myriadrf/LimeRFE-8001P/hardware/1v0/KiCAD/ATMEGA_MCU.sch

## KiCad design hardware/1v0/KiCAD/ATMEGA_MCU.sch (2023-10-04)

Schematic: ATMEGA_MCU.sch

Parts:
C35, C91, C179, C181, C183, C323, C325: 1nF_0402; SMD0402; Manufacturer Part Number CC0402KRX7R9BB102
C43, C46, C48, C50: 1uF_0603_TMK107BJ105KA-T; SMD0603; Manufacturer Part Number TMK107BJ105KA-T
C44: 4.7uF_0402_GRM155R60J475ME87D; SMD0402; Manufacturer Part Number GRM155R60J475ME87D
C45, C47, C49, C56: 100nF_0402_GRM155R71C104KA88J; SMD0402; Manufacturer Part Number GRM155R71C104KA88J
C83: 3.9nF_0402_04025C392JAT2A; SMD0402; Manufacturer Part Number 04025C392JAT2A
C92, C96, C97, C98, C167, C169, C180, C182, C184, C228, C229, C321, C322, C324, C326, C329, C330, C387, C388, C390, C391, C394, C395, C396, C397: 10nF_0402; SMD0402; Manufacturer Part Number CC0402ZRY5V7BB103
C320, C393: 1uF_0402; SMD0402; Manufacturer Part Number CC0402ZRY5V5BB105
CON2: 47346-0001; USB-MINI-B; Manufacturer Part Number 47346-0001
D1: LED0603_RED; LED_0603; Manufacturer Part Number SML-D12U1WT86
D2: LED0603_GREEN; LED_0603; Manufacturer Part Number SML-D12M1WT86
FB23: 10uH_0603_TDK; SMD0603; Manufacturer Part Number MLZ1608E100MT
J19: TSM-103-04-F-DV; Manufacturer Part Number TSM-103-04-F-DV
J28, J31: PMOD_CONN; Manufacturer Part Number 95278-401-06LF
J32: M50-3600542; PIN_HEADER_2X5; Manufacturer Part Number M50-3600542
J42: TSM-103-04-L-SV; Manufacturer Part Number TSM-103-04-L-SV
J43: Jumper_SNM-100-BK-T; SNM-100-BK-T; Manufacturer Part Number SNM-100-BK-T
R3, R4, R7, R18, R19, R22: 10K_0402; SMD0402; Manufacturer Part Number RMCF0402FT10K0
R5, R6, R20, R21: 10K_0402; SMD0402
R8, R9, R10, R11, R12, R13, R14, R15, R17, R23, R24, R25, R26, R27, R28, R84, R85, R132: 330R_0402; SMD0402; Manufacturer Part Number RC0402JR-07330RL
R16, R60, R61, R64, R71, R181, R182: 20K_0402_CRCW040220K0FKEDC; SMD0402; Manufacturer Part Number CRCW040220K0FKEDC
R43, R44, R46, R58, R59: 1K_0402_CRGP0402F1K0; SMD0402; Manufacturer Part Number CRGP0402F1K0
R47, R48: 22R_0402_RC0402JR-0722RL; SMD0402; Manufacturer Part Number RC0402JR-0722RL
R49: 1M_0402_RC0402FR-071ML; SMD0402; Manufacturer Part Number RC0402FR-071ML
R100: 0R_0402_RC0402JR-070RL; SMD0402; Manufacturer Part Number RC0402JR-070RL
R129, R204: 0R_0402_NF; SMD0402; Manufacturer Part Number RC0402JR-070RL
R163, R164, R165, R166, R167, R168, R169, R170, R173, R174, R175, R176, R177, R178, R205, R206, R207, R209, R279, R280, R281, R300, R301, R302, R303, R304, R305, R306, R307: 0R_0402; SMD0201
R179, R180: NF_0R_0402_RCS04020000Z0ED; SMD0402; Manufacturer Part Number RCS04020000Z0ED
R208: 0RNF_0402; SMD0402
SW3: SW_PUSH; B3U-1000P; Manufacturer Part Number B3U-1000P
U1, U2: LMS8001
U3, U22, U87: SN74LV1T04; Manufacturer Part Number SN74LV1T04DCKRG4
U11: ATMEGA328P-AU; Manufacturer Part Number ATMEGA328P-AUR
U12: FT232RL; Manufacturer Part Number FT232RL-REEL
U13: NUP2202W1T2G; SC-88-6_NUP2202W1T2G; Manufacturer Part Number NUP2202W1T2G
U17, U70, U71, U72: NXB0108PW-Q100J; Manufacturer Part Number NXB0108PW-Q100J
U19, U20: SN74HCS594QPWRQ1; Manufacturer Part Number SN74HCS594QPWRQ1
U23, U24: MC74VHC1G126DBVT1G; Manufacturer Part Number ONSEMI
U25: SN74HCS595QPWRQ1; Manufacturer Part Number SN74HCS595QPWRQ1
U88, U89: SN74CBT3245APWE4; Manufacturer Part Number SN74CBT3245APWE4
U90: TC7MBL3245CFT(EL); Manufacturer Part Number TC7MBL3245CFT(EL)
X2: CSTNE16M0V530000R0; Manufacturer Part Number CSTNE16M0V530000R0

Notes on the sheet:
SPI_SOFT CON
SAENn towards LMS8001 #1
SCENn towards PLL #1
Level convertors 3.3V<->5V for SPI
Daisy Chain
SBENn towards LMS8001 #2
SN74HCS595QPWRQ1: this one has OE pin and 3-state out
brisi ovo!
3.3V pull-up
5V pull-up
0V pull-down
SDENn towards PLL #2
This one should be default
This one should be NF
LMS8001 #1
LMS8001 #2
MCU FREE PINS CON
RESETn towards LMS8001 #1
RESETn towards LMS8001 #2
1.2-3.6V on A side
1.65-5V on B side
SCENn towards PLL #2
MCU_side
Connects free MCU pins to eather LMS8001 chip A or B
GPIO 00, 01, 02 of LMS8001 A or B to free MCU pins PC5, PC4 and PB0
SPI connector from 5G board
SDIO signal to MISO and MOSI
RESET
USB 2 SERIAL
TVS_protection
USB_CONN
Interupt 1
NE ZNAM CEMU SLUZI?
Interupt 0
Shift (Serial) Register Data CLOCK
Output Register Data ENABLE
Shift (Serial) Register Data RESET
Output Register Data RESET
MCU
