myriadrf/LimeRFE-8001P/hardware/1v0/KiCAD/DA1.sch

## KiCad design hardware/1v0/KiCAD/DA1.sch (2023-10-04)

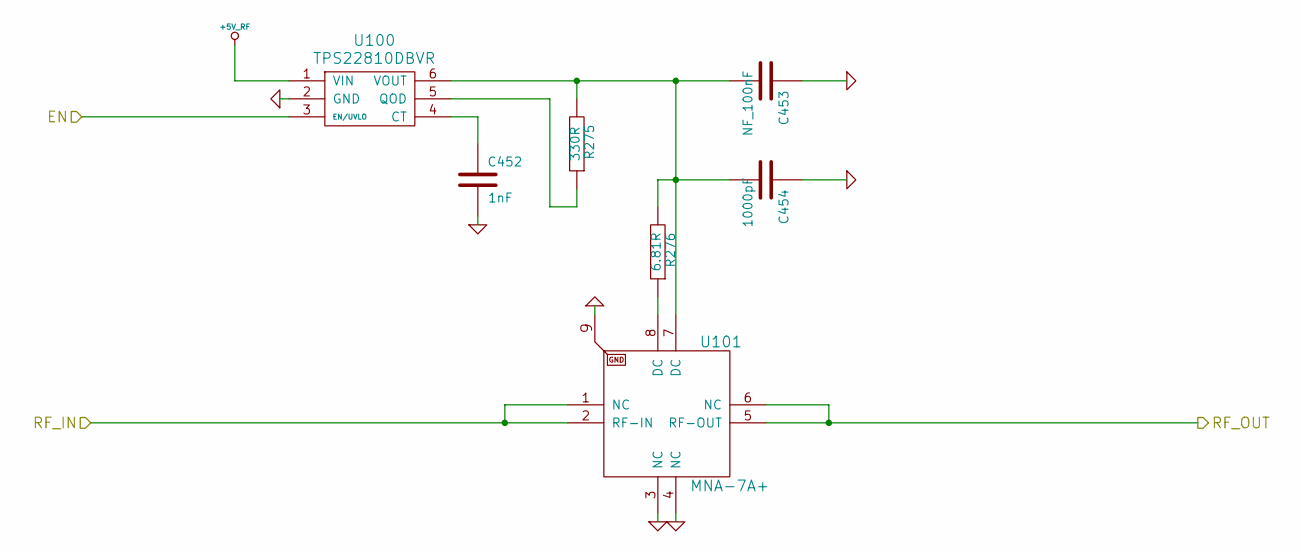
[picture p48: schematic DA1.sch]

Parts:
C452: 1nF_0603_06035C102KAT2A; SMD0603; Manufacturer Part Number 06035C102KAT2A
C453: NF_100nF_0603_C0603C104M5RACTU; SMD0603; Manufacturer Part Number C0603C104M5RACTU
C454: 1000pF_0402_GCM155R71H102KA37D; SMD0402; Manufacturer Part Number GCM155R71H102KA37D
R275: 330R_0603_CRGCQ0603J330R; SMD0603; Manufacturer Part Number CRGCQ0603J330R
R276: 6.81R_0805_CRCW08056R81FNEA; SMD0805; Manufacturer Part Number CRCW08056R81FNEA
U100: TPS22810DBVR; SOT23_TPS22810DBVR; Manufacturer Part Number TPS22810DBVR
U101: MNA-7A+; Manufacturer Part Number MNA-7A+

Connections:
+5V_RF: U100.1 (VIN)
EN: U100.3 (EN/UVLO)
GND: C452.2, C453.1, C454.1, U100.2 (GND), U101.3 (NC), U101.4 (NC), U101.9
unnamed: C452.1, U100.4 (CT)
unnamed: C453.2, C454.2, R275.2, R276.2, U100.6 (VOUT), U101.7 (DC)
unnamed: R275.1, U100.5 (QOD)
unnamed: R276.1, U101.8 (DC)
RF_IN: U101.1 (NC), U101.2 (RF-IN)
RF_OUT: U101.5 (RF-OUT), U101.6 (NC)
