myriadrf/LimeRFE-8001P/hardware/1v0/KiCAD/DA2.sch

## KiCad design hardware/1v0/KiCAD/DA2.sch (2023-10-04)

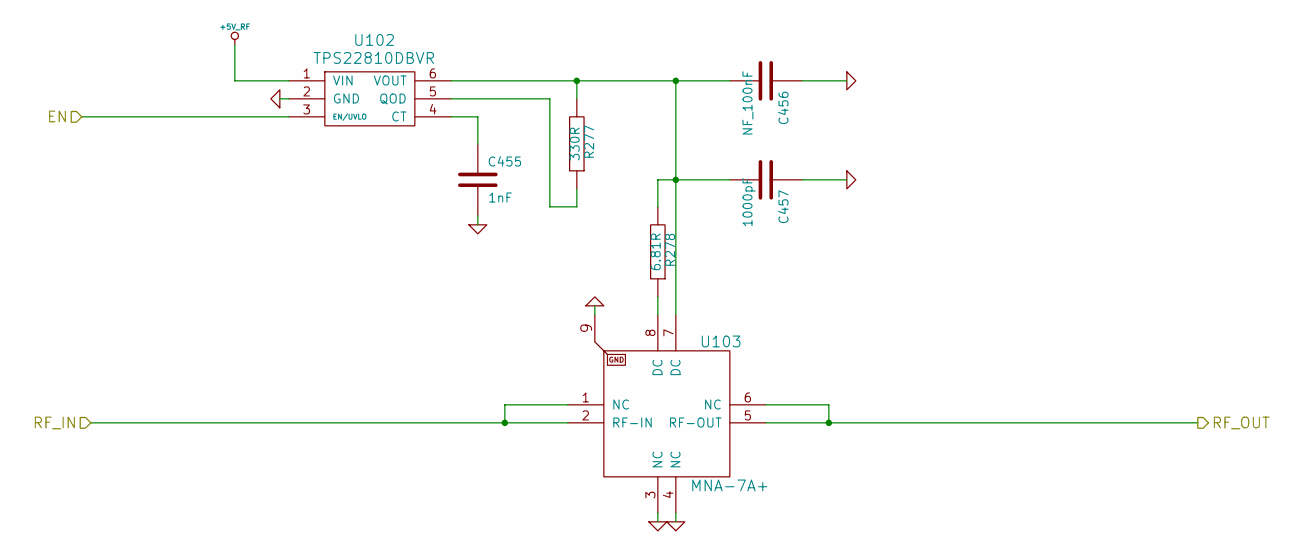
[picture p49: schematic DA2.sch]

Parts:
C455: 1nF_0603_06035C102KAT2A; SMD0603; Manufacturer Part Number 06035C102KAT2A
C456: NF_100nF_0603_C0603C104M5RACTU; SMD0603; Manufacturer Part Number C0603C104M5RACTU
C457: 1000pF_0402_GCM155R71H102KA37D; SMD0402; Manufacturer Part Number GCM155R71H102KA37D
R277: 330R_0603_CRGCQ0603J330R; SMD0603; Manufacturer Part Number CRGCQ0603J330R
R278: 6.81R_0805_CRCW08056R81FNEA; SMD0805; Manufacturer Part Number CRCW08056R81FNEA
U102: TPS22810DBVR; SOT23_TPS22810DBVR; Manufacturer Part Number TPS22810DBVR
U103: MNA-7A+; Manufacturer Part Number MNA-7A+

Connections:
+5V_RF: U102.1 (VIN)
EN: U102.3 (EN/UVLO)
GND: C455.2, C456.1, C457.1, U102.2 (GND), U103.3 (NC), U103.4 (NC), U103.9
unnamed: C455.1, U102.4 (CT)
unnamed: C456.2, C457.2, R277.2, R278.2, U102.6 (VOUT), U103.7 (DC)
unnamed: R277.1, U102.5 (QOD)
unnamed: R278.1, U103.8 (DC)
RF_IN: U103.1 (NC), U103.2 (RF-IN)
RF_OUT: U103.5 (RF-OUT), U103.6 (NC)
