myriadrf/LimeRFE-8001P/hardware/1v0/KiCAD/LMS8001_PowerSupply.sch

## KiCad design hardware/1v0/KiCAD/LMS8001_PowerSupply.sch (2023-10-04)

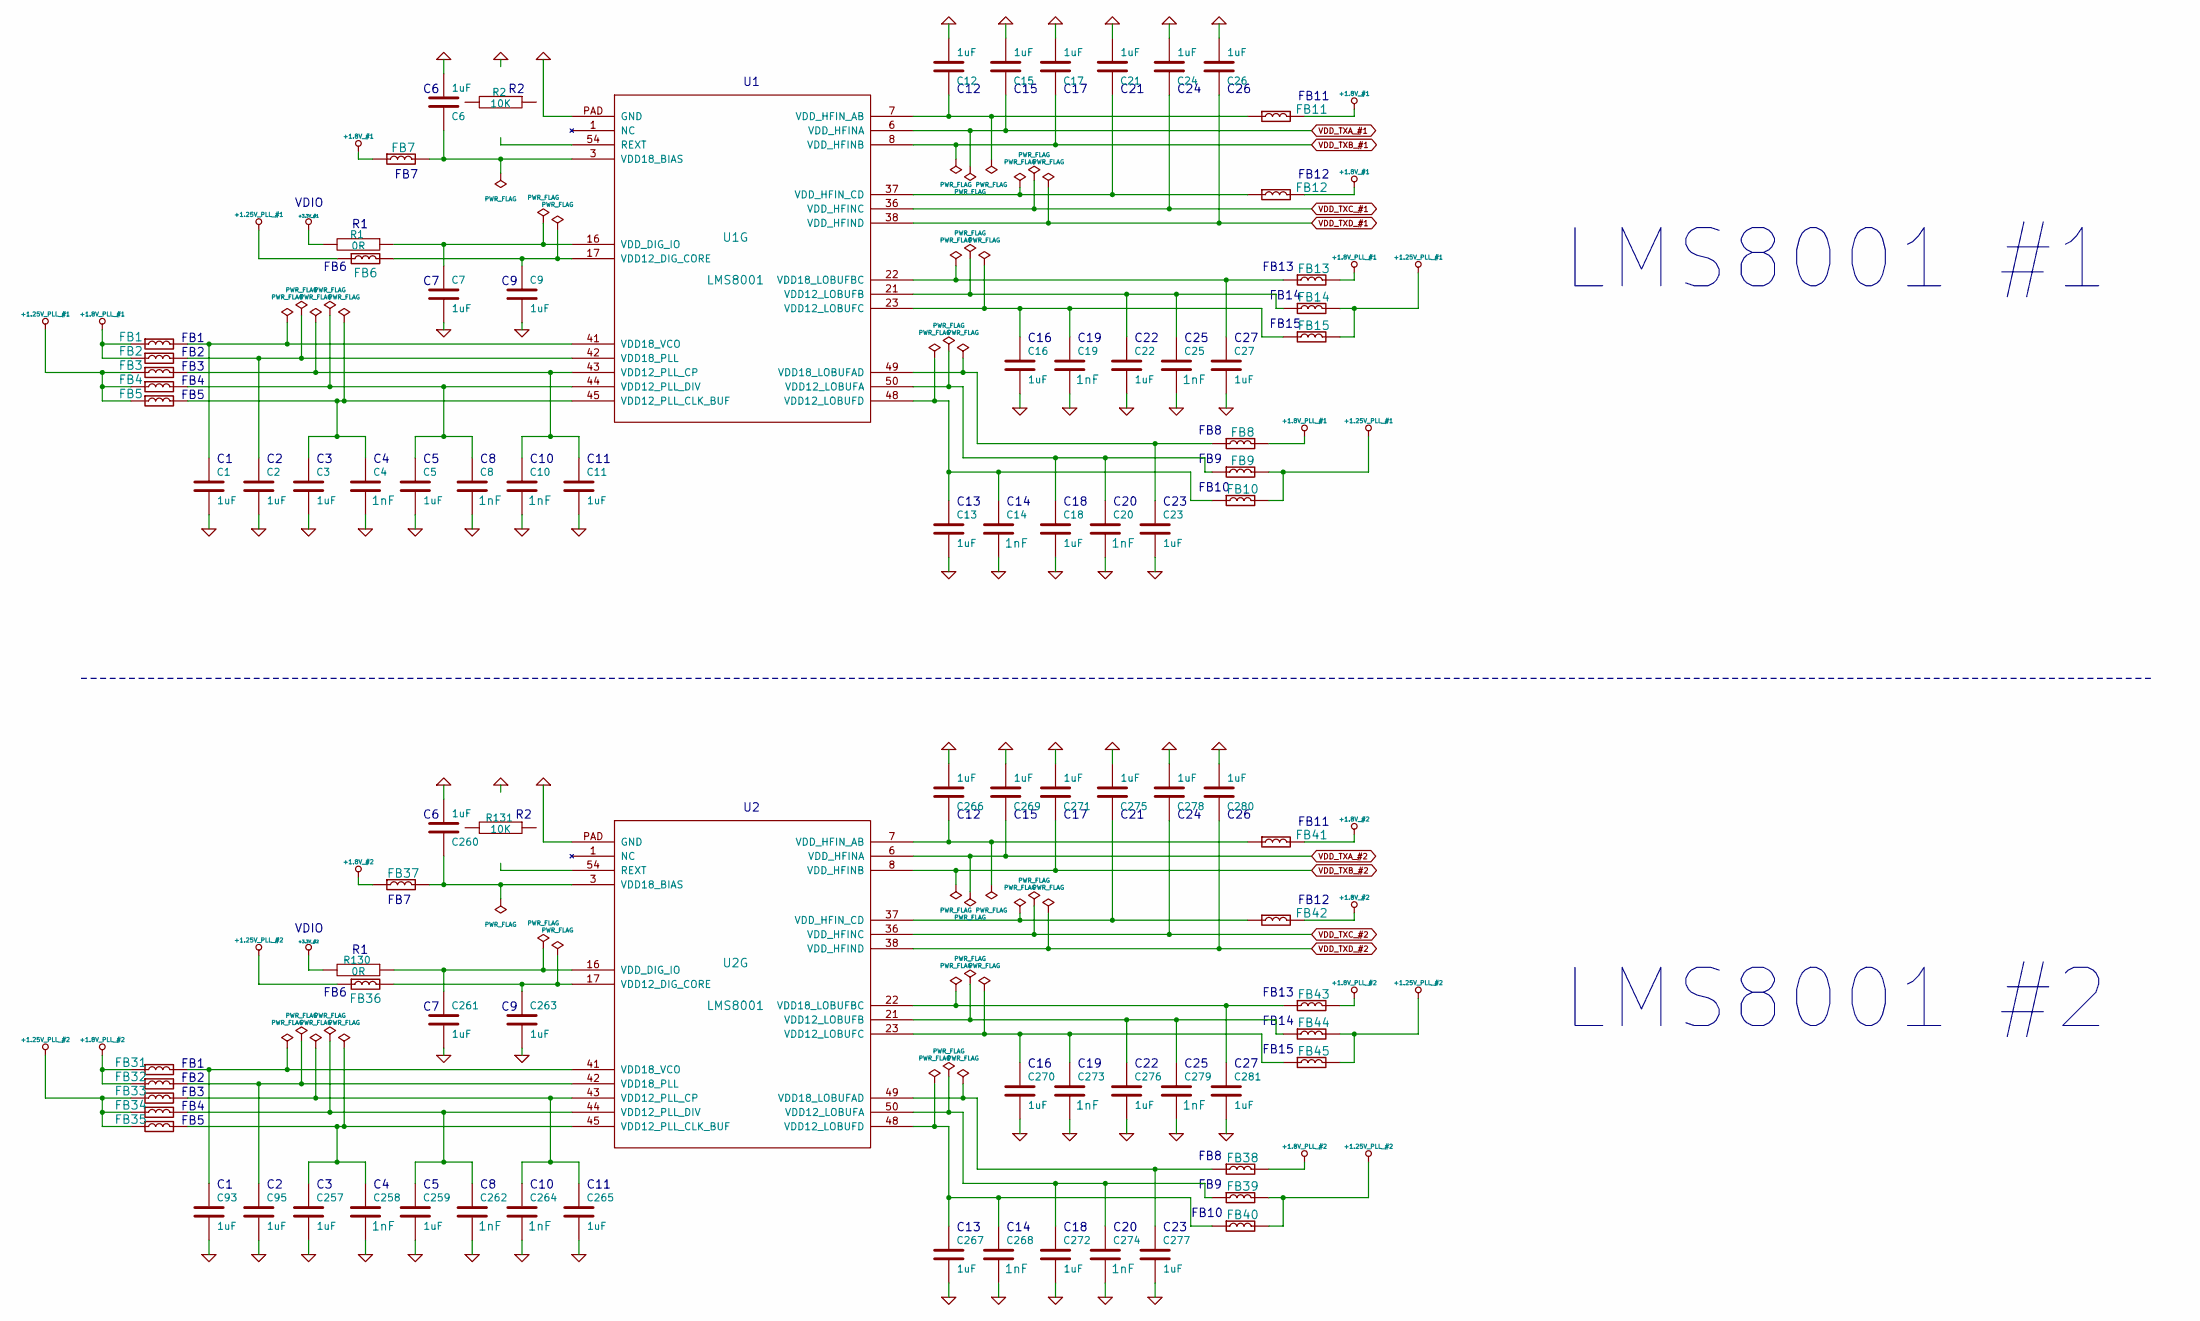
[picture p50: schematic LMS8001_PowerSupply.sch]

Parts:
C1, C2, C3, C5, C6, C7, C9, C11, C12, C13, C15, C16, C17, C18, C21, C22, C23, C24, C26, C27, C93, C95, C257, C259, C260, C261, C263, C265, C266, C267, C269, C270, C271, C272, C275, C276, C277, C278, C280, C281: 1UF_0201_TDK_X5R; SMD0201; Manufacturer Part Number C0603X5R0J105M030BC
C4, C8, C10, C14, C19, C20, C25, C258, C262, C264, C268, C273, C274, C279: 1NF_0201; SMD0201; Manufacturer Part Number C0603X7R1E102K030BA
FB1, FB2, FB3, FB4, FB5, FB6, FB7, FB8, FB9, FB10, FB11, FB12, FB13, FB14, FB15, FB31, FB32, FB33, FB34, FB35, FB36, FB37, FB38, FB39, FB40, FB41, FB42, FB43, FB44, FB45: FB_0201; SMD0201; Manufacturer Part Number BK0603TS601-T
R1, R130: 0R_0201; SMD0201; Manufacturer Part Number MCR006YRTJ000
R2, R131: 10K_0402; SMD0402; Manufacturer Part Number RMCF0402FT10K0
U1, U2: LMS8001

Connections:
+1.8V_#1: FB7.1, FB11.2, FB12.2
+1.8V_#2: FB37.1, FB41.2, FB42.2
+1.8V_PLL_#1: FB1.1, FB2.1, FB8.2, FB13.2
+1.8V_PLL_#2: FB31.1, FB32.1, FB38.2, FB43.2
+1.25V_PLL_#1: FB3.1, FB4.1, FB5.1, FB6.1, FB9.2, FB10.2, FB14.2, FB15.2
+1.25V_PLL_#2: FB33.1, FB34.1, FB35.1, FB36.1, FB39.2, FB40.2, FB44.2, FB45.2
+3.3V_#1: R1.2
+3.3V_#2: R130.2
GND: C1.2, C2.2, C3.2, C4.2, C5.2, C6.2, C7.2, C8.2, C9.2, C10.2, C11.2, C12.2, C13.2, C14.2, C15.2, C16.2, C17.2, C18.2, C19.2, C20.2, C21.2, C22.2, C23.2, C24.2, C25.2, C26.2, C27.2, C93.2, C95.2, C257.2, C258.2, C259.2, C260.2, C261.2, C262.2, C263.2, C264.2, C265.2, C266.2, C267.2, C268.2, C269.2, C270.2, C271.2, C272.2, C273.2, C274.2, C275.2, C276.2, C277.2, C278.2, C279.2, C280.2, C281.2, U1.PAD (GND), U2.PAD (GND)
unnamed: C1.1, FB1.2, U1.41 (VDD18_VCO)
unnamed: C2.1, FB2.2, U1.42 (VDD18_PLL)
unnamed: C3.1, C4.1, FB5.2, U1.45 (VDD12_PLL_CLK_BUF)
unnamed: C5.1, C8.1, FB4.2, U1.44 (VDD12_PLL_DIV)
unnamed: C6.1, FB7.2, U1.3 (VDD18_BIAS)
unnamed: C7.1, R1.1, U1.16 (VDD_DIG_IO)
unnamed: C9.1, FB6.2, U1.17 (VDD12_DIG_CORE)
unnamed: C10.1, C11.1, FB3.2, U1.43 (VDD12_PLL_CP)
unnamed: C12.1, FB11.1, U1.7 (VDD_HFIN_AB)
unnamed: C13.1, C14.1, FB10.1, U1.48 (VDD12_LOBUFD)
unnamed: C16.1, C19.1, FB15.1, U1.23 (VDD12_LOBUFC)
unnamed: C18.1, C20.1, FB9.1, U1.50 (VDD12_LOBUFA)
unnamed: C21.1, FB12.1, U1.37 (VDD_HFIN_CD)
unnamed: C22.1, C25.1, FB14.1, U1.21 (VDD12_LOBUFB)
unnamed: C23.1, FB8.1, U1.49 (VDD18_LOBUFAD)
unnamed: C27.1, FB13.1, U1.22 (VDD18_LOBUFBC)
unnamed: C93.1, FB31.2, U2.41 (VDD18_VCO)
unnamed: C95.1, FB32.2, U2.42 (VDD18_PLL)
unnamed: C257.1, C258.1, FB35.2, U2.45 (VDD12_PLL_CLK_BUF)
unnamed: C259.1, C262.1, FB34.2, U2.44 (VDD12_PLL_DIV)
unnamed: C260.1, FB37.2, U2.3 (VDD18_BIAS)
unnamed: C261.1, R130.1, U2.16 (VDD_DIG_IO)
unnamed: C263.1, FB36.2, U2.17 (VDD12_DIG_CORE)
unnamed: C264.1, C265.1, FB33.2, U2.43 (VDD12_PLL_CP)
unnamed: C266.1, FB41.1, U2.7 (VDD_HFIN_AB)
unnamed: C267.1, C268.1, FB40.1, U2.48 (VDD12_LOBUFD)
unnamed: C270.1, C273.1, FB45.1, U2.23 (VDD12_LOBUFC)
unnamed: C272.1, C274.1, FB39.1, U2.50 (VDD12_LOBUFA)
unnamed: C275.1, FB42.1, U2.37 (VDD_HFIN_CD)
unnamed: C276.1, C279.1, FB44.1, U2.21 (VDD12_LOBUFB)
unnamed: C277.1, FB38.1, U2.49 (VDD18_LOBUFAD)
unnamed: C281.1, FB43.1, U2.22 (VDD18_LOBUFBC)
VDD_TXA_#1: C15.1, U1.6 (VDD_HFINA)
VDD_TXA_#2: C269.1, U2.6 (VDD_HFINA)
VDD_TXB_#1: C17.1, U1.8 (VDD_HFINB)
VDD_TXB_#2: C271.1, U2.8 (VDD_HFINB)
VDD_TXC_#1: C24.1, U1.36 (VDD_HFINC)
VDD_TXC_#2: C278.1, U2.36 (VDD_HFINC)
VDD_TXD_#1: C26.1, U1.38 (VDD_HFIND)
VDD_TXD_#2: C280.1, U2.38 (VDD_HFIND)

Notes on the sheet:
LMS8001 #1
LMS8001 #2
FB7
FB6
FB1
FB2
FB3
FB4
FB5
C10
C11
C12
C15
C17
C21
C24
C26
FB11
FB12
FB13
FB14
FB15
C16
C19
C22
C25
C27
FB8
FB9
FB10
C13
C14
C18
C20
C23
VDIO
