myriadrf/LimeRFE-8001P/hardware/1v0/KiCAD/LMS98001_GPIO.sch

## KiCad design hardware/1v0/KiCAD/LMS98001_GPIO.sch (2023-10-04)

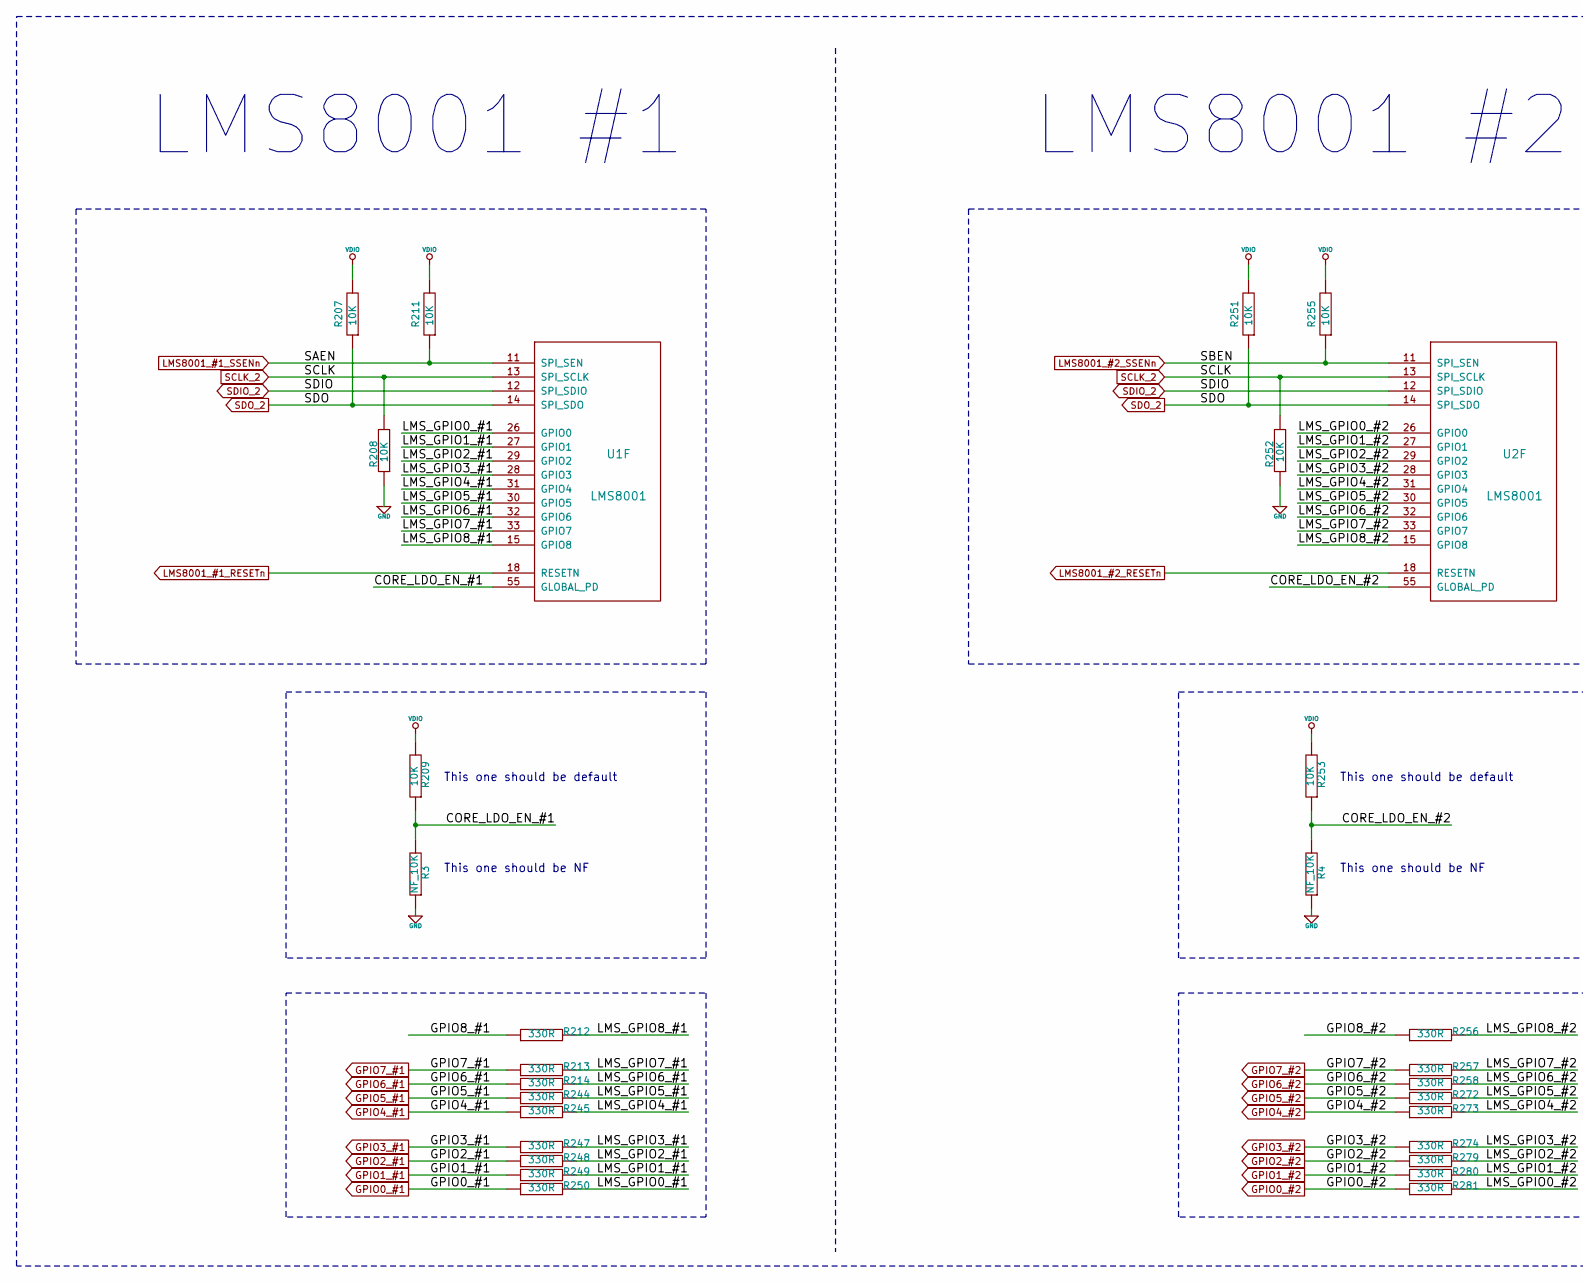
[picture p55: schematic LMS98001_GPIO.sch, part in row 1, column 1]

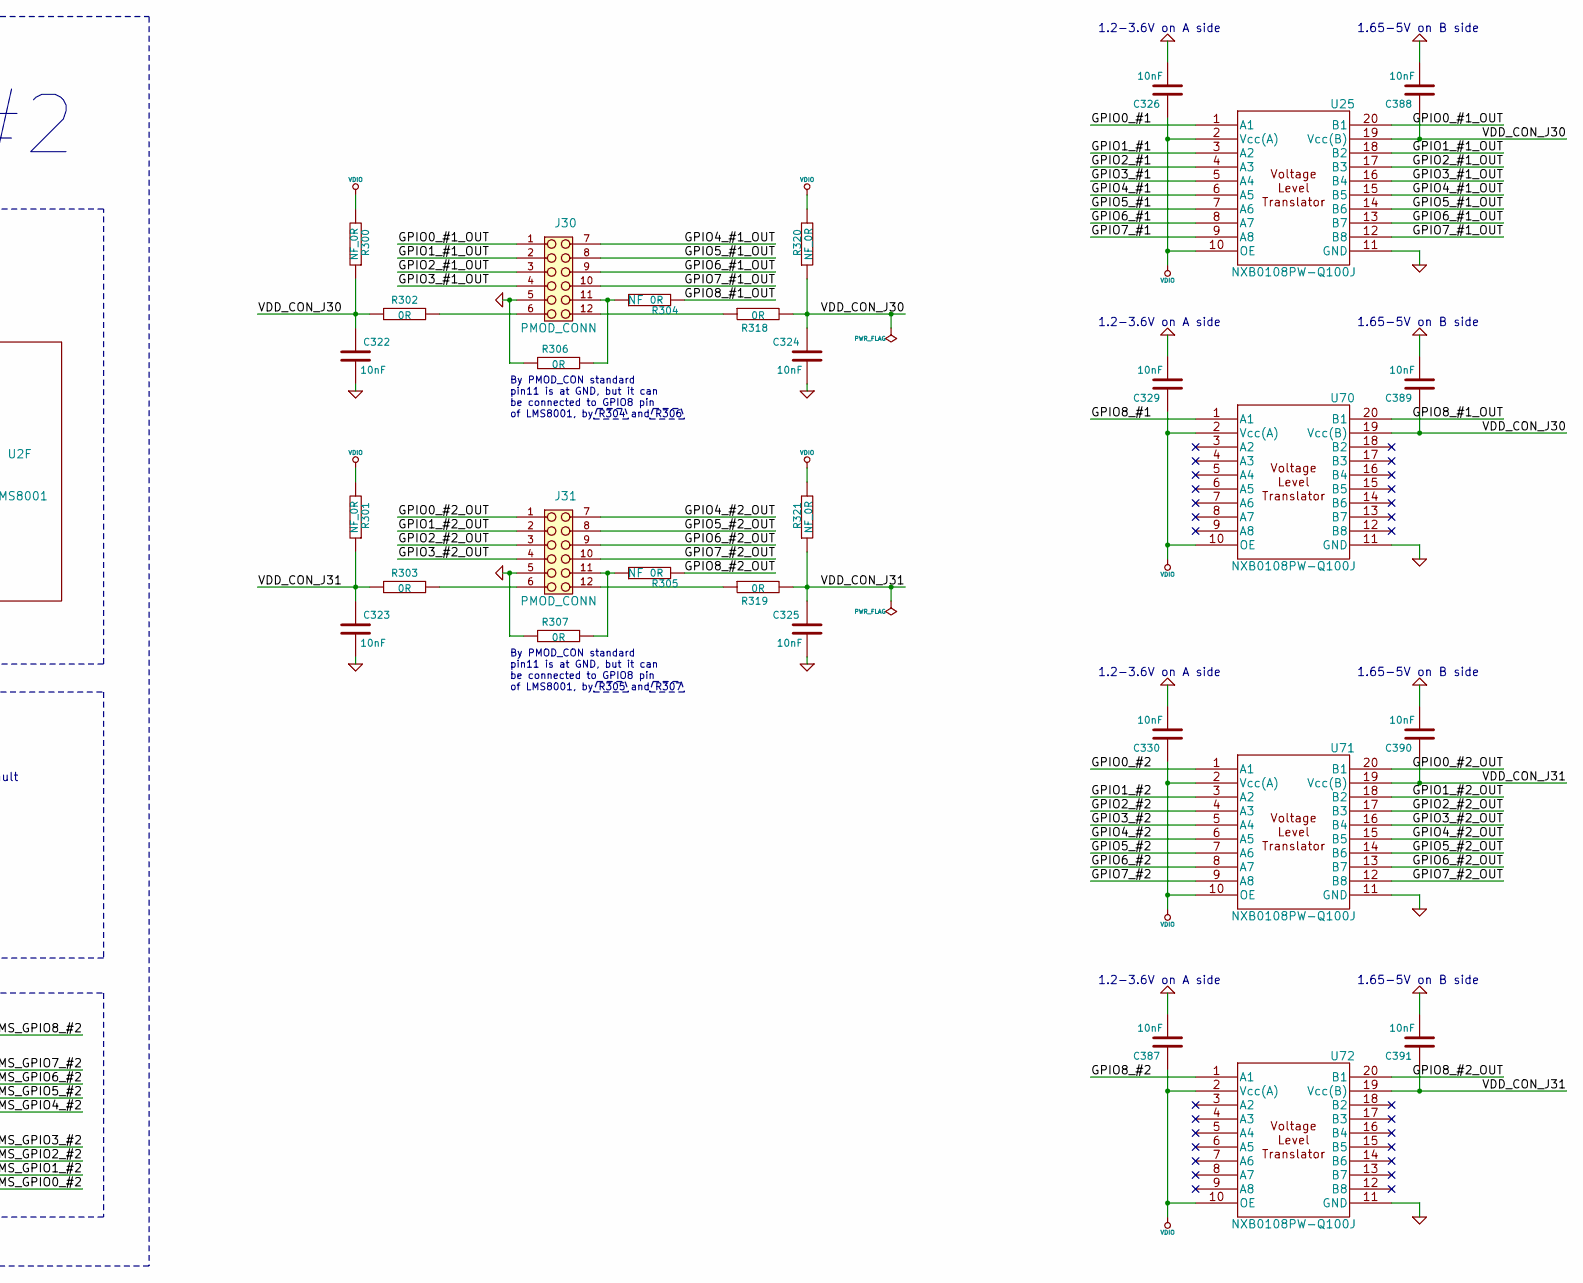
[picture p56: schematic LMS98001_GPIO.sch, part in row 1, column 2]

Parts:
C322, C323, C324, C325, C326, C329, C330, C387, C388, C389, C390, C391: 10nF_0402; SMD0402; Manufacturer Part Number CC0402ZRY5V7BB103
J30, J31: PMOD_CONN; Manufacturer Part Number 95278-401-06LF
R3, R4: NF_10K_0402; SMD0402
R207, R208, R211, R251, R252, R255: 10K_0402; SMD0402; Manufacturer Part Number RMCF0402FT10K0
R209, R253: 10K_0402; SMD0402
R212, R213, R214, R244, R245, R247, R248, R249, R250, R256, R257, R258, R272, R273, R274, R279, R280, R281: 330R_0402; SMD0402; Manufacturer Part Number RC0402JR-07330RL
R300, R301, R320, R321: NF_0R_0402_RCS04020000Z0ED; SMD0402; Manufacturer Part Number RCS04020000Z0ED
R302, R303, R306, R307, R318, R319: 0R_0402; SMD0402
R304, R305: 0R_0402_NF; SMD0402; Manufacturer Part Number RC0402JR-070RL
U1, U2: LMS8001
U25, U70, U71, U72: NXB0108PW-Q100J; Manufacturer Part Number NXB0108PW-Q100J

Connections:
CORE_LDO_EN_#1: R3.2, R209.1, U1.55 (GLOBAL_PD)
CORE_LDO_EN_#2: R4.2, R253.1, U2.55 (GLOBAL_PD)
GND: C322.2, C323.2, C324.2, C325.2, C326.2, C329.2, C330.2, C387.2, C388.2, C389.2, C390.2, C391.2, J30.5, J31.5, R3.1, R4.1, R208.1, R252.1, R306.2, R307.2, U25.11 (GND), U70.11 (GND), U71.11 (GND), U72.11 (GND)
GPIO0_#1: R250.1, U25.1 (A1)
GPIO0_#1_OUT: J30.1, U25.20 (B1)
GPIO0_#2: R281.1, U71.1 (A1)
GPIO0_#2_OUT: J31.1, U71.20 (B1)
GPIO1_#1: R249.1, U25.3 (A2)
GPIO1_#1_OUT: J30.2, U25.18 (B2)
GPIO1_#2: R280.1, U71.3 (A2)
GPIO1_#2_OUT: J31.2, U71.18 (B2)
GPIO2_#1: R248.1, U25.4 (A3)
GPIO2_#1_OUT: J30.3, U25.17 (B3)
GPIO2_#2: R279.1, U71.4 (A3)
GPIO2_#2_OUT: J31.3, U71.17 (B3)
GPIO3_#1: R247.1, U25.5 (A4)
GPIO3_#1_OUT: J30.4, U25.16 (B4)
GPIO3_#2: R274.1, U71.5 (A4)
GPIO3_#2_OUT: J31.4, U71.16 (B4)
GPIO4_#1: R245.1, U25.6 (A5)
GPIO4_#1_OUT: J30.7, U25.15 (B5)
GPIO4_#2: R273.1, U71.6 (A5)
GPIO4_#2_OUT: J31.7, U71.15 (B5)
GPIO5_#1: R244.1, U25.7 (A6)
GPIO5_#1_OUT: J30.8, U25.14 (B6)
GPIO5_#2: R272.1, U71.7 (A6)
GPIO5_#2_OUT: J31.8, U71.14 (B6)
GPIO6_#1: R214.1, U25.8 (A7)
GPIO6_#1_OUT: J30.9, U25.13 (B7)
GPIO6_#2: R258.1, U71.8 (A7)
GPIO6_#2_OUT: J31.9, U71.13 (B7)
GPIO7_#1: R213.1, U25.9 (A8)
GPIO7_#1_OUT: J30.10, U25.12 (B8)
GPIO7_#2: R257.1, U71.9 (A8)
GPIO7_#2_OUT: J31.10, U71.12 (B8)
GPIO8_#1: R212.1, U70.1 (A1)
GPIO8_#1_OUT: R304.2, U70.20 (B1)
GPIO8_#2: R256.1, U72.1 (A1)
GPIO8_#2_OUT: R305.2, U72.20 (B1)
LMS8001_#1_RESETn: U1.18 (RESETN)
LMS8001_#1_SSENn: R211.1, U1.11 (SPI_SEN)
LMS8001_#2_RESETn: U2.18 (RESETN)
LMS8001_#2_SSENn: R255.1, U2.11 (SPI_SEN)
LMS_GPIO0_#1: R250.2, U1.26 (GPIO0)
LMS_GPIO0_#2: R281.2, U2.26 (GPIO0)
LMS_GPIO1_#1: R249.2, U1.27 (GPIO1)
LMS_GPIO1_#2: R280.2, U2.27 (GPIO1)
LMS_GPIO2_#1: R248.2, U1.29 (GPIO2)
LMS_GPIO2_#2: R279.2, U2.29 (GPIO2)
LMS_GPIO3_#1: R247.2, U1.28 (GPIO3)
LMS_GPIO3_#2: R274.2, U2.28 (GPIO3)
LMS_GPIO4_#1: R245.2, U1.31 (GPIO4)
LMS_GPIO4_#2: R273.2, U2.31 (GPIO4)
LMS_GPIO5_#1: R244.2, U1.30 (GPIO5)
LMS_GPIO5_#2: R272.2, U2.30 (GPIO5)
LMS_GPIO6_#1: R214.2, U1.32 (GPIO6)
LMS_GPIO6_#2: R258.2, U2.32 (GPIO6)
LMS_GPIO7_#1: R213.2, U1.33 (GPIO7)
LMS_GPIO7_#2: R257.2, U2.33 (GPIO7)
LMS_GPIO8_#1: R212.2, U1.15 (GPIO8)
LMS_GPIO8_#2: R256.2, U2.15 (GPIO8)
unnamed: J30.6, R302.1
unnamed: J30.11, R304.1, R306.1
unnamed: J30.12, R318.1
unnamed: J31.6, R303.1
unnamed: J31.11, R305.1, R307.1
unnamed: J31.12, R319.1
SCLK_2: R208.2, R252.2, U1.13 (SPI_SCLK), U2.13 (SPI_SCLK)
SDIO_2: U1.12 (SPI_SDIO), U2.12 (SPI_SDIO)
SDO_2: R207.1, R251.1, U1.14 (SPI_SDO), U2.14 (SPI_SDO)
VDD_CON_J30: C322.1, C324.1, C388.1, C389.1, R300.1, R302.2, R318.2, R320.1, U25.19 (Vcc(B)), U70.19 (Vcc(B))
VDD_CON_J31: C323.1, C325.1, C390.1, C391.1, R301.1, R303.2, R319.2, R321.1, U71.19 (Vcc(B)), U72.19 (Vcc(B))
VDIO: C326.1, C329.1, C330.1, C387.1, R207.2, R209.2, R211.2, R251.2, R253.2, R255.2, R300.2, R301.2, R320.2, R321.2, U25.2 (Vcc(A)), U25.10 (OE), U70.2 (Vcc(A)), U70.10 (OE), U71.2 (Vcc(A)), U71.10 (OE), U72.2 (Vcc(A)), U72.10 (OE)

Notes on the sheet:
This one should be default
This one should be NF
LMS8001 #1
LMS8001 #2
1.2-3.6V on A side
1.65-5V on B side
By PMOD_CON standard pin11 is at GND, but it can be connected to GPIO8 pin of LMS8001, by R304 and R306
By PMOD_CON standard pin11 is at GND, but it can be connected to GPIO8 pin of LMS8001, by R305 and R307
