myriadrf/LimeRFE-8001P/hardware/1v0/KiCAD/LNA1.sch

## KiCad design hardware/1v0/KiCAD/LNA1.sch (2023-10-04)

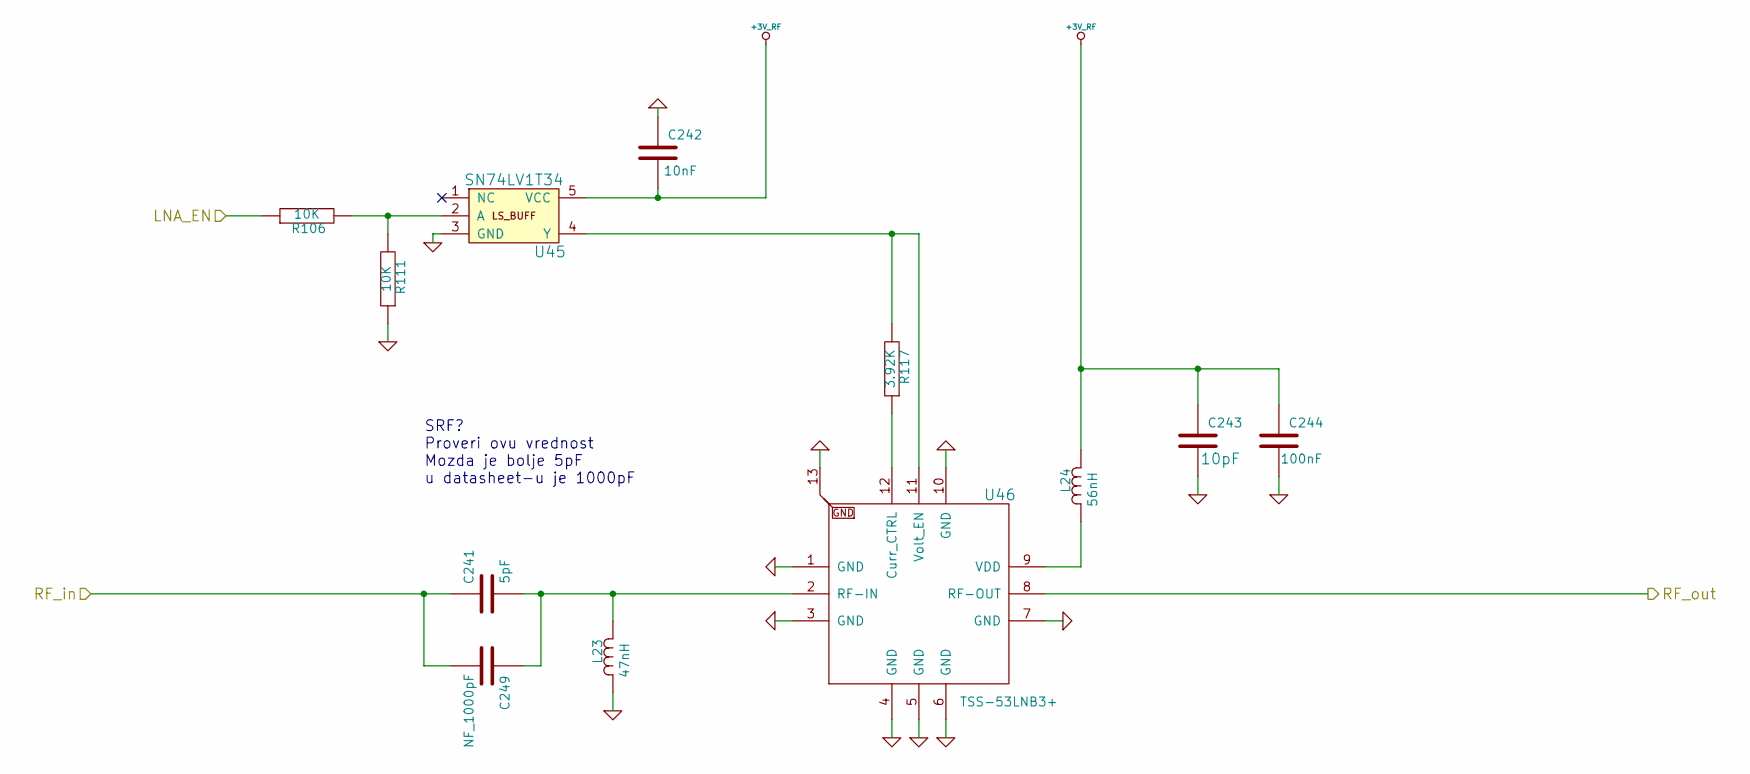
[picture p57: schematic LNA1.sch]

Parts:
C241: 5pF_0402_CBR04C509C5GAC; SMD0402; Manufacturer Part Number CBR04C509C5GAC
C242: 10nF_0402; SMD0402; Manufacturer Part Number CC0402ZRY5V7BB103
C243: 10pF_0402; SMD0402; Manufacturer Part Number CC0402JRNPO9BN100
C244: 100nF_0402_GRM155R71C104KA88J; SMD0402; Manufacturer Part Number GRM155R71C104KA88J
C249: NF_1000pF_0402_GCM155R71H102KA37D; SMD0402; Manufacturer Part Number GCM155R71H102KA37D
L23: 47nH_0402_LQW04AN47NH20D; SMD0402; Manufacturer Part Number LQW04AN47NH20D
L24: 56nH_0402_LQW15AW56NJ80D; SMD0402; Manufacturer Part Number LQW15AW56NJ80D
R106, R111: 10K_0402; SMD0402
R117: 3.92K_0402_CRCW04023K92FKEDC; SMD0402; Manufacturer Part Number CRCW04023K92FKEDC
U45: SN74LV1T34; Manufacturer Part Number Texas Instruments
U46: TSS-53LNB3+; Manufacturer Part Number TSS-53LNB3+

Connections:
+3V_RF: C242.2, C243.1, C244.1, L24.1, U45.5 (VCC)
GND: C242.1, C243.2, C244.2, L23.2, R111.1, U45.3 (GND), U46.1 (GND), U46.3 (GND), U46.4 (GND), U46.5 (GND), U46.6 (GND), U46.7 (GND), U46.10 (GND), U46.13
LNA_EN: R106.1
unnamed: C241.2, C249.1, L23.1, U46.2 (RF-IN)
unnamed: L24.2, U46.9 (VDD)
unnamed: R106.2, R111.2, U45.2 (A)
unnamed: R117.1, U46.12 (Curr_CTRL)
unnamed: R117.2, U45.4 (Y), U46.11 (Volt_EN)
RF_in: C241.1, C249.2
RF_out: U46.8 (RF-OUT)

Notes on the sheet:
SRF? Proveri ovu vrednost Mozda je bolje 5pF u datasheet-u je 1000pF
