myriadrf/LimeRFE-8001P/hardware/1v0/KiCAD/LNA2.sch

## KiCad design hardware/1v0/KiCAD/LNA2.sch (2023-10-04)

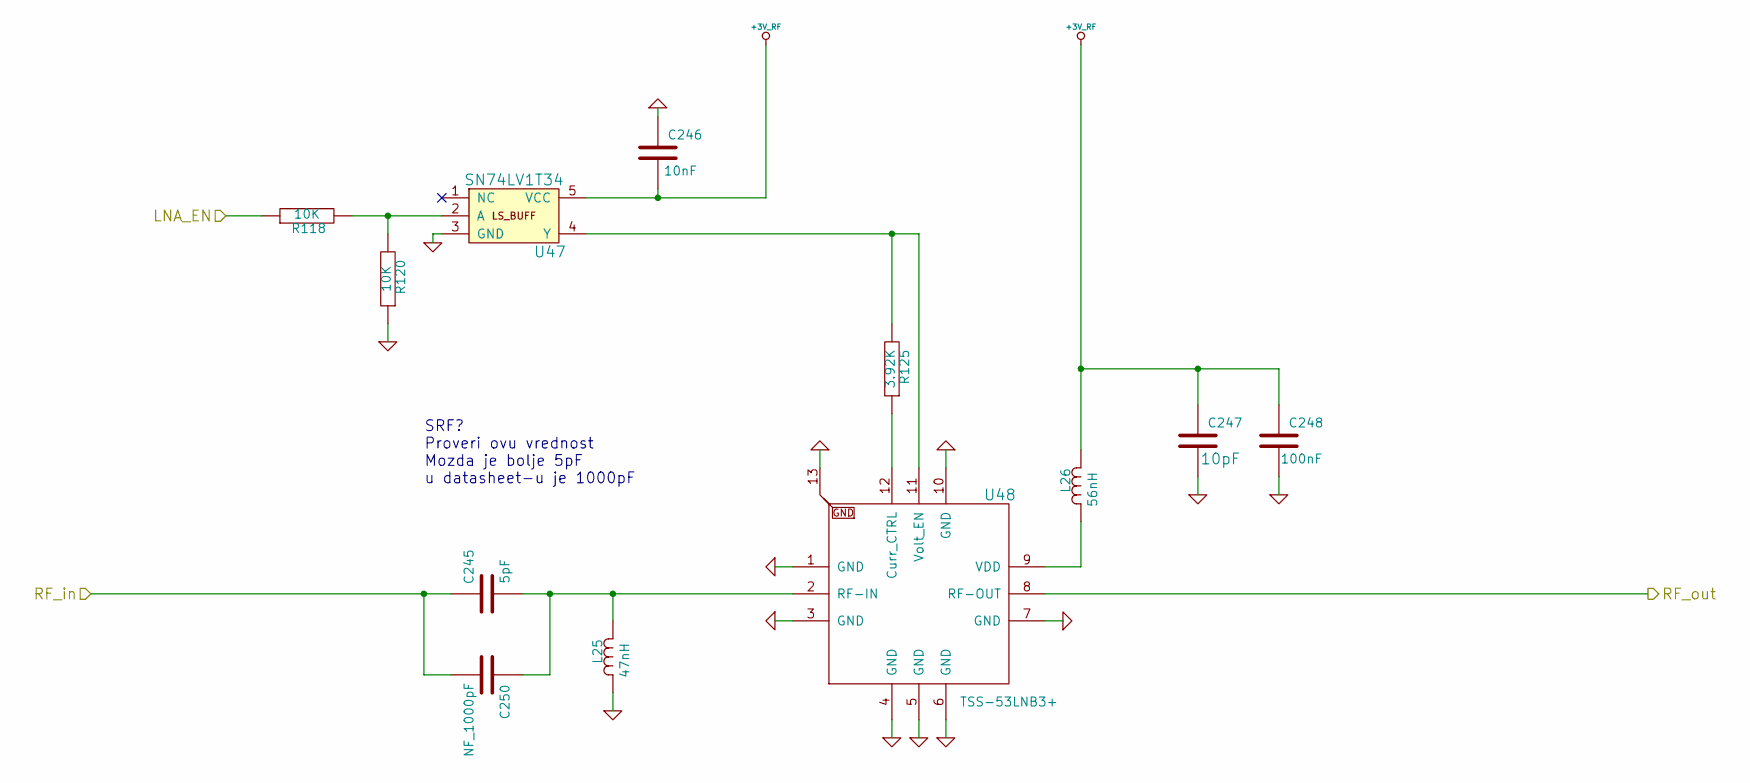
[picture p58: schematic LNA2.sch]

Parts:
C245: 5pF_0402_CBR04C509C5GAC; SMD0402; Manufacturer Part Number CBR04C509C5GAC
C246: 10nF_0402; SMD0402; Manufacturer Part Number CC0402ZRY5V7BB103
C247: 10pF_0402; SMD0402; Manufacturer Part Number CC0402JRNPO9BN100
C248: 100nF_0402_GRM155R71C104KA88J; SMD0402; Manufacturer Part Number GRM155R71C104KA88J
C250: NF_1000pF_0402_GCM155R71H102KA37D; SMD0402; Manufacturer Part Number GCM155R71H102KA37D
L25: 47nH_0402_LQW04AN47NH20D; SMD0402; Manufacturer Part Number LQW04AN47NH20D
L26: 56nH_0402_LQW15AW56NJ80D; SMD0402; Manufacturer Part Number LQW15AW56NJ80D
R118, R120: 10K_0402; SMD0402
R125: 3.92K_0402_CRCW04023K92FKEDC; SMD0402; Manufacturer Part Number CRCW04023K92FKEDC
U47: SN74LV1T34; Manufacturer Part Number Texas Instruments
U48: TSS-53LNB3+; Manufacturer Part Number TSS-53LNB3+

Connections:
+3V_RF: C246.2, C247.1, C248.1, L26.1, U47.5 (VCC)
GND: C246.1, C247.2, C248.2, L25.2, R120.1, U47.3 (GND), U48.1 (GND), U48.3 (GND), U48.4 (GND), U48.5 (GND), U48.6 (GND), U48.7 (GND), U48.10 (GND), U48.13
LNA_EN: R118.1
unnamed: C245.2, C250.1, L25.1, U48.2 (RF-IN)
unnamed: L26.2, U48.9 (VDD)
unnamed: R118.2, R120.2, U47.2 (A)
unnamed: R125.1, U48.12 (Curr_CTRL)
unnamed: R125.2, U47.4 (Y), U48.11 (Volt_EN)
RF_in: C245.1, C250.2
RF_out: U48.8 (RF-OUT)

Notes on the sheet:
SRF? Proveri ovu vrednost Mozda je bolje 5pF u datasheet-u je 1000pF
