myriadrf/LimeRFE-8001P/hardware/1v0/KiCAD/PA1_A.sch

## KiCad design hardware/1v0/KiCAD/PA1_A.sch (2023-10-04)

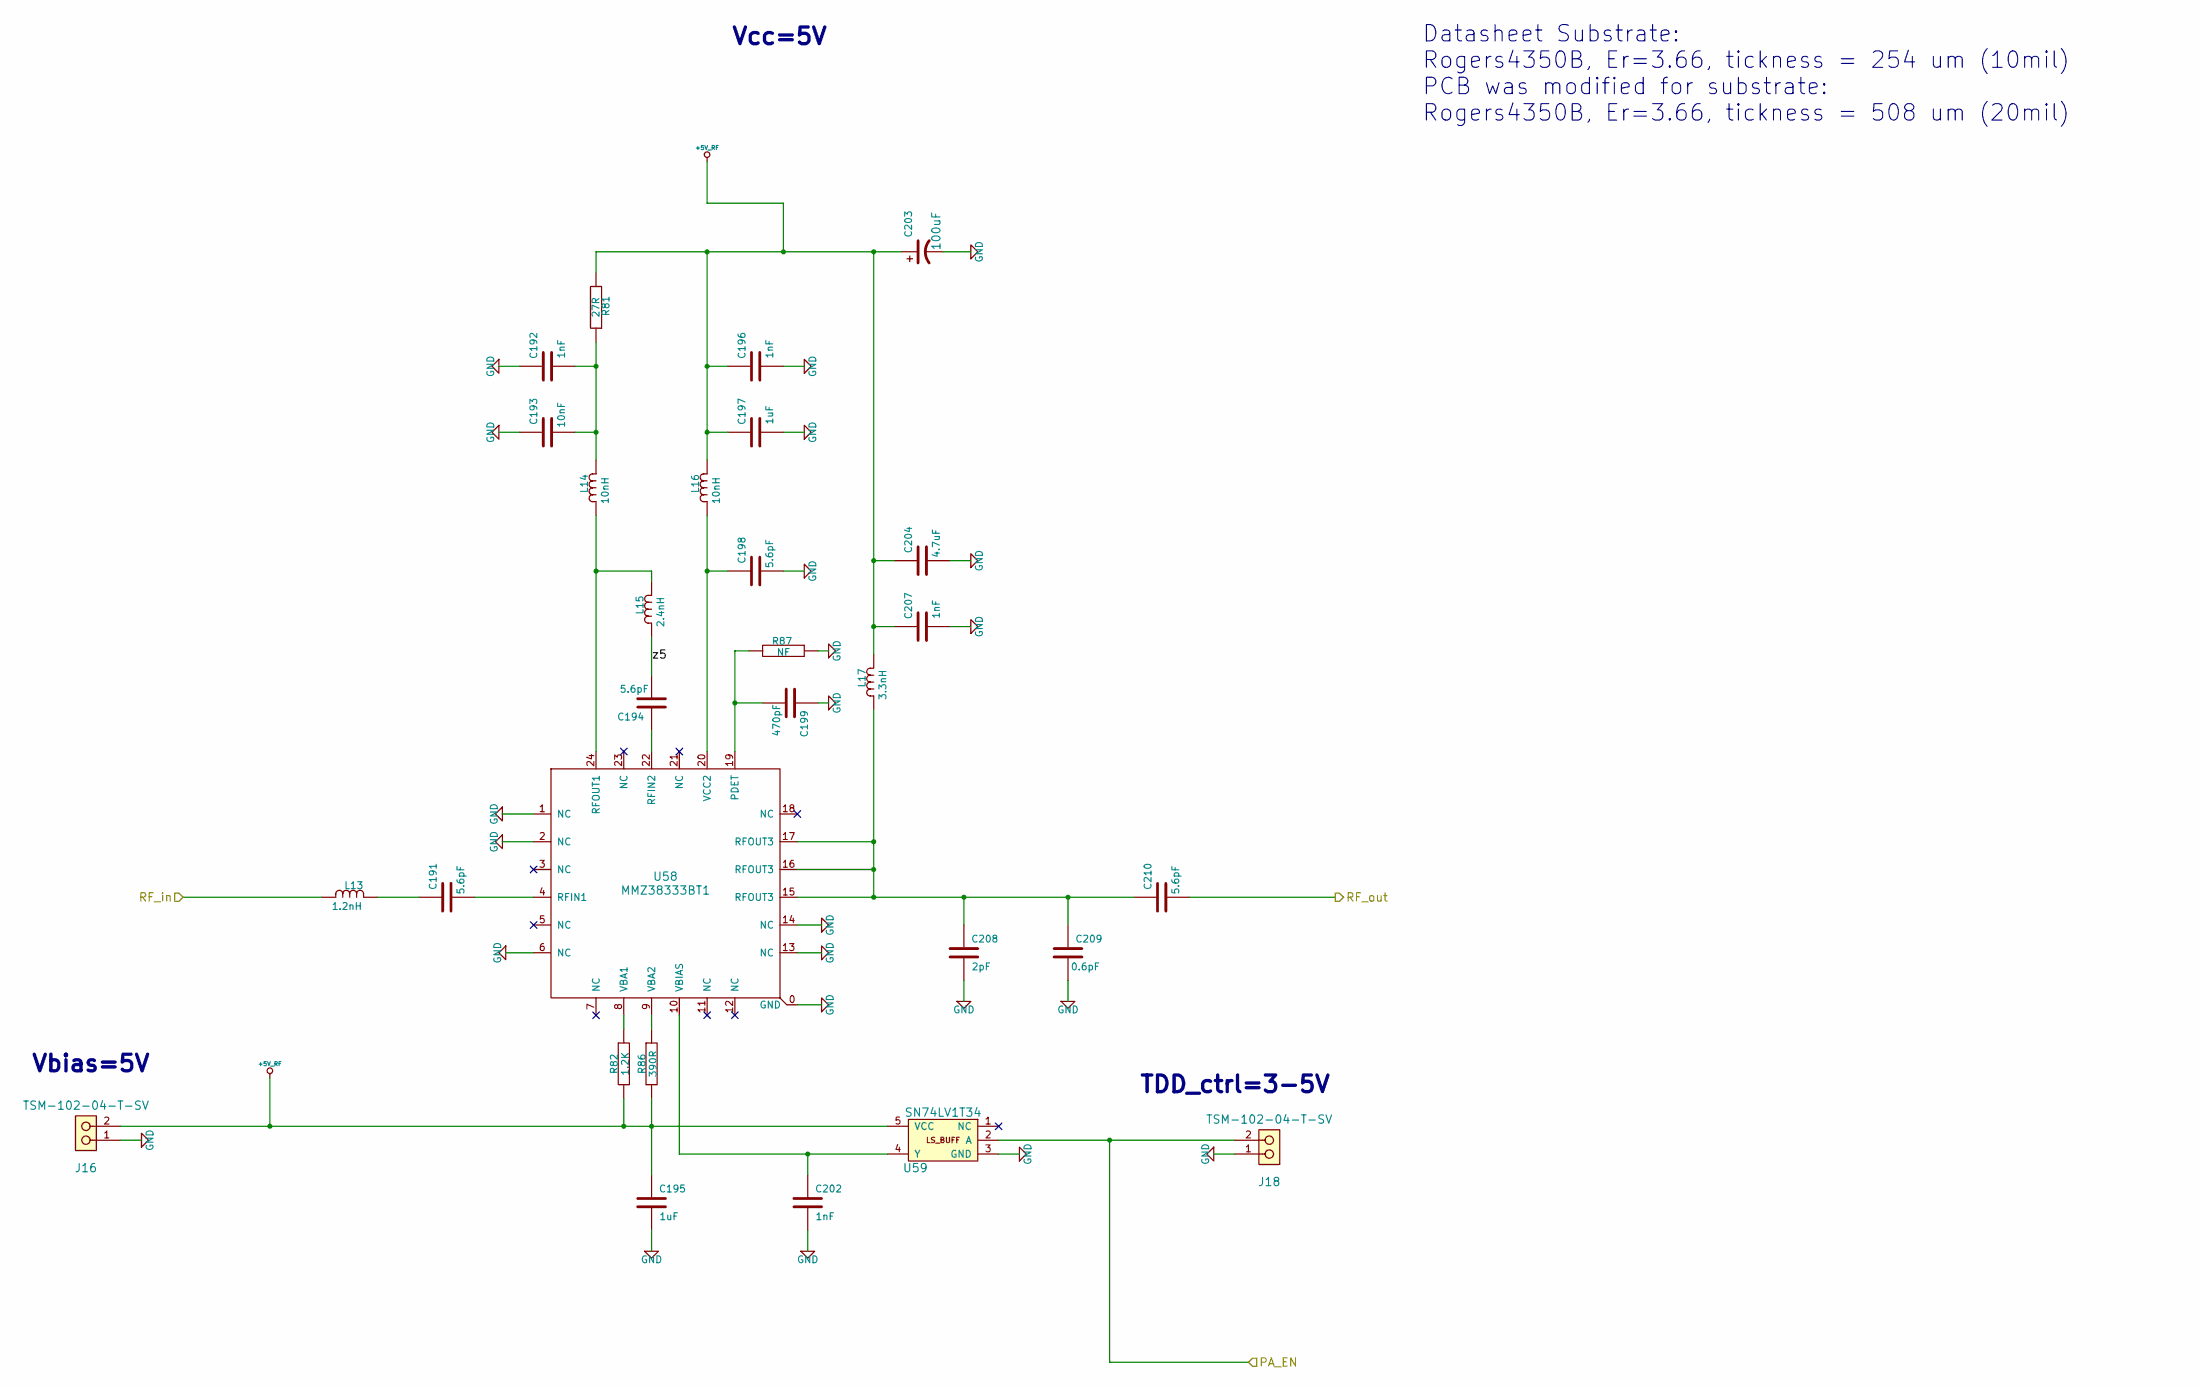
[picture p59: schematic PA1_A.sch]

Parts:
C191, C194, C198, C210: 5.6pF_0402_04023J5R6BBWTR; SMD0402; Manufacturer Part Number 04023J5R6BBWTR
C192, C196, C202, C207: 1nF_0402; SMD0402; Manufacturer Part Number CC0402KRX7R9BB102
C193: 10nF_0603_C0603C103J5RAC; SMD0603; Manufacturer Part Number C0603C103J5RAC
C195, C197: 1uF_0603; SMD0603; Manufacturer Part Number GRM188R61E105KA12D
C199: 470pF_0402_GRM1555C1H471JA01D; SMD0402; Manufacturer Part Number GRM1555C1H471JA01D
C203: 100uF_63V_Electrolytic_Panasonic; EEE-FK1J101P; Manufacturer Part Number EEE-FK1J101P
C204: 4.7uF_0603; SMD0603
C208: 2pF_0402_GRM1555C2A2R0CA01D; SMD0402; Manufacturer Part Number GRM1555C2A2R0CA01D
C209: 0.6pF_0402_GRM1555C2AR60BA01D; SMD0402; Manufacturer Part Number GRM1555C2AR60BA01D
J16, J18: TSM-102-04-T-SV; Manufacturer Part Number 200-TSM10204TSV
L13: 1.2nH_0402_0402CS-1N2XJLU; SMD0402; Manufacturer Part Number 0402CS-1N2XJLU
L14, L16: 10nH_0603_0603HP-10NXGLW; SMD0603; Manufacturer Part Number 0603HP-10NXGLW
L15: 2.4nH_0402_0402CS-2N4XGLU; SMD0402; Manufacturer Part Number 0402CS-2N4XGLU
L17: 3.3nH_0603_0603HP-3N3XJLW; SMD0603; Manufacturer Part Number 0603HP-3N3XJLW
R81: 27R_0402_ERJ2RKD27R0X; SMD0402; Manufacturer Part Number ERJ2RKD27R0X
R82: 1.2K_0402_AC0402JR-071K2L; SMD0402; Manufacturer Part Number AC0402JR-071K2L
R86: 390R_0402_RC0402JR-07390RL; SMD0402; Manufacturer Part Number RC0402JR-07390RL
R87: 0RNF_0402; SMD0402
U58: MMZ38333BT1; Manufacturer Part Number MMZ38333BT1
U59: SN74LV1T34; Manufacturer Part Number Texas Instruments

Connections:
+5V_RF: C195.1, C196.1, C197.1, C203.1, C204.1, C207.1, J16.2, L16.1, L17.1, R81.2, R82.2, R86.2, U59.5 (VCC)
GND: C192.1, C193.1, C195.2, C196.2, C197.2, C198.2, C199.1, C202.2, C203.2, C204.2, C207.2, C208.2, C209.2, J16.1, J18.1, R87.1, U58.0 (GND), U58.1 (NC), U58.2 (NC), U58.6 (NC), U58.13 (NC), U58.14 (NC), U59.3 (GND)
unnamed: C191.1, L13.1
unnamed: C191.2, U58.4 (RFIN1)
unnamed: C192.2, C193.2, L14.1, R81.1
unnamed: C194.1, U58.22 (RFIN2)
unnamed: C198.1, L16.2, U58.20 (VCC2)
unnamed: C199.2, R87.2, U58.19 (PDET)
unnamed: C202.1, U58.10 (VBIAS), U59.4 (Y)
unnamed: C208.1, C209.1, C210.1, L17.2, U58.15 (RFOUT3), U58.16 (RFOUT3), U58.17 (RFOUT3)
unnamed: L14.2, L15.1, U58.24 (RFOUT1)
unnamed: R82.1, U58.8 (VBA1)
unnamed: R86.1, U58.9 (VBA2)
PA_EN: J18.2, U59.2 (A)
RF_in: L13.2
RF_out: C210.2
z5: C194.2, L15.2

Notes on the sheet:
Vcc=5V
TDD_ctrl=3-5V
Vbias=5V
Datasheet Substrate: Rogers4350B, Er=3.66, tickness = 254 um (10mil) PCB was modified for substrate: Rogers4350B, Er=3.66, tickness = 508 um (20mil)
