myriadrf/LimeRFE-8001P/hardware/1v0/KiCAD/PA1_B.sch

## KiCad design hardware/1v0/KiCAD/PA1_B.sch (2023-10-04)

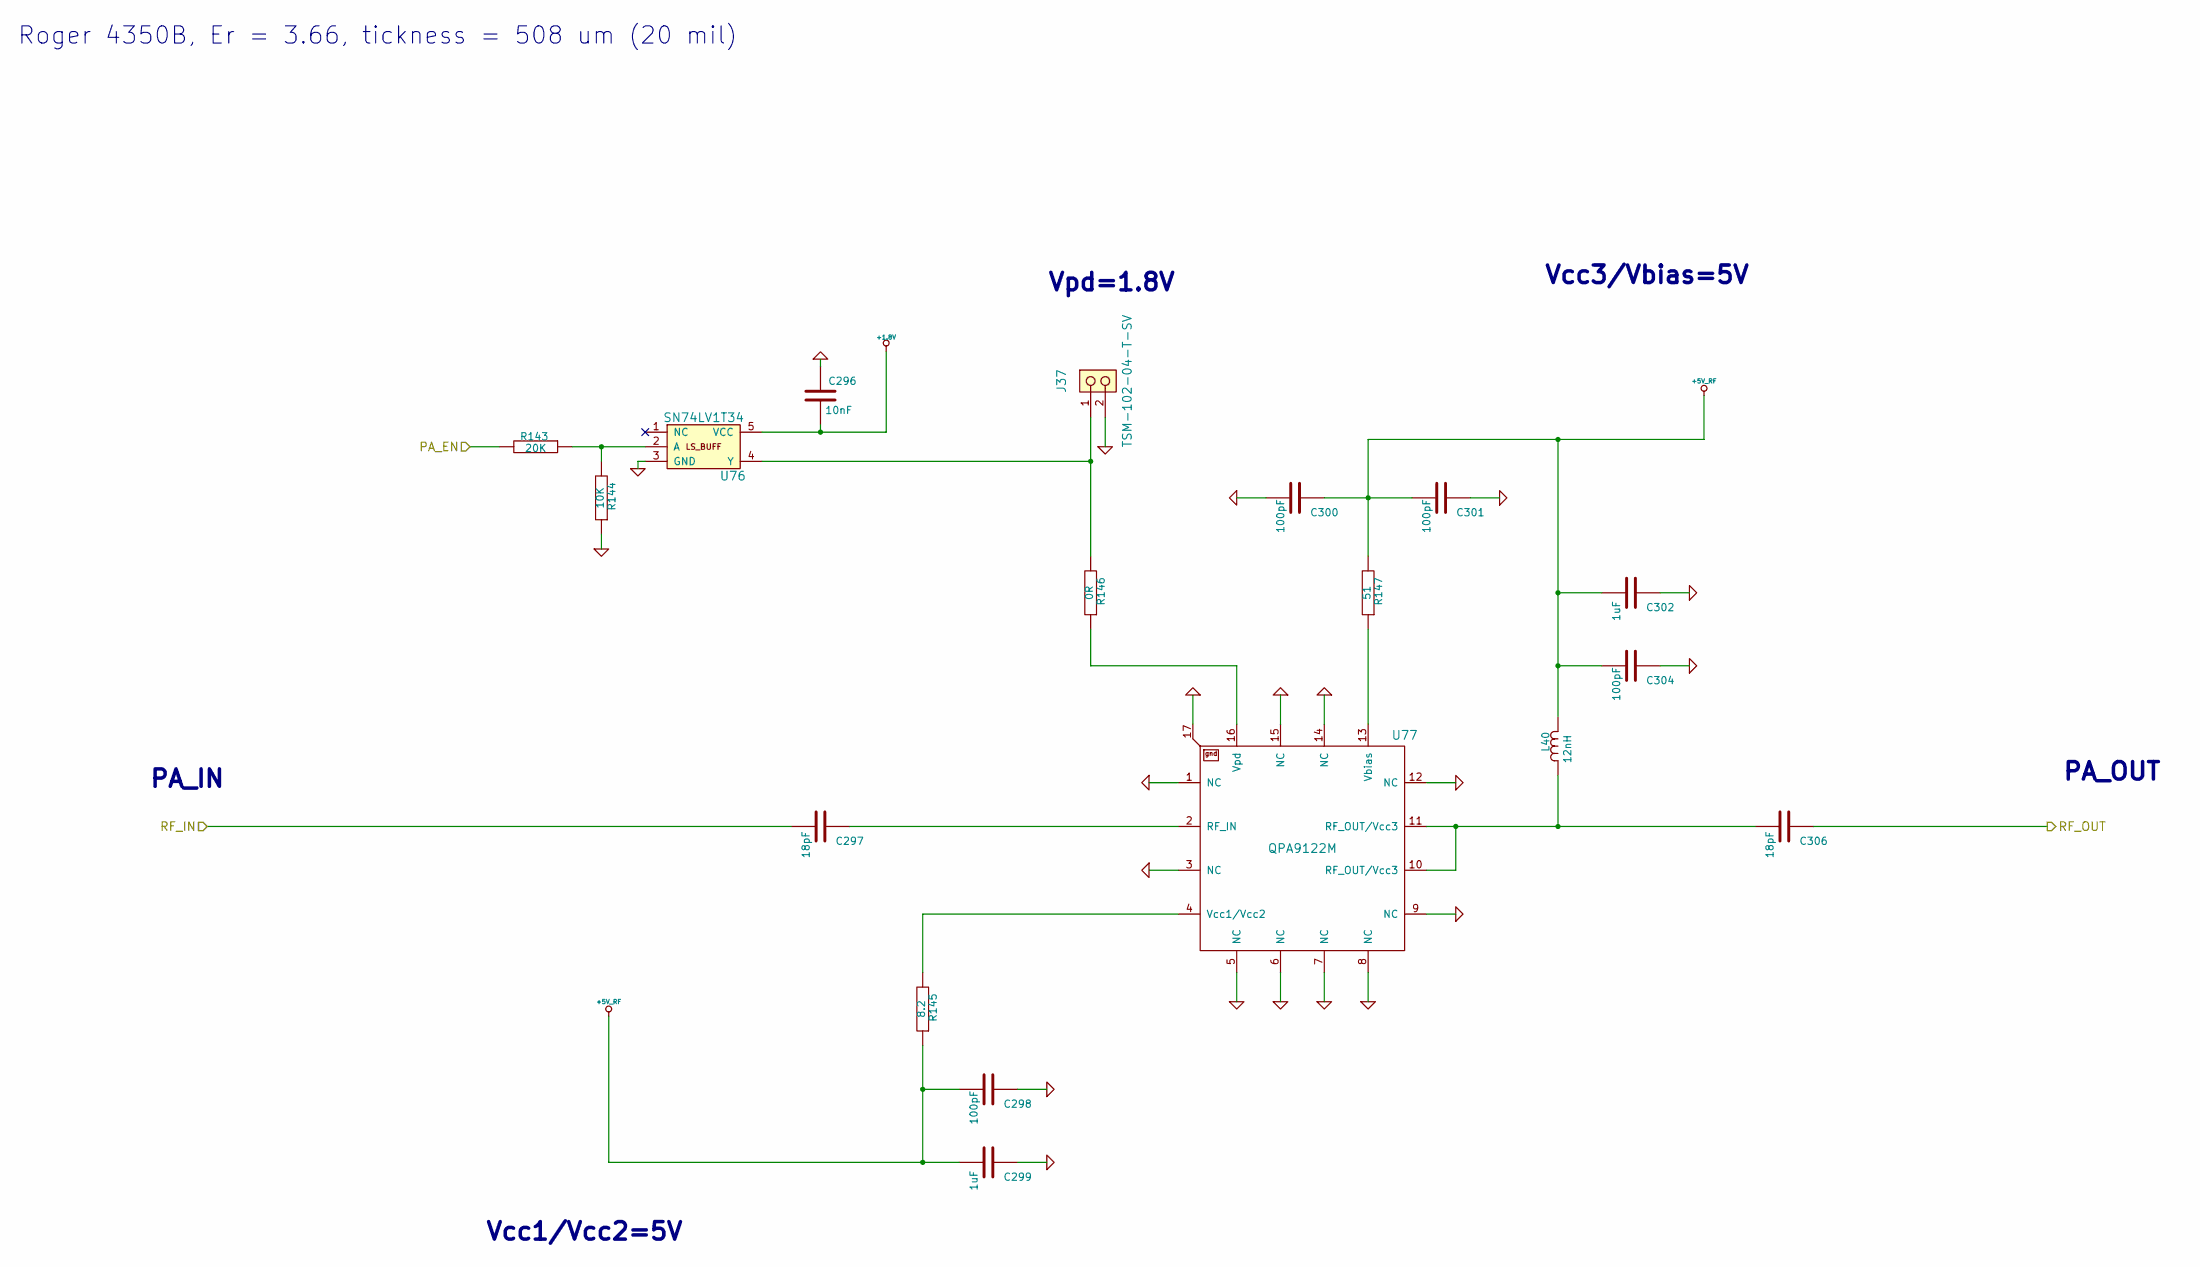
[picture p60: schematic PA1_B.sch]

Parts:
C296: 10nF_0402; SMD0402; Manufacturer Part Number CC0402ZRY5V7BB103
C297, C306: 18pF_0402_GRM1555C1H180JA01D; SMD0402; Manufacturer Part Number GRM1555C1H180JA01D
C298, C300, C301, C304: 100pF_0402_GRM1555C1H101JA01D; SMD0402; Manufacturer Part Number GRM1555C1H101JA01D
C299, C302: 1uF_0402_CC0402ZRY5V5BB105; SMD0402; Manufacturer Part Number CC0402ZRY5V5BB105
J37: TSM-102-04-T-SV; Manufacturer Part Number 200-TSM10204TSV
L40: 12nH_0402_0402CS-12NXJLW; SMD0402; Manufacturer Part Number 0402CS-12NXJLW
R143: 20K_0402_CRCW040220K0FKEDC; SMD0402; Manufacturer Part Number CRCW040220K0FKEDC
R144: 10K_0402; SMD0402
R145: 8.2_0402_CRCW04028R20FKED; SMD0402; Manufacturer Part Number CRCW04028R20FKED
R146: 0R_0402_RC0402JR-070RL; SMD0402; Manufacturer Part Number RC0402JR-070RL
R147: 51_0402_CRCW040251R0FKEDC; SMD0402; Manufacturer Part Number CRCW040251R0FKEDC
U76: SN74LV1T34; Manufacturer Part Number Texas Instruments
U77: QPA9122M; QPA9122MTR7; Manufacturer Part Number QPA9122MTR7

Connections:
+1.8V: C296.2, U76.5 (VCC)
+5V_RF: C298.2, C299.2, C300.1, C301.2, C302.2, C304.2, L40.1, R145.1, R147.2
GND: C296.1, C298.1, C299.1, C300.2, C301.1, C302.1, C304.1, J37.2, R144.1, U76.3 (GND), U77.1 (NC), U77.3 (NC), U77.5 (NC), U77.6 (NC), U77.7 (NC), U77.8 (NC), U77.9 (NC), U77.12 (NC), U77.14 (NC), U77.15 (NC), U77.17
unnamed: C297.1, U77.2 (RF_IN)
unnamed: C306.2, L40.2, U77.10 (RF_OUT/Vcc3), U77.11 (RF_OUT/Vcc3)
unnamed: J37.1, R146.2, U76.4 (Y)
unnamed: R143.1, R144.2, U76.2 (A)
unnamed: R145.2, U77.4 (Vcc1/Vcc2)
unnamed: R146.1, U77.16 (Vpd)
unnamed: R147.1, U77.13 (Vbias)
PA_EN: R143.2
RF_IN: C297.2
RF_OUT: C306.1

Notes on the sheet:
Roger 4350B, Er = 3.66, tickness = 508 um (20 mil)
PA_IN
PA_OUT
Vcc1/Vcc2=5V
Vcc3/Vbias=5V
Vpd=1.8V
