myriadrf/LimeRFE-8001P/hardware/1v0/KiCAD/PA1_a.sch

## KiCad design hardware/1v0/KiCAD/PA1_a.sch (2023-10-04)

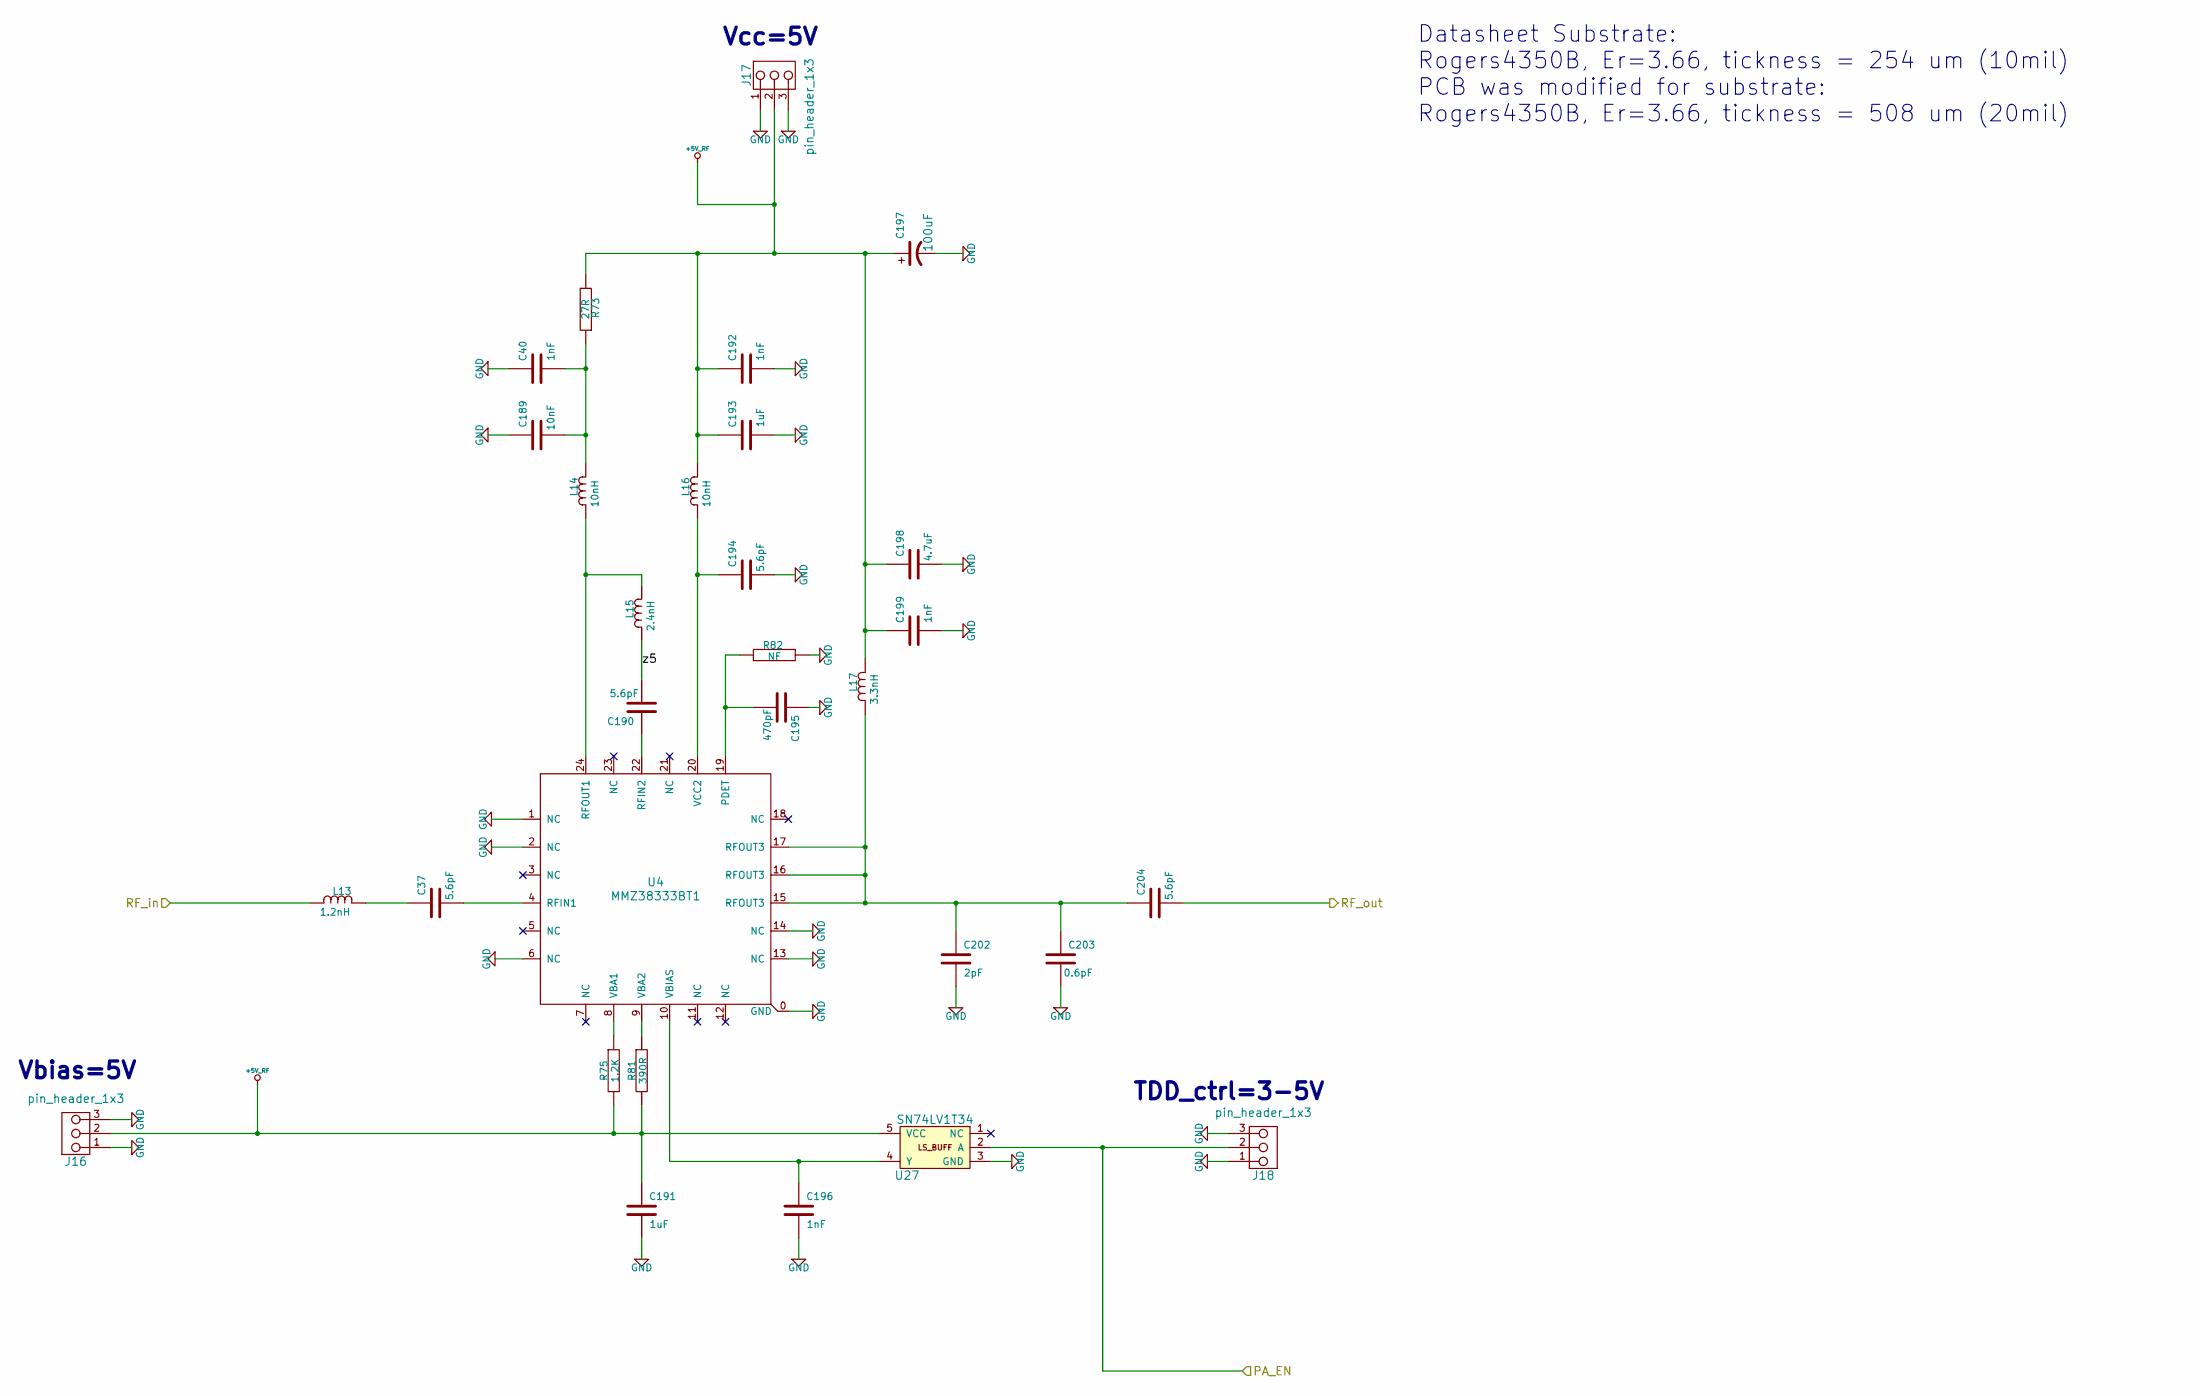
[picture p61: schematic PA1_a.sch]

Parts:
C37, C190, C194, C204: 5.6pF_0402_04023J5R6BBWTR; SMD0402; Manufacturer Part Number 04023J5R6BBWTR
C40, C192, C196, C199: 1nF_0402; SMD0402; Manufacturer Part Number CC0402KRX7R9BB102
C189: 10nF_0603_C0603C103J5RAC; SMD0603; Manufacturer Part Number C0603C103J5RAC
C191, C193: 1uF_0603; SMD0603; Manufacturer Part Number GRM188R61E105KA12D
C195: 470pF_0402_GRM1555C1H471JA01D; SMD0402; Manufacturer Part Number GRM1555C1H471JA01D
C197: 100uF_63V_Electrolytic_Panasonic; EEE-FK1J101P; Manufacturer Part Number EEE-FK1J101P
C198: 4.7uF_0603; SMD0603
C202: 2pF_0402_GRM1555C2A2R0CA01D; SMD0402; Manufacturer Part Number GRM1555C2A2R0CA01D
C203: 0.6pF_0402_GRM1555C2AR60BA01D; SMD0402; Manufacturer Part Number GRM1555C2AR60BA01D
J16, J17, J18: pin_header_1x3; PIN_Header_1x3_SMD; Manufacturer Part Number 68000-103HLF
L13: 1.2nH_0402_0402CS-1N2XJLU; SMD0402; Manufacturer Part Number 0402CS-1N2XJLU
L14, L16: 10nH_0603_0603HP-10NXGLW; SMD0603; Manufacturer Part Number 0603HP-10NXGLW
L15: 2.4nH_0402_0402CS-2N4XGLU; SMD0402; Manufacturer Part Number 0402CS-2N4XGLU
L17: 3.3nH_0603_0603HP-3N3XJLW; SMD0603; Manufacturer Part Number 0603HP-3N3XJLW
R73: 27R_0402_ERJ2RKD27R0X; SMD0603; Manufacturer Part Number ERJ2RKD27R0X
R75: 1.2K_0402_AC0402JR-071K2L; SMD0402; Manufacturer Part Number AC0402JR-071K2L
R81: 390R_0402_RC0402JR-07390RL; SMD0402; Manufacturer Part Number RC0402JR-07390RL
R82: 0RNF_0402; SMD0402
U4: MMZ38333BT1; Manufacturer Part Number MMZ38333BT1
U27: SN74LV1T34; Manufacturer Part Number Texas Instruments

Connections:
+5V_RF: C191.1, C192.1, C193.1, C197.1, C198.1, C199.1, J16.2, J17.2, L16.1, L17.1, R73.2, R75.2, R81.2, U27.5 (VCC)
GND: C40.1, C189.1, C191.2, C192.2, C193.2, C194.2, C195.1, C196.2, C197.2, C198.2, C199.2, C202.2, C203.2, J16.1, J16.3, J17.1, J17.3, J18.1, J18.3, R82.1, U4.0 (GND), U4.1 (NC), U4.2 (NC), U4.6 (NC), U4.13 (NC), U4.14 (NC), U27.3 (GND)
unnamed: C37.1, L13.1
unnamed: C37.2, U4.4 (RFIN1)
unnamed: C40.2, C189.2, L14.1, R73.1
unnamed: C190.1, U4.22 (RFIN2)
unnamed: C194.1, L16.2, U4.20 (VCC2)
unnamed: C195.2, R82.2, U4.19 (PDET)
unnamed: C196.1, U4.10 (VBIAS), U27.4 (Y)
unnamed: C202.1, C203.1, C204.1, L17.2, U4.15 (RFOUT3), U4.16 (RFOUT3), U4.17 (RFOUT3)
unnamed: L14.2, L15.1, U4.24 (RFOUT1)
unnamed: R75.1, U4.8 (VBA1)
unnamed: R81.1, U4.9 (VBA2)
PA_EN: J18.2, U27.2 (A)
RF_in: L13.2
RF_out: C204.2
z5: C190.2, L15.2

Notes on the sheet:
Vcc=5V
TDD_ctrl=3-5V
Vbias=5V
Datasheet Substrate: Rogers4350B, Er=3.66, tickness = 254 um (10mil) PCB was modified for substrate: Rogers4350B, Er=3.66, tickness = 508 um (20mil)
