myriadrf/LimeRFE-8001P/hardware/1v0/KiCAD/PA2_A.sch

## KiCad design hardware/1v0/KiCAD/PA2_A.sch (2023-10-04)

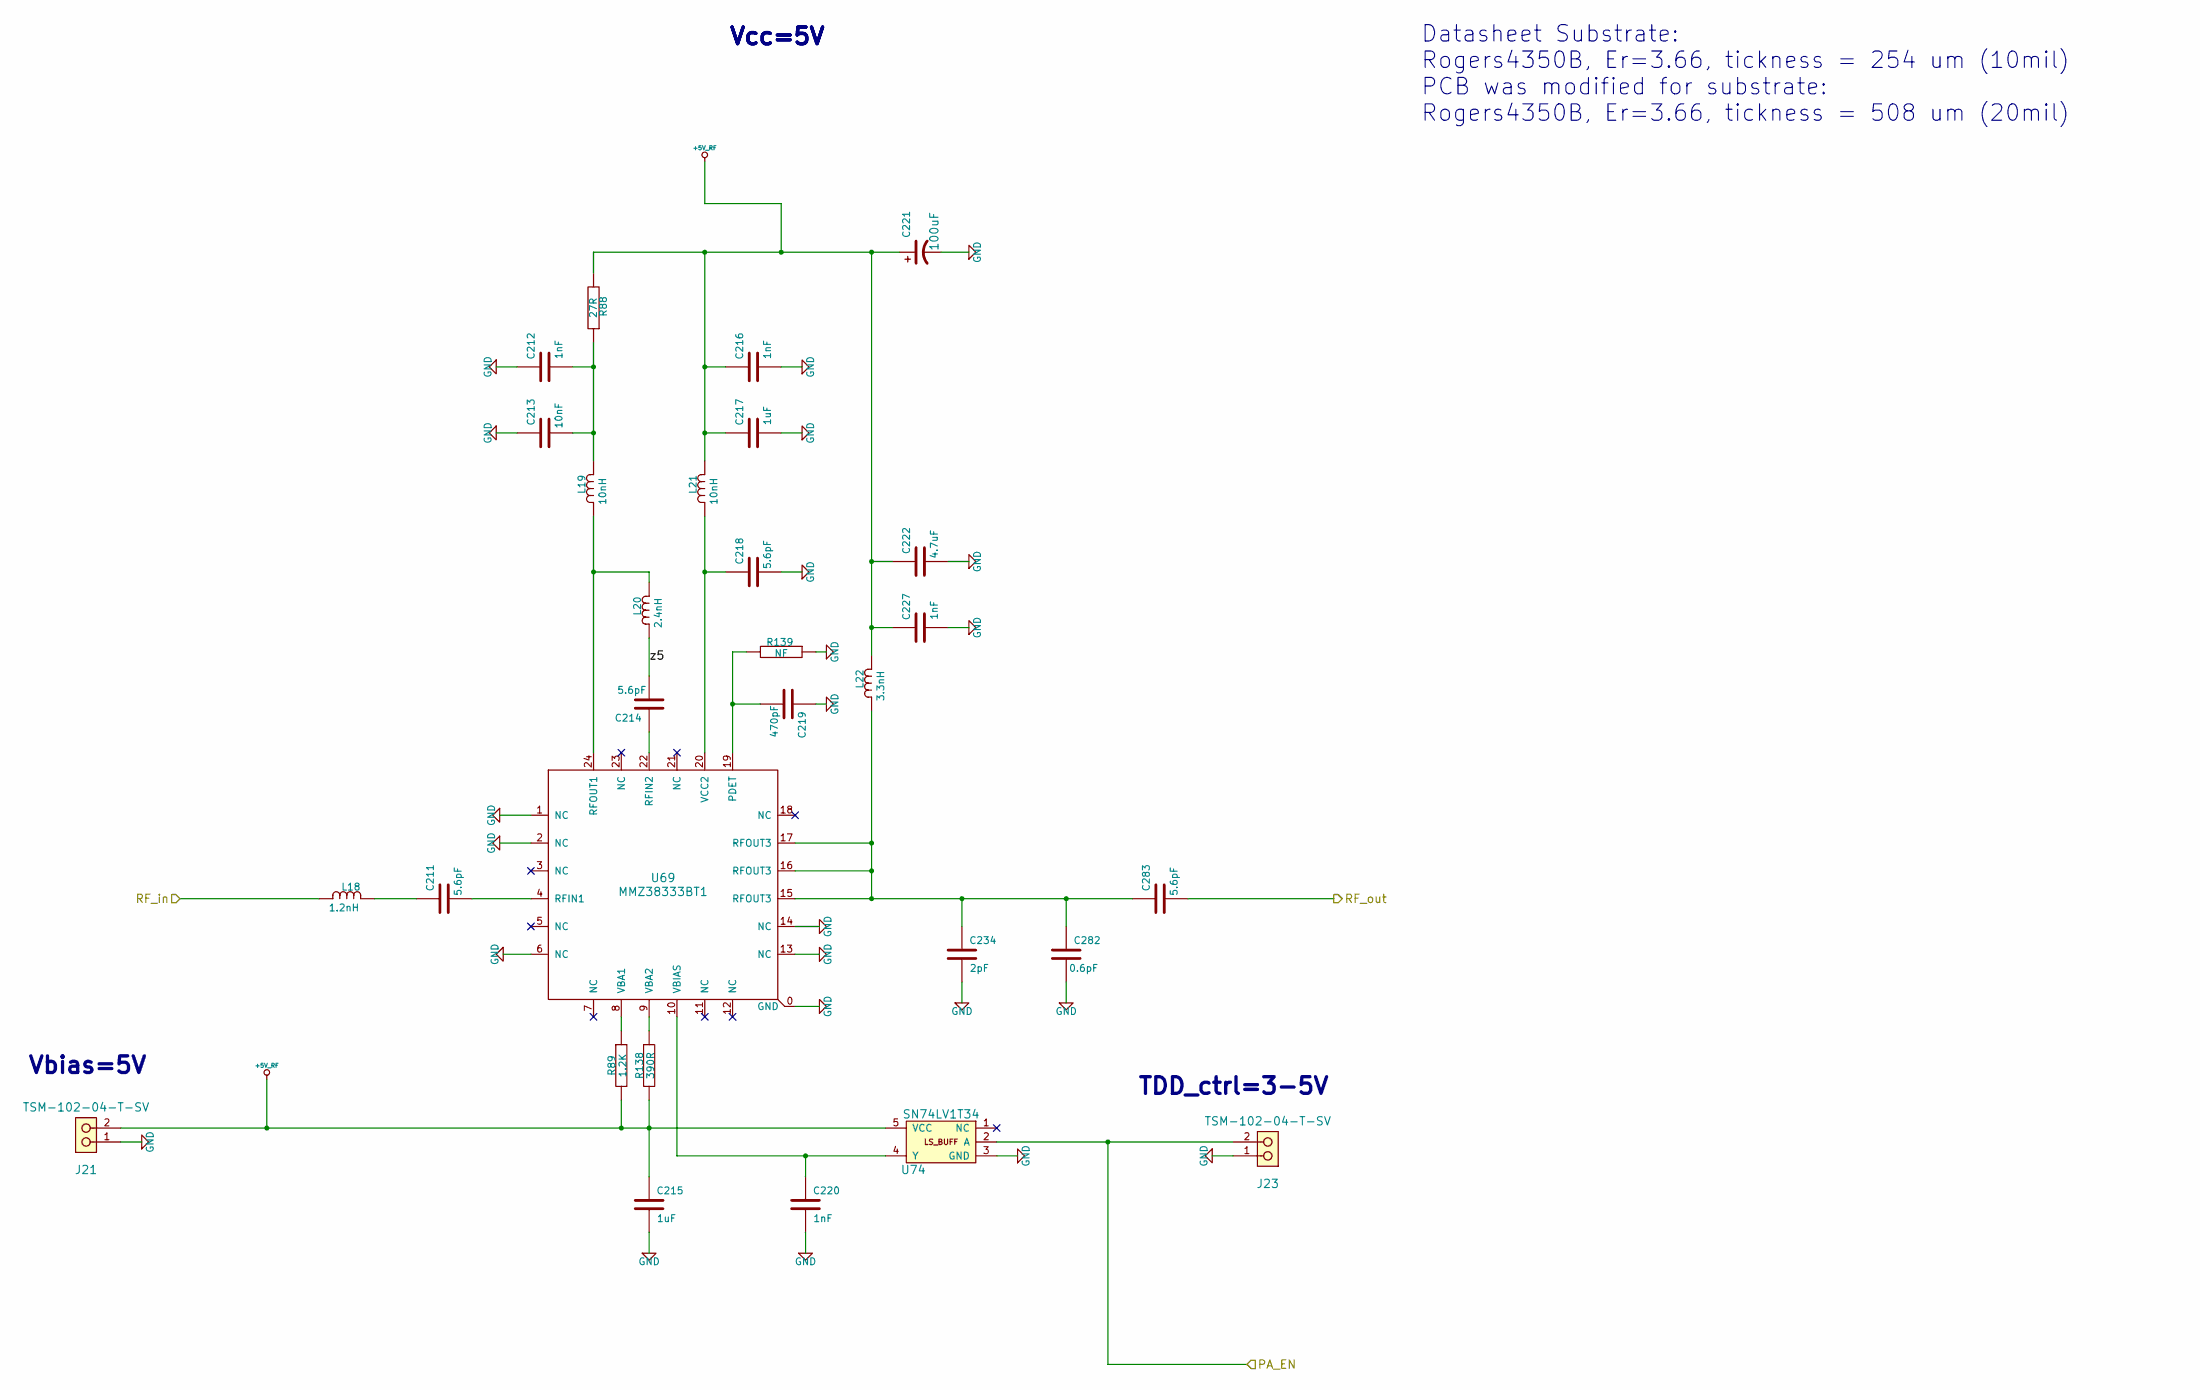
[picture p62: schematic PA2_A.sch]

Parts:
C211, C214, C218, C283: 5.6pF_0402_04023J5R6BBWTR; SMD0402; Manufacturer Part Number 04023J5R6BBWTR
C212, C216, C220, C227: 1nF_0402; SMD0402; Manufacturer Part Number CC0402KRX7R9BB102
C213: 10nF_0603_C0603C103J5RAC; SMD0603; Manufacturer Part Number C0603C103J5RAC
C215, C217: 1uF_0603; SMD0603; Manufacturer Part Number GRM188R61E105KA12D
C219: 470pF_0402_GRM1555C1H471JA01D; SMD0402; Manufacturer Part Number GRM1555C1H471JA01D
C221: 100uF_63V_Electrolytic_Panasonic; EEE-FK1J101P; Manufacturer Part Number EEE-FK1J101P
C222: 4.7uF_0603; SMD0603
C234: 2pF_0402_GRM1555C2A2R0CA01D; SMD0402; Manufacturer Part Number GRM1555C2A2R0CA01D
C282: 0.6pF_0402_GRM1555C2AR60BA01D; SMD0402; Manufacturer Part Number GRM1555C2AR60BA01D
J21, J23: TSM-102-04-T-SV; Manufacturer Part Number 200-TSM10204TSV
L18: 1.2nH_0402_0402CS-1N2XJLU; SMD0402; Manufacturer Part Number 0402CS-1N2XJLU
L19, L21: 10nH_0603_0603HP-10NXGLW; SMD0603; Manufacturer Part Number 0603HP-10NXGLW
L20: 2.4nH_0402_0402CS-2N4XGLU; SMD0402; Manufacturer Part Number 0402CS-2N4XGLU
L22: 3.3nH_0603_0603HP-3N3XJLW; SMD0603; Manufacturer Part Number 0603HP-3N3XJLW
R88: 27R_0402_ERJ2RKD27R0X; SMD0402; Manufacturer Part Number ERJ2RKD27R0X
R89: 1.2K_0402_AC0402JR-071K2L; SMD0402; Manufacturer Part Number AC0402JR-071K2L
R138: 390R_0402_RC0402JR-07390RL; SMD0402; Manufacturer Part Number RC0402JR-07390RL
R139: 0RNF_0402; SMD0402
U69: MMZ38333BT1; Manufacturer Part Number MMZ38333BT1
U74: SN74LV1T34; Manufacturer Part Number Texas Instruments

Connections:
+5V_RF: C215.1, C216.1, C217.1, C221.1, C222.1, C227.1, J21.2, L21.1, L22.1, R88.2, R89.2, R138.2, U74.5 (VCC)
GND: C212.1, C213.1, C215.2, C216.2, C217.2, C218.2, C219.1, C220.2, C221.2, C222.2, C227.2, C234.2, C282.2, J21.1, J23.1, R139.1, U69.0 (GND), U69.1 (NC), U69.2 (NC), U69.6 (NC), U69.13 (NC), U69.14 (NC), U74.3 (GND)
unnamed: C211.1, L18.1
unnamed: C211.2, U69.4 (RFIN1)
unnamed: C212.2, C213.2, L19.1, R88.1
unnamed: C214.1, U69.22 (RFIN2)
unnamed: C218.1, L21.2, U69.20 (VCC2)
unnamed: C219.2, R139.2, U69.19 (PDET)
unnamed: C220.1, U69.10 (VBIAS), U74.4 (Y)
unnamed: C234.1, C282.1, C283.1, L22.2, U69.15 (RFOUT3), U69.16 (RFOUT3), U69.17 (RFOUT3)
unnamed: L19.2, L20.1, U69.24 (RFOUT1)
unnamed: R89.1, U69.8 (VBA1)
unnamed: R138.1, U69.9 (VBA2)
PA_EN: J23.2, U74.2 (A)
RF_in: L18.2
RF_out: C283.2
z5: C214.2, L20.2

Notes on the sheet:
Vcc=5V
TDD_ctrl=3-5V
Vbias=5V
Datasheet Substrate: Rogers4350B, Er=3.66, tickness = 254 um (10mil) PCB was modified for substrate: Rogers4350B, Er=3.66, tickness = 508 um (20mil)
