myriadrf/LimeRFE-8001P/hardware/1v0/KiCAD/PA2_B.sch

## KiCad design hardware/1v0/KiCAD/PA2_B.sch (2023-10-04)

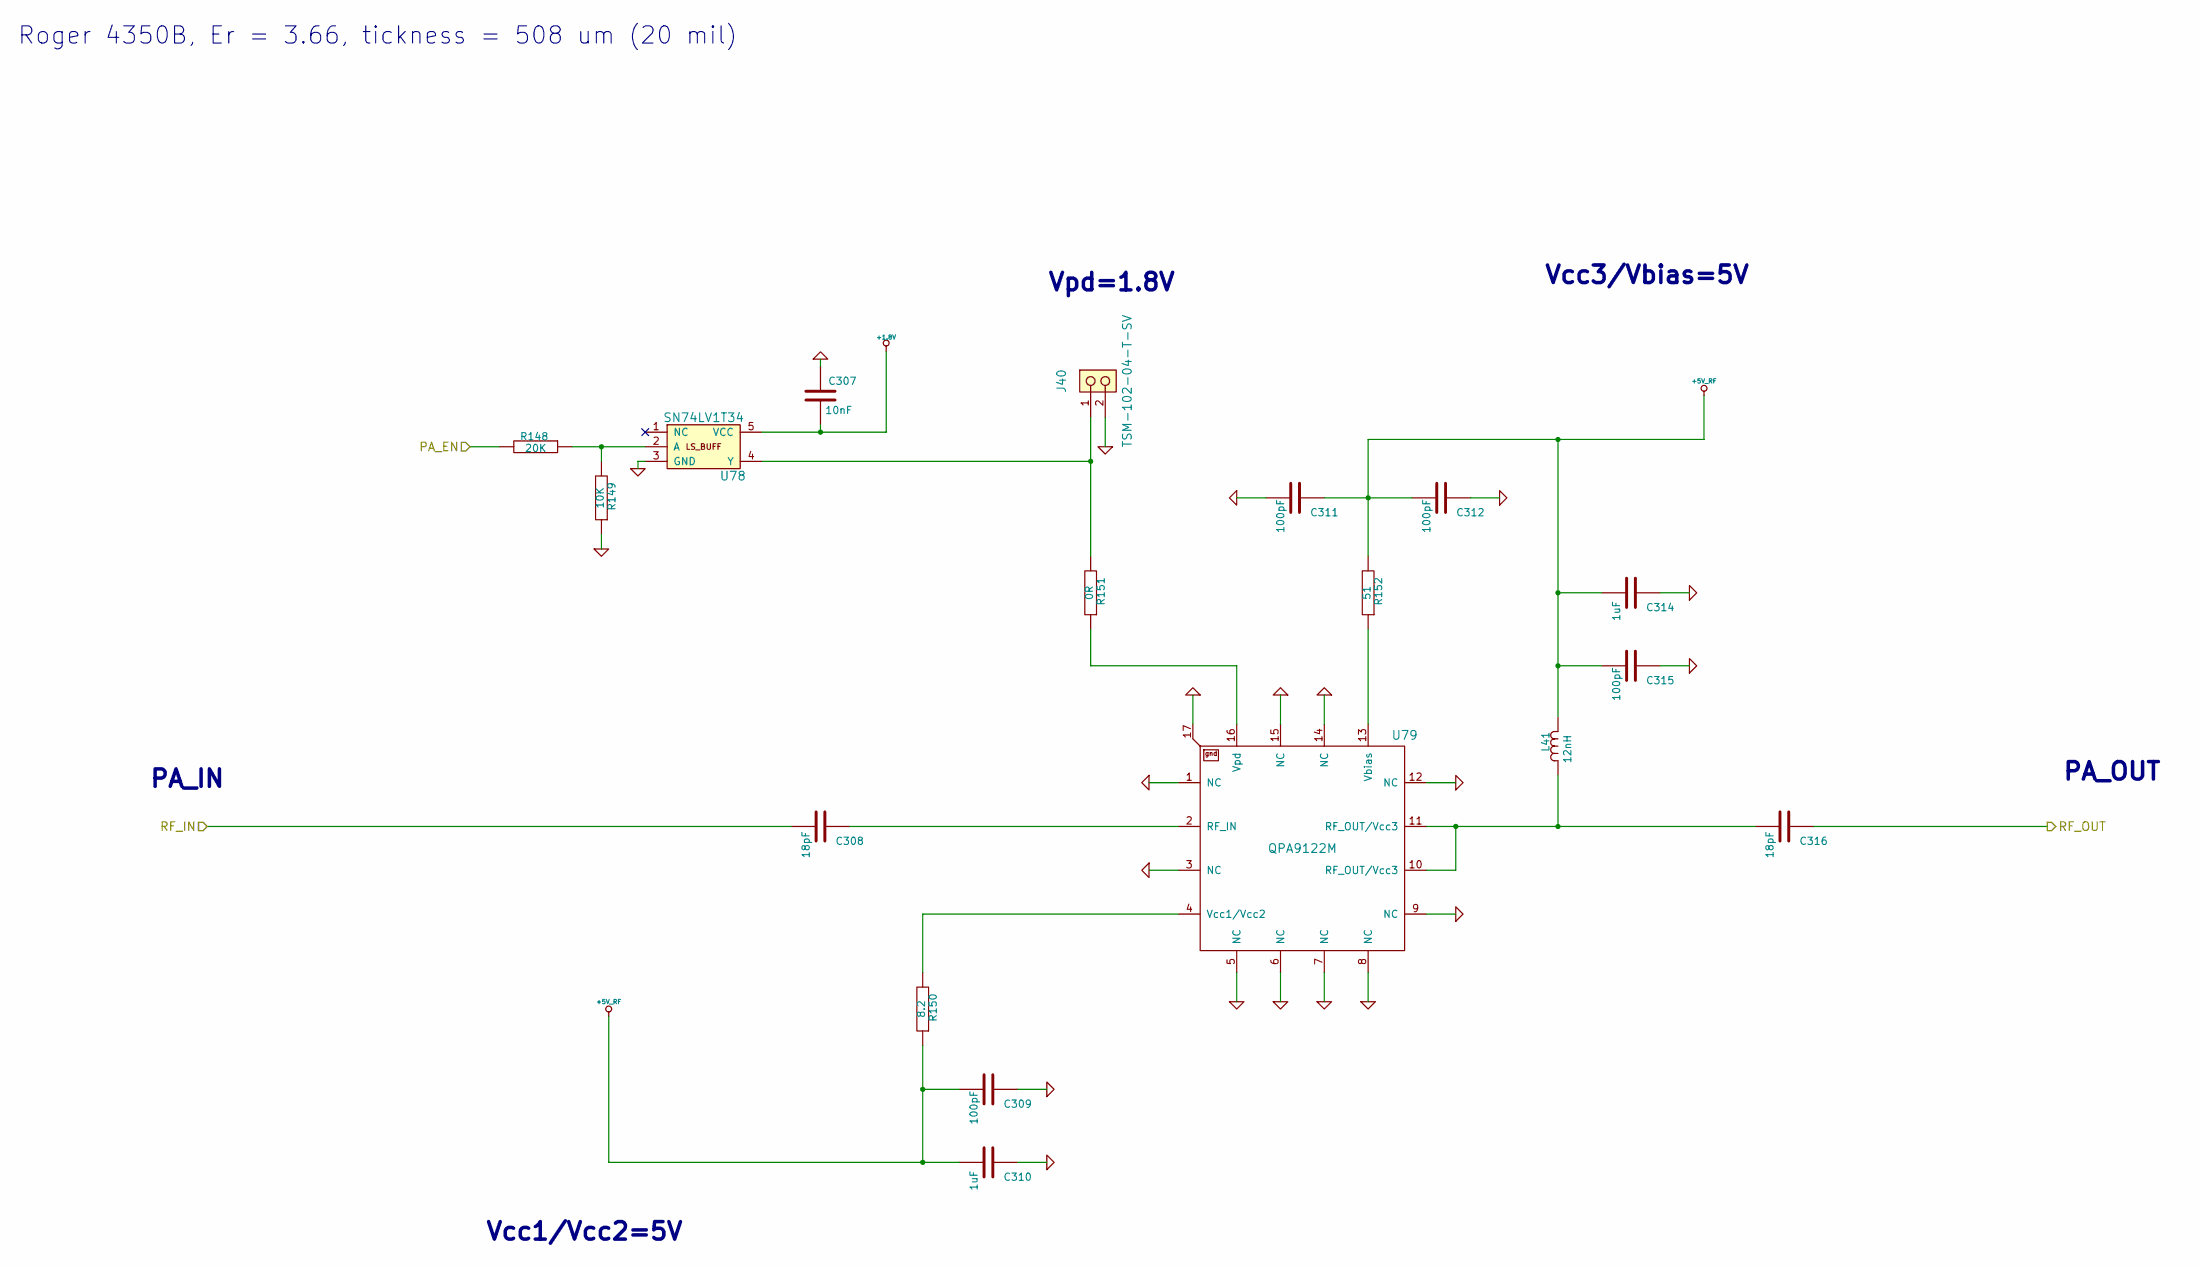
[picture p63: schematic PA2_B.sch]

Parts:
C307: 10nF_0402; SMD0402; Manufacturer Part Number CC0402ZRY5V7BB103
C308, C316: 18pF_0402_GRM1555C1H180JA01D; SMD0402; Manufacturer Part Number GRM1555C1H180JA01D
C309, C311, C312, C315: 100pF_0402_GRM1555C1H101JA01D; SMD0402; Manufacturer Part Number GRM1555C1H101JA01D
C310, C314: 1uF_0402_CC0402ZRY5V5BB105; SMD0402; Manufacturer Part Number CC0402ZRY5V5BB105
J40: TSM-102-04-T-SV; Manufacturer Part Number 200-TSM10204TSV
L41: 12nH_0402_0402CS-12NXJLW; SMD0402; Manufacturer Part Number 0402CS-12NXJLW
R148: 20K_0402_CRCW040220K0FKEDC; SMD0402; Manufacturer Part Number CRCW040220K0FKEDC
R149: 10K_0402; SMD0402
R150: 8.2_0402_CRCW04028R20FKED; SMD0402; Manufacturer Part Number CRCW04028R20FKED
R151: 0R_0402_RC0402JR-070RL; SMD0402; Manufacturer Part Number RC0402JR-070RL
R152: 51_0402_CRCW040251R0FKEDC; SMD0402; Manufacturer Part Number CRCW040251R0FKEDC
U78: SN74LV1T34; Manufacturer Part Number Texas Instruments
U79: QPA9122M; QPA9122MTR7; Manufacturer Part Number QPA9122MTR7

Connections:
+1.8V: C307.2, U78.5 (VCC)
+5V_RF: C309.2, C310.2, C311.1, C312.2, C314.2, C315.2, L41.1, R150.1, R152.2
GND: C307.1, C309.1, C310.1, C311.2, C312.1, C314.1, C315.1, J40.2, R149.1, U78.3 (GND), U79.1 (NC), U79.3 (NC), U79.5 (NC), U79.6 (NC), U79.7 (NC), U79.8 (NC), U79.9 (NC), U79.12 (NC), U79.14 (NC), U79.15 (NC), U79.17
unnamed: C308.1, U79.2 (RF_IN)
unnamed: C316.2, L41.2, U79.10 (RF_OUT/Vcc3), U79.11 (RF_OUT/Vcc3)
unnamed: J40.1, R151.2, U78.4 (Y)
unnamed: R148.1, R149.2, U78.2 (A)
unnamed: R150.2, U79.4 (Vcc1/Vcc2)
unnamed: R151.1, U79.16 (Vpd)
unnamed: R152.1, U79.13 (Vbias)
PA_EN: R148.2
RF_IN: C308.2
RF_OUT: C316.1

Notes on the sheet:
Roger 4350B, Er = 3.66, tickness = 508 um (20 mil)
PA_IN
PA_OUT
Vcc1/Vcc2=5V
Vcc3/Vbias=5V
Vpd=1.8V
