myriadrf/LimeRFE-8001P/hardware/1v0/KiCAD/PowerSupply.sch

## KiCad design hardware/1v0/KiCAD/PowerSupply.sch (2023-10-04)

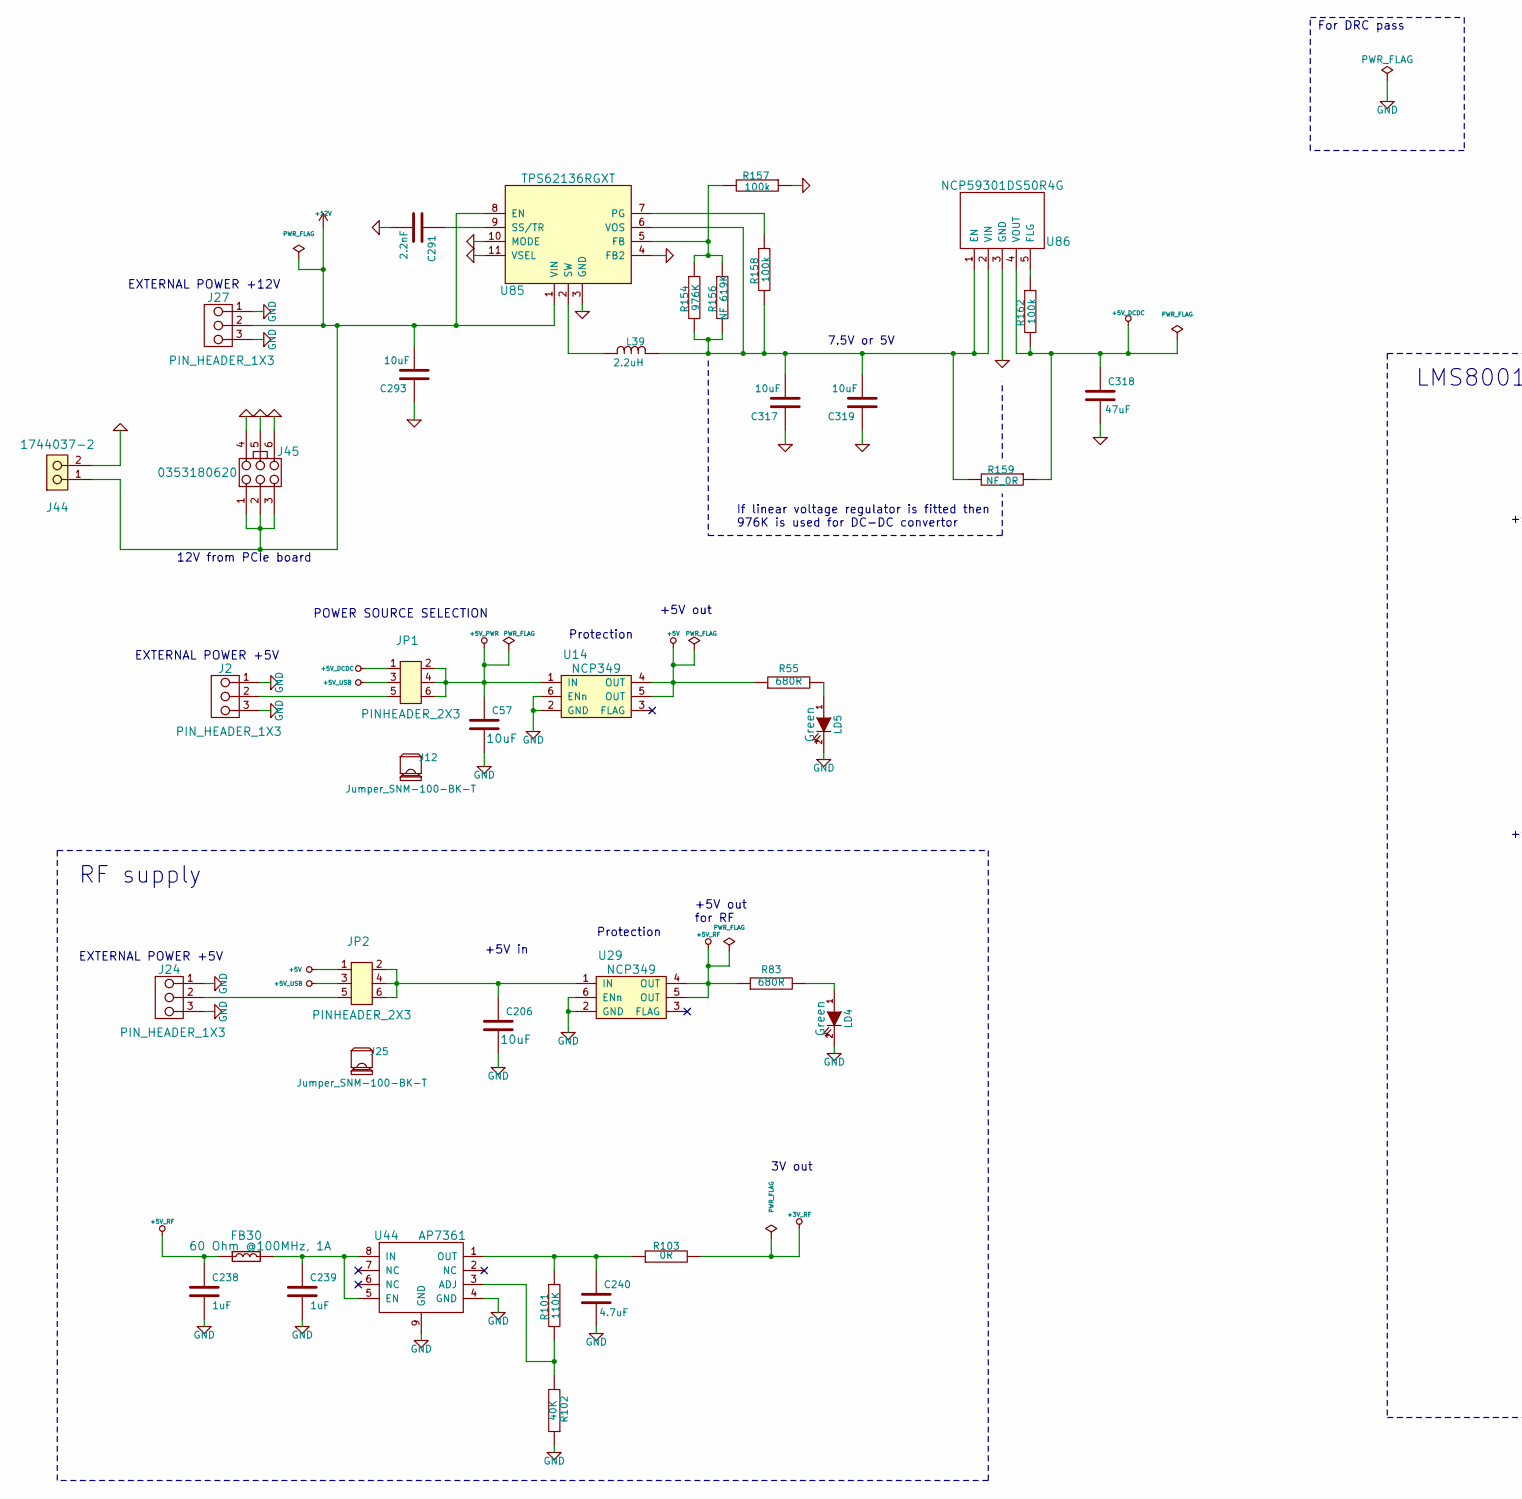
[picture p64: schematic PowerSupply.sch, part in row 1, column 1]

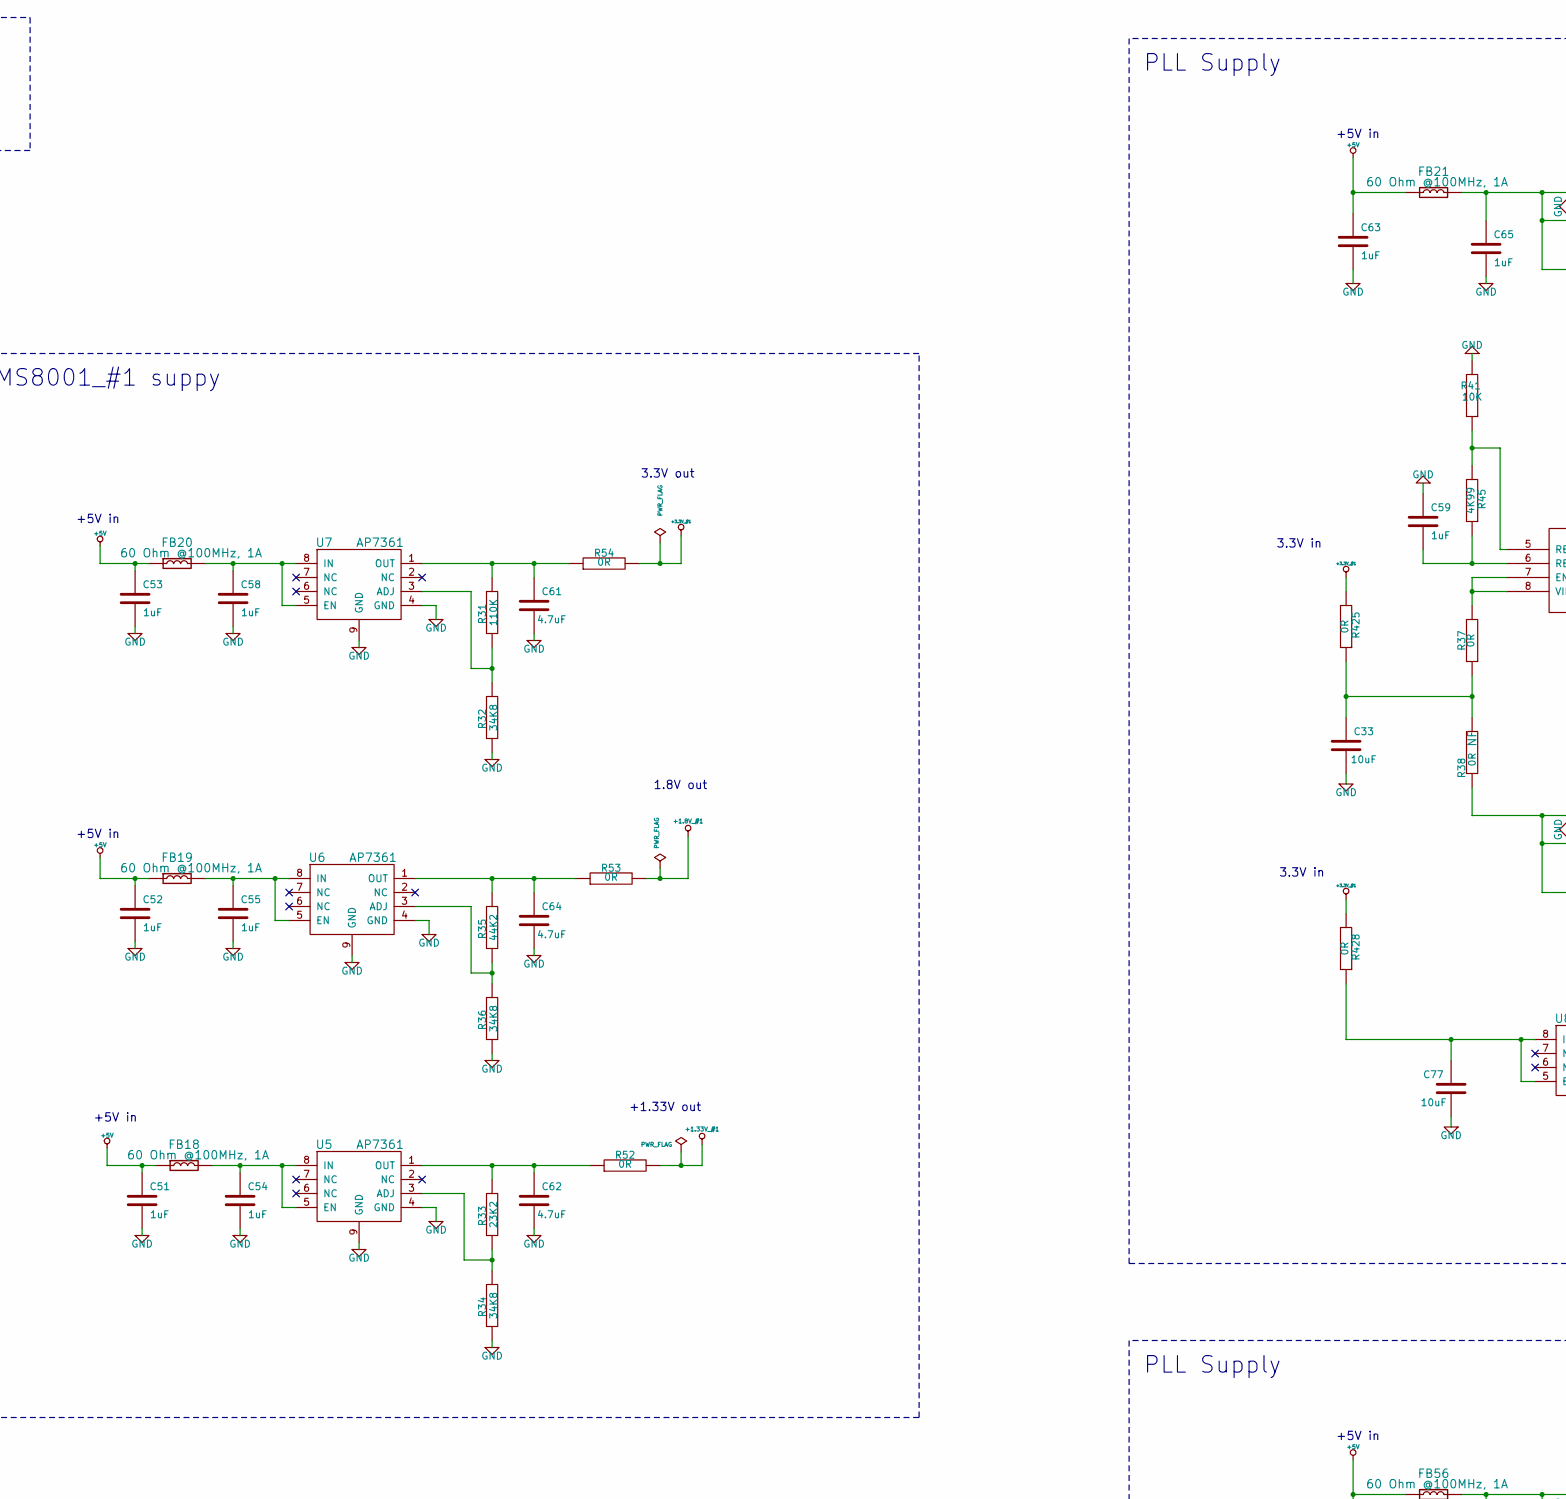
[picture p65: schematic PowerSupply.sch, part in row 1, column 2]

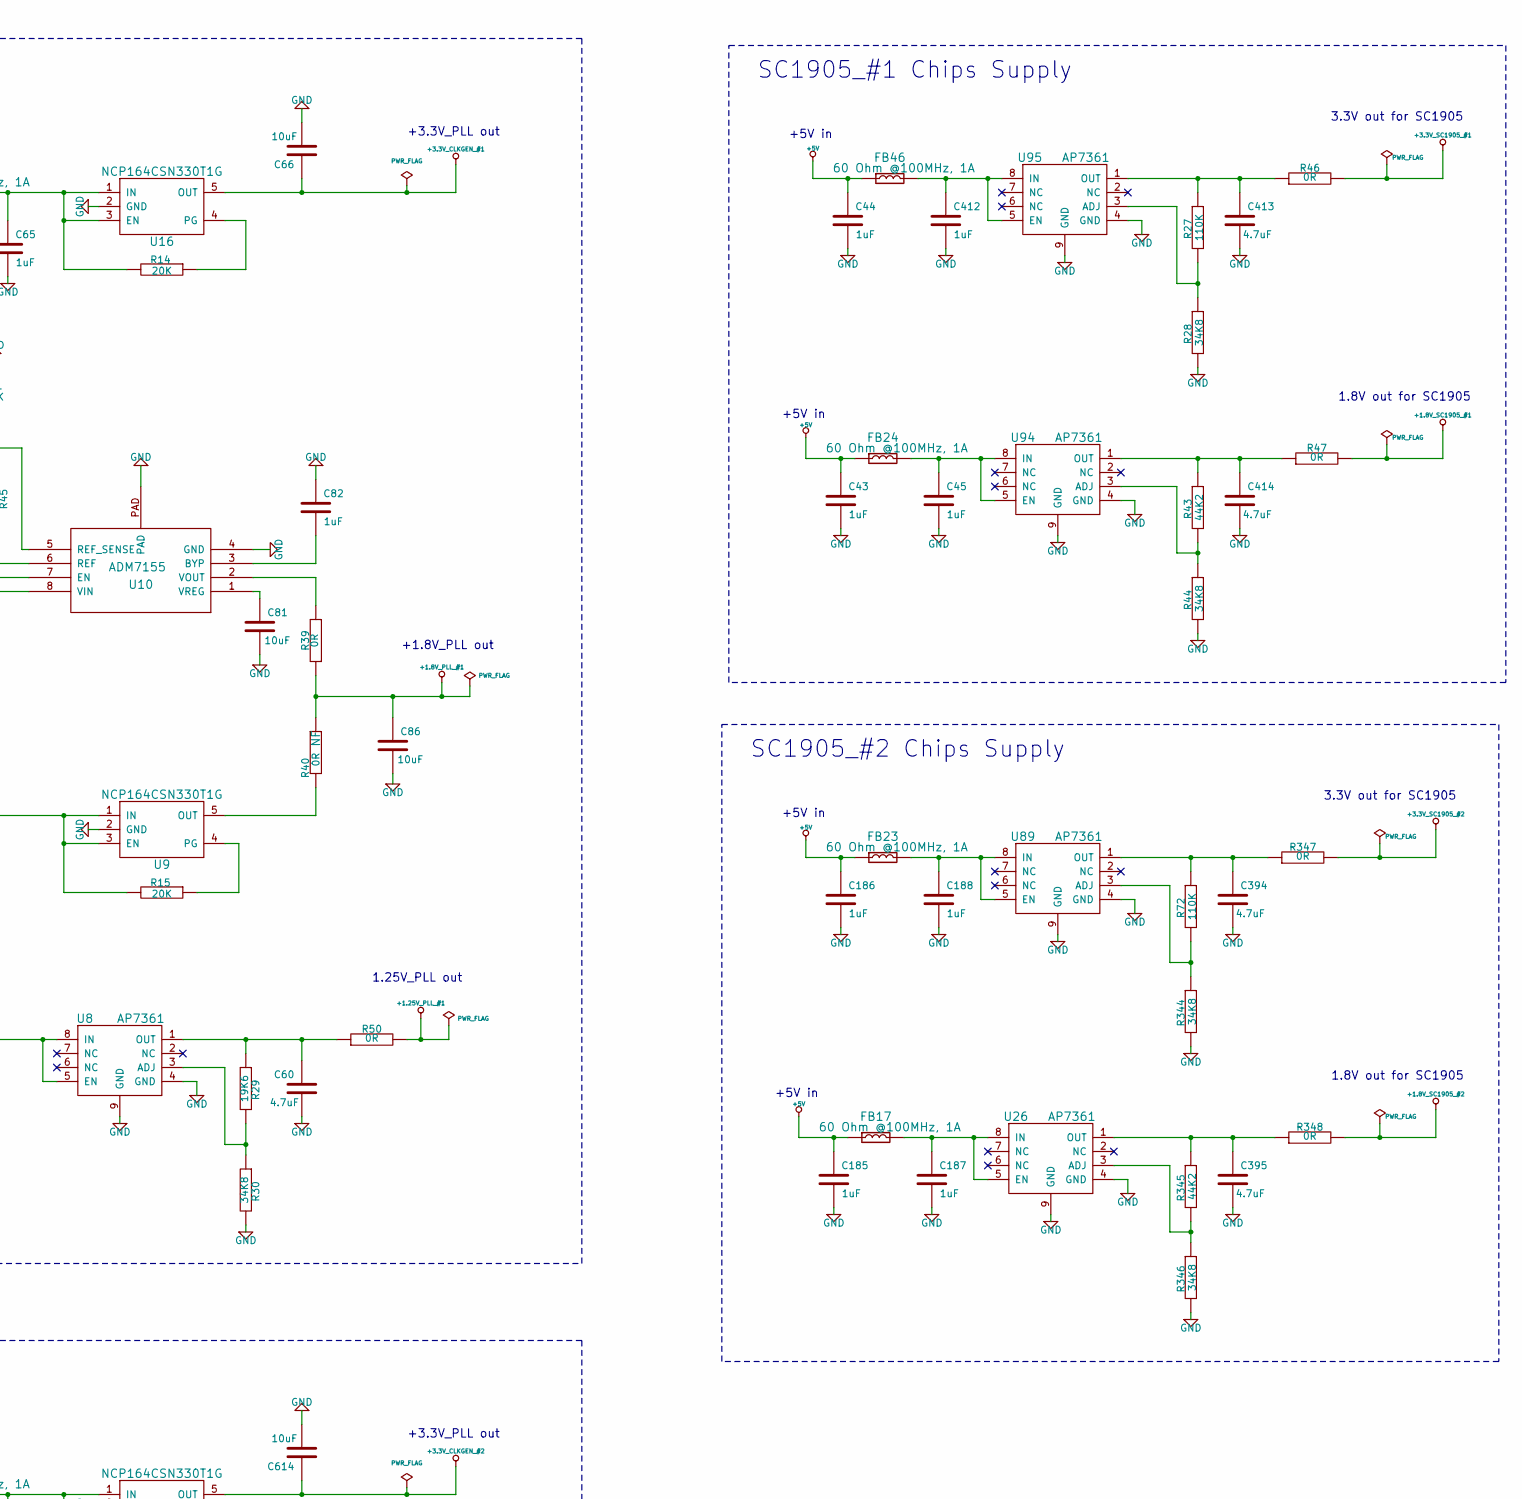
[picture p66: schematic PowerSupply.sch, part in row 1, column 3]

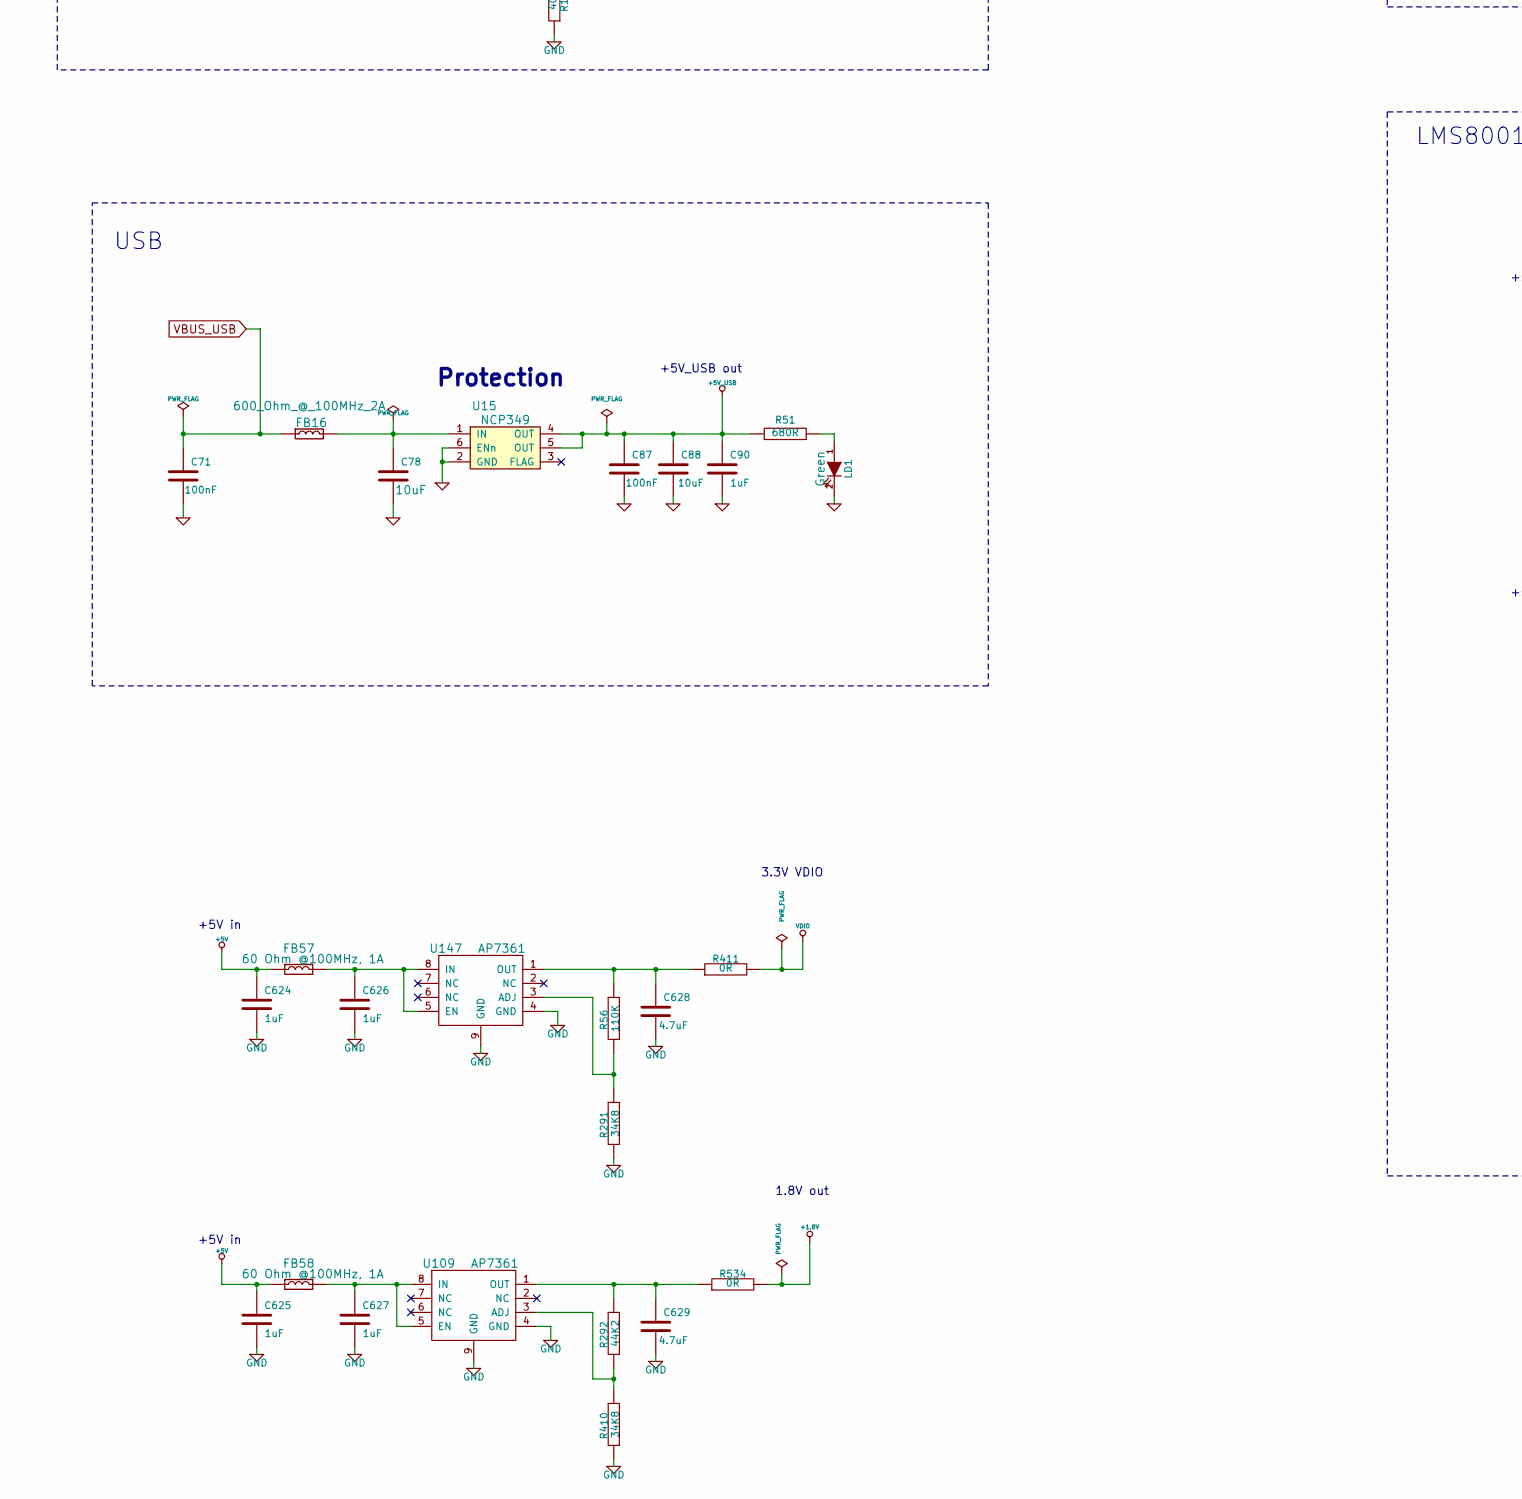
[picture p67: schematic PowerSupply.sch, part in row 2, column 1]

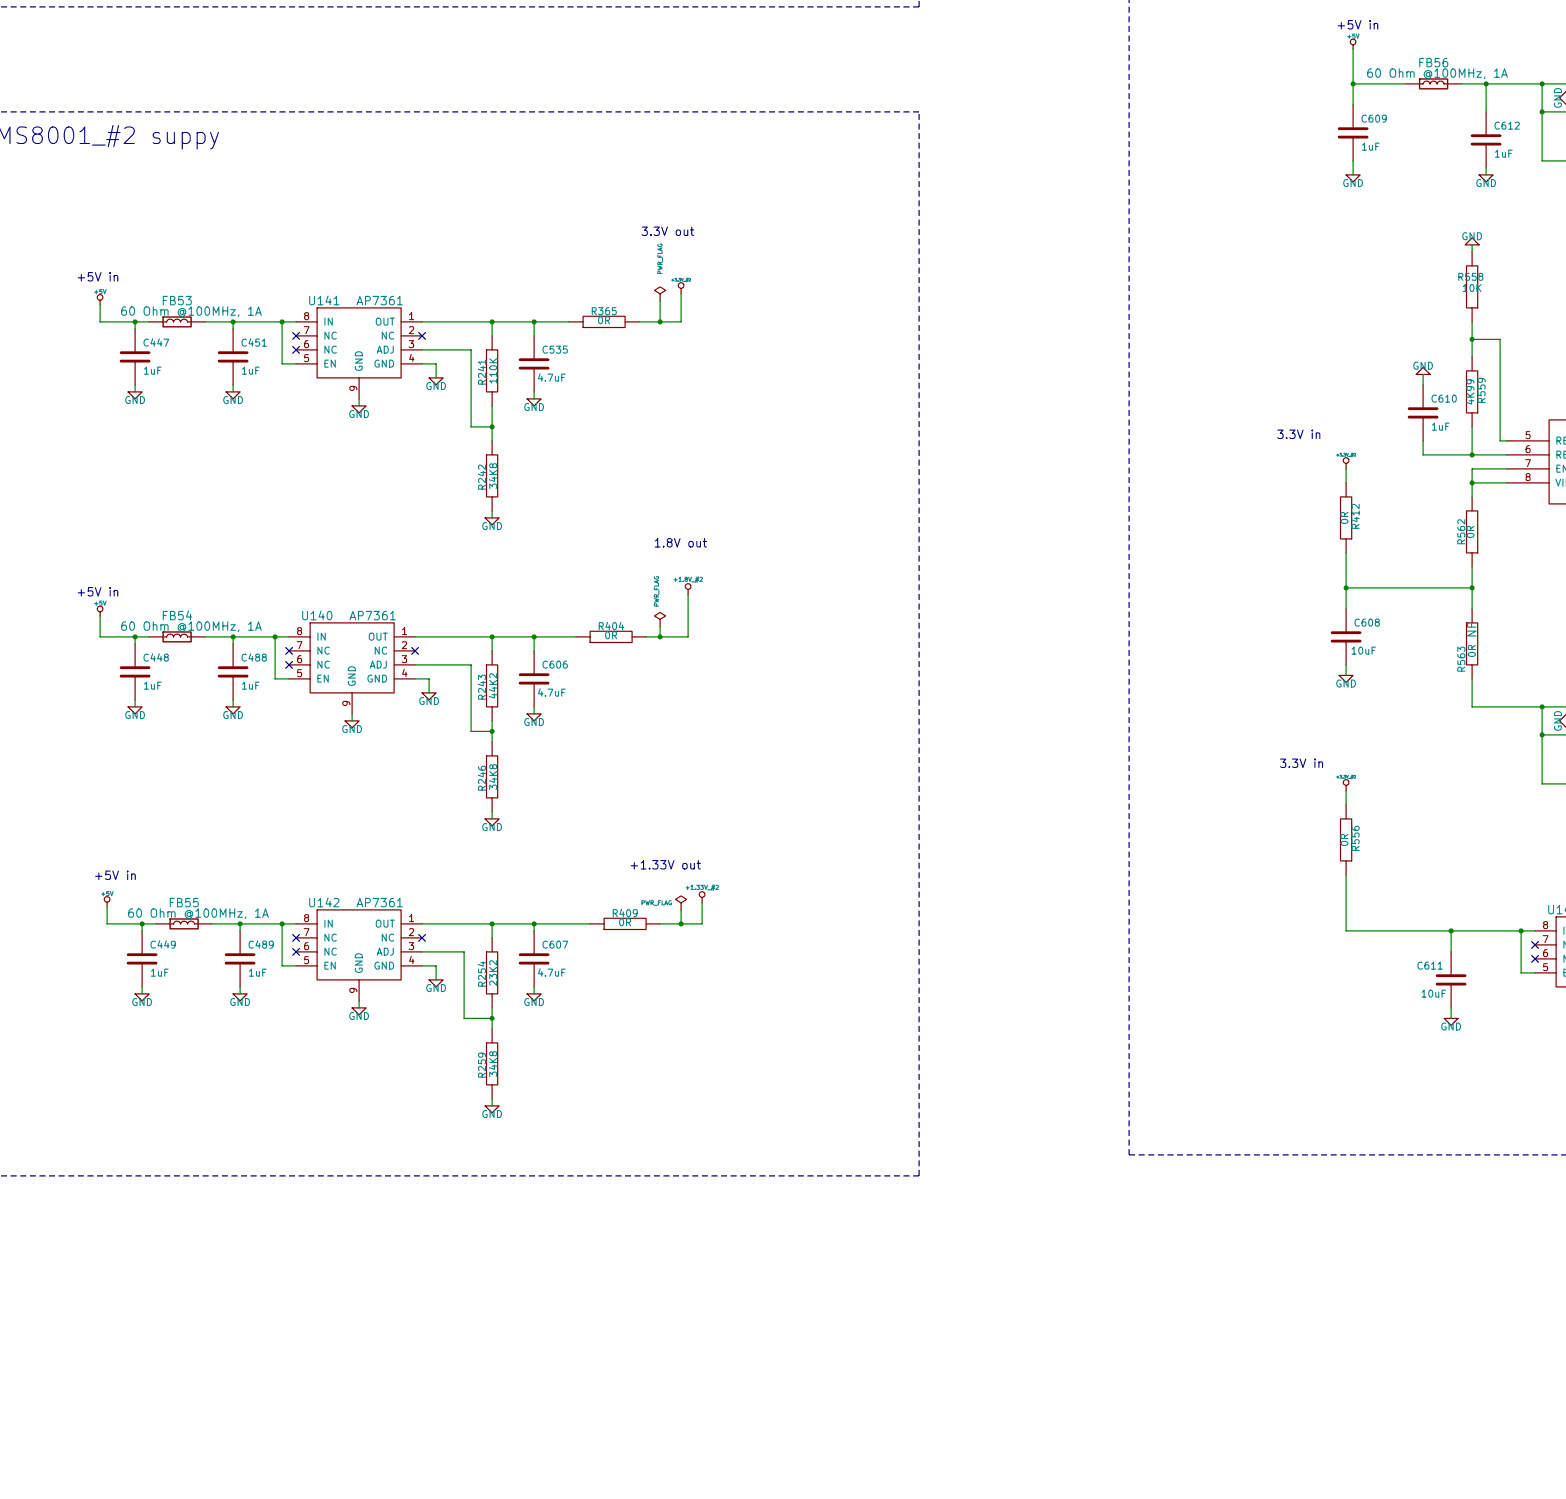
[picture p68: schematic PowerSupply.sch, part in row 2, column 2]

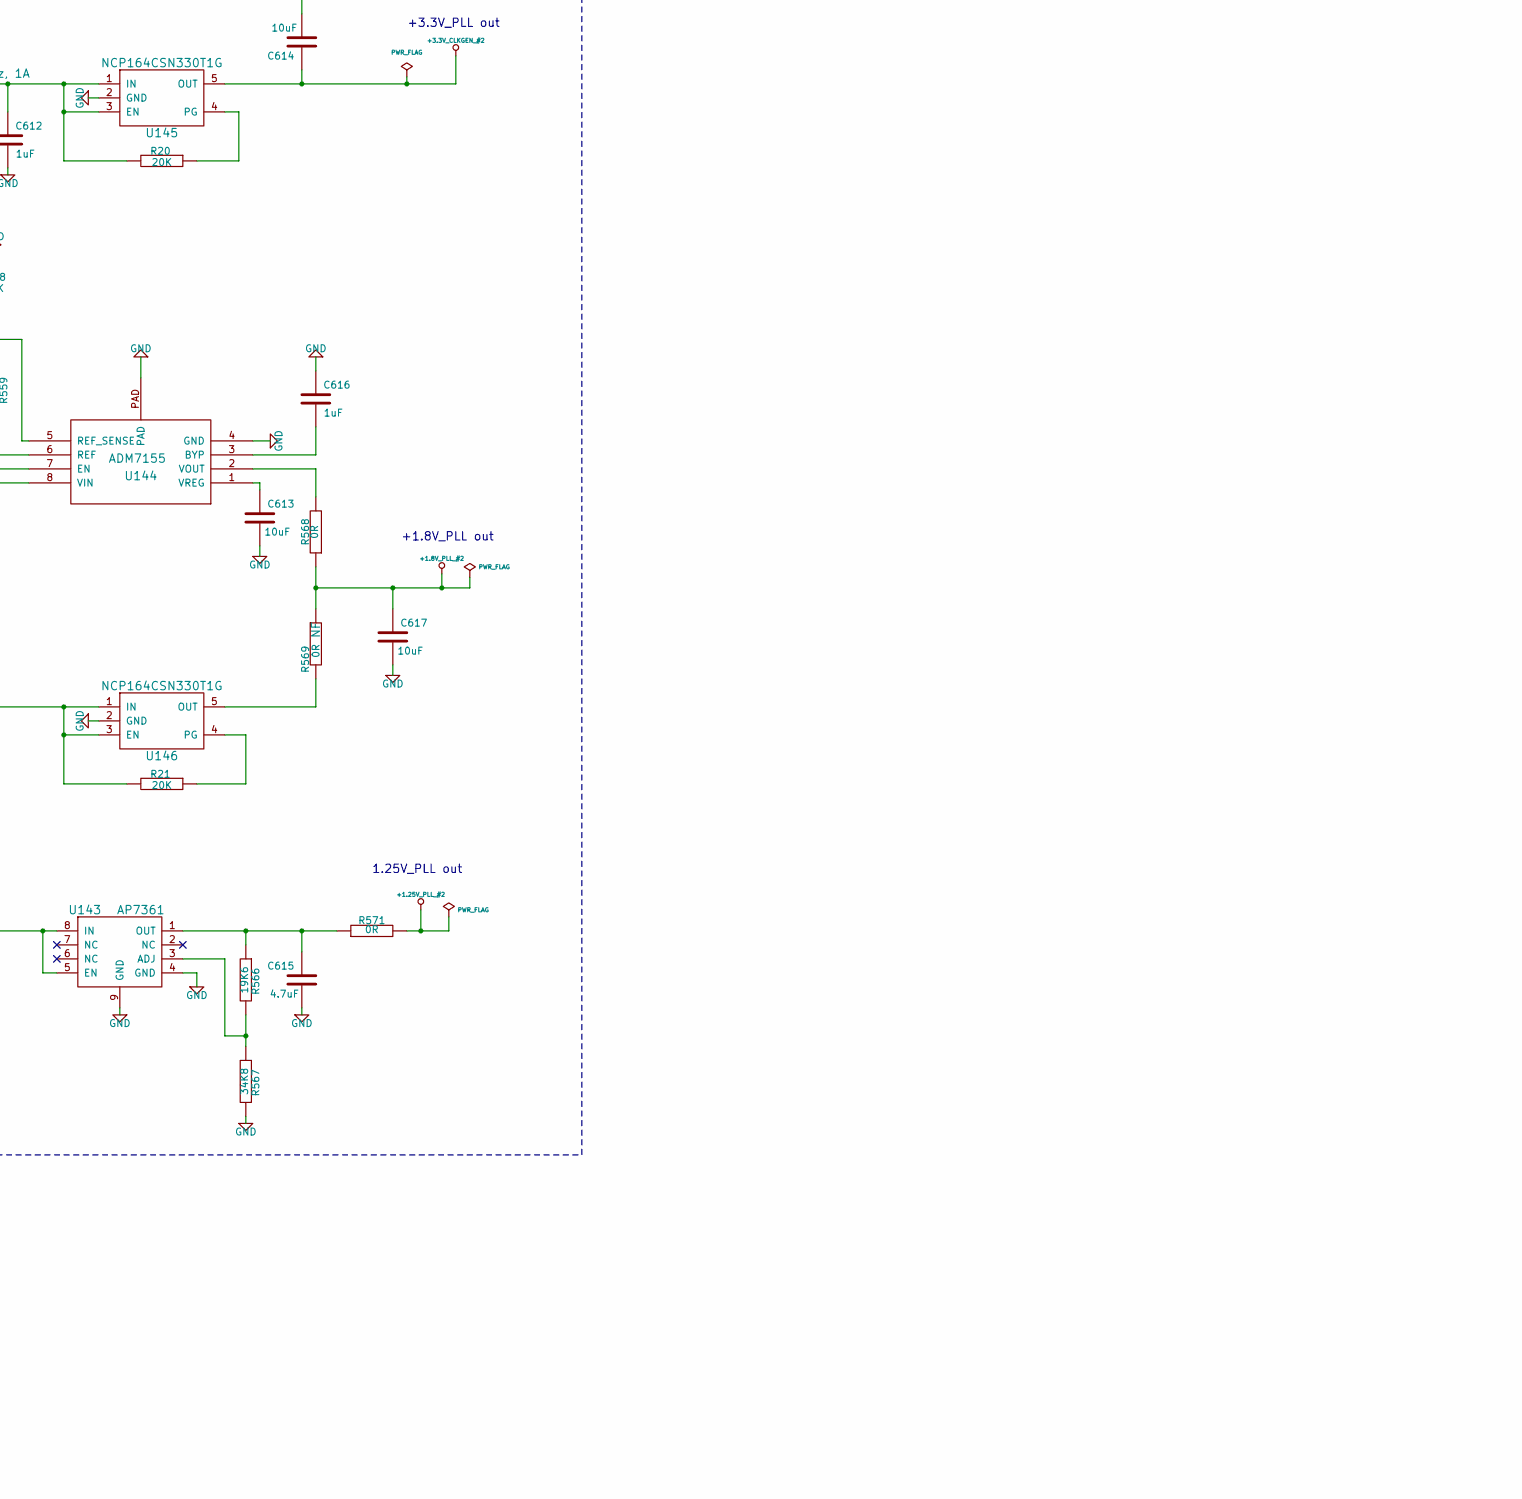
[picture p69: schematic PowerSupply.sch, part in row 2, column 3]

Parts:
C33, C66, C77, C81, C86, C608, C611, C613, C614, C617: 10UF_0603; SMD0603; Manufacturer Part Number CC0603MRX5R5BB106
C43, C44, C45, C51, C52, C53, C54, C55, C58, C63, C65, C185, C186, C187, C188, C238, C239, C412, C447, C448, C449, C451, C488, C489, C609, C612, C624, C625, C626, C627: 1UF_0402; SMD0402; Manufacturer Part Number CC0402ZRY5V5BB105
C57, C78, C206: 10UF_1206; SMD1206; Manufacturer Part Number CC1206ZKY5V7BB106
C59, C82, C610, C616: 1UF_0603; SMD0603; Manufacturer Part Number GRM188R61E105KA12D
C60, C61, C62, C64, C240, C394, C395, C413, C414, C535, C606, C607, C615, C628, C629: 4.7UF_0402; SMD0402; Manufacturer Part Number GRM155R60J475ME87D
C71, C87: 100nF_0402_GRM155R71C104KA88J; SMD0402; Manufacturer Part Number GRM155R71C104KA88J
C88, C293, C317, C319: 10uF_0603_GRM188R61E106KA73J; SMD0603; Manufacturer Part Number GRM188R61E106KA73J
C90: 1uF_0402_CC0402ZRY5V5BB105; SMD0402; Manufacturer Part Number CC0402ZRY5V5BB105
C291: 2.2nF_0402_GRM155R71E222KA01D; SMD0402; Manufacturer Part Number GRM155R71E222KA01D
C318: 47uF_2220_CGA9N3X7R1E476M230KB; SMD2220; Manufacturer Part Number GRM155R61H474KE11D
FB16: FB_600R_0805_MPZ2012S601AT000; SMD0805; Manufacturer Part Number MPZ2012S601AT000
FB17, FB18, FB19, FB20, FB21, FB23, FB24, FB30, FB46, FB53, FB54, FB55, FB56, FB57, FB58: FB_60R_0805; SMD0805; Manufacturer Part Number MMZ2012Y600B
J2, J24, J27: PIN_HEADER_1X3; pin_header_1x3; Manufacturer Part Number 68000-103HLF
J12, J25: Jumper_SNM-100-BK-T; SNM-100-BK-T; Manufacturer Part Number SNM-100-BK-T
J44: 1744037-2; Manufacturer Part Number A112698-ND
J45: 0353180620; Manufacturer Part Number 0353180620
JP1, JP2: PINHEADER_2X3; Manufacturer Part Number 0015912060
L39: SPM6530T-2R2M; Manufacturer Part Number SPM6530T-2R2M
LD1, LD4, LD5: LED; LED_0603; Manufacturer Part Number LG Q971-KN-1
R14, R15, R20, R21: 20K_0402_CRCW040220K0FKEDC; SMD0402; Manufacturer Part Number CRCW040220K0FKEDC
R27, R31, R56, R72, R101, R241: 110K_0402; SMD0402; Manufacturer Part Number RC0402JR-07110KL
R28, R30, R32, R34, R36, R44, R242, R246, R259, R291, R344, R346, R410, R567: 34K8_0402; SMD0402; Manufacturer Part Number RC0402FR-0734K8L
R29, R566: 19K6_0402; SMD0402; Manufacturer Part Number RC0402FR-0719K6L
R33, R254: 23K2_0402; SMD0402; Manufacturer Part Number RC0402FR-0723K2L
R35, R43, R243, R292, R345: 44K2_0402; SMD0402; Manufacturer Part Number RC0402FR-0744K2L
R37, R39, R46, R47, R50, R52, R53, R54, R103, R347, R348, R365, R404, R409, R411, R534, R562, R568, R571: 0R_0402; SMD0402; Manufacturer Part Number RC0402JR-070RL
R38, R40, R563, R569: 0R_0402_NF; SMD0402; Manufacturer Part Number RC0402JR-070RL
R41, R558: 10K_0402; SMD0402; Manufacturer Part Number RMCF0402FT10K0
R45, R559: 4K99_0402; SMD0402; Manufacturer Part Number RC0402FR-074K99L
R51, R55, R83: 680R_0402; SMD0402; Manufacturer Part Number RC0402FR-07680RL
R102: 40K_0402_ERJ-U02F4022X; SMD0402; Manufacturer Part Number ERJ-U02F4022X
R154: 976K_0805_ERJ-6ENF9763V; SMD0805; Manufacturer Part Number ERJ-6ENF9763V
R156: NF_619K_0805_ERJ-6ENF6193V; SMD0805; Manufacturer Part Number ERJ-6ENF6193V
R157, R158, R162: 100k_0805; SMD0805; Manufacturer Part Number ERJ-6ENF1003V
R159: NF_0R_0805_RC0805FR-130RL; SMD0805; Manufacturer Part Number RC0805FR-130RL
R412, R425, R428, R556: 0R_0402; SMD0402
U5, U6, U7, U8, U26, U44, U89, U94, U95, U109, U140, U141, U142, U143, U147: AP7361; U-DFN3030-8; Manufacturer Part Number AP7361-FGE-7
U9, U16, U145, U146: NCP164CSN330T1G; Manufacturer Part Number NCP164CSN330T1G
U10, U144: ADM7155; Manufacturer Part Number ADM7155ACPZ-02-R7
U14, U15, U29: NCP349; 6-DFN; Manufacturer Part Number NCP349MNAETBG
U85: TPS62136RGXT; Manufacturer Part Number TPS62136RGXR
U86: NCP59301DS50R4G; Manufacturer Part Number NCP59301DS50R4G

Connections:
+1.8V: R534.2
+1.8V_#1: R53.2
+1.8V_#2: R404.2
+1.8V_PLL_#1: C86.1, R39.1, R40.1
+1.8V_PLL_#2: C617.1, R568.1, R569.1
+1.8V_SC1905_#1: R47.2
+1.8V_SC1905_#2: R348.2
+1.25V_PLL_#1: R50.2
+1.25V_PLL_#2: R571.2
+1.33V_#1: R52.2
+1.33V_#2: R409.2
+3.3V_#1: R54.2, R425.2, R428.2
+3.3V_#2: R365.2, R412.2, R556.2
+3.3V_CLKGEN_#1: C66.1, U16.5 (OUT)
+3.3V_CLKGEN_#2: C614.1, U145.5 (OUT)
+3.3V_SC1905_#1: R46.2
+3.3V_SC1905_#2: R347.2
+3V_RF: R103.2
+5V: C43.1, C44.1, C51.1, C52.1, C53.1, C63.1, C185.1, C186.1, C447.1, C448.1, C449.1, C609.1, C624.1, C625.1, FB17.1, FB18.1, FB19.1, FB20.1, FB21.1, FB23.1, FB24.1, FB46.1, FB53.1, FB54.1, FB55.1, FB56.1, FB57.1, FB58.1, JP2.1, R55.1, U14.4 (OUT), U14.5 (OUT)
+5V_DCDC: C318.1, JP1.1, R159.1, R162.2, U86.4 (VOUT)
+5V_PWR: C57.1, JP1.2, JP1.4, JP1.6, U14.1 (IN)
+5V_RF: C238.1, FB30.1, R83.1, U29.4 (OUT), U29.5 (OUT)
+5V_USB: C87.1, C88.1, C90.1, JP1.3, JP2.3, R51.1, U15.4 (OUT), U15.5 (OUT)
+12V: C293.2, J27.2, J44.1, J45.1, J45.2, J45.3, U85.1 (VIN), U85.8 (EN)
GND: C33.2, C43.2, C44.2, C45.2, C51.2, C52.2, C53.2, C54.2, C55.2, C57.2, C58.2, C59.1, C60.2, C61.2, C62.2, C63.2, C64.2, C65.2, C66.2, C71.2, C77.2, C78.2, C81.2, C82.1, C86.2, C87.2, C88.2, C90.2, C185.2, C186.2, C187.2, C188.2, C206.2, C238.2, C239.2, C240.2, C291.2, C293.1, C317.1, C318.2, C319.1, C394.2, C395.2, C412.2, C413.2, C414.2, C447.2, C448.2, C449.2, C451.2, C488.2, C489.2, C535.2, C606.2, C607.2, C608.2, C609.2, C610.1, C611.2, C612.2, C613.2, C614.2, C615.2, C616.1, C617.2, C624.2, C625.2, C626.2, C627.2, C628.2, C629.2, J2.1, J2.3, J24.1, J24.3, J27.1, J27.3, J44.2, J45.4, J45.5, J45.6, LD1.2 (K), LD4.2 (K), LD5.2 (K), R28.2, R30.2, R32.2, R34.2, R36.2, R41.2, R44.2, R102.1, R157.1, R242.2, R246.2, R259.2, R291.2, R344.2, R346.2, R410.2, R558.2, R567.2, U5.4 (GND), U5.9 (GND), U6.4 (GND), U6.9 (GND), U7.4 (GND), U7.9 (GND), U8.4 (GND), U8.9 (GND), U9.2 (GND), U10.4 (GND), U10.PAD, U14.2 (GND), U14.6 (ENn), U15.2 (GND), U15.6 (ENn), U16.2 (GND), U26.4 (GND), U26.9 (GND), U29.2 (GND), U29.6 (ENn), U44.4 (GND), U44.9 (GND), U85.3 (GND), U85.4 (FB2), U85.10 (MODE), U85.11 (VSEL), U86.3 (GND), U89.4 (GND), U89.9 (GND), U94.4 (GND), U94.9 (GND), U95.4 (GND), U95.9 (GND), U109.4 (GND), U109.9 (GND), U140.4 (GND), U140.9 (GND), U141.4 (GND), U141.9 (GND), U142.4 (GND), U142.9 (GND), U143.4 (GND), U143.9 (GND), U144.4 (GND), U144.PAD, U145.2 (GND), U146.2 (GND), U147.4 (GND), U147.9 (GND)
unnamed: C33.1, R37.1, R38.1, R425.1
unnamed: C45.1, FB24.2, U94.5 (EN), U94.8 (IN)
unnamed: C54.1, FB18.2, U5.5 (EN), U5.8 (IN)
unnamed: C55.1, FB19.2, U6.5 (EN), U6.8 (IN)
unnamed: C58.1, FB20.2, U7.5 (EN), U7.8 (IN)
unnamed: C59.2, R45.1, U10.6 (REF)
unnamed: C60.1, R29.1, R50.1, U8.1 (OUT)
unnamed: C61.1, R31.1, R54.1, U7.1 (OUT)
unnamed: C62.1, R33.1, R52.1, U5.1 (OUT)
unnamed: C64.1, R35.1, R53.1, U6.1 (OUT)
unnamed: C65.1, FB21.2, R14.2, U16.1 (IN), U16.3 (EN)
unnamed: C77.1, R428.1, U8.5 (EN), U8.8 (IN)
unnamed: C78.1, FB16.2, U15.1 (IN)
unnamed: C81.1, U10.1 (VREG)
unnamed: C82.2, U10.3 (BYP)
unnamed: C187.1, FB17.2, U26.5 (EN), U26.8 (IN)
unnamed: C188.1, FB23.2, U89.5 (EN), U89.8 (IN)
unnamed: C206.1, JP2.2, JP2.4, JP2.6, U29.1 (IN)
unnamed: C239.1, FB30.2, U44.5 (EN), U44.8 (IN)
unnamed: C240.1, R101.1, R103.1, U44.1 (OUT)
unnamed: C291.1, U85.9 (SS/TR)
unnamed: C317.2, C319.2, L39.1, R154.2, R156.2, R158.2, R159.2, U85.6 (VOS), U86.1 (EN), U86.2 (VIN)
unnamed: C394.1, R72.1, R347.1, U89.1 (OUT)
unnamed: C395.1, R345.1, R348.1, U26.1 (OUT)
unnamed: C412.1, FB46.2, U95.5 (EN), U95.8 (IN)
unnamed: C413.1, R27.1, R46.1, U95.1 (OUT)
unnamed: C414.1, R43.1, R47.1, U94.1 (OUT)
unnamed: C451.1, FB53.2, U141.5 (EN), U141.8 (IN)
unnamed: C488.1, FB54.2, U140.5 (EN), U140.8 (IN)
unnamed: C489.1, FB55.2, U142.5 (EN), U142.8 (IN)
unnamed: C535.1, R241.1, R365.1, U141.1 (OUT)
unnamed: C606.1, R243.1, R404.1, U140.1 (OUT)
unnamed: C607.1, R254.1, R409.1, U142.1 (OUT)
unnamed: C608.1, R412.1, R562.1, R563.1
unnamed: C610.2, R559.1, U144.6 (REF)
unnamed: C611.1, R556.1, U143.5 (EN), U143.8 (IN)
unnamed: C612.1, FB56.2, R20.2, U145.1 (IN), U145.3 (EN)
unnamed: C613.1, U144.1 (VREG)
unnamed: C615.1, R566.1, R571.1, U143.1 (OUT)
unnamed: C616.2, U144.3 (BYP)
unnamed: C626.1, FB57.2, U147.5 (EN), U147.8 (IN)
unnamed: C627.1, FB58.2, U109.5 (EN), U109.8 (IN)
unnamed: C628.1, R56.1, R411.1, U147.1 (OUT)
unnamed: C629.1, R292.1, R534.1, U109.1 (OUT)
unnamed: J2.2, JP1.5
unnamed: J24.2, JP2.5
unnamed: L39.2, U85.2 (SW)
unnamed: LD1.1 (A), R51.2
unnamed: LD4.1 (A), R83.2
unnamed: LD5.1 (A), R55.2
unnamed: R14.1, U16.4 (PG)
unnamed: R15.1, U9.4 (PG)
unnamed: R15.2, R38.2, U9.1 (IN), U9.3 (EN)
unnamed: R20.1, U145.4 (PG)
unnamed: R21.1, U146.4 (PG)
unnamed: R21.2, R563.2, U146.1 (IN), U146.3 (EN)
unnamed: R27.2, R28.1, U95.3 (ADJ)
unnamed: R29.2, R30.1, U8.3 (ADJ)
unnamed: R31.2, R32.1, U7.3 (ADJ)
unnamed: R33.2, R34.1, U5.3 (ADJ)
unnamed: R35.2, R36.1, U6.3 (ADJ)
unnamed: R37.2, U10.7 (EN), U10.8 (VIN)
unnamed: R39.2, U10.2 (VOUT)
unnamed: R40.2, U9.5 (OUT)
unnamed: R41.1, R45.2, U10.5 (REF_SENSE)
unnamed: R43.2, R44.1, U94.3 (ADJ)
unnamed: R101.2, R102.2, U44.3 (ADJ)
unnamed: R154.1, R156.1, R157.2, U85.5 (FB)
unnamed: R158.1, U85.7 (PG)
unnamed: R162.1, U86.5 (FLG)
unnamed: R241.2, R242.1, U141.3 (ADJ)
unnamed: R243.2, R246.1, U140.3 (ADJ)
unnamed: R254.2, R259.1, U142.3 (ADJ)
unnamed: R56.2, R291.1, U147.3 (ADJ)
unnamed: R292.2, R410.1, U109.3 (ADJ)
unnamed: R72.2, R344.1, U89.3 (ADJ)
unnamed: R345.2, R346.1, U26.3 (ADJ)
unnamed: R558.1, R559.2, U144.5 (REF_SENSE)
unnamed: R562.2, U144.7 (EN), U144.8 (VIN)
unnamed: R566.2, R567.1, U143.3 (ADJ)
unnamed: R568.2, U144.2 (VOUT)
unnamed: R569.2, U146.5 (OUT)
VBUS_USB: C71.1, FB16.1
VDIO: R411.2

Notes on the sheet:
EXTERNAL POWER +5V
POWER SOURCE SELECTION
+1.8V_PLL out
3.3V out
+5V out
+1.33V out
+3.3V_PLL out
1.8V out
3.3V in
1.25V_PLL out
3.3V VDIO
+5V in
Protection
For DRC pass
+5V out for RF
3V out
EXTERNAL POWER +12V
If linear voltage regulator is fitted then 976K is used for DC-DC convertor
12V from PCIe board
+5V_USB out
7.5V or 5V
RF supply
PLL Supply
USB
3.3V out for SC1905
1.8V out for SC1905
SC1905_#2 Chips Supply
SC1905_#1 Chips Supply
LMS8001_#1 suppy
LMS8001_#2 suppy
