myriadrf/LimeRFE-8001P/hardware/1v0/KiCAD/RP2040_MCU.sch

## KiCad design hardware/1v0/KiCAD/RP2040_MCU.sch (2023-10-04)

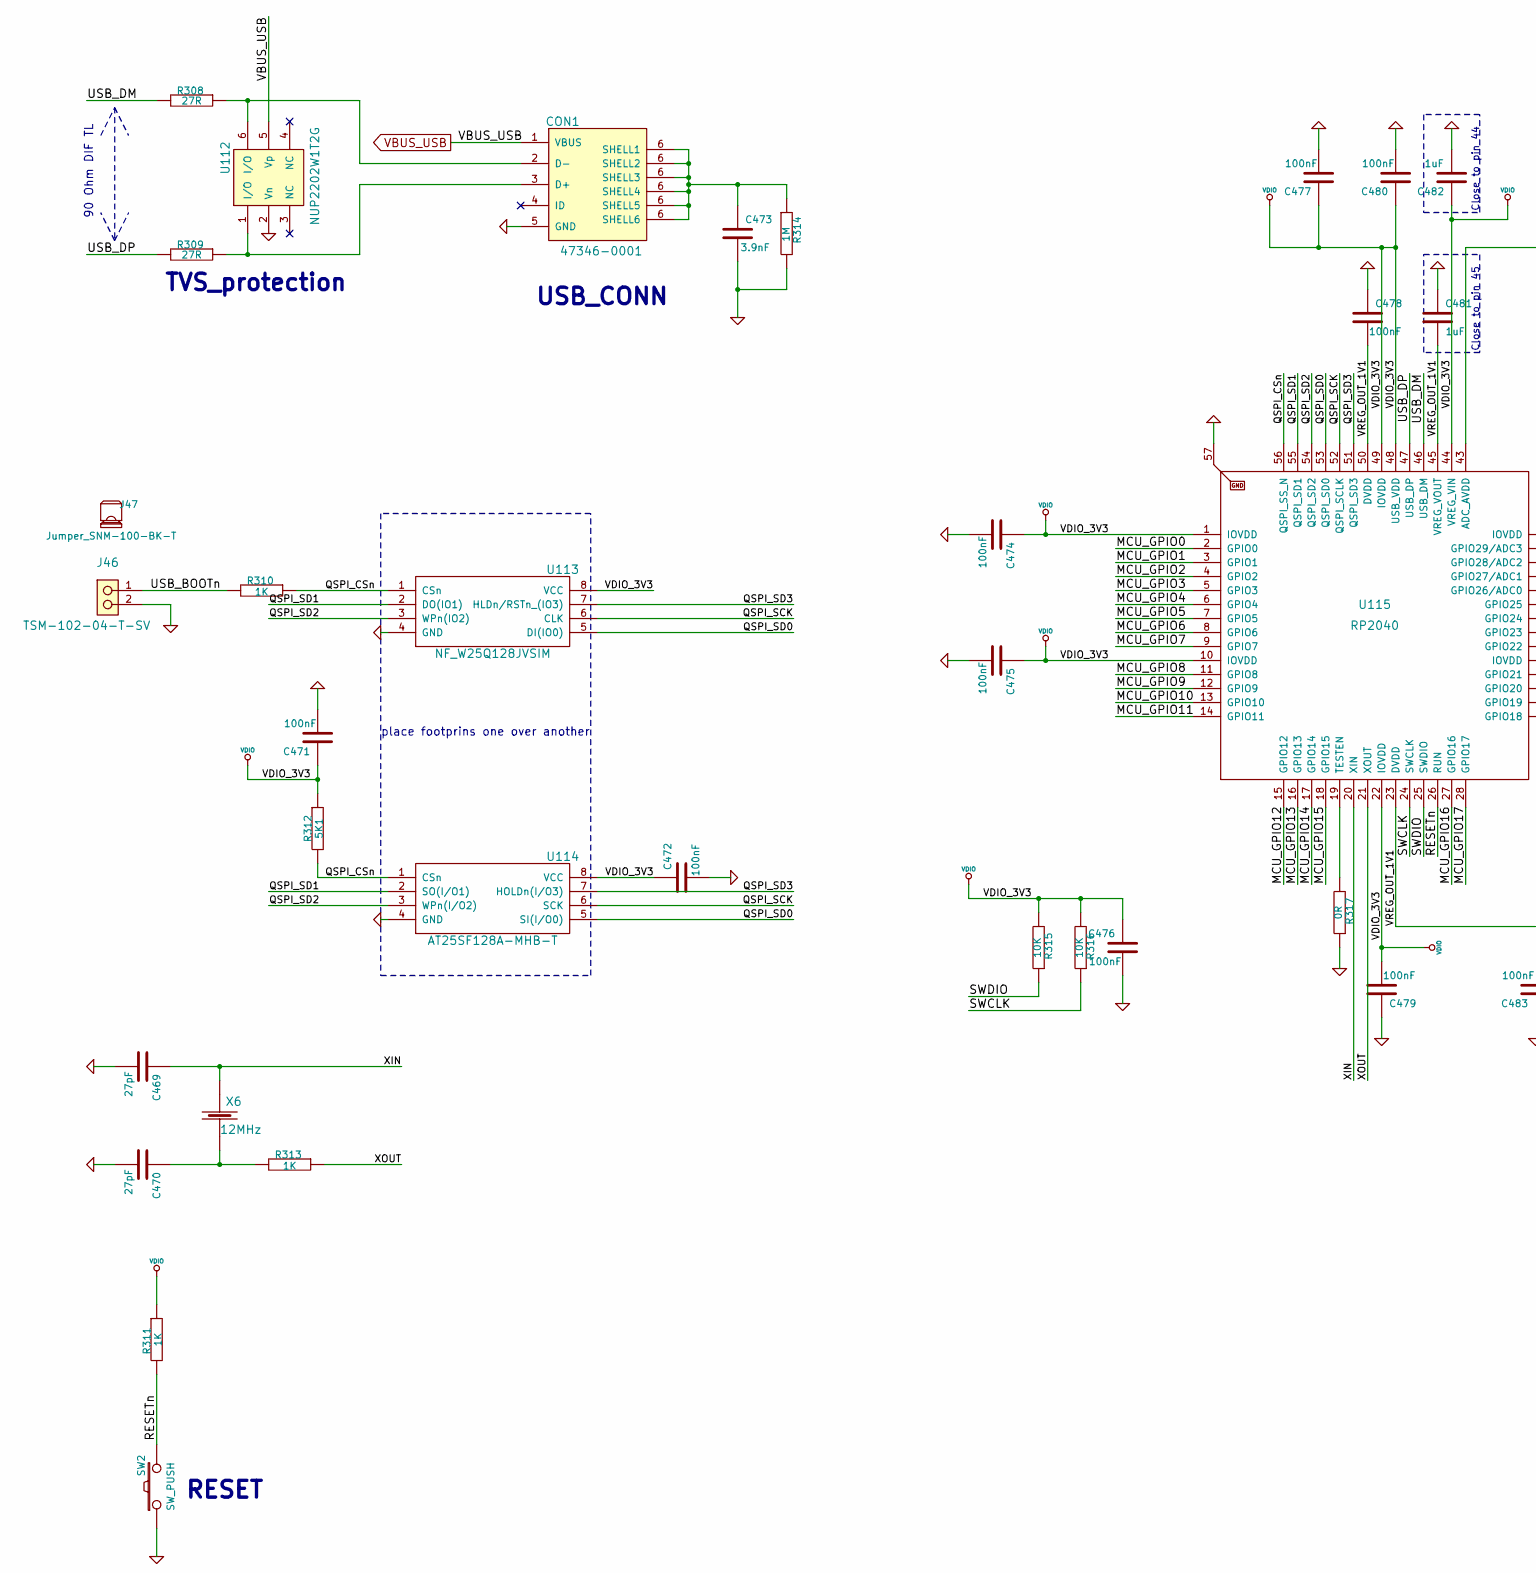
[picture p76: schematic RP2040_MCU.sch, part in row 1, column 1]

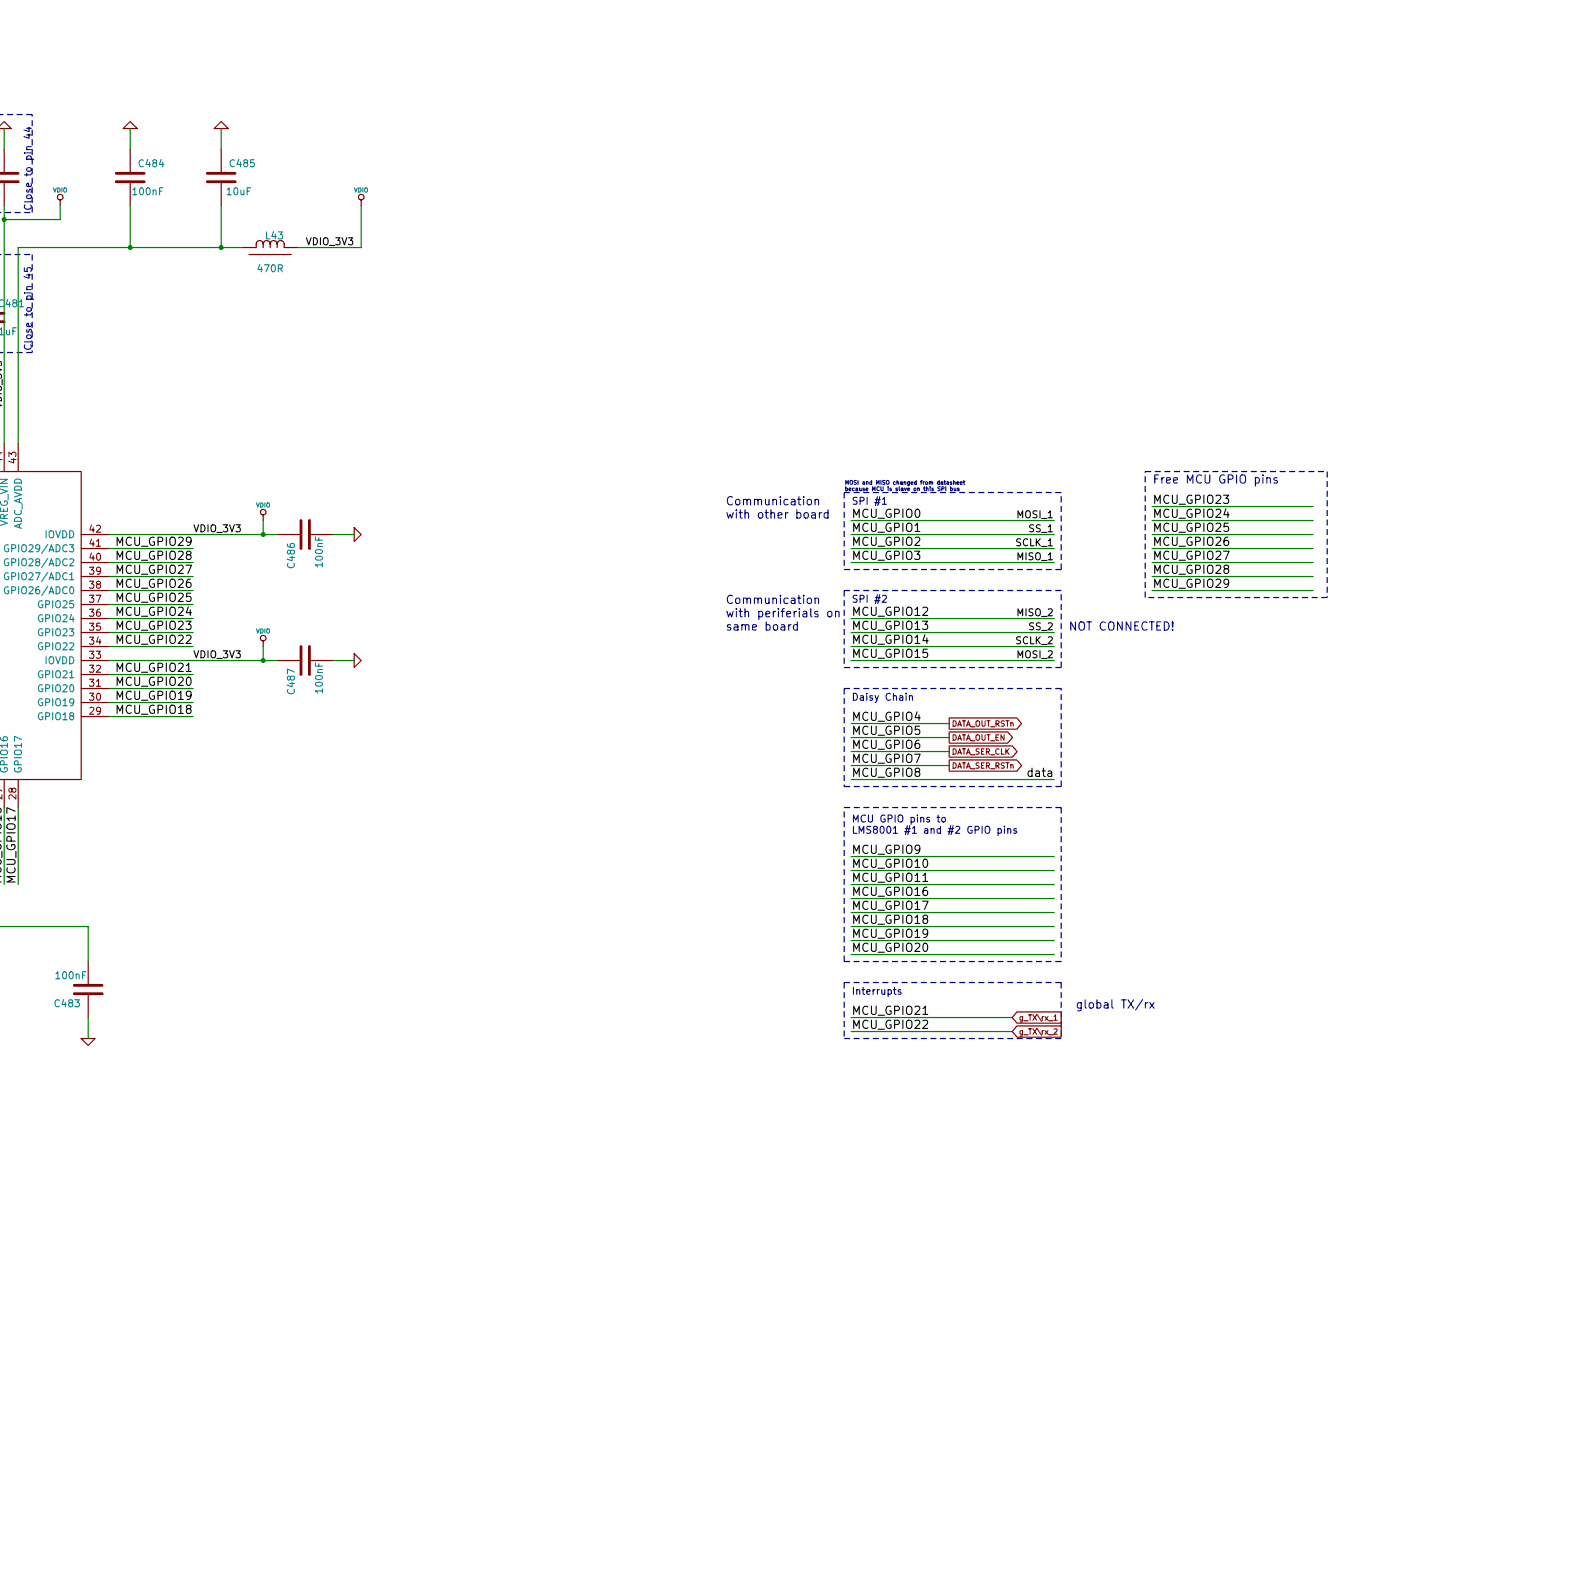
[picture p77: schematic RP2040_MCU.sch, part in row 1, column 2]

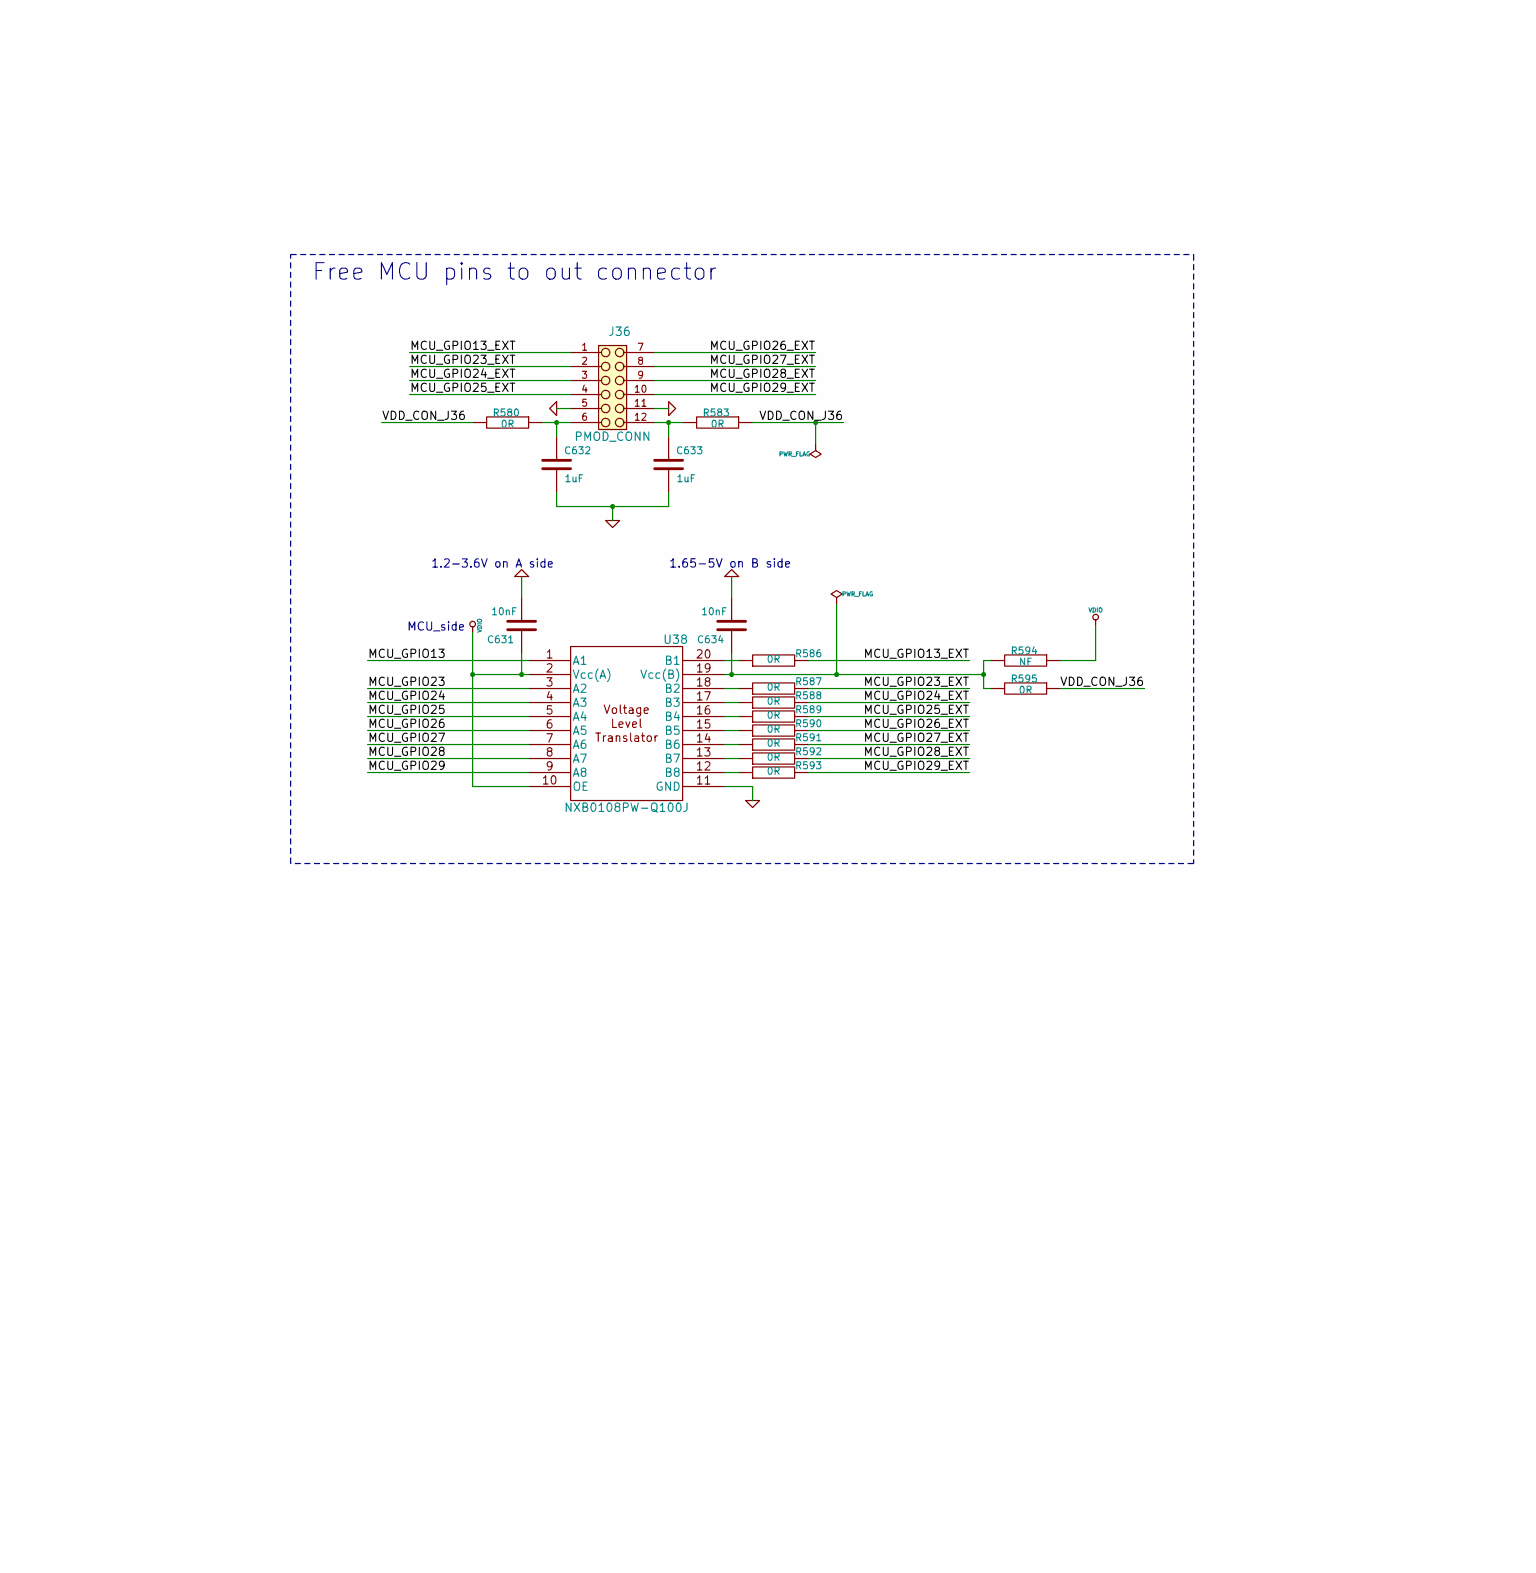
[picture p78: schematic RP2040_MCU.sch, part in row 1, column 3]

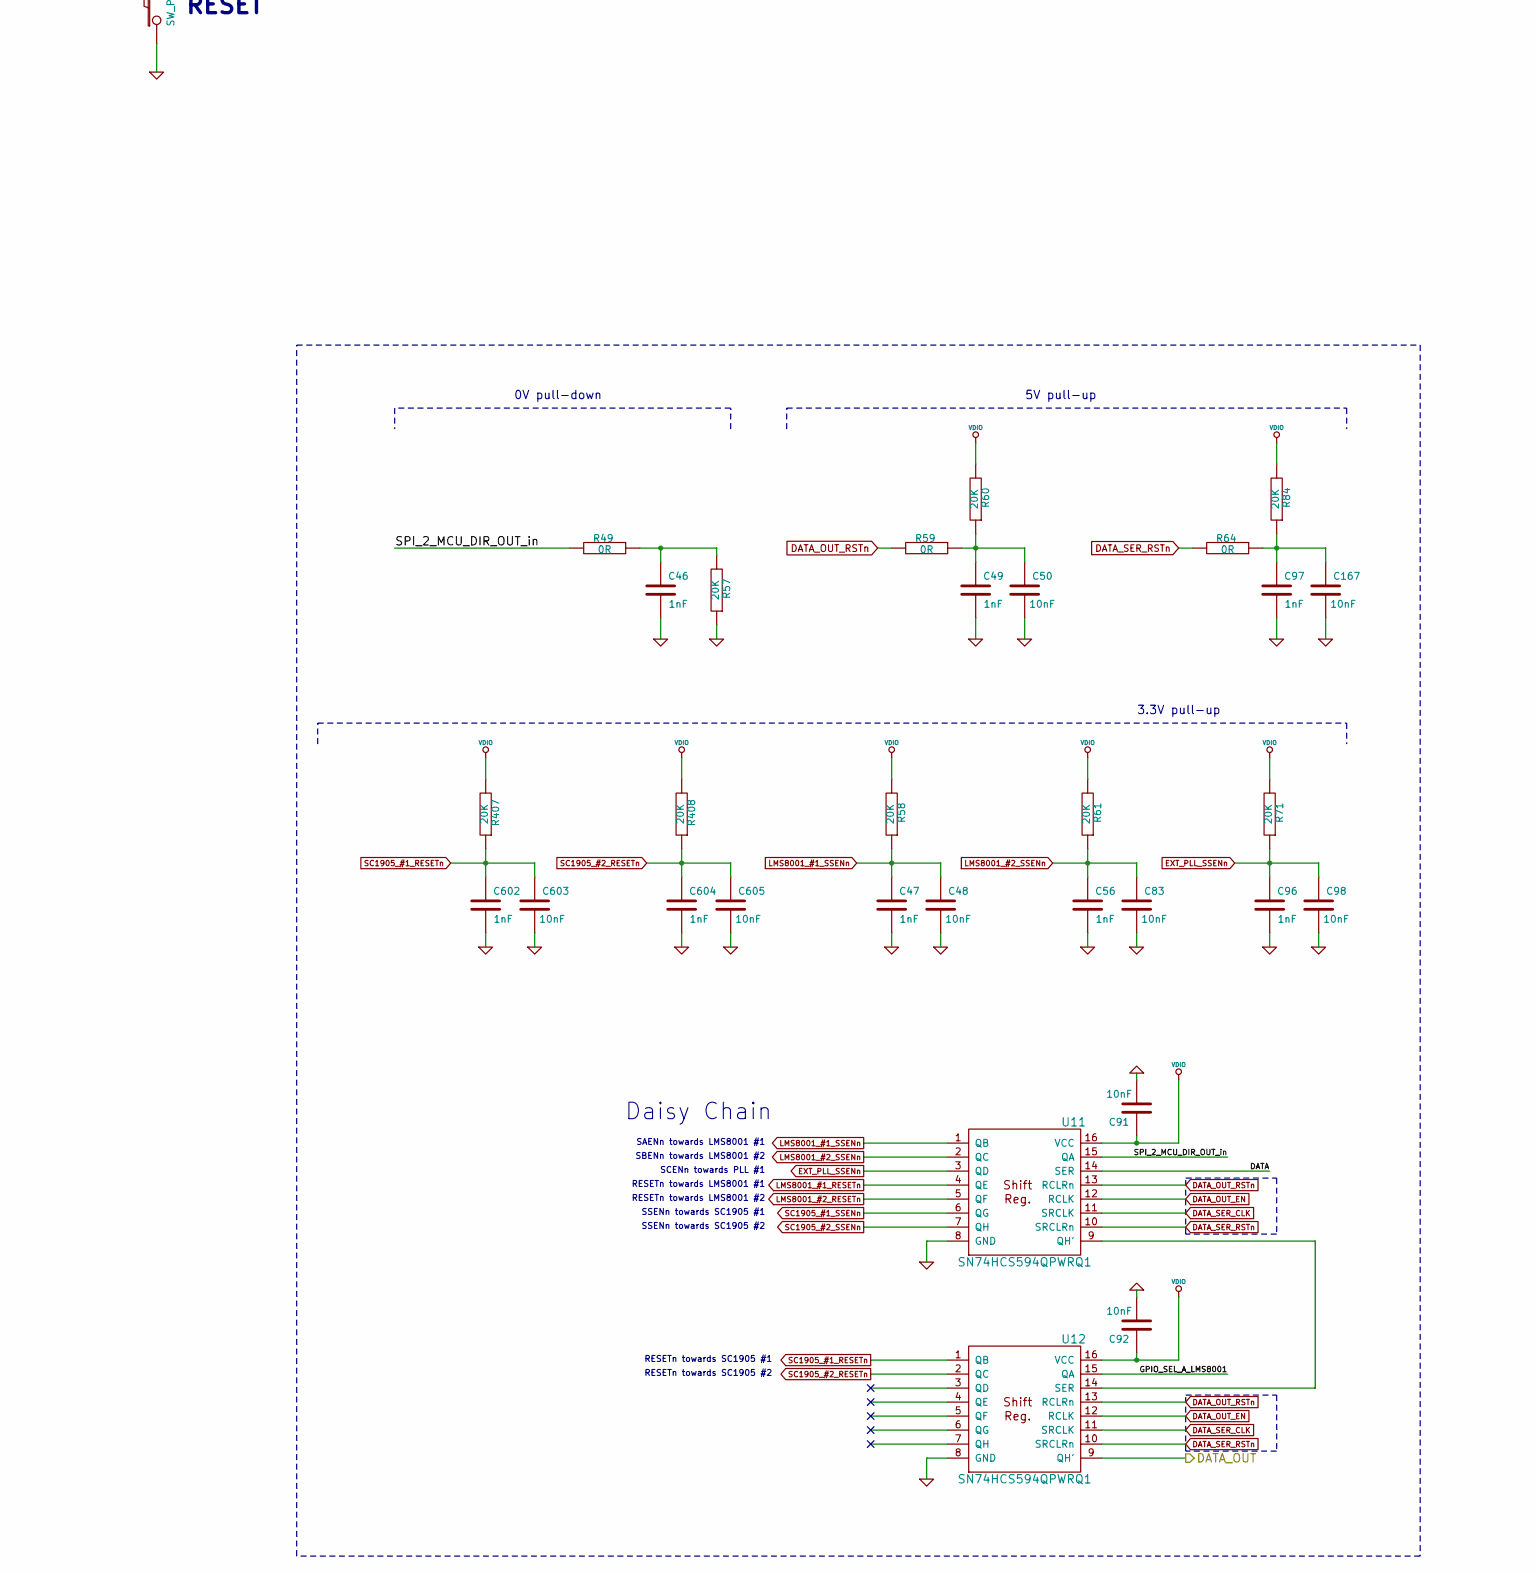
[picture p79: schematic RP2040_MCU.sch, part in row 2, column 1]

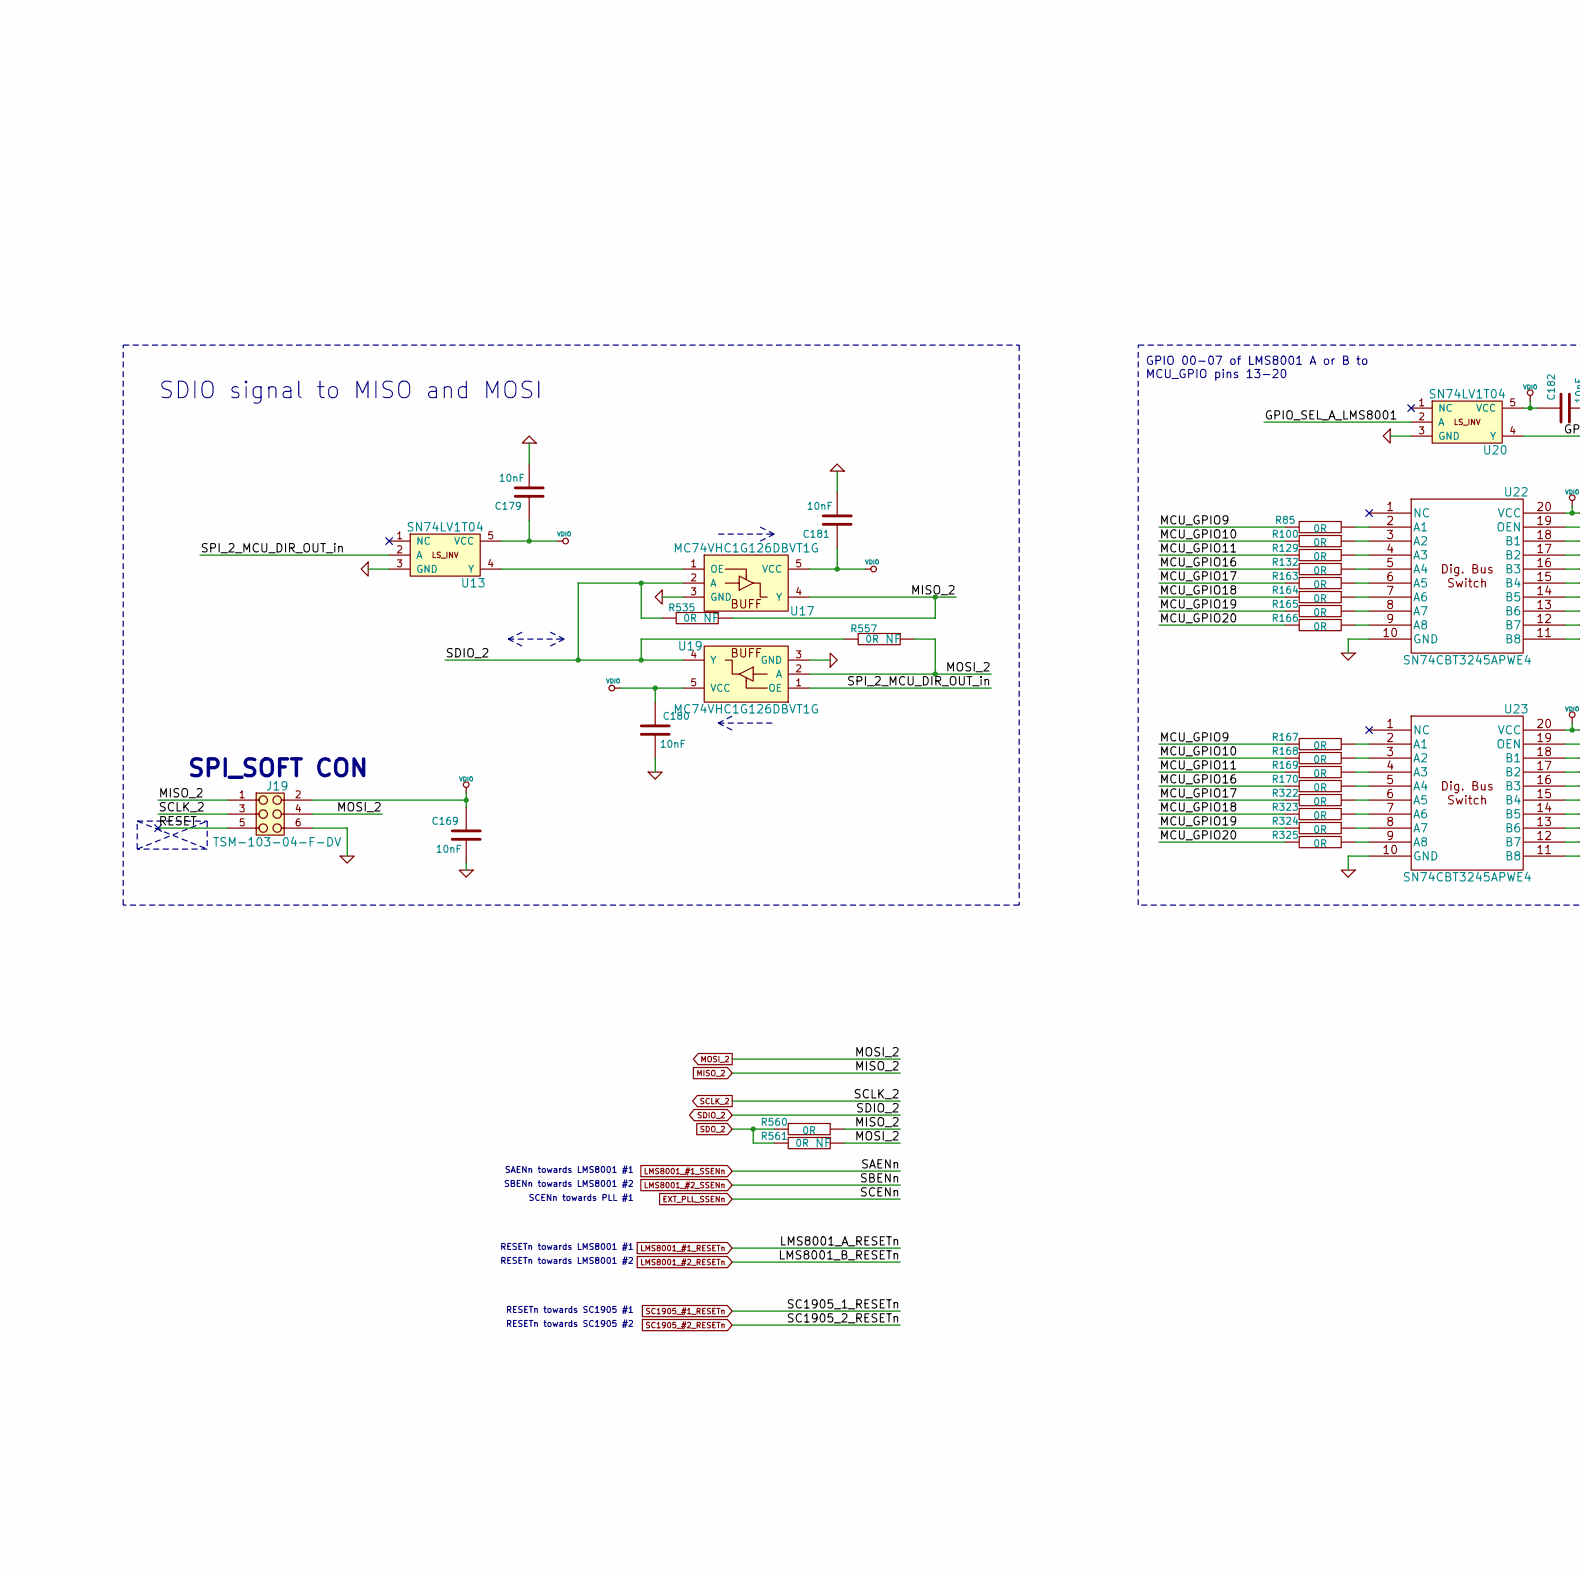
[picture p80: schematic RP2040_MCU.sch, part in row 2, column 2]

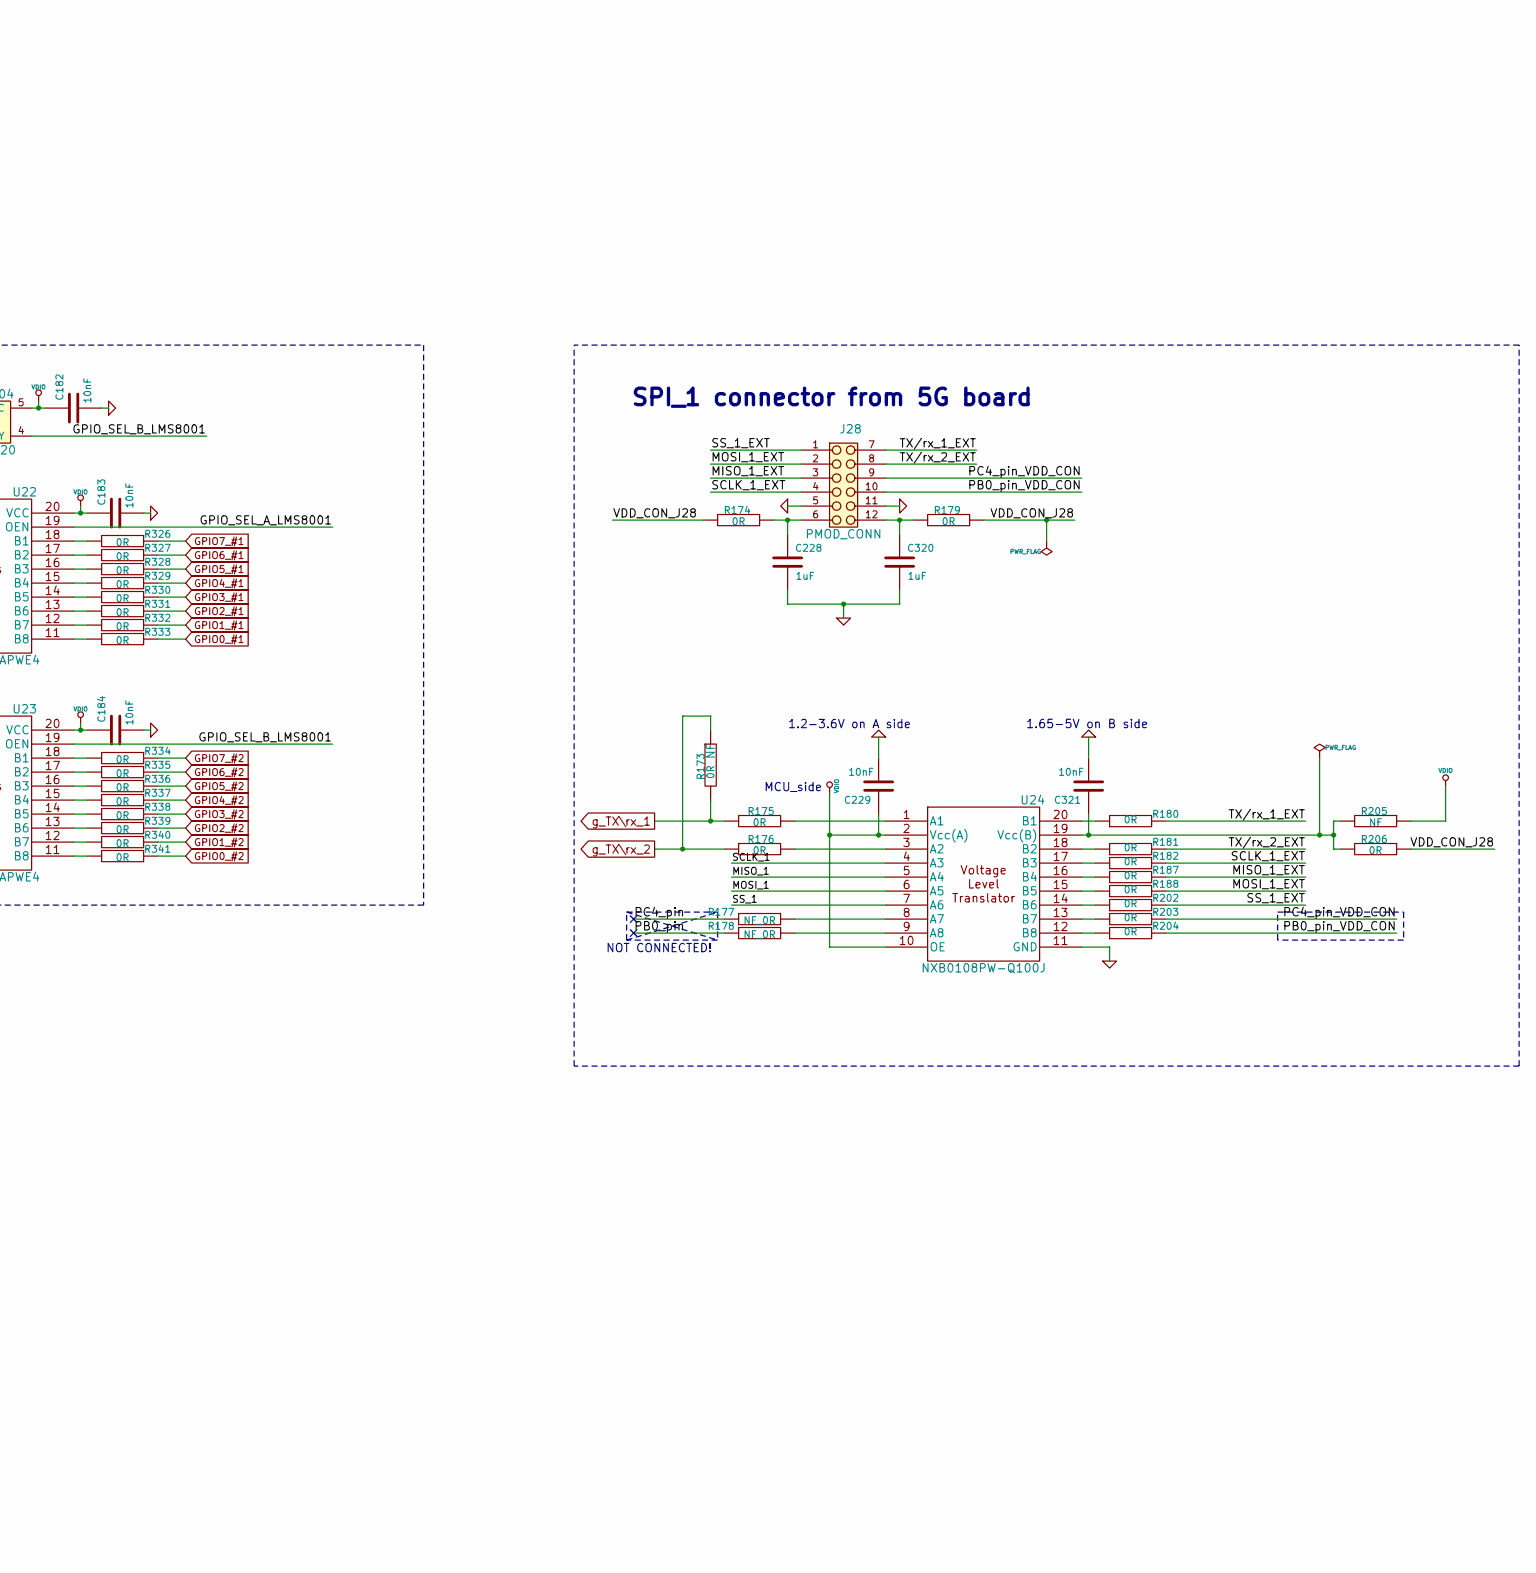
[picture p81: schematic RP2040_MCU.sch, part in row 2, column 3]

Parts:
C46, C47, C49, C56, C96, C97, C602, C604: 1nF_0402; SMD0402; Manufacturer Part Number CC0402KRX7R9BB102
C48, C50, C83, C91, C92, C98, C167, C169, C179, C180, C181, C182, C183, C184, C229, C321, C603, C605, C631, C634: 10nF_0402; SMD0402; Manufacturer Part Number CC0402ZRY5V7BB103
C228, C320, C632, C633: 1uF_0402; SMD0402; Manufacturer Part Number CC0402ZRY5V5BB105
C469, C470: 27pF_0402_GCM1555C1H270FA16D; SMD0402; Manufacturer Part Number GCM1555C1H270FA16D
C471, C472, C474, C475, C476, C477, C478, C479, C480, C483, C484, C486, C487: 100nF_0402_GRM155R71C104KA88J; SMD0402; Manufacturer Part Number GRM155R71C104KA88J
C473: 3.9nF_0402_04025C392JAT2A; SMD0402; Manufacturer Part Number 04025C392JAT2A
C481, C482: 1uF_0402_CC0402ZRY5V5BB105; SMD0402; Manufacturer Part Number CC0402ZRY5V5BB105
C485: 10uF_0603_GRM188R61E106KA73J; SMD0603; Manufacturer Part Number GRM188R61E106KA73J
CON1: 47346-0001; USB-MINI-B; Manufacturer Part Number 47346-0001
J19: TSM-103-04-F-DV; Manufacturer Part Number TSM-103-04-F-DV
J28, J36: PMOD_CONN; Manufacturer Part Number 95278-401-06LF
J46: TSM-102-04-T-SV; Manufacturer Part Number 200-TSM10204TSV
J47: Jumper_SNM-100-BK-T; SNM-100-BK-T; Manufacturer Part Number SNM-100-BK-T
L43: 470R_0603_BLM18PG471SN1D; SMD0603; Manufacturer Part Number BLM18PG471SN1D
R49, R59, R64, R206, R560, R580, R583, R595: 0R_0402; SMD0402
R57, R58, R60, R61, R71, R84, R407, R408: 20K_0402_CRCW040220K0FKEDC; SMD0402; Manufacturer Part Number CRCW040220K0FKEDC
R85, R100, R129, R132, R163, R164, R165, R166, R167, R168, R169, R170, R174, R175, R176, R179, R180, R181, R182, R187, R188, R202, R203, R204, R322, R323, R324, R325, R326, R327, R328, R329, R330, R331, R332, R333, R334, R335, R336, R337, R338, R339, R340, R341, R586, R587, R588, R589, R590, R591, R592, R593: 0R_0402; SMD0201
R173: 0R_0201_NF; SMD0201; Manufacturer Part Number MCR006YRTJ000
R177, R178: NF_0R_0402_RCS04020000Z0ED; SMD0201; Manufacturer Part Number RCS04020000Z0ED
R205, R594: 0RNF_0402; SMD0402
R308, R309: 27R_0402_ERJ2RKD27R0X; SMD0402; Manufacturer Part Number ERJ2RKD27R0X
R310, R311, R313: 1K_0402_CRGP0402F1K0; SMD0402; Manufacturer Part Number CRGP0402F1K0
R312: 5K1_0402; SMD0402; Manufacturer Part Number RC0402FR-075K1L
R314: 1M_0402_RC0402FR-071ML; SMD0402; Manufacturer Part Number RC0402FR-071ML
R315, R316: 10K_0402_Yageo; SMD0402; Manufacturer Part Number RC0402JR-7D10KL
R317: 0R_0402_RC0402JR-070RL; SMD0402; Manufacturer Part Number RC0402JR-070RL
R535, R557, R561: 0R_0402_NF; SMD0402; Manufacturer Part Number RC0402JR-070RL
SW2: SW_PUSH; B3U-1000P; Manufacturer Part Number B3U-1000P
U11, U12: SN74HCS594QPWRQ1; Manufacturer Part Number SN74HCS594QPWRQ1
U13, U20: SN74LV1T04; Manufacturer Part Number SN74LV1T04DCKRG4
U17, U19: MC74VHC1G126DBVT1G; Manufacturer Part Number ONSEMI
U22, U23: SN74CBT3245APWE4; Manufacturer Part Number SN74CBT3245APWE4
U24, U38: NXB0108PW-Q100J; Manufacturer Part Number NXB0108PW-Q100J
U112: NUP2202W1T2G; SC-88-6_NUP2202W1T2G; Manufacturer Part Number NUP2202W1T2G
U113: NF_W25Q128JVSIM; W25Q128JVSIM; Manufacturer Part Number W25Q128JVSIM
U114: AT25SF128A-MHB-T; Manufacturer Part Number AT25SF128A-MHB-T
U115: RP2040; RPI_Chip_RP2040_7_500; Manufacturer Part Number RPI Chip RP2040-7-500
X6: ABLS-12.000MHZ-B4-T; Manufacturer Part Number ABLS-12.000MHZ-B4-T

Connections:
DATA_OUT: U12.9 (QH')
DATA_OUT_EN: U11.12 (RCLK), U12.12 (RCLK), U115.7 (GPIO5)
DATA_OUT_RSTn: R59.2, U11.13 (RCLRn), U12.13 (RCLRn), U115.6 (GPIO4)
DATA_SER_CLK: U11.11 (SRCLK), U12.11 (SRCLK), U115.8 (GPIO6)
DATA_SER_RSTn: R64.2, U11.10 (SRCLRn), U12.10 (SRCLRn), U115.9 (GPIO7)
EXT_PLL_SSENn: C96.1, C98.1, R71.1, U11.3 (QD)
GND: C46.2, C47.2, C48.2, C49.2, C50.2, C56.2, C83.2, C91.2, C92.2, C96.2, C97.2, C98.2, C167.2, C169.2, C179.2, C180.2, C181.2, C182.2, C183.2, C184.2, C228.2, C229.2, C320.2, C321.2, C469.2, C470.2, C471.2, C472.2, C473.2, C474.2, C475.2, C476.2, C477.2, C478.1, C479.1, C480.2, C481.1, C482.2, C483.1, C484.1, C485.1, C486.2, C487.2, C602.2, C603.2, C604.2, C605.2, C631.2, C632.2, C633.2, C634.2, CON1.5 (GND), J19.6, J28.5, J28.11, J36.5, J36.11, J46.2, R57.1, R314.2, R317.1, SW2.1, U11.8 (GND), U12.8 (GND), U13.3 (GND), U17.3 (GND), U19.3 (GND), U20.3 (GND), U22.10 (GND), U23.10 (GND), U24.11 (GND), U38.11 (GND), U112.2 (Vn), U113.4 (GND), U114.4 (GND), U115.57
GPIO0_#1: R333.1
GPIO0_#2: R341.1
GPIO1_#1: R332.1
GPIO1_#2: R340.1
GPIO2_#1: R331.1
GPIO2_#2: R339.1
GPIO3_#1: R330.1
GPIO3_#2: R338.1
GPIO4_#1: R329.1
GPIO4_#2: R337.1
GPIO5_#1: R328.1
GPIO5_#2: R336.1
GPIO6_#1: R327.1
GPIO6_#2: R335.1
GPIO7_#1: R326.1
GPIO7_#2: R334.1
GPIO_SEL_A_LMS8001: U12.15 (QA), U20.2 (A), U22.19 (OEN)
GPIO_SEL_B_LMS8001: U20.4 (Y), U23.19 (OEN)
LMS8001_#1_RESETn: U11.4 (QE)
LMS8001_#1_SSENn: C47.1, C48.1, R58.1, U11.1 (QB)
LMS8001_#2_RESETn: U11.5 (QF)
LMS8001_#2_SSENn: C56.1, C83.1, R61.1, U11.2 (QC)
MCU_GPIO0: U24.6 (A5), U115.2 (GPIO0)
MCU_GPIO1: U24.7 (A6), U115.3 (GPIO1)
MCU_GPIO2: U24.4 (A3), U115.4 (GPIO2)
MCU_GPIO3: U24.5 (A4), U115.5 (GPIO3)
MCU_GPIO9: R85.2, R167.2, U115.12 (GPIO9)
MCU_GPIO10: R100.2, R168.2, U115.13 (GPIO10)
MCU_GPIO11: R129.2, R169.2, U115.14 (GPIO11)
MCU_GPIO13: U38.1 (A1), U115.16 (GPIO13)
MCU_GPIO13_EXT: J36.1, R586.2
MCU_GPIO16: R132.2, R170.2, U115.27 (GPIO16)
MCU_GPIO17: R163.2, R322.2, U115.28 (GPIO17)
MCU_GPIO18: R164.2, R323.2, U115.29 (GPIO18)
MCU_GPIO19: R165.2, R324.2, U115.30 (GPIO19)
MCU_GPIO20: R166.2, R325.2, U115.31 (GPIO20)
MCU_GPIO23: U38.3 (A2), U115.35 (GPIO23)
MCU_GPIO23_EXT: J36.2, R587.2
MCU_GPIO24: U38.4 (A3), U115.36 (GPIO24)
MCU_GPIO24_EXT: J36.3, R588.2
MCU_GPIO25: U38.5 (A4), U115.37 (GPIO25)
MCU_GPIO25_EXT: J36.4, R589.2
MCU_GPIO26: U38.6 (A5), U115.38 (GPIO26/ADC0)
MCU_GPIO26_EXT: J36.7, R590.2
MCU_GPIO27: U38.7 (A6), U115.39 (GPIO27/ADC1)
MCU_GPIO27_EXT: J36.8, R591.2
MCU_GPIO28: U38.8 (A7), U115.40 (GPIO28/ADC2)
MCU_GPIO28_EXT: J36.9, R592.2
MCU_GPIO29: U38.9 (A8), U115.41 (GPIO29/ADC3)
MCU_GPIO29_EXT: J36.10, R593.2
MISO_1_EXT: J28.3, R187.2
MISO_2: J19.1, R535.1, R560.1, U17.4 (Y), U115.15 (GPIO12)
MOSI_1_EXT: J28.2, R188.2
MOSI_2: J19.4, R557.1, R561.1, U19.2 (A), U115.18 (GPIO15)
unnamed: C46.1, R49.1, R57.2
unnamed: C49.1, C50.1, R59.1, R60.1
unnamed: C97.1, C167.1, R64.1, R84.1
unnamed: C228.1, J28.6, R174.1
unnamed: C320.1, J28.12, R179.2
unnamed: C321.1, R205.2, R206.2, U24.19 (Vcc(B))
unnamed: C470.1, R313.2, X6.2
unnamed: C473.1, CON1.6 (SHELL1), R314.1
unnamed: C484.2, C485.2, L43.2, U115.43 (ADC_AVDD)
unnamed: C632.1, J36.6, R580.1
unnamed: C633.1, J36.12, R583.2
unnamed: C634.1, R594.2, R595.2, U38.19 (Vcc(B))
unnamed: CON1.2 (D-), R308.1, U112.6 (I/O)
unnamed: CON1.3 (D+), R309.1, U112.1 (I/O)
unnamed: R85.1, U22.2 (A1)
unnamed: R100.1, U22.3 (A2)
unnamed: R129.1, U22.4 (A3)
unnamed: R132.1, U22.5 (A4)
unnamed: R163.1, U22.6 (A5)
unnamed: R164.1, U22.7 (A6)
unnamed: R165.1, U22.8 (A7)
unnamed: R166.1, U22.9 (A8)
unnamed: R167.1, U23.2 (A1)
unnamed: R168.1, U23.3 (A2)
unnamed: R169.1, U23.4 (A3)
unnamed: R170.1, U23.5 (A4)
unnamed: R175.2, U24.1 (A1)
unnamed: R176.2, U24.3 (A2)
unnamed: R177.2, U24.8 (A7)
unnamed: R178.2, U24.9 (A8)
unnamed: R180.1, U24.20 (B1)
unnamed: R181.1, U24.18 (B2)
unnamed: R182.1, U24.17 (B3)
unnamed: R187.1, U24.16 (B4)
unnamed: R188.1, U24.15 (B5)
unnamed: R202.1, U24.14 (B6)
unnamed: R203.1, U24.13 (B7)
unnamed: R204.1, U24.12 (B8)
unnamed: R317.2, U115.19 (TESTEN)
unnamed: R322.1, U23.6 (A5)
unnamed: R323.1, U23.7 (A6)
unnamed: R324.1, U23.8 (A7)
unnamed: R325.1, U23.9 (A8)
unnamed: R326.2, U22.18 (B1)
unnamed: R327.2, U22.17 (B2)
unnamed: R328.2, U22.16 (B3)
unnamed: R329.2, U22.15 (B4)
unnamed: R330.2, U22.14 (B5)
unnamed: R331.2, U22.13 (B6)
unnamed: R332.2, U22.12 (B7)
unnamed: R333.2, U22.11 (B8)
unnamed: R334.2, U23.18 (B1)
unnamed: R335.2, U23.17 (B2)
unnamed: R336.2, U23.16 (B3)
unnamed: R337.2, U23.15 (B4)
unnamed: R338.2, U23.14 (B5)
unnamed: R339.2, U23.13 (B6)
unnamed: R340.2, U23.12 (B7)
unnamed: R341.2, U23.11 (B8)
unnamed: R586.1, U38.20 (B1)
unnamed: R587.1, U38.18 (B2)
unnamed: R588.1, U38.17 (B3)
unnamed: R589.1, U38.16 (B4)
unnamed: R590.1, U38.15 (B5)
unnamed: R591.1, U38.14 (B6)
unnamed: R592.1, U38.13 (B7)
unnamed: R593.1, U38.12 (B8)
unnamed: U11.9 (QH'), U12.14 (SER)
unnamed: U13.4 (Y), U17.1 (OE)
PB0_pin: R178.1
PB0_pin_VDD_CON: J28.10, R204.2
PC4_pin: R177.1
PC4_pin_VDD_CON: J28.9, R203.2
QSPI_CSn: R310.1, R312.2, U113.1 (CSn), U114.1 (CSn), U115.56 (QSPI_SS_N)
QSPI_SCK: U113.6 (CLK), U114.6 (SCK), U115.52 (QSPI_SCLK)
QSPI_SD0: U113.5 (DI(IO0)), U114.5 (SI(I/O0)), U115.53 (QSPI_SD0)
QSPI_SD1: U113.2 (DO(IO1)), U114.2 (SO(I/O1)), U115.55 (QSPI_SD1)
QSPI_SD2: U113.3 (WPn(IO2)), U114.3 (WPn(I/O2)), U115.54 (QSPI_SD2)
QSPI_SD3: U113.7 (HLDn/RSTn_(IO3)), U114.7 (HOLDn(I/O3)), U115.51 (QSPI_SD3)
RESET: J19.5
RESETn: R311.2, SW2.2, U115.26 (RUN)
SC1905_#1_RESETn: C602.1, C603.1, R407.1, U12.1 (QB)
SC1905_#1_SSENn: U11.6 (QG)
SC1905_#2_RESETn: C604.1, C605.1, R408.1, U12.2 (QC)
SC1905_#2_SSENn: U11.7 (QH)
SCLK_1_EXT: J28.4, R182.2
SCLK_2: J19.3, U115.17 (GPIO14)
SDIO_2: R535.2, R557.2, U17.2 (A), U19.4 (Y)
SDO_2: R560.2, R561.2
SPI_2_MCU_DIR_OUT_in: R49.2, U11.15 (QA), U13.2 (A), U19.1 (OE)
SS_1_EXT: J28.1, R202.2
SWCLK: R316.1, U115.24 (SWCLK)
SWDIO: R315.1, U115.25 (SWDIO)
TX/rx_1_EXT: J28.7, R180.2
TX/rx_2_EXT: J28.8, R181.2
USB_BOOTn: J46.1, R310.2
USB_DM: R308.2, U115.46 (USB_DM)
USB_DP: R309.2, U115.47 (USB_DP)
VBUS_USB: CON1.1 (VBUS), U112.5 (Vp)
VDD_CON_J28: R174.2, R179.1, R206.1
VDD_CON_J36: R580.2, R583.1, R595.1
VDIO: C91.1, C92.1, C169.1, C179.1, C180.1, C181.1, C182.1, C183.1, C184.1, C229.1, C471.1, C472.1, C474.1, C475.1, C476.1, C477.1, C479.2, C480.1, C482.1, C486.1, C487.1, C631.1, J19.2, L43.1, R58.2, R60.2, R61.2, R71.2, R84.2, R205.1, R311.1, R312.1, R315.2, R316.2, R407.2, R408.2, R594.1, U11.16 (VCC), U12.16 (VCC), U13.5 (VCC), U17.5 (VCC), U19.5 (VCC), U20.5 (VCC), U22.20 (VCC), U23.20 (VCC), U24.2 (Vcc(A)), U24.10 (OE), U38.2 (Vcc(A)), U38.10 (OE), U113.8 (VCC), U114.8 (VCC), U115.1 (IOVDD), U115.10 (IOVDD), U115.22 (IOVDD), U115.33 (IOVDD), U115.42 (IOVDD), U115.44 (VREG_VIN), U115.48 (USB_VDD), U115.49 (IOVDD)
VREG_OUT_1V1: C478.2, C481.2, C483.2, U115.23 (DVDD), U115.45 (VREG_VOUT), U115.50 (DVDD)
XIN: C469.1, U115.20 (XIN), X6.1
XOUT: R313.1, U115.21 (XOUT)
data: U11.14 (SER), U115.11 (GPIO8)
g_TX\rx_1: R173.2, R175.1, U115.32 (GPIO21)
g_TX\rx_2: R173.1, R176.1, U115.34 (GPIO22)

Notes on the sheet:
USB_CONN
TVS_protection
Close to pin 44
Close to pin 45
place footprins one over another
RESET
90 Ohm DIF TL
Daisy Chain
5V pull-up
0V pull-down
SAENn towards LMS8001 #1
SCENn towards PLL #1
SBENn towards LMS8001 #2
RESETn towards LMS8001 #1
RESETn towards LMS8001 #2
SPI_SOFT CON
SDIO signal to MISO and MOSI
GPIO 00-07 of LMS8001 A or B to MCU_GPIO pins 13-20
3.3V pull-up
1.2-3.6V on A side
1.65-5V on B side
MCU_side
SPI_1 connector from 5G board
SSENn towards SC1905 #1
SSENn towards SC1905 #2
SPI #1
SPI #2
RESETn towards SC1905 #1
RESETn towards SC1905 #2
NOT CONNECTED!
MCU GPIO pins to LMS8001 #1 and #2 GPIO pins
Free MCU GPIO pins
Interrupts
global TX/rx
Communication with other board
Communication with periferials on same board
MOSI and MISO changed from datasheet because MCU is slave on this SPI bus
Free MCU pins to out connector
