myriadrf/LimeRFE-8001P/hardware/1v0/KiCAD/SC1905.sch

## KiCad design hardware/1v0/KiCAD/SC1905.sch (2023-10-04)

Schematic: SC1905.sch

Parts:
C397: NF_1uF_0603_GRM188R61A105KA61D; SMD0603; Manufacturer Part Number GRM188R61A105KA61D
C398: NF_2.2uF_0603_GRM188R71A225KE15J; SMD0603; Manufacturer Part Number GRM188R71A225KE15J
C399, C403, C405, C516, C517, C521, C522, C523, C524: NF_10pF_0402_GJM1555C1H100GB01D; SMD0402; Manufacturer Part Number GJM1555C1H100GB01D
C400, C404: NF_1nF_0402_GRM1555C1H102JA01D; SMD0402; Manufacturer Part Number GRM1555C1H102JA01D
C406, C407, C509: 15pF_0402_GJM1555C1H150JB01D; SMD0402; Manufacturer Part Number GJM1555C1H150JB01D
C408: 0.2pF_0402_GJM1555C1HR20BB01D; SMD0402; Manufacturer Part Number GJM1555C1HR20BB01D
C409, C450, C490, C491, C492, C493, C494, C495, C496, C497, C498, C499, C501, C502, C504, C519, C520: 1nF_0402_GRM1555C1H102JA01D; SMD0402; Manufacturer Part Number GRM1555C1H102JA01D
C410: 0.9pF_0402_GJM1555C1HR90BB01D; SMD0402; Manufacturer Part Number GJM1555C1HR90BB01D
C411, C507, C508: 2.2uF_0603_GRM188R71A225KE15J; SMD0603; Manufacturer Part Number GRM188R71A225KE15J
C503: 0.5pF_0402_GJM1555C1HR50BB01D; SMD0402; Manufacturer Part Number GJM1555C1HR50BB01D
C514, C515: 10pF_0402_GJM1555C1H100GB01D; SMD0402; Manufacturer Part Number GJM1555C1H100GB01D
D1, D2: LED_1208_GREEN_SML-LX23GC-TR; LED_1208; Manufacturer Part Number SML-LX23GC-TR
J32: 10056844-114LF; Manufacturer PN 10056844-114LF
J42, J43: SMA_vert_SMD; Manufacturer Part Number 0732511352
L42: 470R_0402_BLM15BD471SN1D; SMD0402; Manufacturer Part Number BLM15BD471SN1D
L44, L45: 5.6nH_0402_HK10055N6S-T; SMD0402; Manufacturer Part Number HK10055N6S-T
L46: 18nH_0402_HK100518NJ-T; SMD0402; Manufacturer Part Number HK100518NJ-T
L57, L58: 1.2nH_0402_HK10051N2S-T; SMD0402; Manufacturer Part Number HK10051N2S-T
L59: 3.3nH_0402_HK10053N3S-T; SMD0402; Manufacturer Part Number HK10053N3S-T
L60: 8.2nH_0402_HK10058N2J-T; SMD0402; Manufacturer Part Number HK10058N2J-T
L61, L62: 2.2nH_0402_HK10052N2S-T; SMD0402; Manufacturer Part Number HK10052N2S-T
L63, L64: 120R_0603_BLM18AG121SN1D; SMD0603; Manufacturer Part Number BLM18AG121SN1D
Q1: NF_MMBT3904; MMBT3904; Manufacturer Part Number MMBT3904
Q2: 2N7002; SOT-23; Manufacturer PN 2N7002
R349, R351: 49.9R_0402_ERJ-U02F49R9X; SMD0402; Manufacturer Part Number ERJ-U02F49R9X
R350, R356, R357, R358, R359, R362, R365, R366, R367, R378, R385, R386, R387, R400, R401, R402, R403: 0R_0402_NF; SMD0402; Manufacturer Part Number RC0402JR-070RL
R352, R353, R354, R355, R363, R364: 0R_0402_RC0402JR-070RL; SMD0402; Manufacturer Part Number RC0402JR-070RL
R360, R361, R368, R369, R380, R388, R389, R390, R391, R392, R393, R394, R395, R396, R397, R398, R399: NF_10K_0402; SMD0402
R370: NF_0R_0402_RCS04020000Z0ED; SMD0402; Manufacturer Part Number RCS04020000Z0ED
R371: 12.4K_0402_ERJ-2RKF1242X; SMD0402; Manufacturer Part Number ERJ-2RKF1242X
R376: 10K_0402_Yageo; SMD0402; Manufacturer Part Number RC0402JR-7D10KL
R381, R382: 510R_0402_RC0402JR-07510RL; SMD0402; Manufacturer Part Number RC0402JR-07510RL
SW3: SW_PUSH; B3U-1000P; Manufacturer Part Number B3U-1000P
U90: BDCN-7-25+; Manufacturer Part Number BDCN-7-25+
U92: XDL15-2-020S; Manufacturer Part Number XDL15-2-020S
U116: DC1722J5010AHF; Manufacturer Part Number DC1722J5010AHF
U117: NF_TMP36GRTZ-REEL7; TMP36GRTZ-REEL7; Manufacturer Part Number TMP36GRTZ-REEL7
U118, U119, U121: BD1722J50100AHF; Manufacturer Part Number BD1722J50100AHF
U120: SC1905; SC1905A-00A00; Manufacturer Part Number SC1905A-00A00
U122: NF_LMV324QDRG4; LMV324QDRG4; Manufacturer Part Number LMV324QDRG4
X1: 278-20.0M-20-W-TR; Manufacturer Part Number 278-20.0M-20-W-TR

Notes on the sheet:
C14
C12
R12
C17
C26
FT3
C31
C33
R27
R25
R26
RFOUT Attenuator
DC2
R10
C48
R102
R17
R13
R15
R14
Thru Path Attenuator
R11
Optional RF Thru Path without Delay Line
DC1
R16
C47
R23
R21
R24
RFIN Attenuator
C18
C28
C34
C35
C20
C36
C45
C32
FT2
C29
C30
C27
C25
C13
C10
C11
C15
FT1
SW1
R12 must have 1% tolerance and 100ppm/C temperature coefficient!
R46
R47
R44
R65
C42
R40
Vadj = +0.84V
20dB Attenuator
Power Detector
Temperature Sensor
R64
R53
R54
R51
R57
R58
C38
R49
R56
R55
C37
R52
R60
R59
R50
C39
