myriadrf/LimeRFE-8001P/hardware/1v0/KiCAD/SC2200.sch

## KiCad design hardware/1v0/KiCAD/SC2200.sch (2023-10-04)

Schematic: SC2200.sch

Parts:
C35, C43, C44, C45, C447, C448, C449, C451: 10nF_0402; SMD0402; Manufacturer Part Number CC0402ZRY5V7BB103
C412, C418, C420, C425: 100pF_0402_GRM1555C1H101JA01D; SMD0402; Manufacturer Part Number GRM1555C1H101JA01D
C413, C424, C443: 1uF_0402_CC0402ZRY5V5BB105; SMD0402; Manufacturer Part Number CC0402ZRY5V5BB105
C414, C417, C431, C433: 10pF_0402_GJM1555C1H100GB01D; SMD0402; Manufacturer Part Number GJM1555C1H100GB01D
C415, C423, C427, C429, C430, C434, C435, C437, C438, C440, C441, C442, C445: 1000pF_0402_GRM1555C1H102GA01D; SMD0402; Manufacturer Part Number GRM1555C1H102GA01D
C416, C422: 0.5pF_0402_GJM1555C1HR50BB01D; SMD0402; Manufacturer Part Number GJM1555C1HR50BB01D
C419, C421, C488, C489: 1.3pF_0402_GJM1555C1H1R3BB01D; SMD0402; Manufacturer Part Number GJM1555C1H1R3BB01D
C426, C428, C439, C444: 2.2uF_0603_GRM188R71A225KE15J; SMD0603; Manufacturer Part Number GRM188R71A225KE15J
C432, C436, C446: 100nF_0402_C1005X7R1A104K050BB; SMD0402; Manufacturer Part Number C1005X7R1A104K050BB
J1: 15110122601000; Manufacturer PN 15110122601000
J29, J35: TSM-102-04-T-SV; Manufacturer Part Number 200-TSM10204TSV
J33: Jumper_SNM-100-BK-T; SNM-100-BK-T; Manufacturer Part Number SNM-100-BK-T
J34: PMOD_CONN; Manufacturer Part Number 95278-401-06LF
L47, L52: 470R_0402_BLM15BD471SN1D; SMD0402; Manufacturer Part Number BLM15BD471SN1D
L48, L50: 5.6nH_0402_HK10055N6S-T; SMD0402; Manufacturer Part Number HK10055N6S-T
L49, L51: 10nH_0402_HK100510NJ-T; SMD0402; Manufacturer Part Number HK100510NJ-T
L53, L54, L55, L56: 120R_0603_BLM18AG121SN1D; SMD0603; Manufacturer Part Number BLM18AG121SN1D
R3, R4, R5, R6, R7, R8, R9, R10, R11, R12, R13, R14, R15, R16, R17, R18, R19, R20, R21, R22, R23, R24, R25, R26, R27, R28, R43, R46, R47: 0R_0402; SMD0201
R44, R48, R220, R223: NF_0R_0402_RCS04020000Z0ED; SMD0402; Manufacturer Part Number RCS04020000Z0ED
R215, R216, R222, R225, R226, R227, R228, R231, R233, R235, R236, R237, R239: 0RNF_0402; SMD0402
R217, R219, R221, R224, R229, R230, R232, R234, R238, R240, R241, R243: 0R_0402_RC0402JR-070RL; SMD0402; Manufacturer Part Number RC0402JR-070RL
R218, R242: 49.9R_0402_ERJ-U02F49R9X; SMD0402; Manufacturer Part Number ERJ-U02F49R9X
R246: 10K_0402; SMD0402
R259: 20K_0402_CRCW040220K0FKEDC; SMD0402; Manufacturer Part Number CRCW040220K0FKEDC
SW1: SW_PUSH; B3U-1000P; Manufacturer Part Number B3U-1000P
U3, U98: NXB0108PW-Q100J; Manufacturer Part Number NXB0108PW-Q100J
U93, U97: XDL15-3-030S; Manufacturer Part Number XDL15-3-030S
U94, U96: DC1722J5005AHF; Manufacturer Part Number DC1722J5005AHF
U95: SC2200
U99: SN74CBT3245APWE4; Manufacturer Part Number SN74CBT3245APWE4
X3: 278-20.0M-20-W-TR; Manufacturer Part Number 278-20.0M-20-W-TR
X4, X5: SMA_vert_SMD; Manufacturer Part Number 0732511352

Notes on the sheet:
S100
DC104
R165
C161
C154
R265
R263
R262
R252
R167
R161
R222
R194
R192
R223
U103
R166
C162
R168
R162
DC1015
C156
R172
R254
R255
R253
R195
R201
R193
R241
U104
C160
C292
C163
C293
C147
L104
C146
C153
C151
FT104
C148
L105
C143
C155
C152
FT105
R300
R301
Y100
C101
C102
R250
R251
R121
R124
FT103
C140
C141
C126
C120
C108
C106
FT101
C118
C119
FT100
C112
C113
FR102
C139
C138
C131
C130
C116
C115
C114
C111
C109
C107
C142
R118
1.2-3.6V on A side
1.65-5V on B side
U100B
U100A
U100D
U100C
J112
20 MHz
Jumper ON - SPI of SC2200 connected to MCU Jumper OFF - SPI of SC2200 disconnected from MCU
