myriadrf/LimeRFE-8001P/hardware/1v1/KiCAD/AMP_RFIN1.sch

## KiCad design hardware/1v1/KiCAD/AMP_RFIN1.sch (2023-10-04)

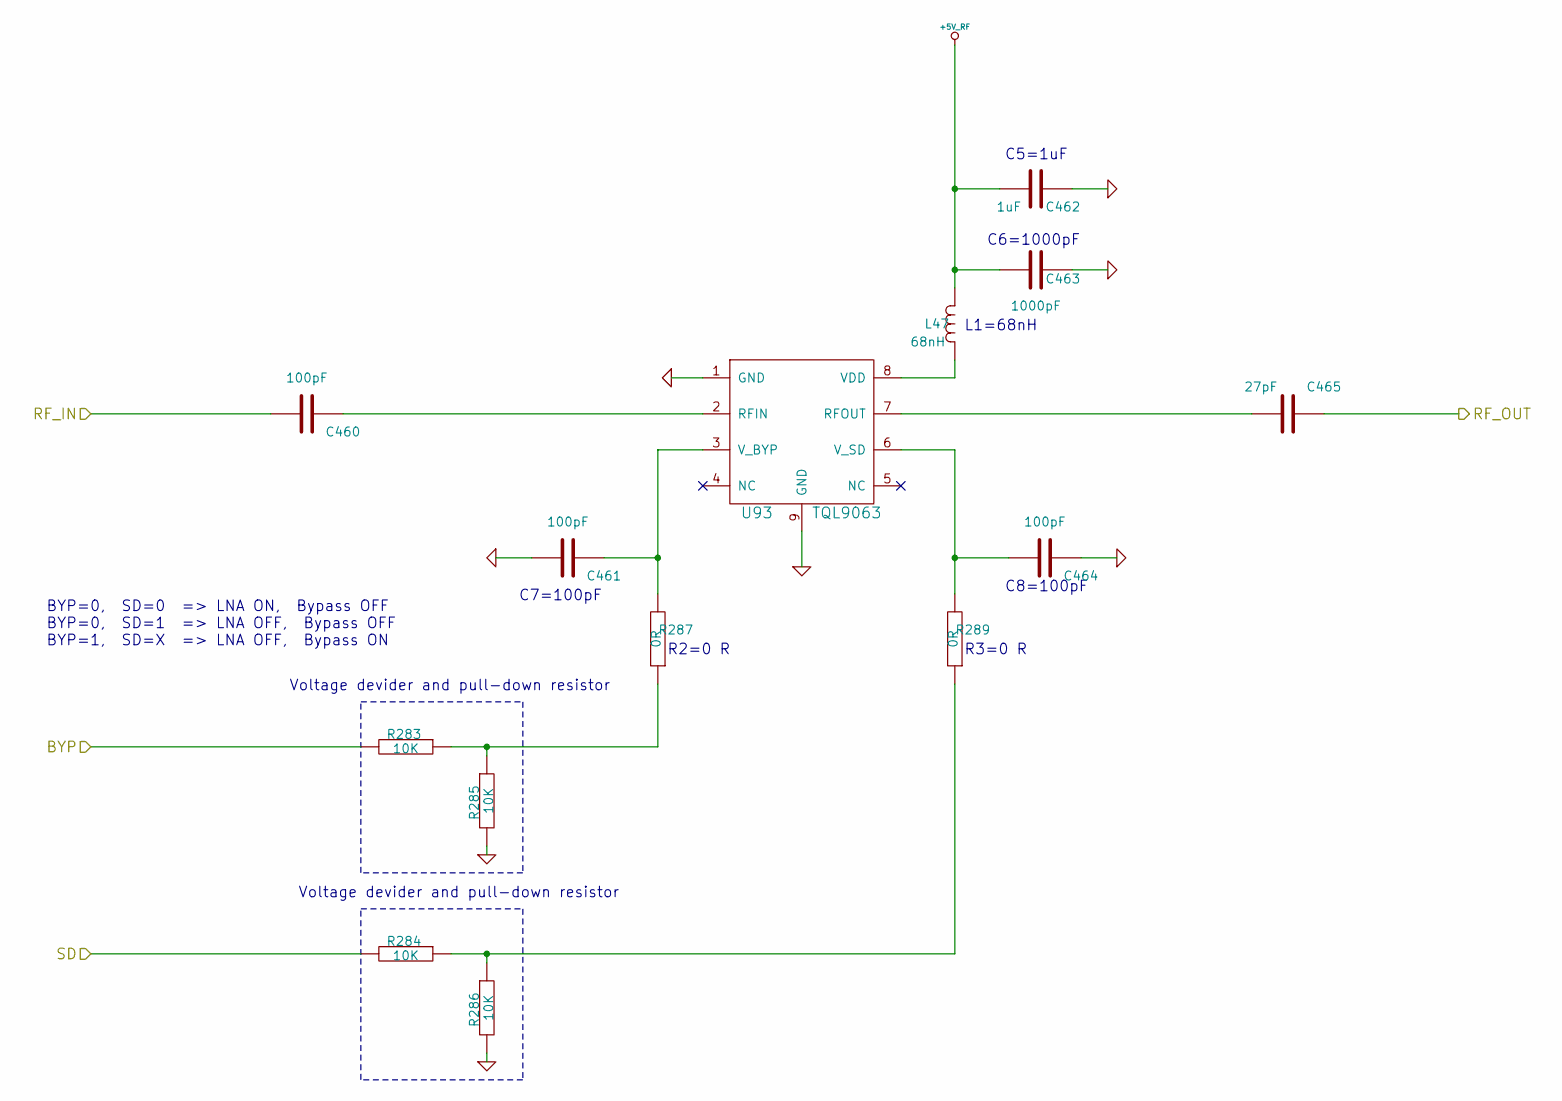
[picture p90: schematic AMP_RFIN1.sch]

Parts:
C460, C461, C464: 100pF_0402_ECJ-0EC1H101J; SMD0402; Manufacturer Part Number ECJ-0EC1H101J
C462: 1uF_0402_CC0402ZRY5V5BB105; SMD0402; Manufacturer Part Number CC0402ZRY5V5BB105
C463: 1000pF_0402_GCM155R71H102KA37D; SMD0402; Manufacturer Part Number GCM155R71H102KA37D
C465: 27pF_0402_GCM1555C1H270FA16D; SMD0402; Manufacturer Part Number GCM1555C1H270FA16D
L47: 68nH_0603_0603CS-68NXJLW; SMD0603; Manufacturer Part Number 0603CS-68NXJLW
R283, R284, R285, R286: 10K_0402; SMD0402
R287, R289: 0R_0402; SMD0402
U93: TQL9063; Manufacturer Part Number TQL9063

Connections:
+5V_RF: C462.2, C463.2, L47.1
BYP: R283.2
GND: C461.2, C462.1, C463.1, C464.1, R285.2, R286.2, U93.1 (GND), U93.9 (GND)
unnamed: C460.1, U93.2 (RFIN)
unnamed: C461.1, R287.2, U93.3 (V_BYP)
unnamed: C464.2, R289.2, U93.6 (V_SD)
unnamed: C465.2, U93.7 (RFOUT)
unnamed: L47.2, U93.8 (VDD)
unnamed: R283.1, R285.1, R287.1
unnamed: R284.1, R286.1, R289.1
RF_IN: C460.2
RF_OUT: C465.1
SD: R284.2

Notes on the sheet:
C7=100pF
R2=0 R
C8=100pF
R3=0 R
L1=68nH
C6=1000pF
C5=1uF
Voltage devider and pull-down resistor
BYP=0, SD=0 => LNA ON, Bypass OFF BYP=0, SD=1 => LNA OFF, Bypass OFF BYP=1, SD=X => LNA OFF, Bypass ON
