myriadrf/LimeRFE-8001P/hardware/1v1/KiCAD/AMP_RFIN2.sch

## KiCad design hardware/1v1/KiCAD/AMP_RFIN2.sch (2023-10-04)

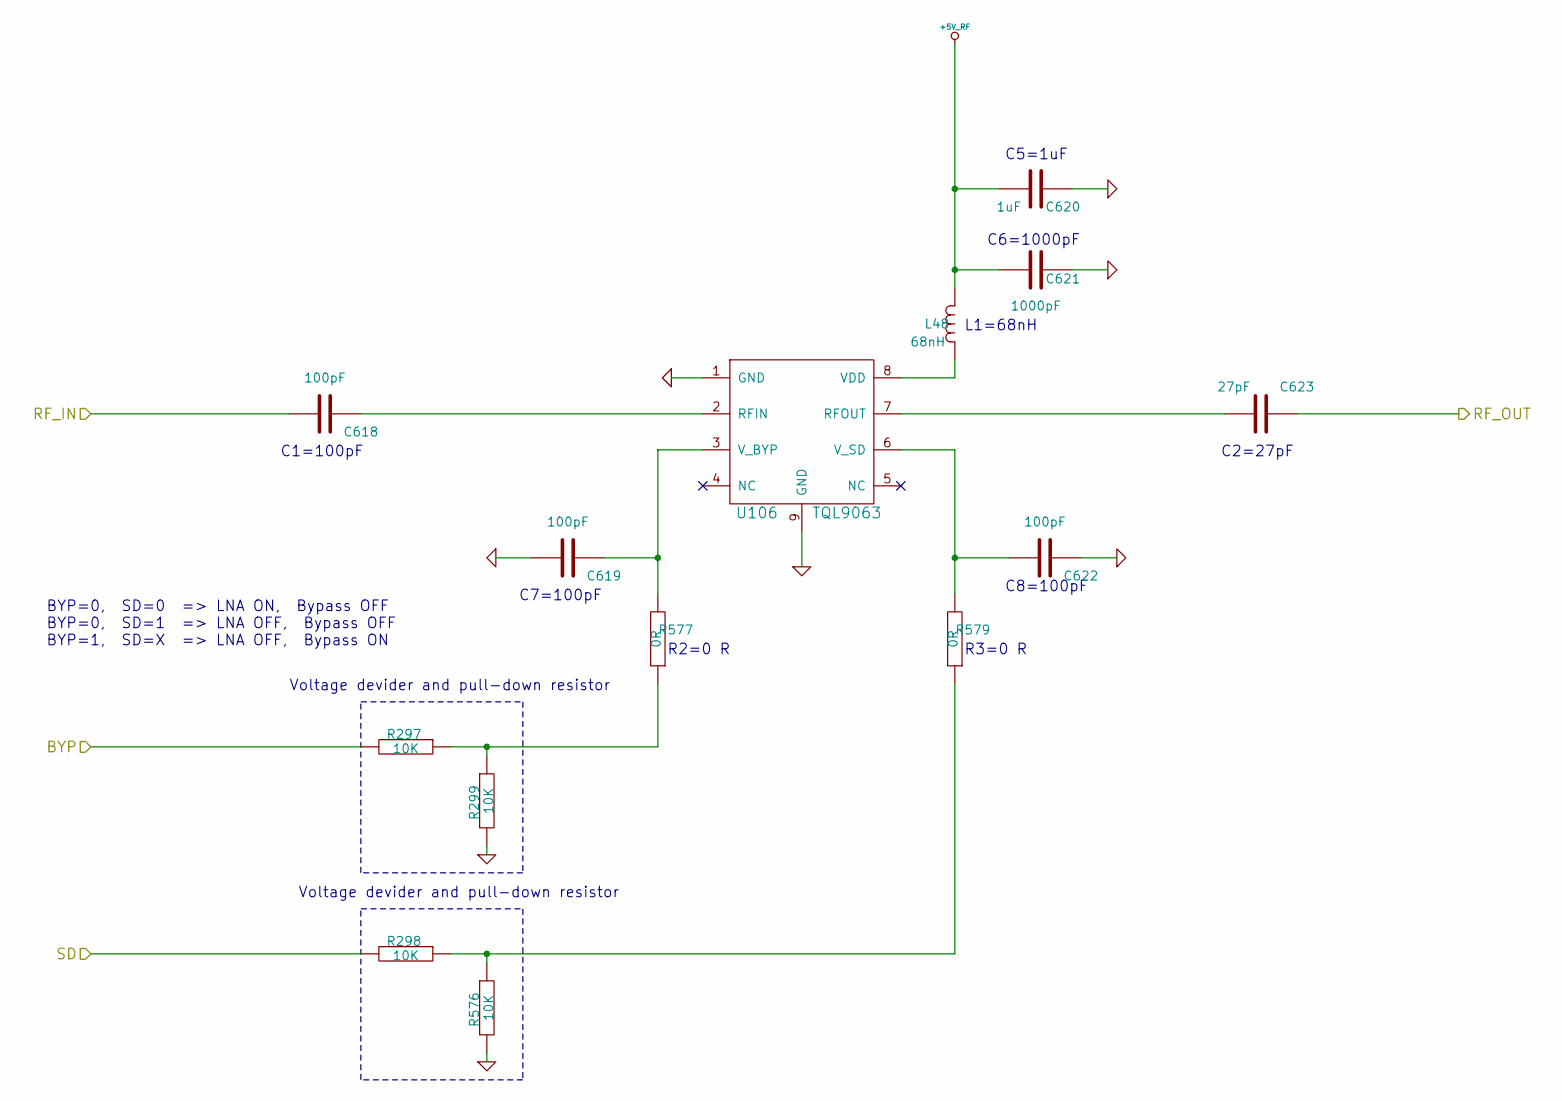
[picture p91: schematic AMP_RFIN2.sch]

Parts:
C618, C619, C622: 100pF_0402_ECJ-0EC1H101J; SMD0402; Manufacturer Part Number ECJ-0EC1H101J
C620: 1uF_0402_CC0402ZRY5V5BB105; SMD0402; Manufacturer Part Number CC0402ZRY5V5BB105
C621: 1000pF_0402_GCM155R71H102KA37D; SMD0402; Manufacturer Part Number GCM155R71H102KA37D
C623: 27pF_0402_GCM1555C1H270FA16D; SMD0402; Manufacturer Part Number GCM1555C1H270FA16D
L48: 68nH_0603_0603CS-68NXJLW; SMD0603; Manufacturer Part Number 0603CS-68NXJLW
R297, R298, R299, R576: 10K_0402; SMD0402
R577, R579: 0R_0402; SMD0402
U106: TQL9063; Manufacturer Part Number TQL9063

Connections:
+5V_RF: C620.2, C621.2, L48.1
BYP: R297.2
GND: C619.2, C620.1, C621.1, C622.1, R299.2, R576.2, U106.1 (GND), U106.9 (GND)
unnamed: C618.1, U106.2 (RFIN)
unnamed: C619.1, R577.2, U106.3 (V_BYP)
unnamed: C622.2, R579.2, U106.6 (V_SD)
unnamed: C623.2, U106.7 (RFOUT)
unnamed: L48.2, U106.8 (VDD)
unnamed: R297.1, R299.1, R577.1
unnamed: R298.1, R576.1, R579.1
RF_IN: C618.2
RF_OUT: C623.1
SD: R298.2

Notes on the sheet:
C1=100pF
C2=27pF
C7=100pF
R2=0 R
C8=100pF
R3=0 R
L1=68nH
C6=1000pF
C5=1uF
Voltage devider and pull-down resistor
BYP=0, SD=0 => LNA ON, Bypass OFF BYP=0, SD=1 => LNA OFF, Bypass OFF BYP=1, SD=X => LNA OFF, Bypass ON
