myriadrf/LimeRFE-8001P/hardware/1v1/KiCAD/Clocks.sch

## KiCad design hardware/1v1/KiCAD/Clocks.sch (2023-10-04)

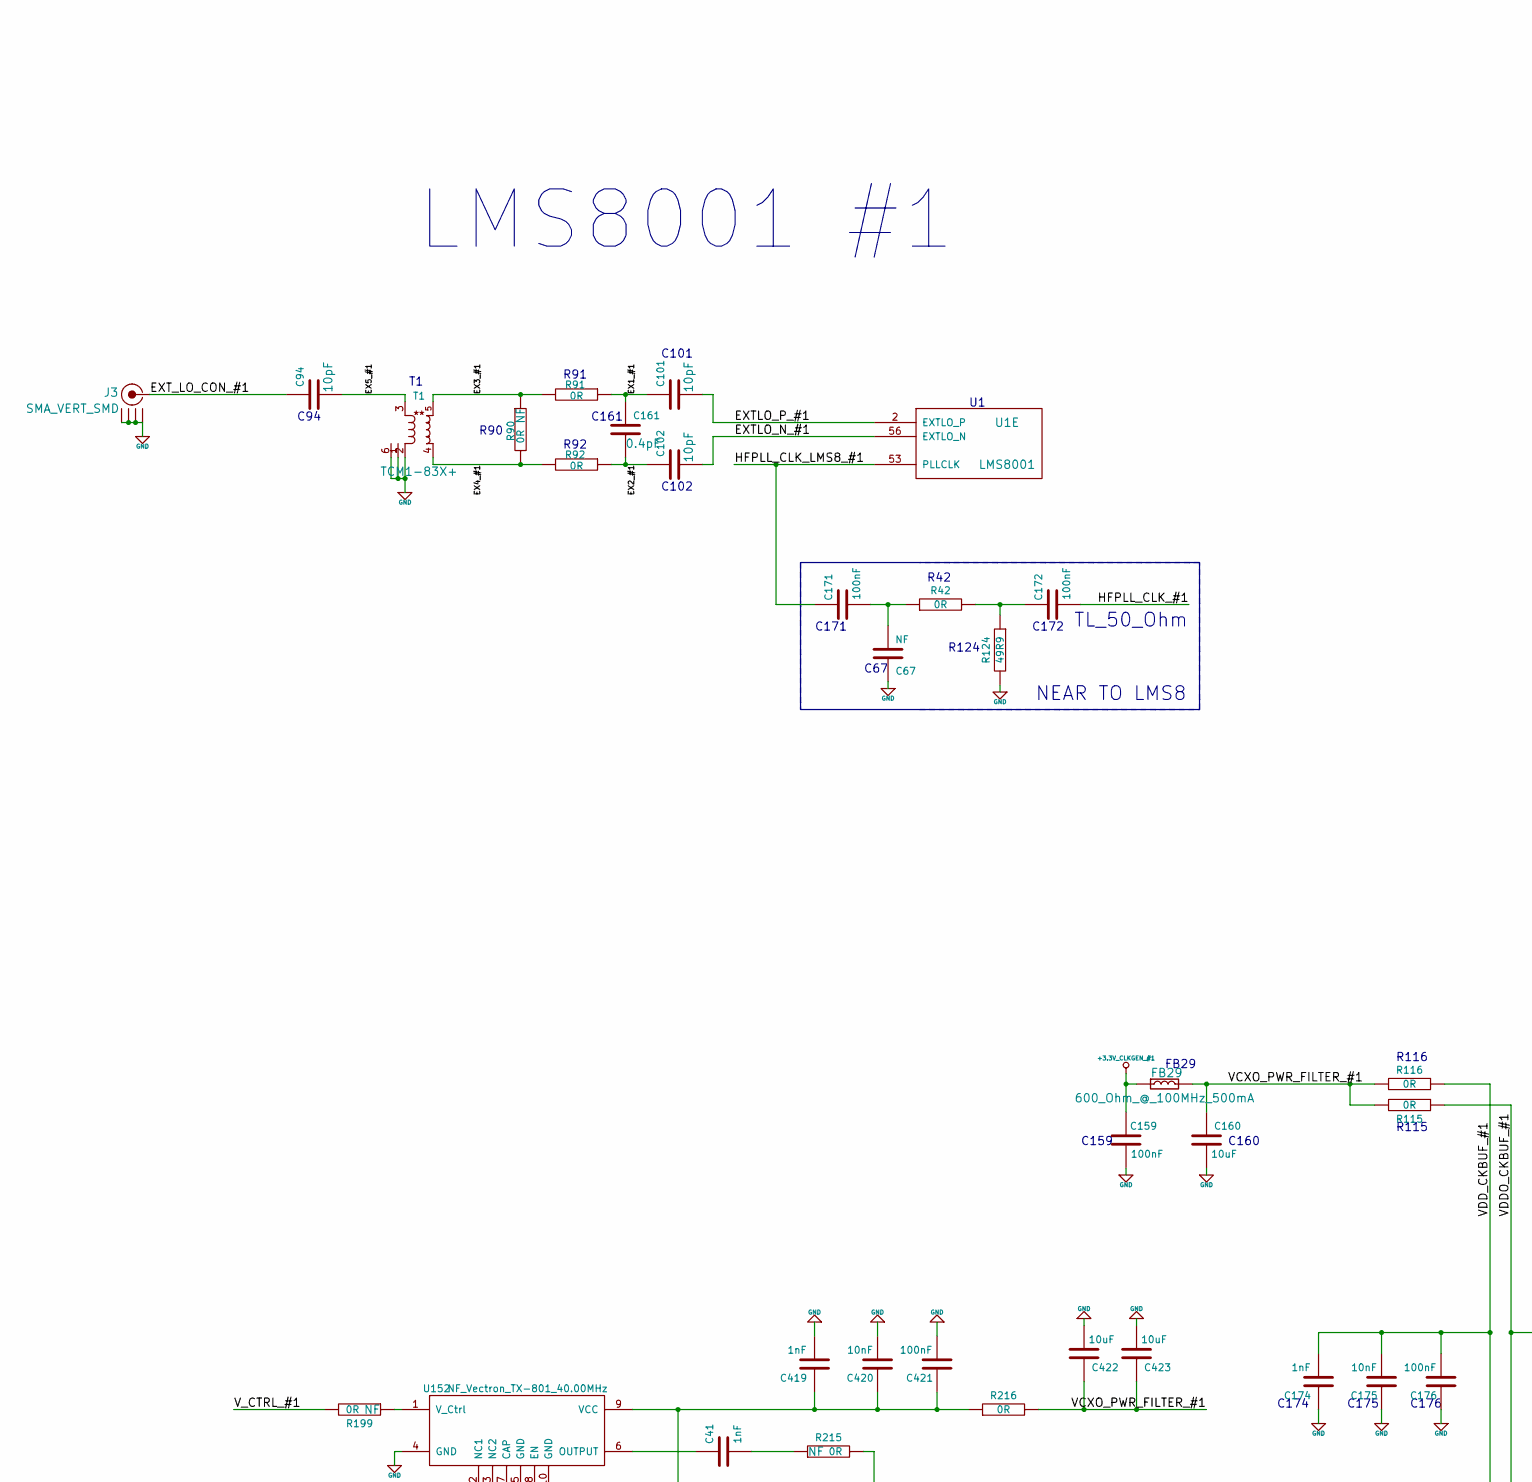
[picture p92: schematic Clocks.sch, part in row 1, column 1]

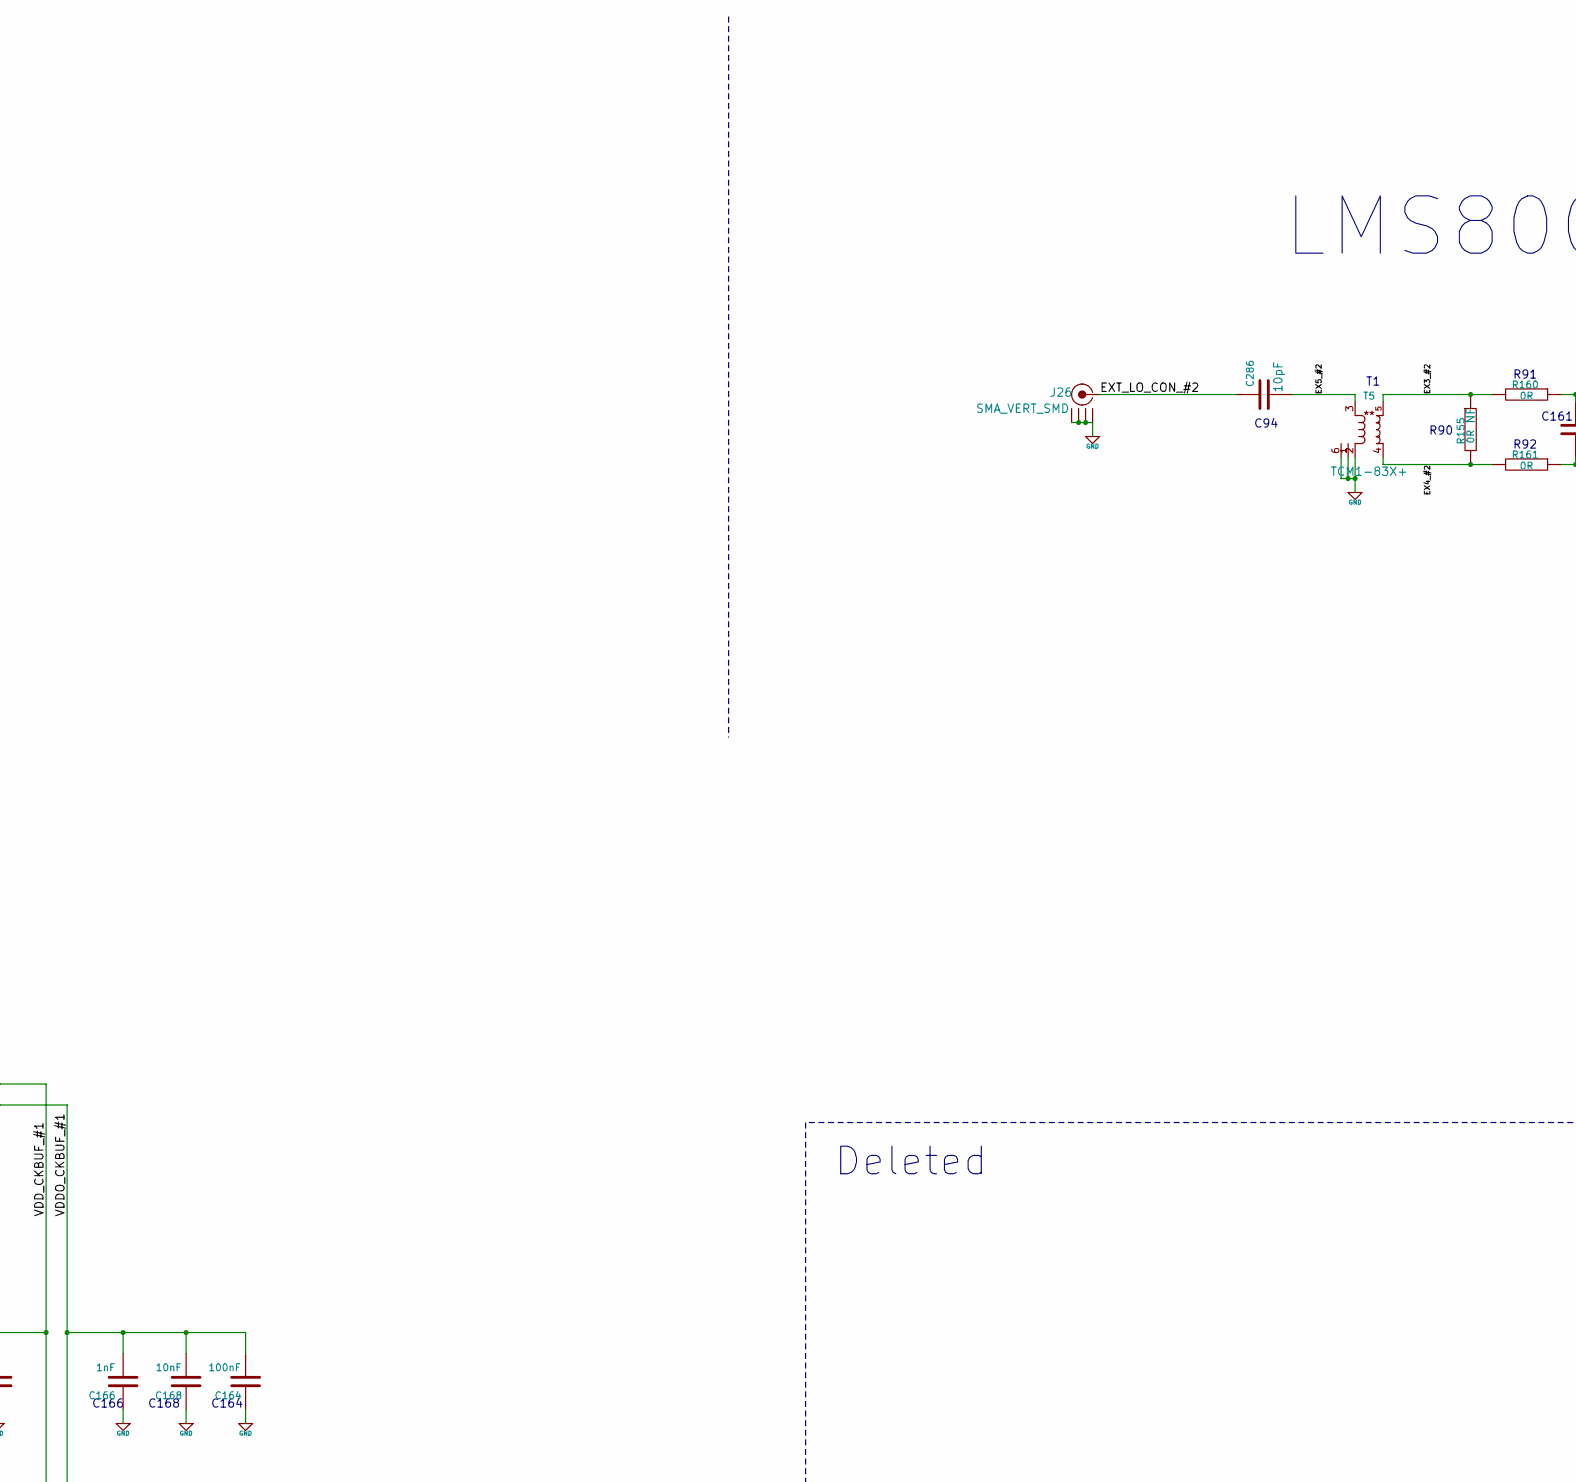
[picture p93: schematic Clocks.sch, part in row 1, column 2]

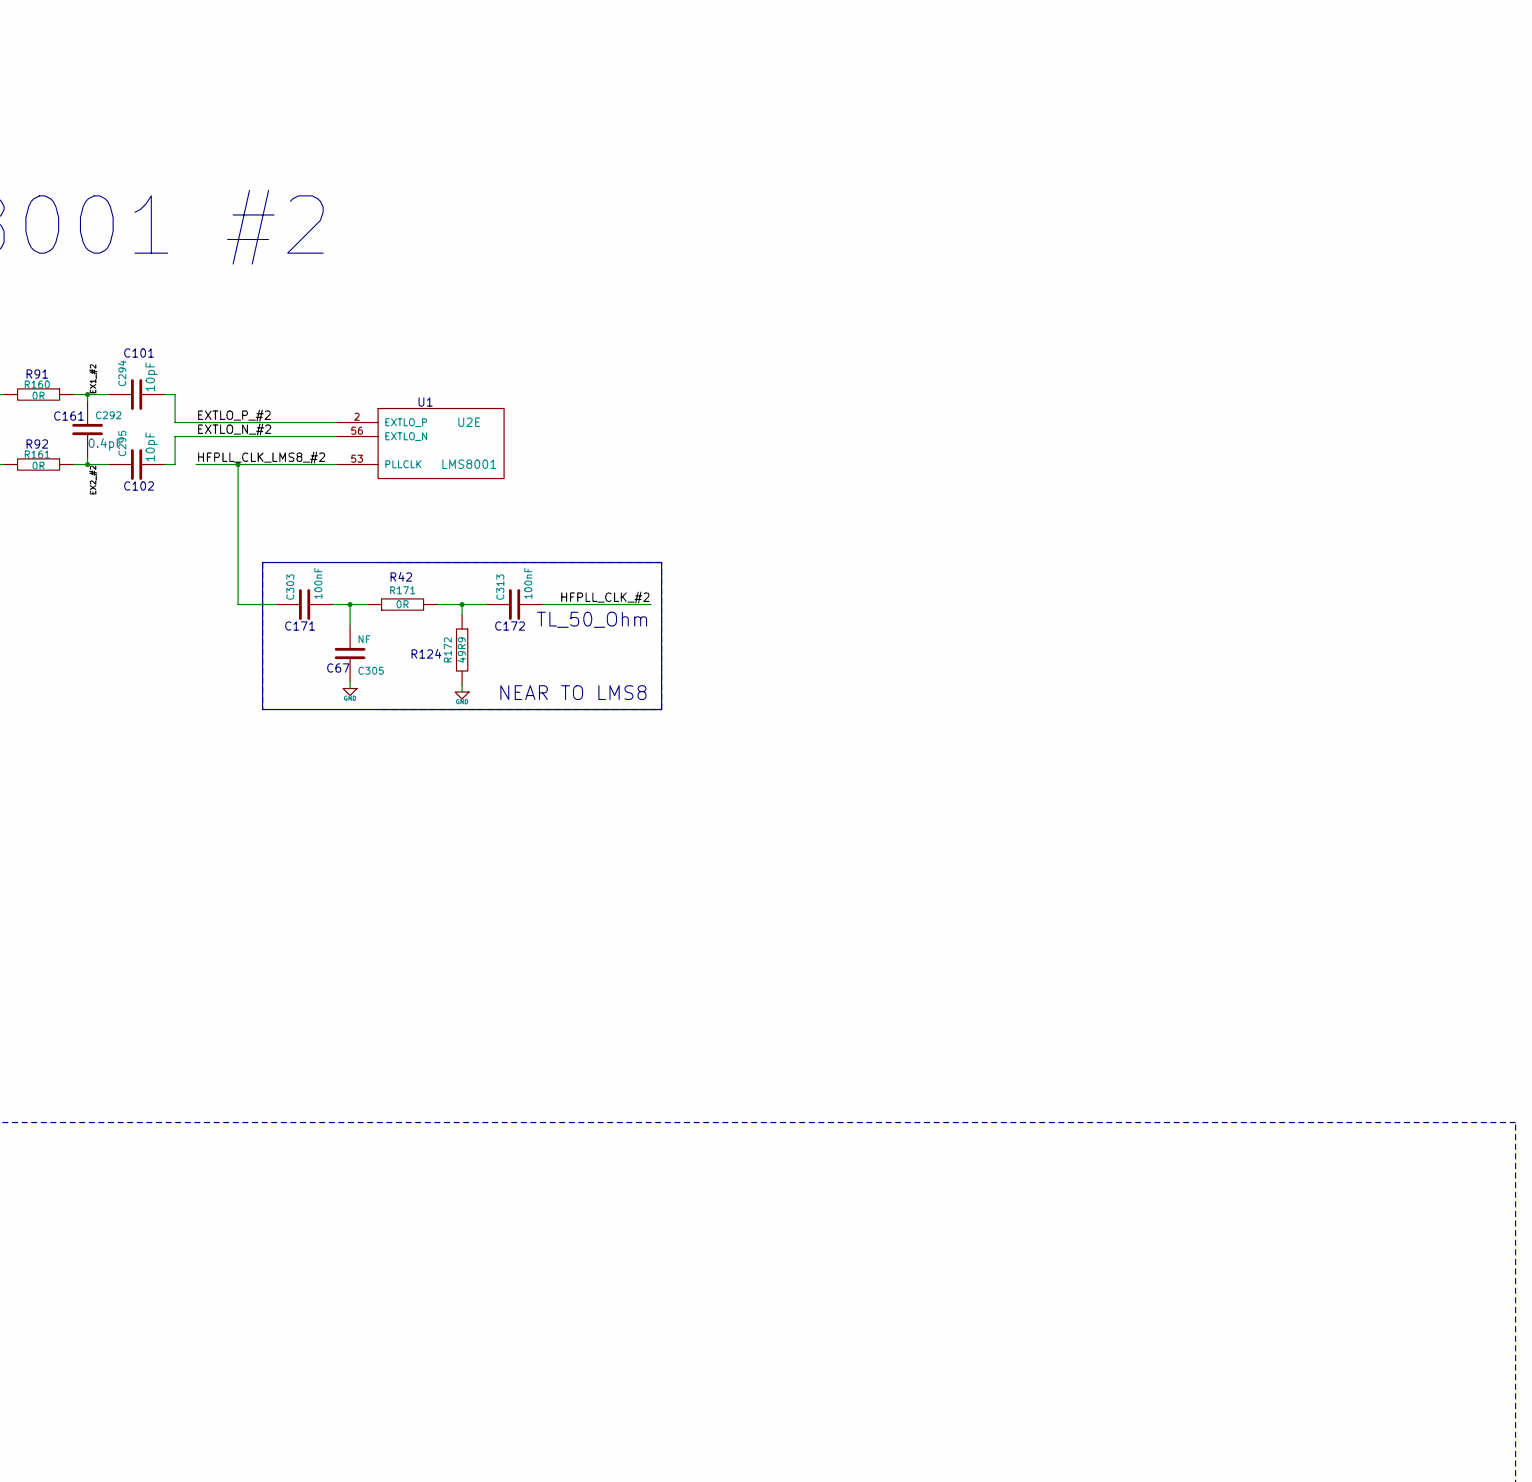
[picture p94: schematic Clocks.sch, part in row 1, column 3]

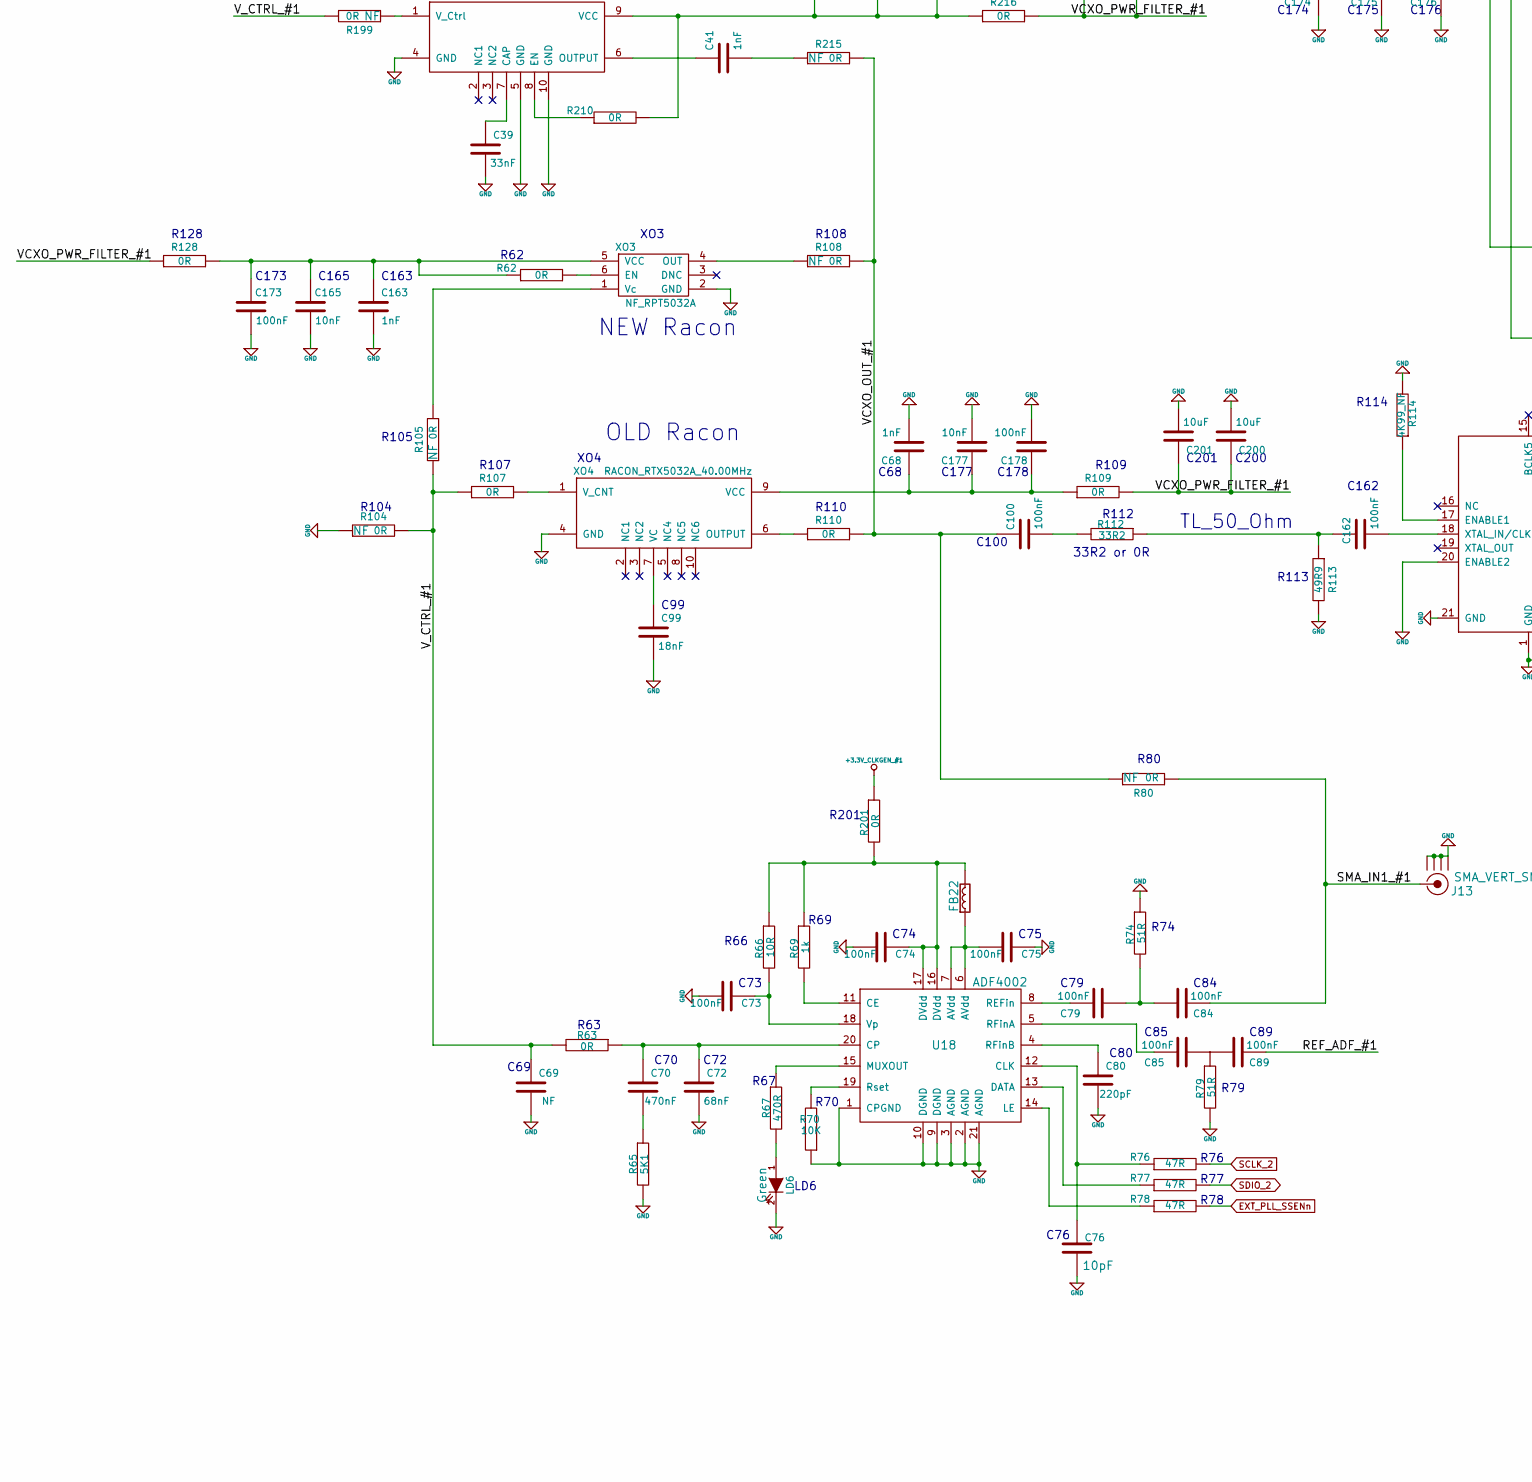
[picture p95: schematic Clocks.sch, part in row 2, column 1]

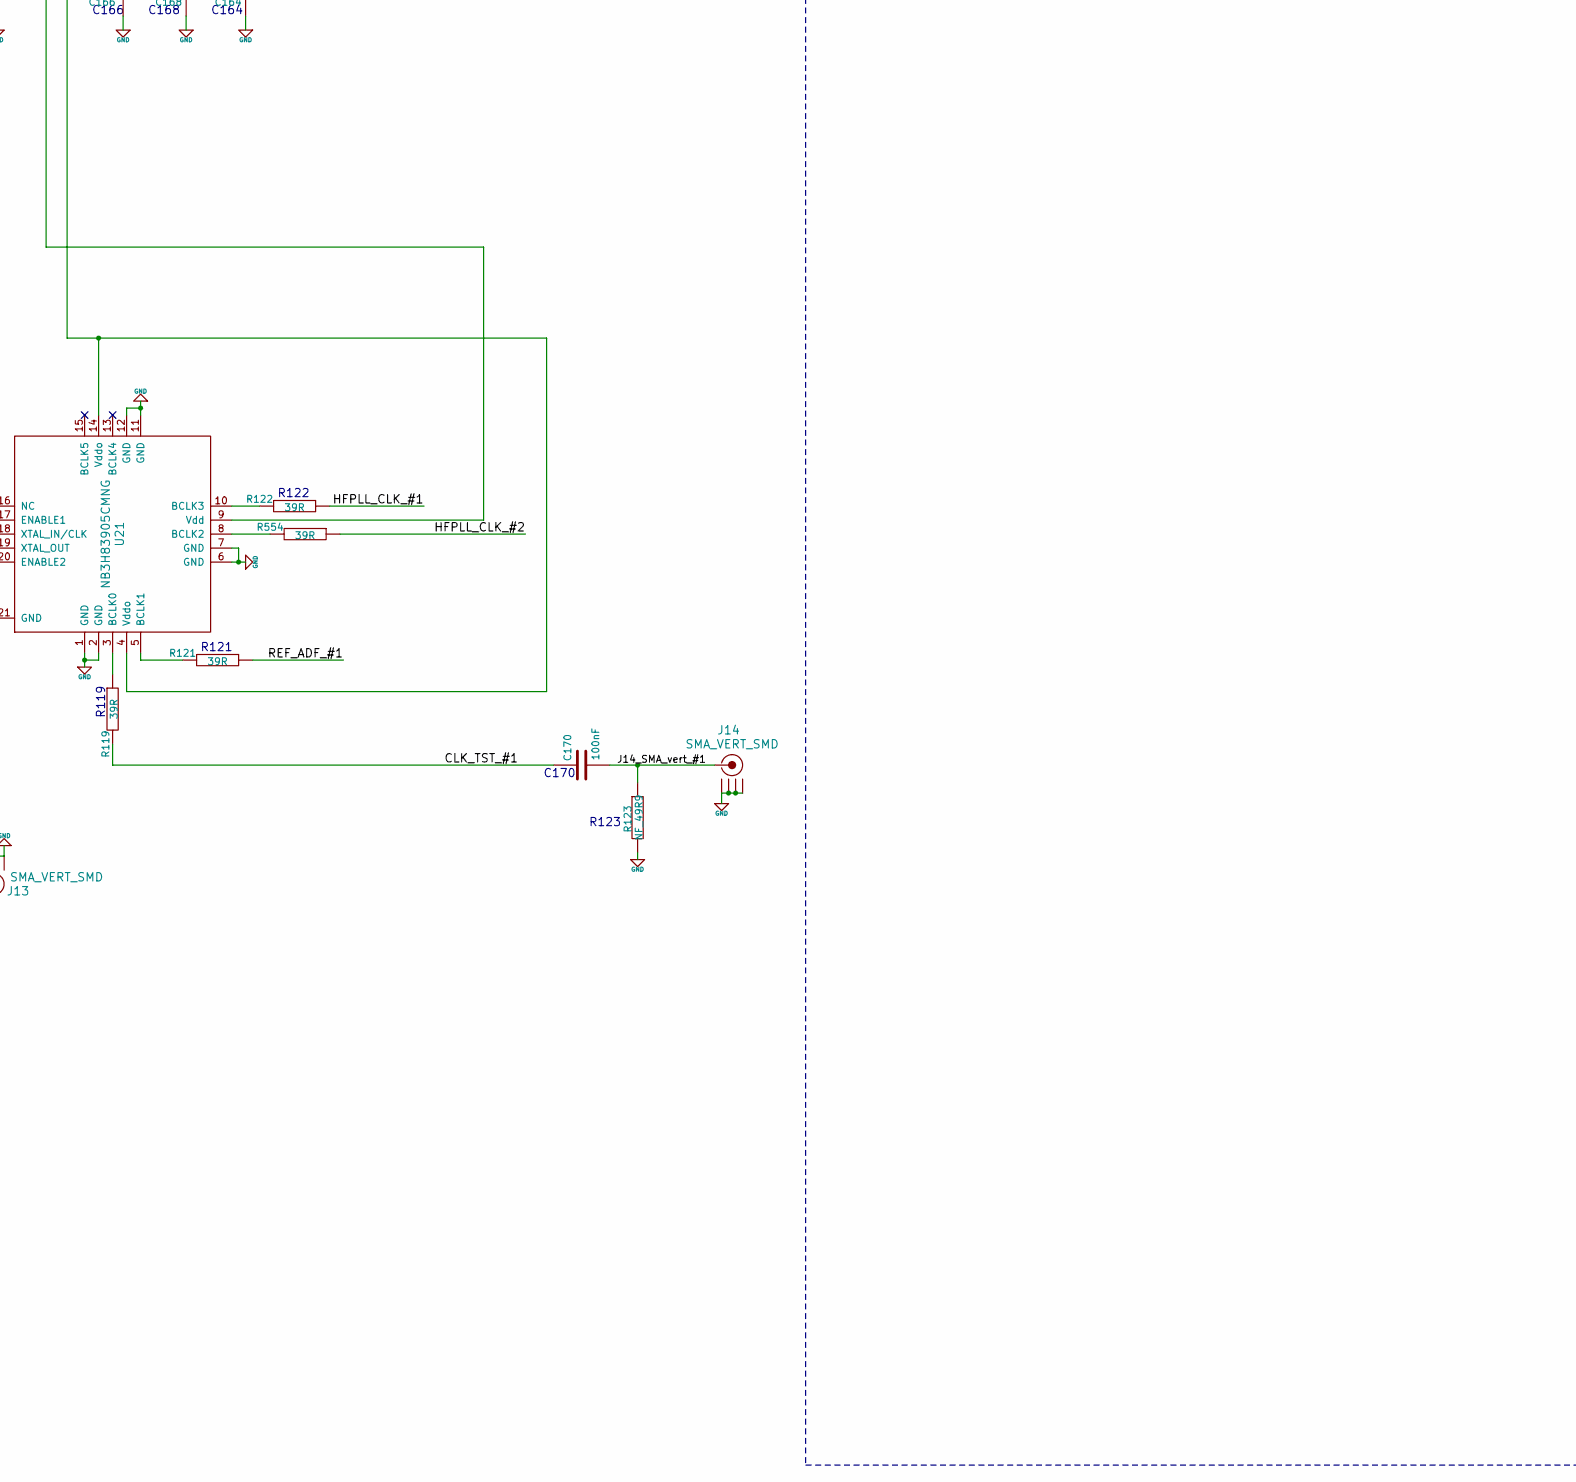
[picture p96: schematic Clocks.sch, part in row 2, column 2]

Parts:
C39: 33nF_0402; SMD0402; Manufacturer Part Number C0402C333J3RECAUTO
C41: 1nF_0402; SMD0402; Manufacturer Part Number CC0402KRX7R9BB102
C67, C73, C74, C75, C79, C84, C85, C89, C100, C159, C162, C164, C170, C171, C172, C173, C176, C178, C303, C305, C313, C421: 100NF_0402; SMD0402; Manufacturer Part Number GRM155R71C104KA88D
C68, C163, C166, C174, C419: 1NF_0402; SMD0402; Manufacturer Part Number GCM155R71H102KA37D
C69: 1.2NF_0402; SMD0402; Manufacturer Part Number GRM155R71H122KA01D
C70: 470NF_0402; SMD0402; Manufacturer Part Number GRM155R61A474KE15D
C72: 68NF_0402; SMD0402; Manufacturer Part Number GRM155R71H683ME14D
C76: 10PF_0402; SMD0402; Manufacturer Part Number 04023A100JAT2A
C80: 220PF_0402; SMD0402; Manufacturer Part Number CC0402KRX7R9BB221
C94, C101, C102, C286, C294, C295: 10PF_0201; SMD0201; Manufacturer Part Number C0603C0G1H100D030BA
C99: 18NF_0402; SMD0402; Manufacturer Part Number CC0402KRX7R7BB183
C160: 10UF_0603; SMD0603_gap04; Manufacturer Part Number GRM188R61C106MA73D
C161, C292: 0.4PF_0201; SMD0201; Manufacturer Part Number GJM0335C1ER40WB01D
C165, C168, C175, C177, C420: 10NF_0402; SMD0402; Manufacturer Part Number GCM155R71E103KA37D
C200, C201, C422, C423: 10UF_0603; SMD0603; Manufacturer Part Number GRM188R61C106MA73D
FB22: FB_600R_0402; SMD0402; Manufacturer Part Number MMZ1005S601C
FB29: BLM18EG601SN1D; SMD0603_gap04; Manufacturer Part Number BLM18EG601SN1D
J3, J13, J14, J26: SMA_VERT_SMD; SMA_vert_SMD; Manufacturer Part Number 0732511352
LD6: LED; LED_0603; Manufacturer Part Number HSMG-C190
R42, R62, R107, R109, R110, R115, R116, R128, R171, R201, R210, R216: 0R_0402; SMD0402; Manufacturer Part Number RC0402JR-070RL
R63: 69K8_0402; SMD0402; Manufacturer Part Number RC0402FR-0769K8L
R65: 5K1_0402; SMD0402; Manufacturer Part Number RC0402FR-075K1L
R66: 10R_0402; SMD0402; Manufacturer Part Number RC0402JR-0710RL
R67: 470R_0402; SMD0402; Manufacturer Part Number ERA-2AED471X
R69: 1K_0402; SMD0402; Manufacturer Part Number RMCF0402FT1K00
R70: 10K_0402; SMD0402; Manufacturer Part Number RC0402JR-0710KL
R74, R79: 51R_0402; SMD0402; Manufacturer Part Number CRCW040251R0FKED; Mouser Digi-Key
R76, R77, R78: 47R_0402; SMD0402; Manufacturer Part Number RC0402FR-0747RL
R80, R104, R105, R108, R199, R215: 0R_0402_NF; SMD0402; Manufacturer Part Number RC0402JR-070RL
R90, R155: 0R_0201_NF; SMD0201; Manufacturer Part Number MCR006YRTJ000
R91, R92, R160, R161: 0R_0201; SMD0201; Manufacturer Part Number MCR006YRTJ000
R112: 33R2_0402; SMD0402; Manufacturer Part Number RC0402FR-0733R2L
R113, R124, R172: 49R9_0402; SMD0402; Manufacturer Part Number RC0402FR-0749R9L
R114: 4K99_0402_NF; SMD0402; Manufacturer Part Number RC0402FR-074K99L
R119, R121, R122, R554: 39R_0402; SMD0402; Manufacturer Part Number RC0402FR-0739RL
R123: NF_49R9_0402; SMD0402; Manufacturer Part Number RC0402FR-0749R9L
T1, T5: TR_TCM1-83X+; TCM1-63AX+; Manufacturer Part Number TCM1-83X+
U1, U2: LMS8001
U18: ADF4002; LFCSP 20; Manufacturer Part Number ADF4002BCPZ-RL7
U21: NB3H83905CMNG; Manufacturer Part Number NB3H83905CMNG
U152: NF_TX-801_40.000_MHz; SMD_TX-801; Manufacturer Part Number TX-801
XO3: NF_RPT5032A; RPT5032A; Manufacturer Part Number RPT5032A
XO4: RTX5032A_40.000_MHZ; SMD_RTX5032A; Manufacturer Part Number RTX5032A

Connections:
+3.3V_CLKGEN_#1: C159.2, FB29.1, R201.1
CLK_TST_#1: C170.2, R119.2
EX1_#1: C101.1, C161.1, R91.1
EX1_#2: C292.1, C294.1, R160.1
EX2_#1: C102.1, C161.2, R92.1
EX2_#2: C292.2, C295.1, R161.1
EX3_#1: R90.1, R91.2, T1.5
EX3_#2: R155.1, R160.2, T5.5
EX4_#1: R90.2, R92.2, T1.4
EX4_#2: R155.2, R161.2, T5.4
EX5_#1: C94.2, T1.3
EX5_#2: C286.2, T5.3
EXTLO_N_#1: C102.2, U1.56 (EXTLO_N)
EXTLO_N_#2: C295.2, U2.56 (EXTLO_N)
EXTLO_P_#1: C101.2, U1.2 (EXTLO_P)
EXTLO_P_#2: C294.2, U2.2 (EXTLO_P)
EXT_LO_CON_#1: C94.1, J3.1 (RF)
EXT_LO_CON_#2: C286.1, J26.1 (RF)
EXT_PLL_SSENn: R78.2
GND: C39.2, C67.2, C68.2, C69.2, C72.2, C73.1, C74.1, C75.2, C76.2, C80.2, C99.2, C159.1, C160.2, C163.2, C164.2, C165.1, C166.1, C168.2, C173.1, C174.1, C175.2, C176.2, C177.1, C178.1, C200.2, C201.2, C305.2, C419.2, C420.1, C421.1, C422.2, C423.2, J3.2 (GND1), J3.3 (GND2), J3.4 (GND3), J3.5 (GND4), J13.2 (GND1), J13.3 (GND2), J13.4 (GND3), J13.5 (GND4), J14.2 (GND1), J14.3 (GND2), J14.4 (GND3), J14.5 (GND4), J26.2 (GND1), J26.3 (GND2), J26.4 (GND3), J26.5 (GND4), LD6.2 (K), R65.2, R70.1, R74.1, R79.2, R104.1, R113.2, R114.2, R123.2, R124.2, R172.2, T1.1, T1.2, T1.6, T5.1, T5.2, T5.6, U18.1 (CPGND), U18.2 (AGND), U18.3 (AGND), U18.9 (DGND), U18.10 (DGND), U18.21 (AGND), U21.1 (GND), U21.2 (GND), U21.6 (GND), U21.7 (GND), U21.11 (GND), U21.12 (GND), U21.20 (ENABLE2), U21.21 (GND), U152.4 (GND), U152.5 (GND), U152.10 (GND), XO3.2 (GND), XO4.4 (GND)
HFPLL_CLK_#1: C172.1, R122.1
HFPLL_CLK_#2: C313.1, R554.1
HFPLL_CLK_LMS8_#1: C171.2, U1.53 (PLLCLK)
HFPLL_CLK_LMS8_#2: C303.2, U2.53 (PLLCLK)
J14_SMA_vert_#1: C170.1, J14.1 (RF), R123.1
unnamed: C39.1, U152.7 (CAP)
unnamed: C41.1, U152.6 (OUTPUT)
unnamed: C41.2, R215.1
unnamed: C70.1, C72.1, R63.1, U18.20 (CP)
unnamed: C70.2, R65.1
unnamed: C73.2, R66.2, U18.18 (Vp)
unnamed: C74.2, FB22.2, R66.1, R69.1, R201.2, U18.16 (DVdd), U18.17 (DVdd)
unnamed: C75.1, FB22.1, U18.6 (AVdd), U18.7 (AVdd)
unnamed: C76.1, R76.1, U18.12 (CLK)
unnamed: C79.1, C84.2, R74.2
unnamed: C79.2, U18.8 (REFin)
unnamed: C80.1, U18.4 (RFinB)
unnamed: C85.1, C89.2, R79.1
unnamed: C85.2, U18.5 (RFinA)
unnamed: C99.1, XO4.7 (VC)
unnamed: C100.1, R112.2
unnamed: C162.1, U21.18 (XTAL_IN/CLK)
unnamed: C162.2, R112.1, R113.1
unnamed: C163.1, C165.2, C173.2, R62.1, R128.2, XO3.5 (VCC)
unnamed: C67.1, C171.1, R42.1
unnamed: C172.2, R42.2, R124.1
unnamed: C68.1, C177.2, C178.2, R109.1, XO4.9 (VCC)
unnamed: C303.1, C305.1, R171.1
unnamed: C313.2, R171.2, R172.1
unnamed: C419.1, C420.2, C421.2, R210.2, R216.1, U152.9 (VCC)
unnamed: LD6.1 (A), R67.2
unnamed: R62.2, XO3.6 (EN)
unnamed: R67.1, U18.15 (MUXOUT)
unnamed: R69.2, U18.11 (CE)
unnamed: R70.2, U18.19 (Rset)
unnamed: R77.1, U18.13 (DATA)
unnamed: R78.1, U18.14 (LE)
unnamed: R105.2, XO3.1 (Vc)
unnamed: R107.2, XO4.1 (V_CNT)
unnamed: R108.1, XO3.4 (OUT)
unnamed: R110.1, XO4.6 (OUTPUT)
unnamed: R114.1, U21.17 (ENABLE1)
unnamed: R119.1, U21.3 (BCLK0)
unnamed: R121.2, U21.5 (BCLK1)
unnamed: R122.2, U21.10 (BCLK3)
unnamed: R199.1, U152.1 (V_Ctrl)
unnamed: R210.1, U152.8 (EN)
unnamed: R554.2, U21.8 (BCLK2)
REF_ADF_#1: C89.1, R121.1
SCLK_2: R76.2
SDIO_2: R77.2
SMA_IN1_#1: C84.1, J13.1 (RF), R80.2
VCXO_OUT_#1: C100.2, R80.1, R108.2, R110.2, R215.2
VCXO_PWR_FILTER_#1: C160.1, C200.1, C201.1, C422.1, C423.1, FB29.2, R109.2, R115.2, R116.2, R128.1, R216.2
VDDO_CKBUF_#1: C164.1, C166.2, C168.1, R115.1, U21.4 (Vddo), U21.14 (Vddo)
VDD_CKBUF_#1: C174.2, C175.1, C176.1, R116.1, U21.9 (Vdd)
V_CTRL_#1: C69.1, R63.2, R104.2, R105.1, R107.1, R199.2

Notes on the sheet:
NEAR TO LMS8
TL_50_Ohm
LMS8001 #1
LMS8001 #2
33R2 or 0R
C94
R90
R91
R92
C161
C101
C102
C171
R42
C67
R124
C172
R128
C173
C165
C163
R62
XO3
R108
XO4
R105
R104
R107
C99
R110
C68
C177
C178
C100
R112
R109
C201
C200
R113
C162
R114
C174
C175
C176
C166
C168
C164
R116
R115
C159
C160
FB29
R119
R121
R122
C170
R123
R201
R66
R69
C74
C73
C75
R74
C79
C84
C85
C89
R79
R76
R77
R78
C76
LD6
R70
R67
C72
C70
C69
R63
Deleted
R80
C80
OLD Racon
NEW Racon
