myriadrf/LimeRFE-8001P/hardware/1v1/KiCAD/LMS8001_RF.sch

## KiCad design hardware/1v1/KiCAD/LMS8001_RF.sch (2023-10-04)

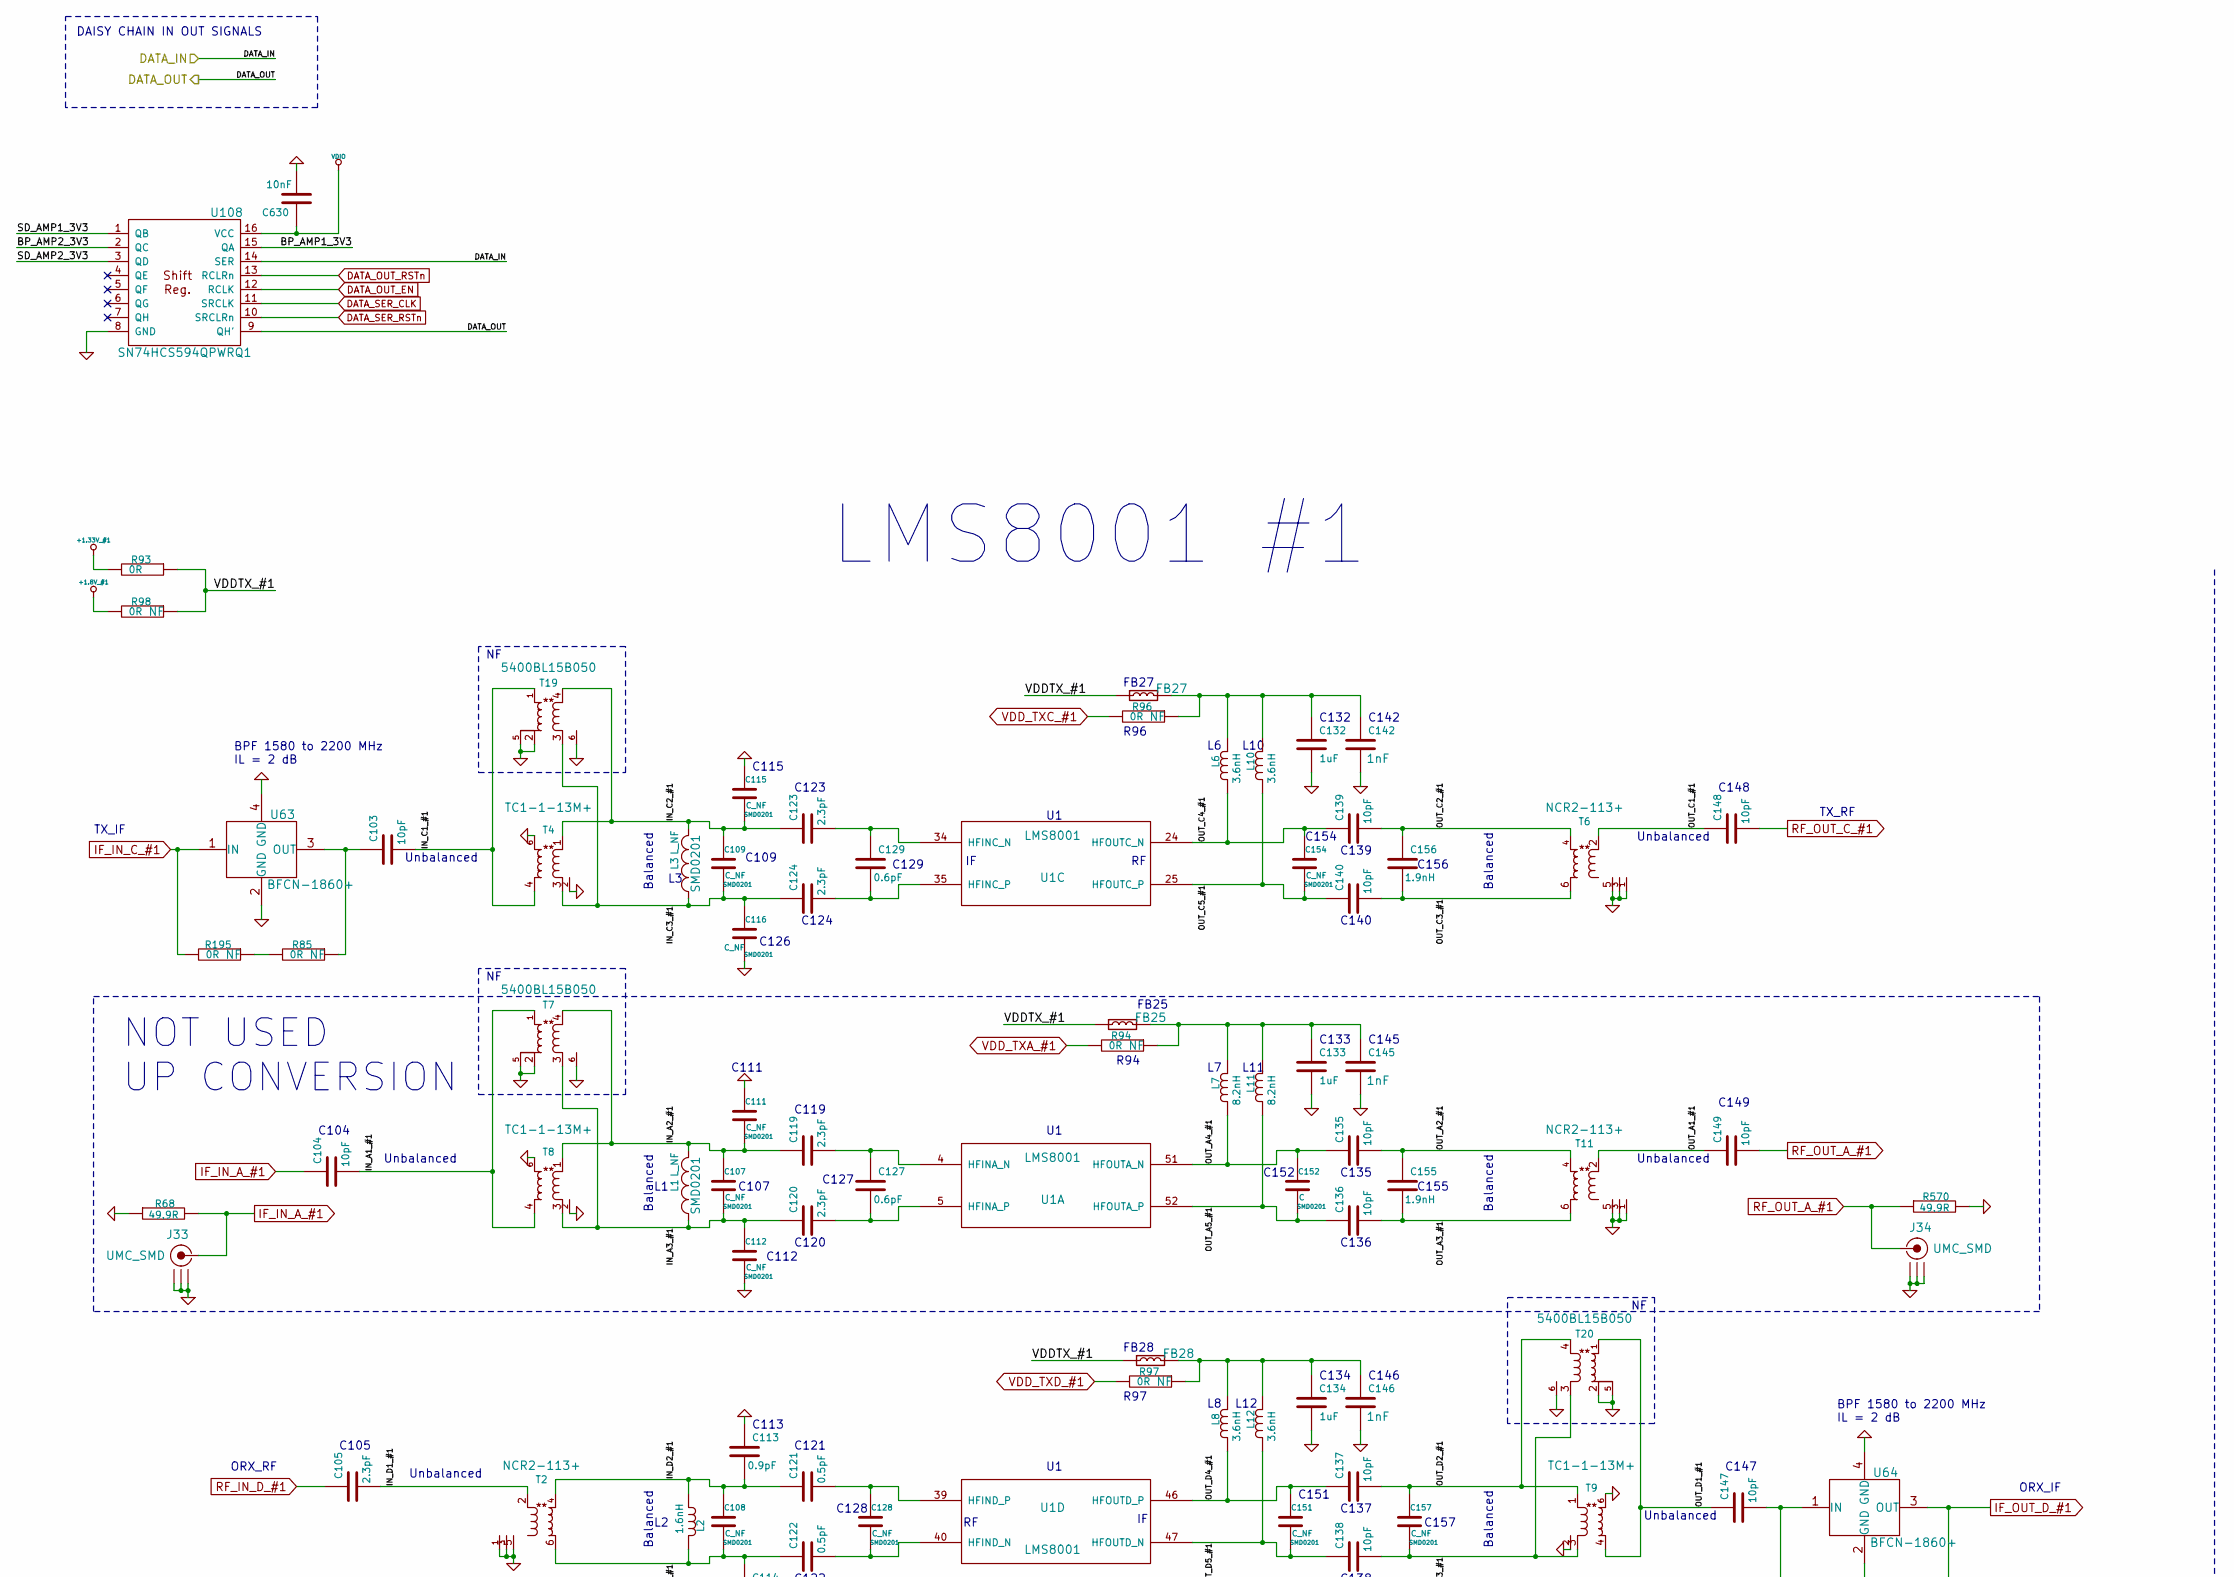
[picture p97: schematic LMS8001_RF.sch, part in row 1, column 1]

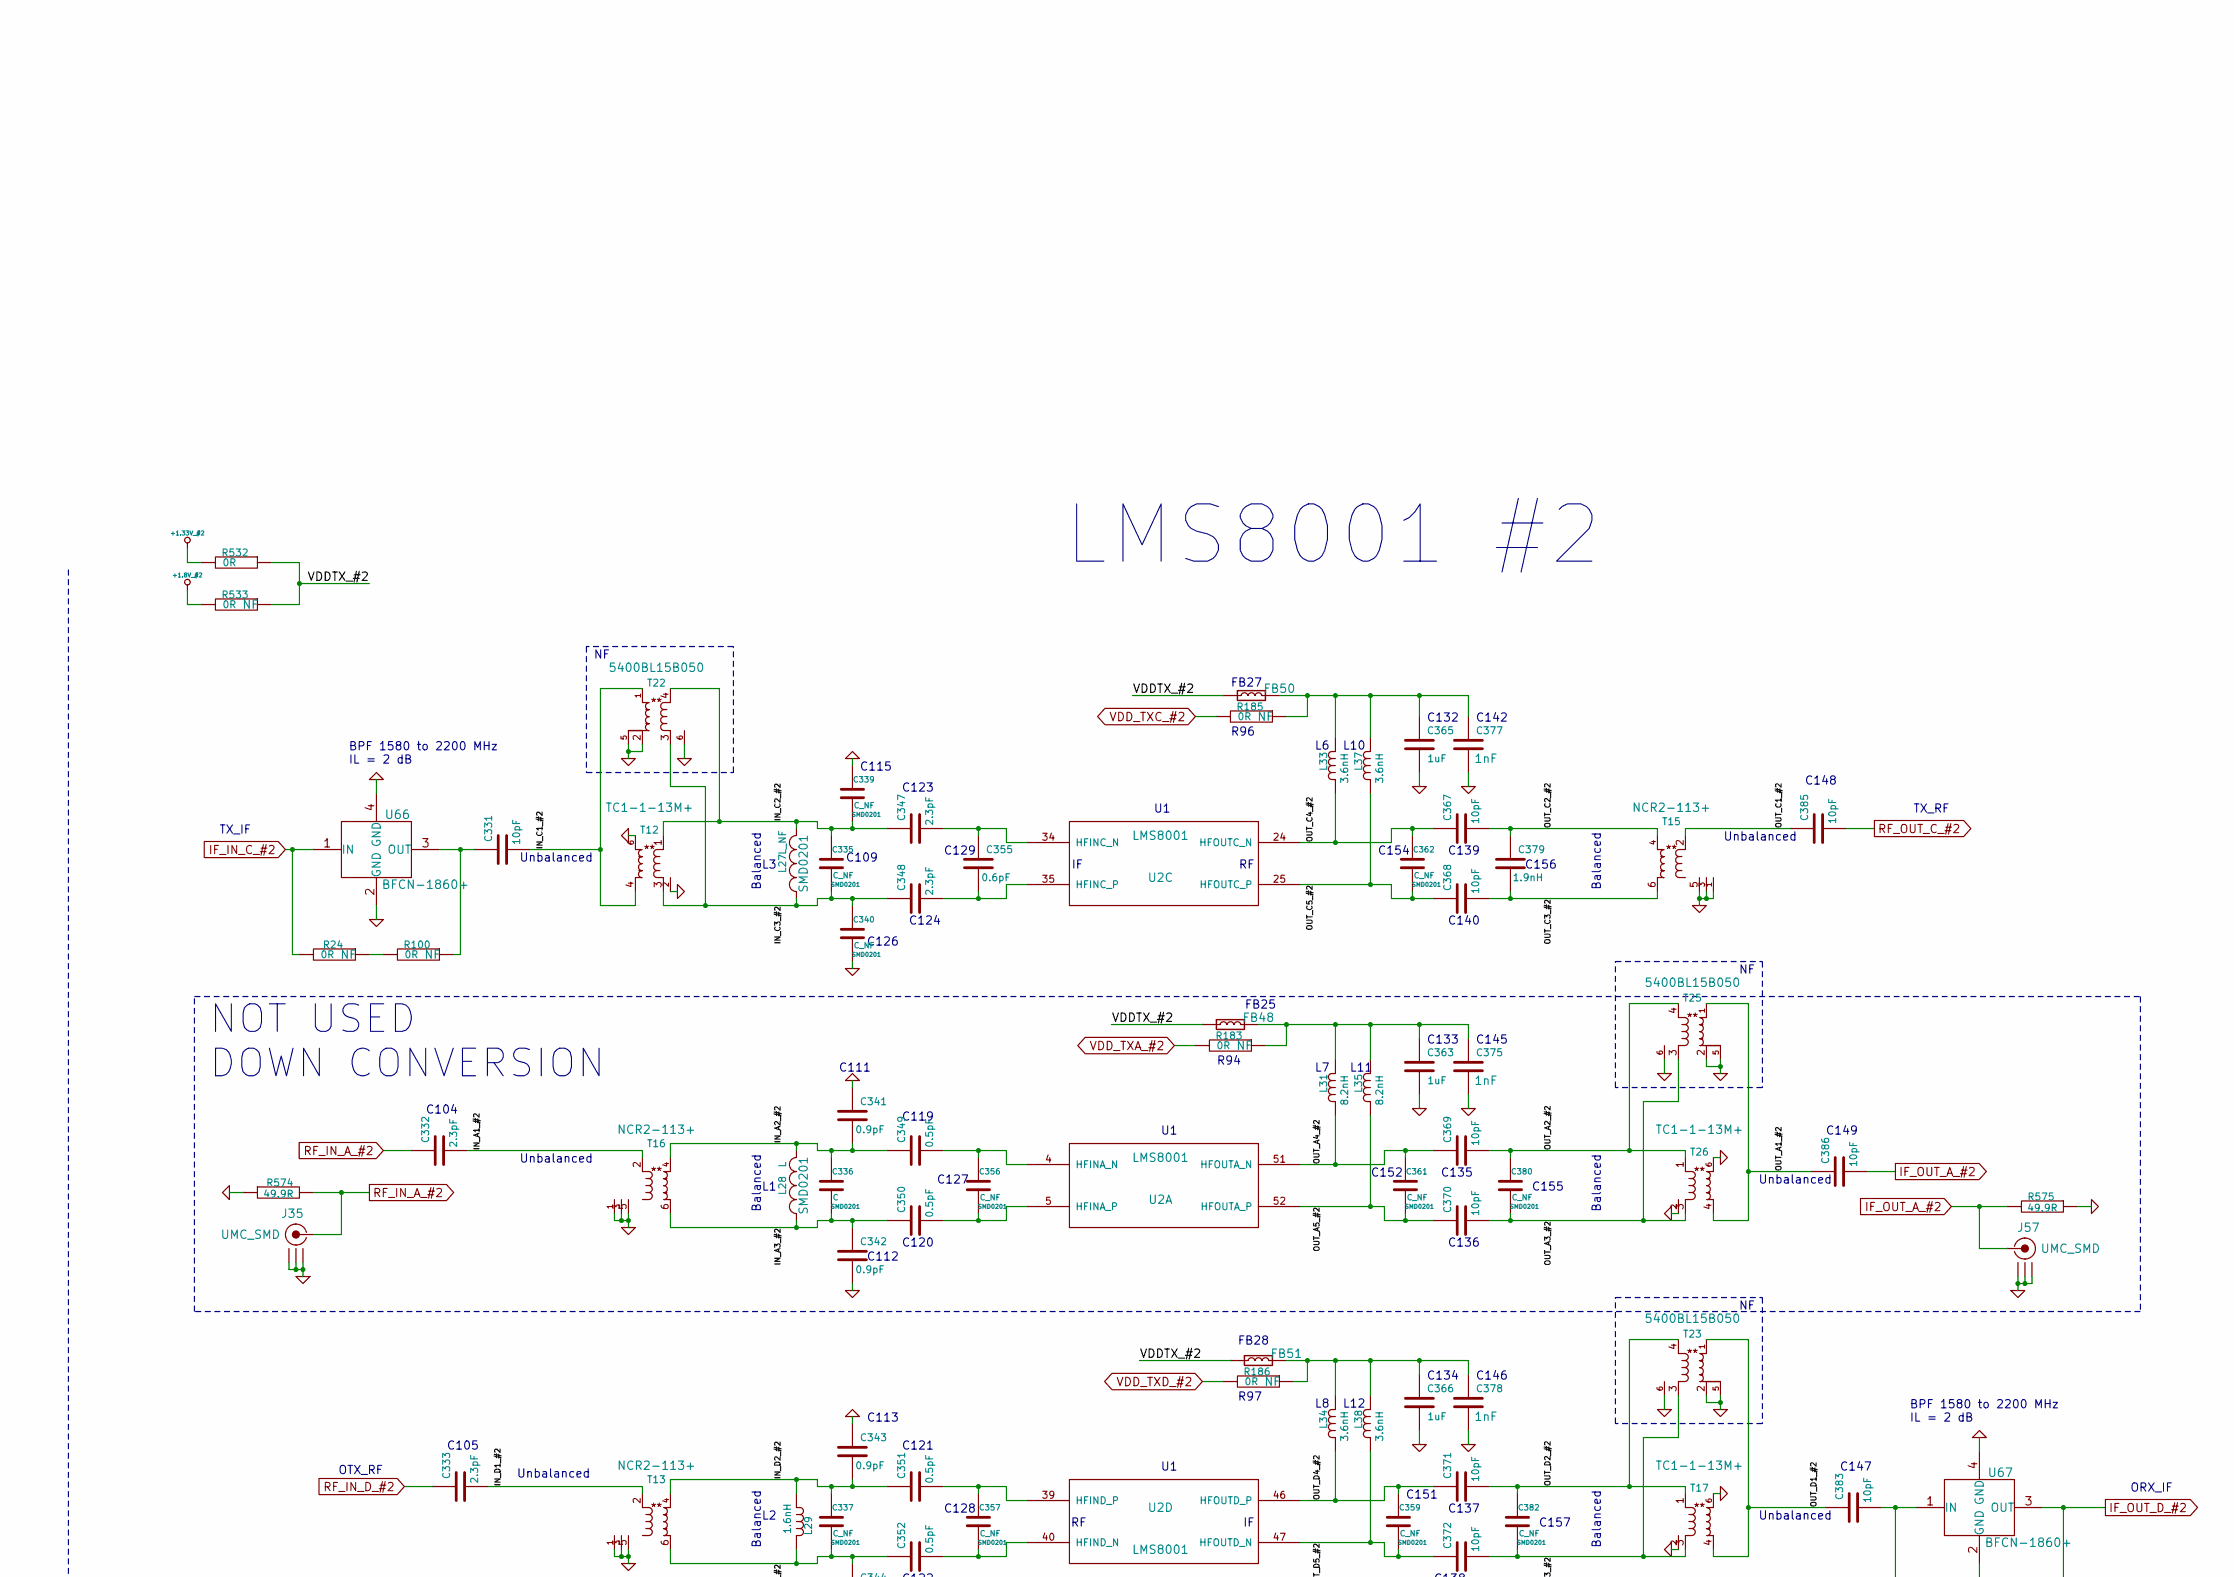
[picture p98: schematic LMS8001_RF.sch, part in row 1, column 2]

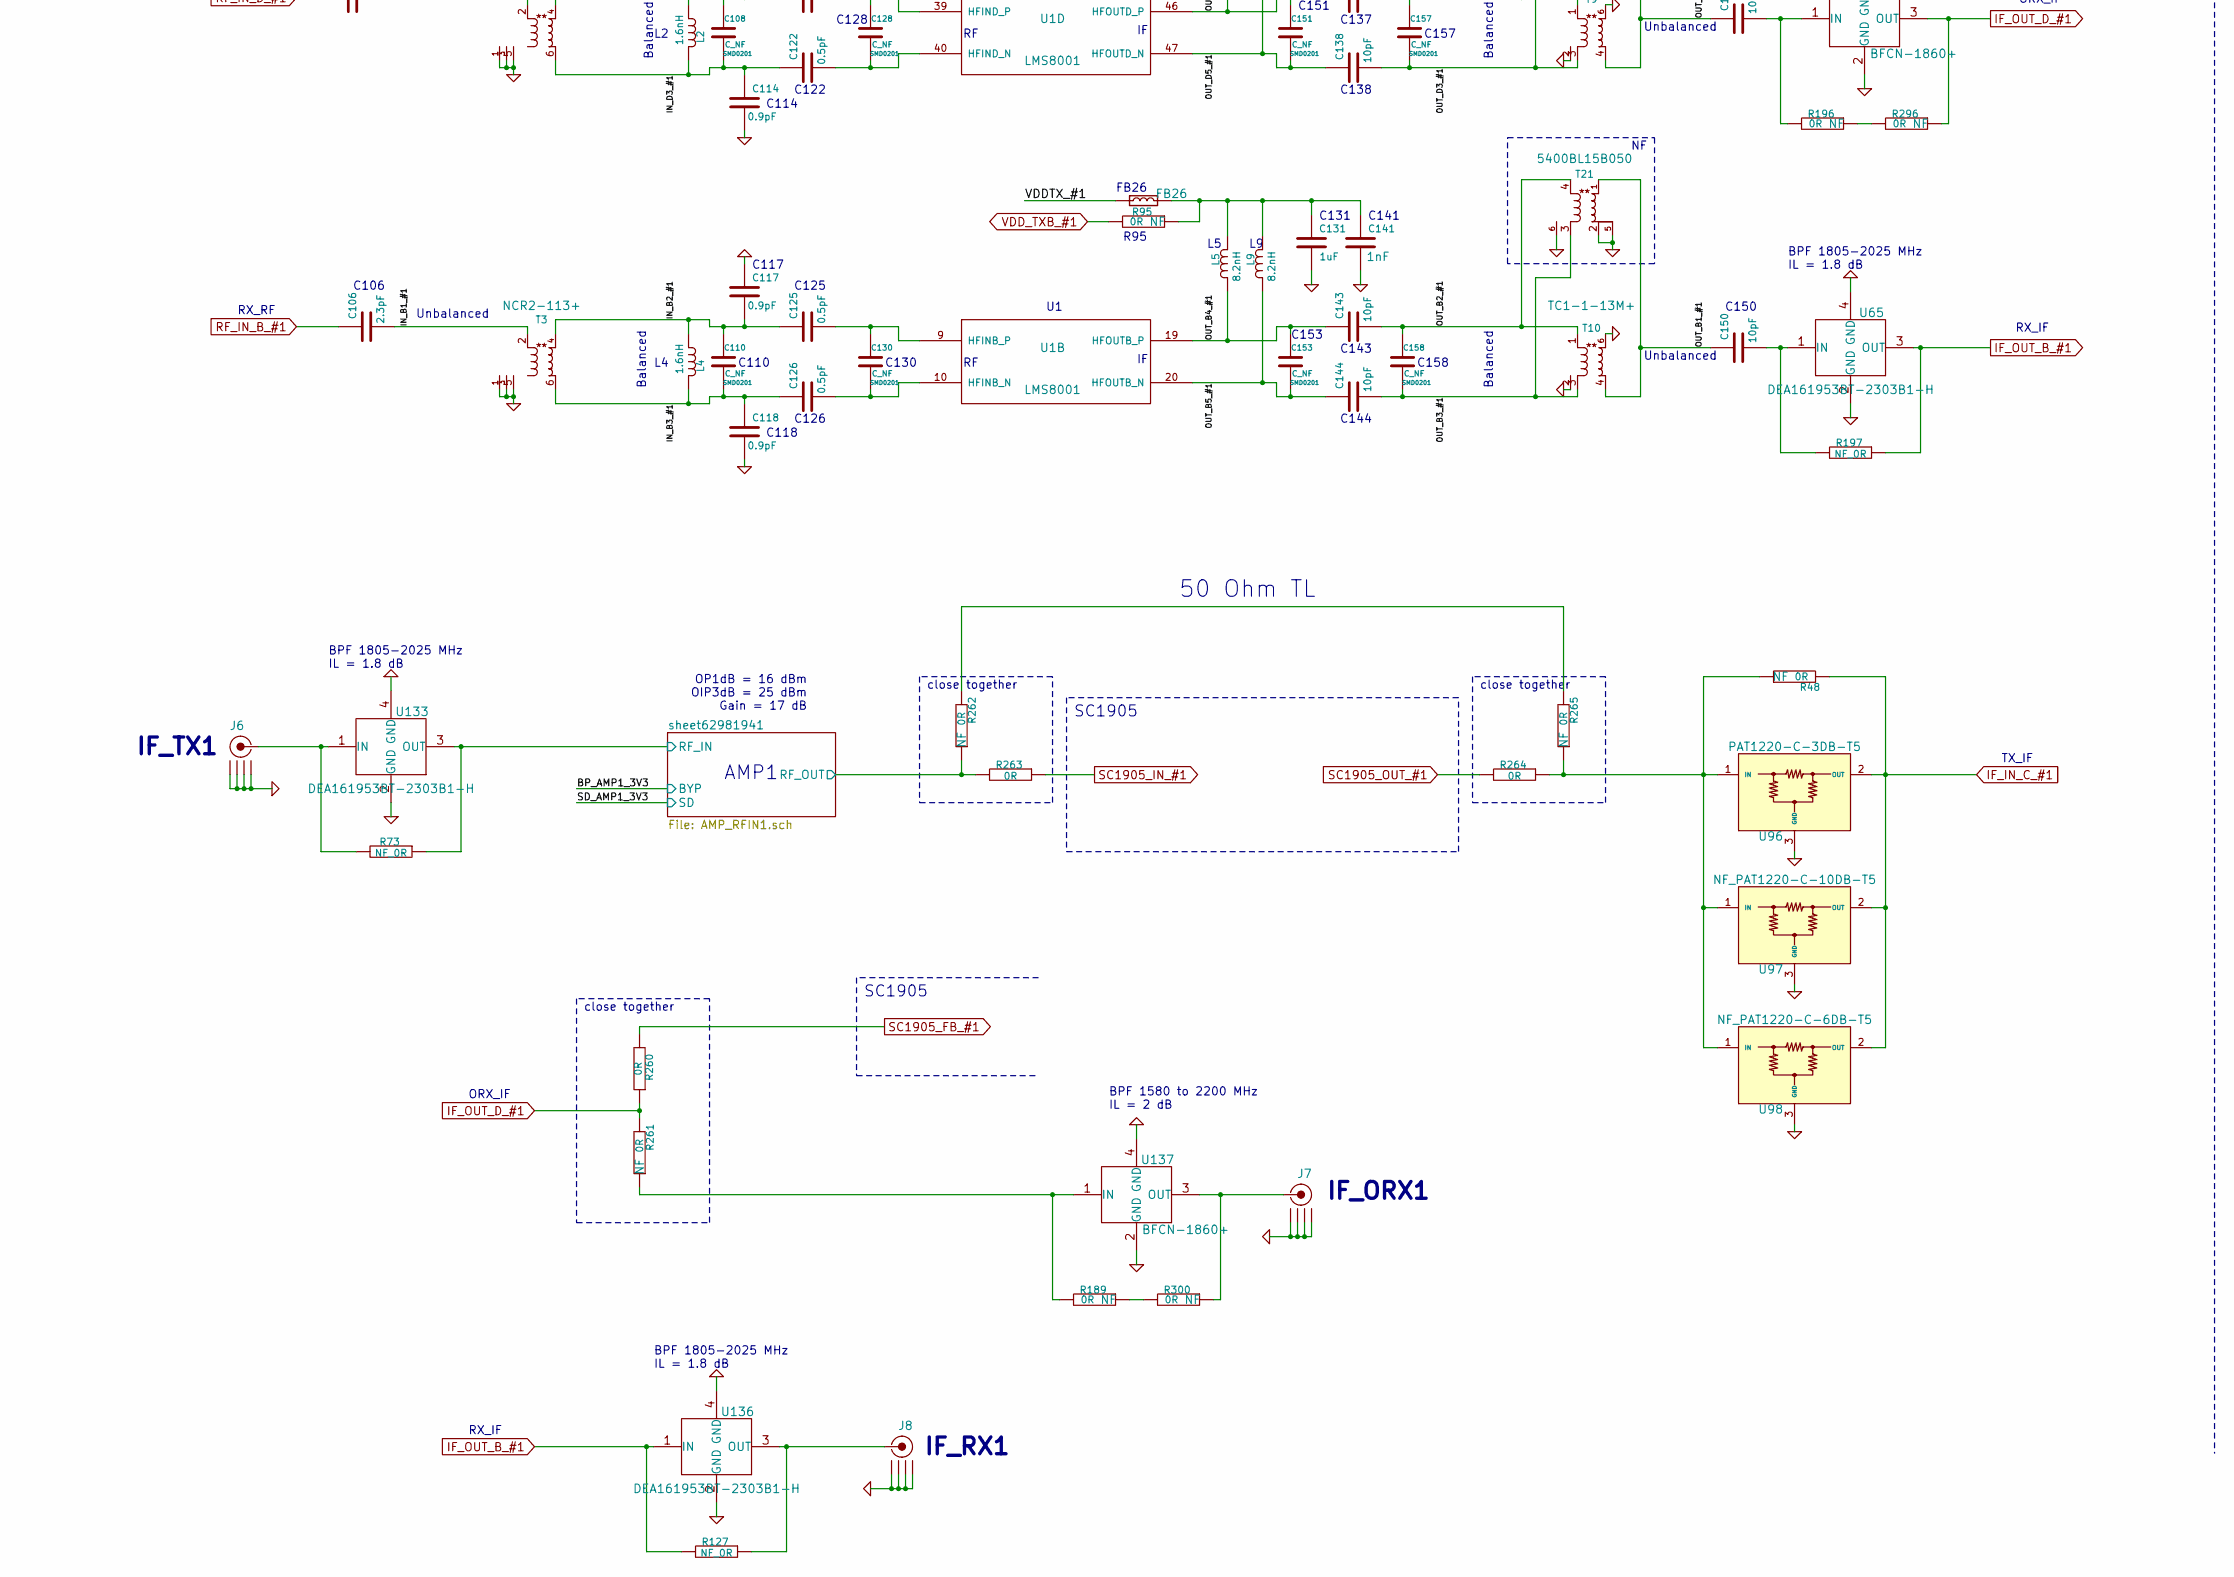
[picture p99: schematic LMS8001_RF.sch, part in row 2, column 1]

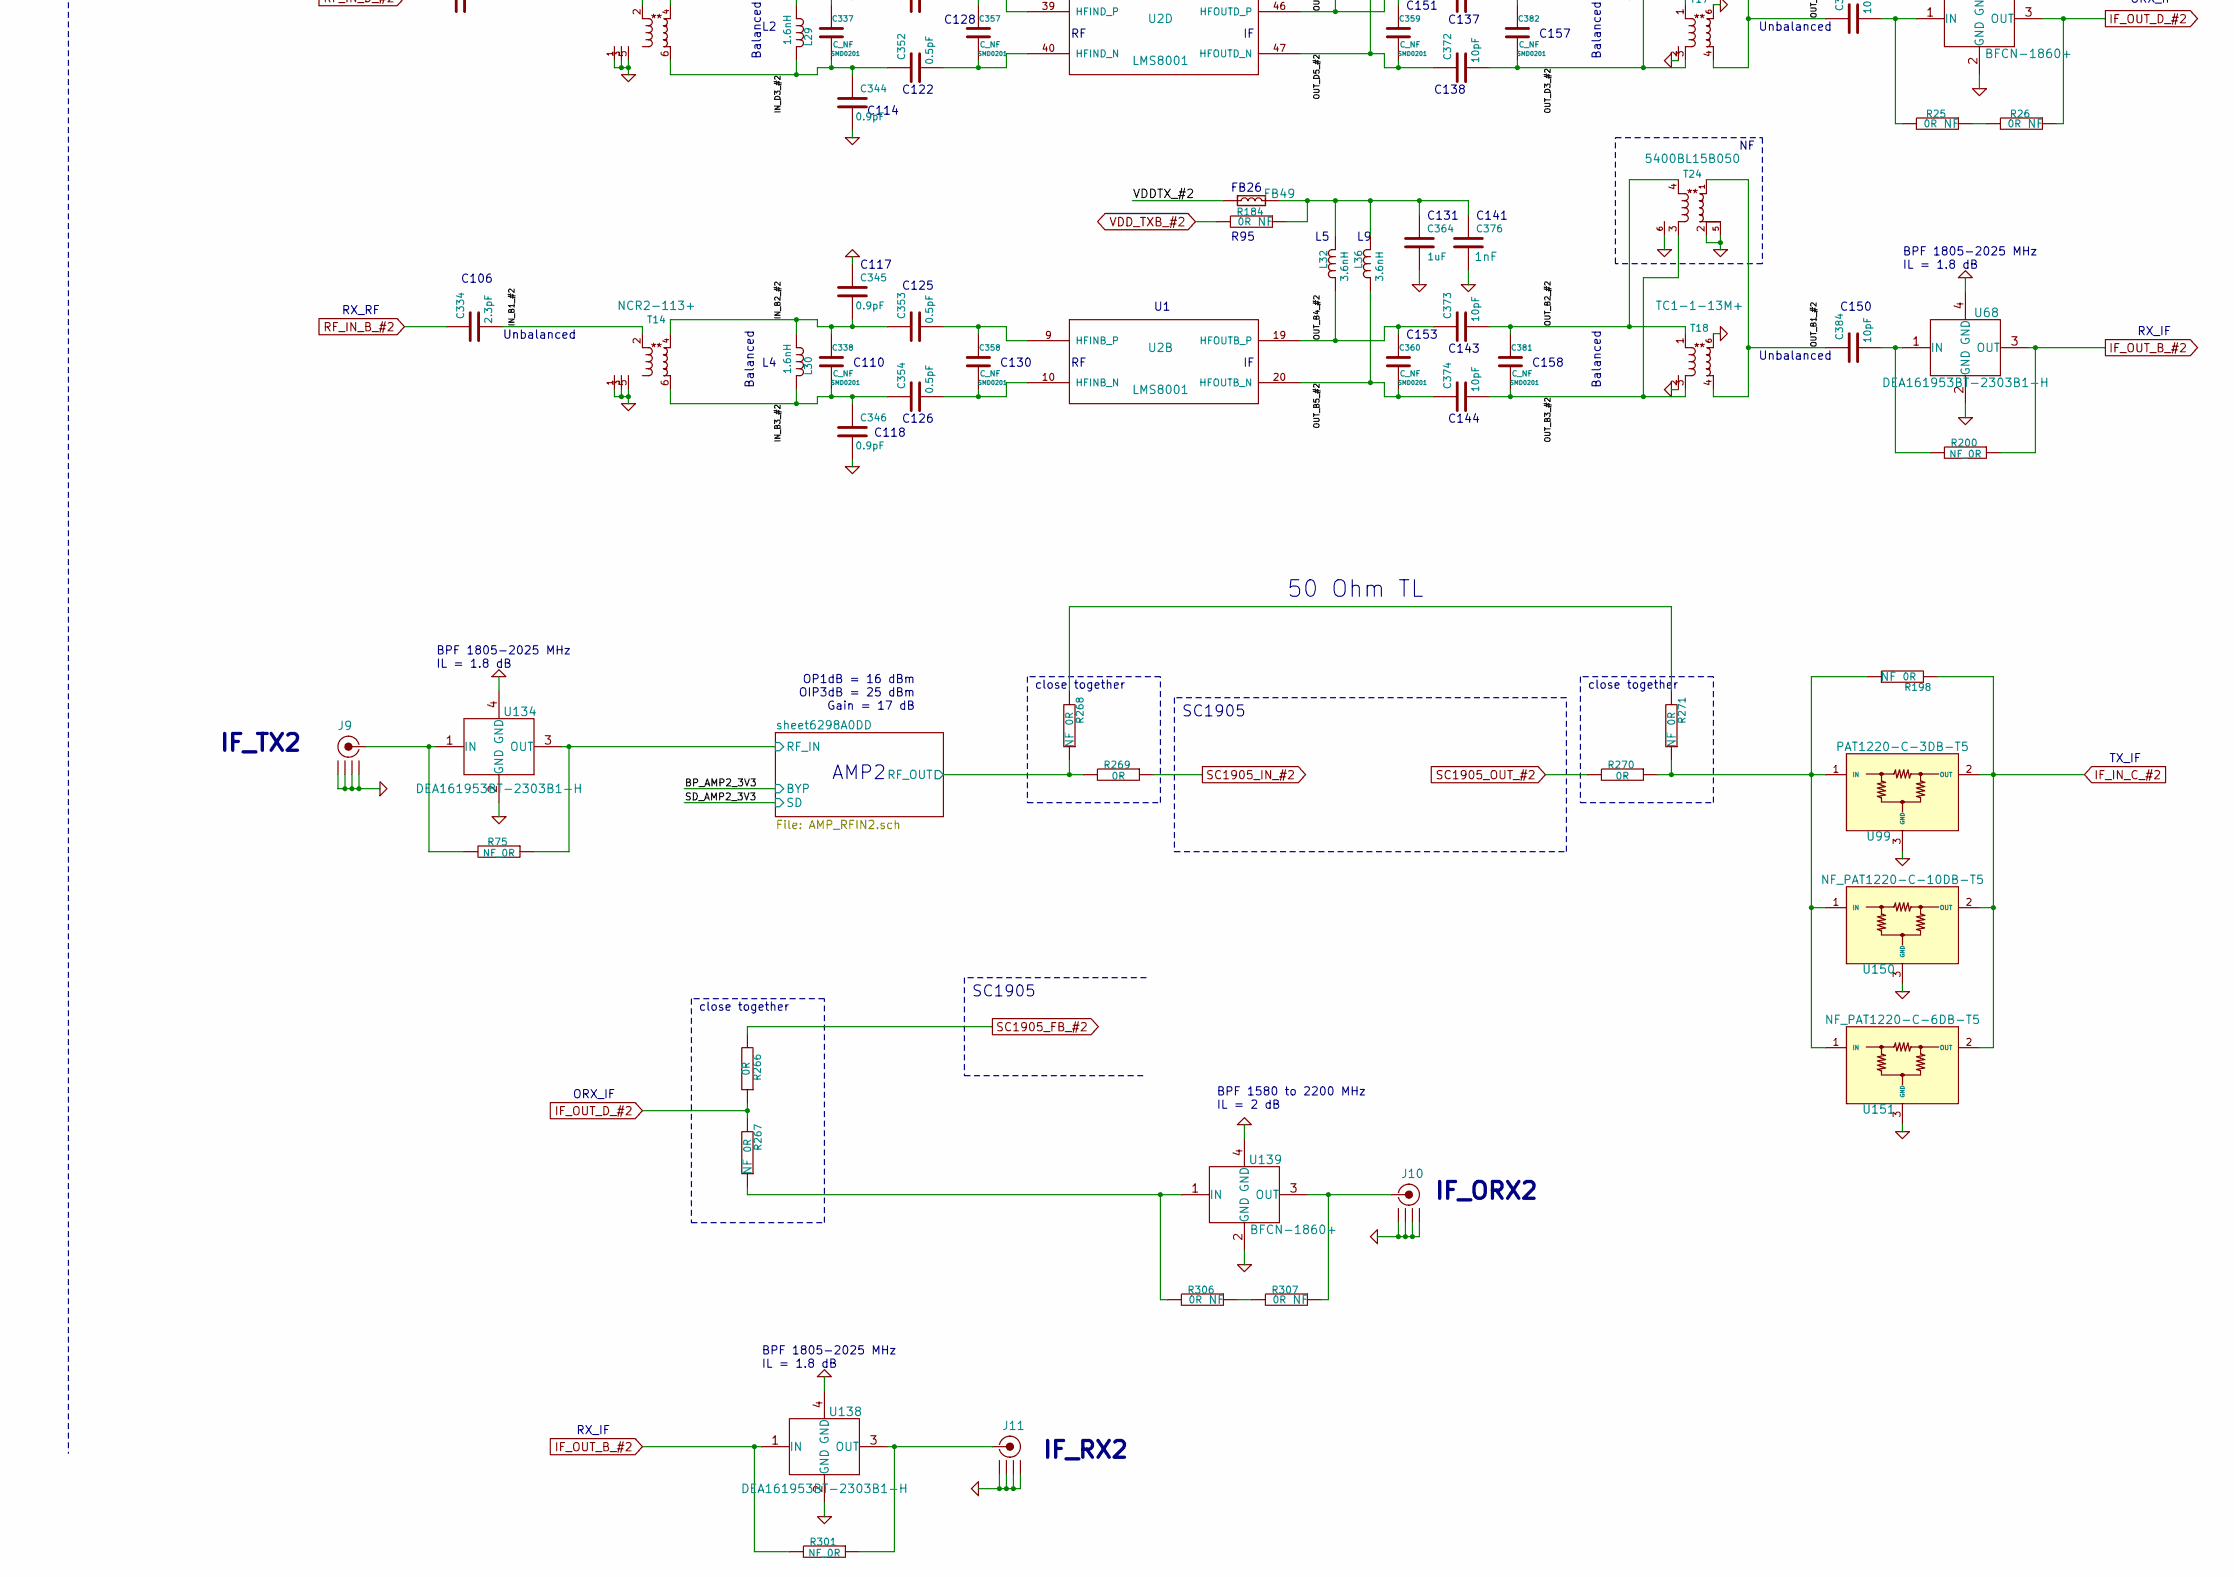
[picture p100: schematic LMS8001_RF.sch, part in row 2, column 2]

Parts:
C103, C104, C135, C136, C137, C138, C139, C140, C143, C144, C147, C148, C149, C150, C331, C367, C368, C369, C370, C371, C372, C373, C374, C383, C384, C385, C386: 10pF_0201_GJM0335C1E100JB01D; SMD0201; Manufacturer Part Number GJM0335C1E100JB01D
C105, C106, C119, C120, C123, C124, C332, C333, C334, C347, C348: 2.3pF_0201_GJM0335C1E2R3BB01D; SMD0201; Manufacturer Part Number GJM0335C1E2R3BB01D
C107, C108, C109, C110, C111, C112, C115, C116, C128, C130, C151, C153, C154, C157, C158, C335, C337, C338, C339, C340, C356, C357, C358, C359, C360, C361, C362, C380, C381, C382: C_NF; SMD0201
C113, C114, C117, C118, C341, C342, C343, C344, C345, C346: 0.9pF_0201_GJM0335C1ER90BB01D; SMD0201; Manufacturer Part Number GJM0335C1ER90BB01D
C121, C122, C125, C126, C349, C350, C351, C352, C353, C354: 0.5pF_0201_GJM0335C1ER50BB01D; SMD0201; Manufacturer Part Number GJM0335C1ER50BB01D
C127, C129, C355: 0.6pF_0201_GJM0335C1ER60BB01D; SMD0201; Manufacturer Part Number GJM0335C1ER60BB01D
C131, C132, C133, C134, C363, C364, C365, C366: 1UF_0201_TDK_X5R; SMD0201; Manufacturer Part Number C0603X5R0J105M030BC
C141, C142, C145, C146, C375, C376, C377, C378: 1NF_0201; SMD0201; Manufacturer Part Number C0603X7R1E102K030BA
C152, C336: C; SMD0201
C155, C156, C379: 1.9nH_0201_LQP03TN1N9B02D; SMD0201; Manufacturer Part Number LQP03TN1N9B02D
C630: 10nF_0402; SMD0402; Manufacturer Part Number CC0402ZRY5V7BB103
FB25, FB26, FB27, FB28, FB48, FB49, FB50, FB51: FB_0201; SMD0201; Manufacturer Part Number BK0603TS601-T
J6, J7, J8, J9, J10, J11: SMA_H_142-0711-811; Manufacturer Part Number 142-0711-811
J33, J34, J35, J57: UMC_SMD; Manufacturer Part Number 0734120110
L1, L3, L27: L_NF; SMD0201
L2, L4, L29, L30: 1.6nH_0201_LQP03TN1N6B02D; SMD0201; Manufacturer Part Number LQP03TN1N6B02D
L5, L7, L9, L11: 8.2nH_0402_LQW15AN8N2G00D; IND_0402; Manufacturer Part Number LQW15AN8N2G00D
L6, L8, L10, L12, L32, L33, L34, L36, L37, L38: 3.6nH_0402_LQW15AN3N6C10D; IND_0402; Manufacturer Part Number LQW15AN3N6C10D
L28: L; SMD0201
L31, L35: 8.2NH_0402; IND_0402; Manufacturer Part Number 0402HP-8N2XJLU
R24, R25, R26, R85, R94, R95, R96, R97, R100, R183, R184, R185, R186, R189, R195, R196, R296, R300, R306, R307: 0R_0201_NF; SMD0201; Manufacturer Part Number MCR006YRTJ000
R48, R198, R261, R262, R265, R267, R268, R271: 0R_0402_NF; SMD0402; Manufacturer Part Number RC0402JR-070RL
R68, R570, R574, R575: 49.9R_0402_ERJ-U02F49R9X; SMD0402; Manufacturer Part Number ERJ-U02F49R9X
R73, R75, R127, R197, R200, R301: NF_0R_0603_RCS06030000Z0EA; SMD0603; Manufacturer Part Number RCS06030000Z0EA
R93, R98, R532, R533: 0R_0805; SMD0805; Manufacturer Part Number RC0805JR-070RL
R260, R263, R264, R266, R269, R270: 0R_0402; SMD0402
T2, T3, T6, T11, T13, T14, T15, T16: NCR2-113+; Manufacturer Part Number NCR2-113+
T4, T8, T9, T10, T12, T17, T18, T26: TR_TC1-1-13M+; TC1-1-13M+; Manufacturer Part Number TC1-1-13M+
T7, T19, T20, T21, T22, T23, T24, T25: TR_5400BL15B050; 5400BL15B050; Manufacturer Part Number 5400BL15B050
U1, U2: LMS8001
U63, U64, U66, U67, U137, U139: BFCN-1860+; Manufacturer Part Number BFCN-1860+
U65, U68, U133, U134, U136, U138: DEA161953BT-2303B1-H; Manufacturer Part Number DEA161953BT-2303B1-H
U96, U99: PAT1220-C-3DB-T5; Manufacturer Part Number PAT1220-C-3DB-T5
U97, U150: NF_PAT1220-C-10DB-T5; PAT1220-C-10DB-T5; Manufacturer Part Number PAT1220-C-10DB-T5
U98, U151: NF_PAT1220-C-6DB-T5; PAT1220-C-6DB-T5; Manufacturer Part Number PAT1220-C-6DB-T5
U108: SN74HCS594QPWRQ1; Manufacturer Part Number SN74HCS594QPWRQ1

Connections:
+1.8V_#1: R98.2
+1.8V_#2: R533.2
+1.33V_#1: R93.2
+1.33V_#2: R532.2
BP_AMP1_3V3: U108.15 (QA)
BP_AMP2_3V3: U108.2 (QC)
DATA_IN: U108.14 (SER)
DATA_OUT: U108.9 (QH')
DATA_OUT_EN: U108.12 (RCLK)
DATA_OUT_RSTn: U108.13 (RCLRn)
DATA_SER_CLK: U108.11 (SRCLK)
DATA_SER_RSTn: U108.10 (SRCLRn)
GND: C111.1, C112.2, C113.1, C114.2, C115.1, C116.2, C117.1, C118.2, C131.2, C132.2, C133.2, C134.2, C141.2, C142.2, C145.2, C146.2, C339.1, C340.2, C341.1, C342.2, C343.1, C344.2, C345.1, C346.2, C363.2, C364.2, C365.2, C366.2, C375.2, C376.2, C377.2, C378.2, C630.2, J6.2 (GND1), J6.3 (GND2), J6.4 (GND3), J6.5 (GND4), J7.2 (GND1), J7.3 (GND2), J7.4 (GND3), J7.5 (GND4), J8.2 (GND1), J8.3 (GND2), J8.4 (GND3), J8.5 (GND4), J9.2 (GND1), J9.3 (GND2), J9.4 (GND3), J9.5 (GND4), J10.2 (GND1), J10.3 (GND2), J10.4 (GND3), J10.5 (GND4), J11.2 (GND1), J11.3 (GND2), J11.4 (GND3), J11.5 (GND4), J33.2 (GND1), J33.3 (GND2), J33.4 (GND3), J34.2 (GND1), J34.3 (GND2), J34.4 (GND3), J35.2 (GND1), J35.3 (GND2), J35.4 (GND3), J57.2 (GND1), J57.3 (GND2), J57.4 (GND3), R68.1, R570.2, R574.1, R575.1, T2.1 (GND), T2.3 (GND), T2.5 (GND), T3.1 (GND), T3.3 (GND), T3.5 (GND), T4.2, T4.6, T6.1 (GND), T6.3 (GND), T6.5 (GND), T7.2, T7.5 (GND), T7.6 (NC), T8.2, T8.6, T9.2, T9.6, T10.2, T10.6, T11.1 (GND), T11.3 (GND), T11.5 (GND), T12.2, T12.6, T13.1 (GND), T13.3 (GND), T13.5 (GND), T14.1 (GND), T14.3 (GND), T14.5 (GND), T15.1 (GND), T15.3 (GND), T15.5 (GND), T16.1 (GND), T16.3 (GND), T16.5 (GND), T17.2, T17.6, T18.2, T18.6, T19.2, T19.5 (GND), T19.6 (NC), T20.2, T20.5 (GND), T20.6 (NC), T21.2, T21.5 (GND), T21.6 (NC), T22.2, T22.5 (GND), T22.6 (NC), T23.2, T23.5 (GND), T23.6 (NC), T24.2, T24.5 (GND), T24.6 (NC), T25.2, T25.5 (GND), T25.6 (NC), T26.2, T26.6, U63.2 (GND), U63.4 (GND), U64.2 (GND), U64.4 (GND), U65.2 (GND), U65.4 (GND), U66.2 (GND), U66.4 (GND), U67.2 (GND), U67.4 (GND), U68.2 (GND), U68.4 (GND), U96.3 (GND), U97.3 (GND), U98.3 (GND), U99.3 (GND), U108.8 (GND), U133.2 (GND), U133.4 (GND), U134.2 (GND), U134.4 (GND), U136.2 (GND), U136.4 (GND), U137.2 (GND), U137.4 (GND), U138.2 (GND), U138.4 (GND), U139.2 (GND), U139.4 (GND), U150.3 (GND), U151.3 (GND)
IF_IN_A_#1: C104.1, J33.1 (RF), R68.2
IF_IN_C_#1: R48.2, R195.2, U63.1 (IN), U96.2 (OUT), U97.2 (OUT), U98.2 (OUT)
IF_IN_C_#2: R24.2, R198.2, U66.1 (IN), U99.2 (OUT), U150.2 (OUT), U151.2 (OUT)
IF_OUT_A_#2: C386.2, J57.1 (RF), R575.2
IF_OUT_B_#1: R127.2, R197.1, U65.3 (OUT), U136.1 (IN)
IF_OUT_B_#2: R200.1, R301.2, U68.3 (OUT), U138.1 (IN)
IF_OUT_D_#1: R260.1, R261.2, R296.1, U64.3 (OUT)
IF_OUT_D_#2: R26.1, R266.1, R267.2, U67.3 (OUT)
IN_A1_#1: C104.2, T7.1, T8.4
IN_A1_#2: C332.2, T16.2
IN_A2_#1: C107.1, C111.2, C119.1, L1.2, T7.4, T8.1
IN_A2_#2: C336.1, C341.2, C349.1, L28.2, T16.4
IN_A3_#1: C107.2, C112.1, C120.1, L1.1, T7.3, T8.3
IN_A3_#2: C336.2, C342.1, C350.1, L28.1, T16.6
IN_B1_#1: C106.2, T3.2
IN_B1_#2: C334.2, T14.2
IN_B2_#1: C110.1, C117.2, C125.1, L4.2, T3.4
IN_B2_#2: C338.1, C345.2, C353.1, L30.2, T14.4
IN_B3_#1: C110.2, C118.1, C126.1, L4.1, T3.6
IN_B3_#2: C338.2, C346.1, C354.1, L30.1, T14.6
IN_C1_#1: C103.2, T4.4, T19.1
IN_C1_#2: C331.2, T12.4, T22.1
IN_C2_#1: C109.1, C115.2, C123.1, L3.2, T4.1, T19.4
IN_C2_#2: C335.1, C339.2, C347.1, L27.2, T12.1, T22.4
IN_C3_#1: C109.2, C116.1, C124.1, L3.1, T4.3, T19.3
IN_C3_#2: C335.2, C340.1, C348.1, L27.1, T12.3, T22.3
IN_D1_#1: C105.2, T2.2
IN_D1_#2: C333.2, T13.2
IN_D2_#1: C108.1, C113.2, C121.1, L2.2, T2.4
IN_D2_#2: C337.1, C343.2, C351.1, L29.2, T13.4
IN_D3_#1: C108.2, C114.1, C122.1, L2.1, T2.6
IN_D3_#2: C337.2, C344.1, C352.1, L29.1, T13.6
unnamed: C103.1, R85.1, U63.3 (OUT)
unnamed: C119.2, C127.1, U1.4 (HFINA_N)
unnamed: C120.2, C127.2, U1.5 (HFINA_P)
unnamed: C121.2, C128.1, U1.39 (HFIND_P)
unnamed: C122.2, C128.2, U1.40 (HFIND_N)
unnamed: C123.2, C129.1, U1.34 (HFINC_N)
unnamed: C124.2, C129.2, U1.35 (HFINC_P)
unnamed: C125.2, C130.1, U1.9 (HFINB_P)
unnamed: C126.2, C130.2, U1.10 (HFINB_N)
unnamed: C131.1, C141.1, FB26.2, L5.1, L9.1, R95.1
unnamed: C132.1, C142.1, FB27.2, L6.1, L10.1, R96.1
unnamed: C133.1, C145.1, FB25.2, L7.1, L11.1, R94.1
unnamed: C134.1, C146.1, FB28.2, L8.1, L12.1, R97.1
unnamed: C147.2, R196.2, U64.1 (IN)
unnamed: C150.2, R197.2, U65.1 (IN)
unnamed: C331.1, R100.1, U66.3 (OUT)
unnamed: C347.2, C355.1, U2.34 (HFINC_N)
unnamed: C348.2, C355.2, U2.35 (HFINC_P)
unnamed: C349.2, C356.1, U2.4 (HFINA_N)
unnamed: C350.2, C356.2, U2.5 (HFINA_P)
unnamed: C351.2, C357.1, U2.39 (HFIND_P)
unnamed: C352.2, C357.2, U2.40 (HFIND_N)
unnamed: C353.2, C358.1, U2.9 (HFINB_P)
unnamed: C354.2, C358.2, U2.10 (HFINB_N)
unnamed: C363.1, C375.1, FB48.2, L31.1, L35.1, R183.1
unnamed: C364.1, C376.1, FB49.2, L32.1, L36.1, R184.1
unnamed: C365.1, C377.1, FB50.2, L33.1, L37.1, R185.1
unnamed: C366.1, C378.1, FB51.2, L34.1, L38.1, R186.1
unnamed: C383.2, R25.2, U67.1 (IN)
unnamed: C384.2, R200.2, U68.1 (IN)
unnamed: J6.1 (RF), R73.2, U133.1 (IN)
unnamed: J7.1 (RF), R300.1, U137.3 (OUT)
unnamed: J8.1 (RF), R127.1, U136.3 (OUT)
unnamed: J9.1 (RF), R75.2, U134.1 (IN)
unnamed: J10.1 (RF), R307.1, U139.3 (OUT)
unnamed: J11.1 (RF), R301.1, U138.3 (OUT)
unnamed: R25.1, R26.2
unnamed: R24.1, R100.2
unnamed: R189.1, R300.2
unnamed: R189.2, R261.1, U137.1 (IN)
unnamed: R85.2, R195.1
unnamed: R196.1, R296.2
unnamed: R198.1, R270.1, R271.1, U99.1 (IN), U150.1 (IN), U151.1 (IN)
unnamed: R262.2, R265.2
unnamed: R48.1, R264.1, R265.1, U96.1 (IN), U97.1 (IN), U98.1 (IN)
unnamed: R267.1, R306.2, U139.1 (IN)
unnamed: R268.2, R271.2
unnamed: R306.1, R307.2
OUT_A1_#1: C149.1, T11.2
OUT_A1_#2: C386.1, T25.1, T26.4
OUT_A2_#1: C135.2, C155.1, T11.4
OUT_A2_#2: C369.2, C380.1, T25.4, T26.1
OUT_A3_#1: C136.2, C155.2, T11.6
OUT_A3_#2: C370.2, C380.2, T25.3, T26.3
OUT_A4_#1: C135.1, C152.1, L7.2, U1.51 (HFOUTA_N)
OUT_A4_#2: C361.1, C369.1, L31.2, U2.51 (HFOUTA_N)
OUT_A5_#1: C136.1, C152.2, L11.2, U1.52 (HFOUTA_P)
OUT_A5_#2: C361.2, C370.1, L35.2, U2.52 (HFOUTA_P)
OUT_B1_#1: C150.1, T10.4, T21.1
OUT_B1_#2: C384.1, T18.4, T24.1
OUT_B2_#1: C143.2, C158.1, T10.1, T21.4
OUT_B2_#2: C373.2, C381.1, T18.1, T24.4
OUT_B3_#1: C144.2, C158.2, T10.3, T21.3
OUT_B3_#2: C374.2, C381.2, T18.3, T24.3
OUT_B4_#1: C143.1, C153.1, L5.2, U1.19 (HFOUTB_P)
OUT_B4_#2: C360.1, C373.1, L32.2, U2.19 (HFOUTB_P)
OUT_B5_#1: C144.1, C153.2, L9.2, U1.20 (HFOUTB_N)
OUT_B5_#2: C360.2, C374.1, L36.2, U2.20 (HFOUTB_N)
OUT_C1_#1: C148.1, T6.2
OUT_C1_#2: C385.1, T15.2
OUT_C2_#1: C139.2, C156.1, T6.4
OUT_C2_#2: C367.2, C379.1, T15.4
OUT_C3_#1: C140.2, C156.2, T6.6
OUT_C3_#2: C368.2, C379.2, T15.6
OUT_C4_#1: C139.1, C154.1, L6.2, U1.24 (HFOUTC_N)
OUT_C4_#2: C362.1, C367.1, L33.2, U2.24 (HFOUTC_N)
OUT_C5_#1: C140.1, C154.2, L10.2, U1.25 (HFOUTC_P)
OUT_C5_#2: C362.2, C368.1, L37.2, U2.25 (HFOUTC_P)
OUT_D1_#1: C147.1, T9.4, T20.1
OUT_D1_#2: C383.1, T17.4, T23.1
OUT_D2_#1: C137.2, C157.1, T9.1, T20.4
OUT_D2_#2: C371.2, C382.1, T17.1, T23.4
OUT_D3_#1: C138.2, C157.2, T9.3, T20.3
OUT_D3_#2: C372.2, C382.2, T17.3, T23.3
OUT_D4_#1: C137.1, C151.1, L8.2, U1.46 (HFOUTD_P)
OUT_D4_#2: C359.1, C371.1, L34.2, U2.46 (HFOUTD_P)
OUT_D5_#1: C138.1, C151.2, L12.2, U1.47 (HFOUTD_N)
OUT_D5_#2: C359.2, C372.1, L38.2, U2.47 (HFOUTD_N)
RF_IN: R73.1, R75.1, U133.3 (OUT), U134.3 (OUT)
RF_IN_A_#2: C332.1, J35.1 (RF), R574.2
RF_IN_B_#1: C106.1
RF_IN_B_#2: C334.1
RF_IN_D_#1: C105.1
RF_IN_D_#2: C333.1
RF_OUT: R262.1, R263.2, R268.1, R269.2
RF_OUT_A_#1: C149.2, J34.1 (RF), R570.1
RF_OUT_C_#1: C148.2
RF_OUT_C_#2: C385.2
SC1905_FB_#1: R260.2
SC1905_FB_#2: R266.2
SC1905_IN_#1: R263.1
SC1905_IN_#2: R269.1
SC1905_OUT_#1: R264.2
SC1905_OUT_#2: R270.2
SD_AMP1_3V3: U108.1 (QB)
SD_AMP2_3V3: U108.3 (QD)
VDDTX_#1: FB25.1, FB26.1, FB27.1, FB28.1, R93.1, R98.1
VDDTX_#2: FB48.1, FB49.1, FB50.1, FB51.1, R532.1, R533.1
VDD_TXA_#1: R94.2
VDD_TXA_#2: R183.2
VDD_TXB_#1: R95.2
VDD_TXB_#2: R184.2
VDD_TXC_#1: R96.2
VDD_TXC_#2: R185.2
VDD_TXD_#1: R97.2
VDD_TXD_#2: R186.2
VDIO: C630.1, U108.16 (VCC)

Notes on the sheet:
Balanced
Unbalanced
LMS8001 #1
LMS8001 #2
IF_TX1
IF_RX1
IF_ORX1
IF_RX2
NOT USED UP CONVERSION
IF_ORX2
BPF 1805-2025 MHz IL = 1.8 dB
BPF 1580 to 2200 MHz IL = 2 dB
IF_TX2
SC1905
50 Ohm TL
AMP1
AMP2
close together
OP1dB = 16 dBm OIP3dB = 25 dBm Gain = 17 dB
C115
C123
C124
C126
C129
C109
L11
C133
C145
FB25
R94
C154
C140
C139
C156
C148
C104
C107
C111
C112
C120
C119
C127
FB26
R95
C131
C141
C152
C136
C135
C155
C149
C105
C113
C114
C121
C122
C128
FB27
R96
L10
C132
C142
C151
C137
C138
C157
C147
C106
C117
C110
C118
C125
C130
FB28
R97
L12
C134
C146
C153
C144
C143
C158
C150
RX_IF
OTX_RF
TX_IF
TX_RF
ORX_IF
RX_RF
ORX_RF
DAISY CHAIN IN OUT SIGNALS
NOT USED DOWN CONVERSION
