myriadrf/LimeRFE-8001P/hardware/1v1/KiCAD/LMS98001_GPIO.sch

## KiCad design hardware/1v1/KiCAD/LMS98001_GPIO.sch (2023-10-04)

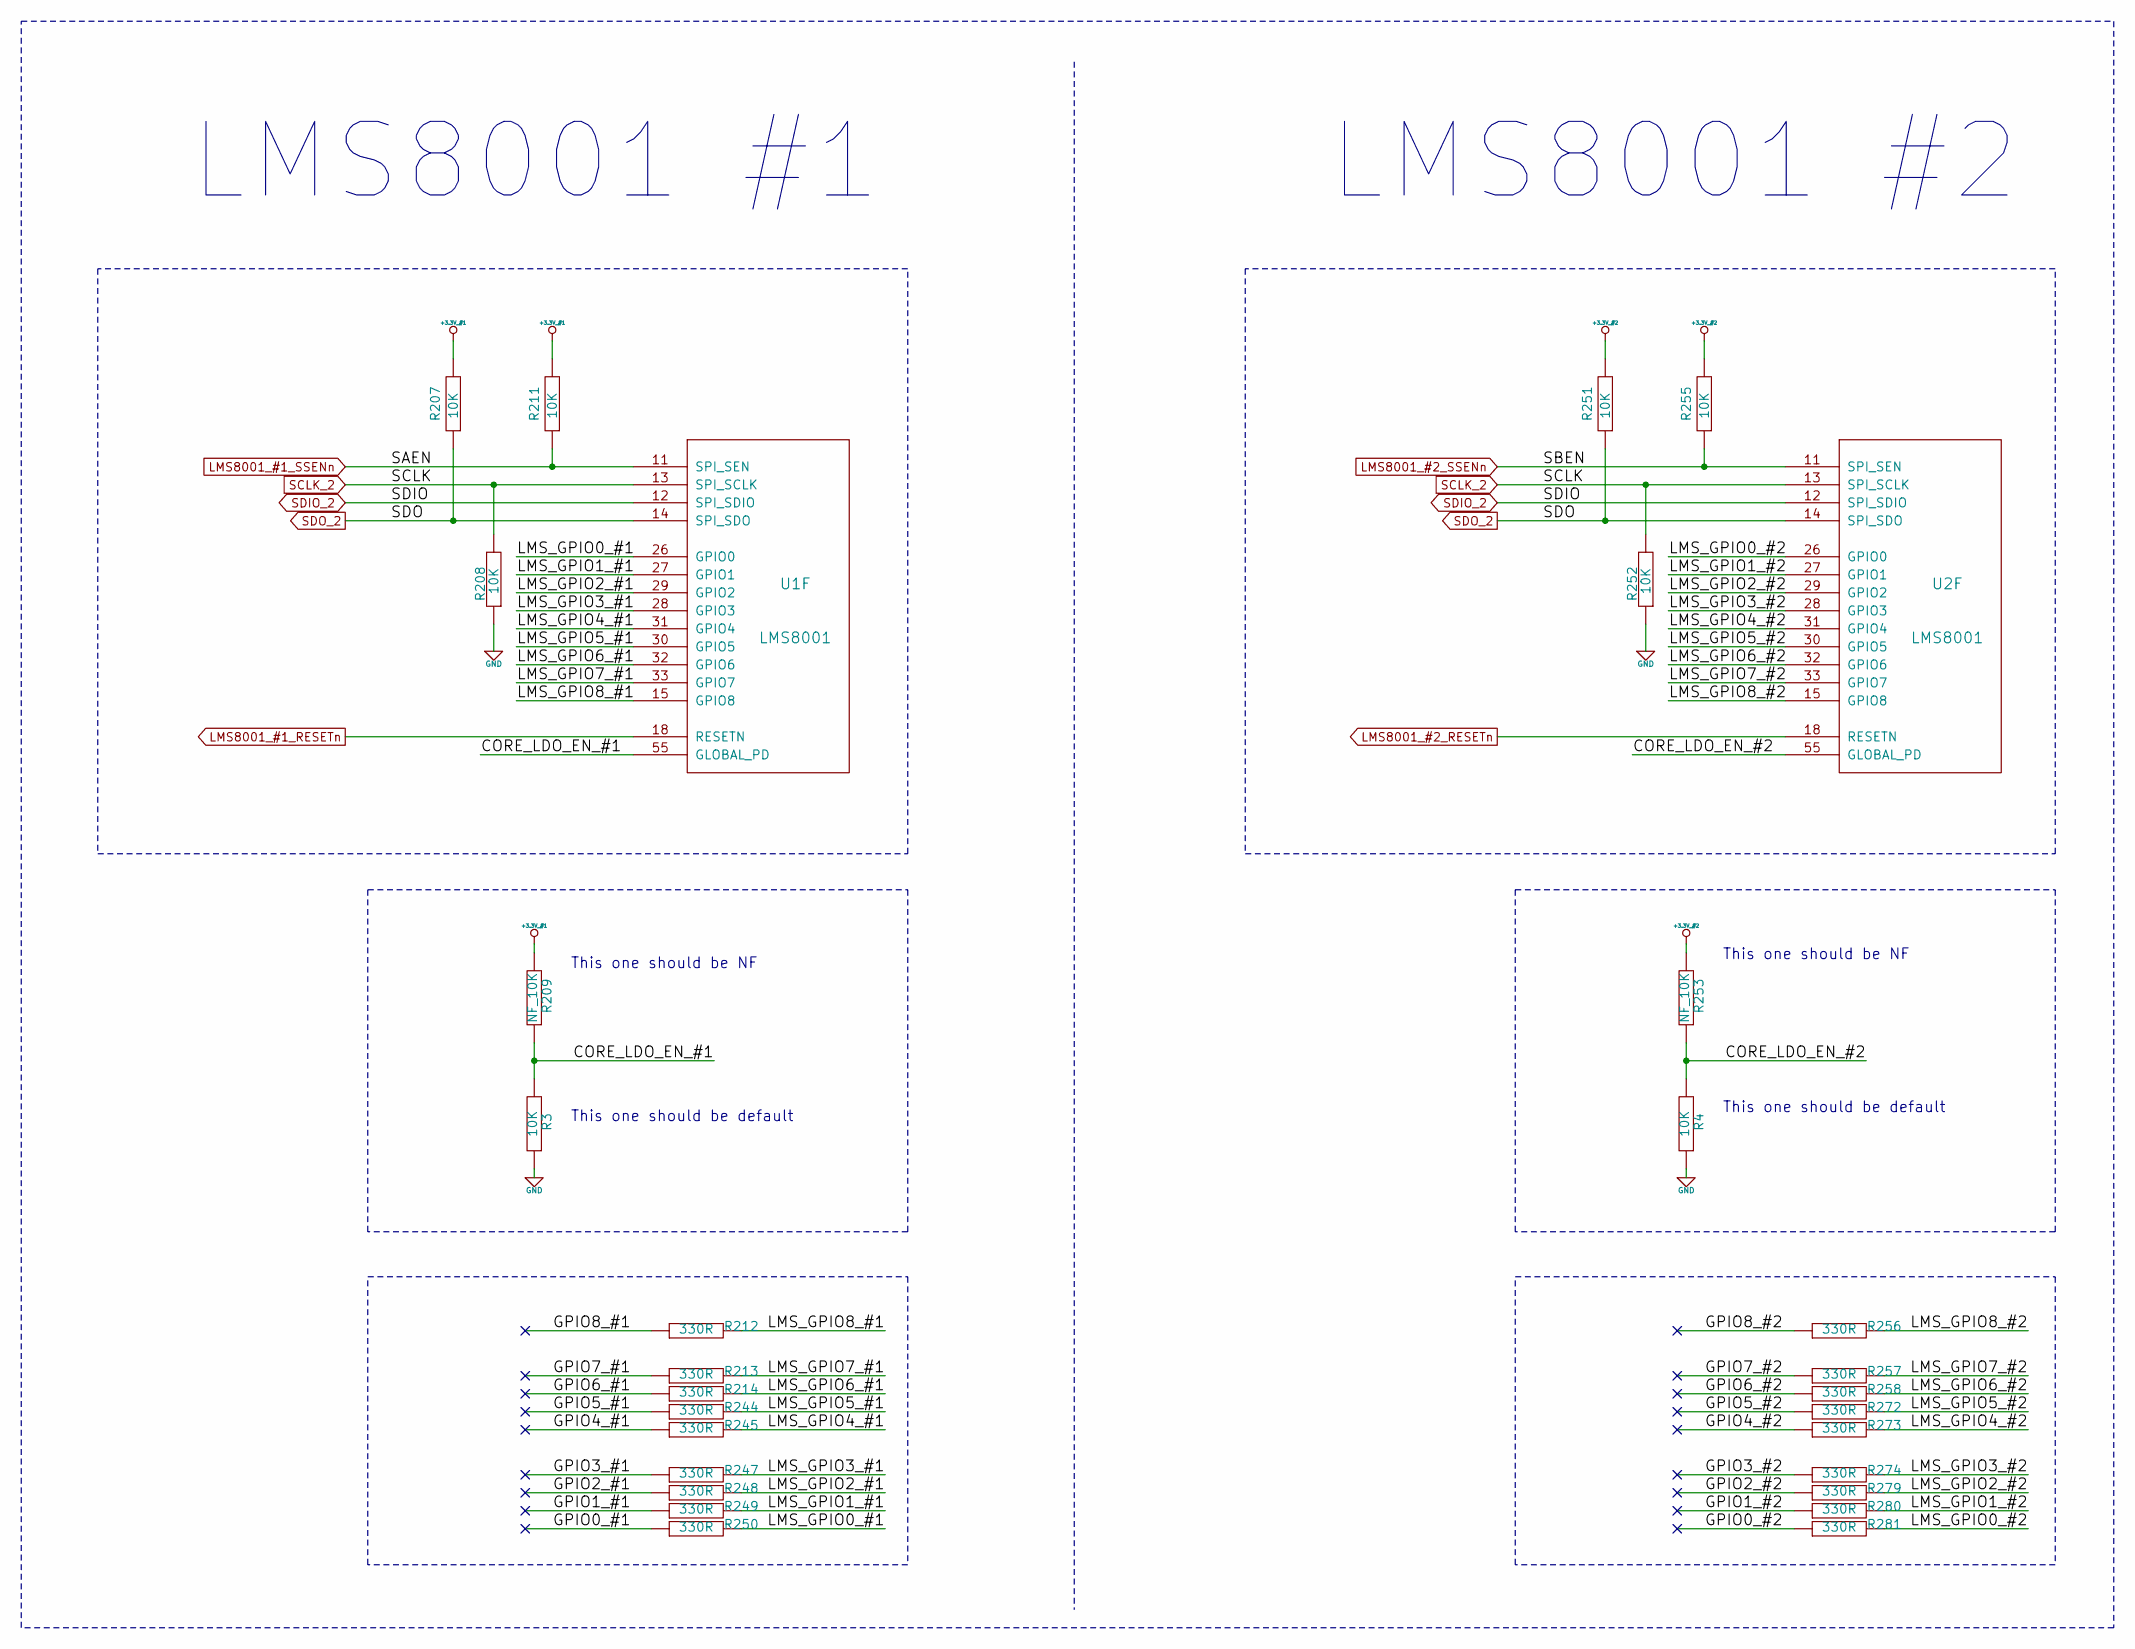
[picture p101: schematic LMS98001_GPIO.sch]

Parts:
R3, R4: 10K_0402; SMD0402
R207, R208, R211, R251, R252, R255: 10K_0402; SMD0402; Manufacturer Part Number RMCF0402FT10K0
R209, R253: NF_10K_0402; SMD0402
R212, R213, R214, R244, R245, R247, R248, R249, R250, R256, R257, R258, R272, R273, R274, R279, R280, R281: 330R_0402; SMD0402; Manufacturer Part Number RC0402JR-07330RL
U1, U2: LMS8001

Connections:
+3.3V_#1: R207.2, R209.2, R211.2
+3.3V_#2: R251.2, R253.2, R255.2
CORE_LDO_EN_#1: R3.2, R209.1, U1.55 (GLOBAL_PD)
CORE_LDO_EN_#2: R4.2, R253.1, U2.55 (GLOBAL_PD)
GND: R3.1, R4.1, R208.1, R252.1
GPIO0_#1: R250.1
GPIO0_#2: R281.1
GPIO1_#1: R249.1
GPIO1_#2: R280.1
GPIO2_#1: R248.1
GPIO2_#2: R279.1
GPIO3_#1: R247.1
GPIO3_#2: R274.1
GPIO4_#1: R245.1
GPIO4_#2: R273.1
GPIO5_#1: R244.1
GPIO5_#2: R272.1
GPIO6_#1: R214.1
GPIO6_#2: R258.1
GPIO7_#1: R213.1
GPIO7_#2: R257.1
GPIO8_#1: R212.1
GPIO8_#2: R256.1
LMS8001_#1_RESETn: U1.18 (RESETN)
LMS8001_#1_SSENn: R211.1, U1.11 (SPI_SEN)
LMS8001_#2_RESETn: U2.18 (RESETN)
LMS8001_#2_SSENn: R255.1, U2.11 (SPI_SEN)
LMS_GPIO0_#1: R250.2, U1.26 (GPIO0)
LMS_GPIO0_#2: R281.2, U2.26 (GPIO0)
LMS_GPIO1_#1: R249.2, U1.27 (GPIO1)
LMS_GPIO1_#2: R280.2, U2.27 (GPIO1)
LMS_GPIO2_#1: R248.2, U1.29 (GPIO2)
LMS_GPIO2_#2: R279.2, U2.29 (GPIO2)
LMS_GPIO3_#1: R247.2, U1.28 (GPIO3)
LMS_GPIO3_#2: R274.2, U2.28 (GPIO3)
LMS_GPIO4_#1: R245.2, U1.31 (GPIO4)
LMS_GPIO4_#2: R273.2, U2.31 (GPIO4)
LMS_GPIO5_#1: R244.2, U1.30 (GPIO5)
LMS_GPIO5_#2: R272.2, U2.30 (GPIO5)
LMS_GPIO6_#1: R214.2, U1.32 (GPIO6)
LMS_GPIO6_#2: R258.2, U2.32 (GPIO6)
LMS_GPIO7_#1: R213.2, U1.33 (GPIO7)
LMS_GPIO7_#2: R257.2, U2.33 (GPIO7)
LMS_GPIO8_#1: R212.2, U1.15 (GPIO8)
LMS_GPIO8_#2: R256.2, U2.15 (GPIO8)
SCLK_2: R208.2, R252.2, U1.13 (SPI_SCLK), U2.13 (SPI_SCLK)
SDIO_2: U1.12 (SPI_SDIO), U2.12 (SPI_SDIO)
SDO_2: R207.1, R251.1, U1.14 (SPI_SDO), U2.14 (SPI_SDO)

Notes on the sheet:
This one should be default
This one should be NF
LMS8001 #1
LMS8001 #2
