myriadrf/LimeRFE-8001P/hardware/1v1/KiCAD/RF.sch

## KiCad design hardware/1v1/KiCAD/RF.sch (2023-10-04)

Schematic: RF.sch

Parts:
C28, C29, C30, C31, C32, C34, C37, C40, C42, C182, C183, C184, C189, C205, C223, C224, C225, C226, C230, C231, C235, C251, C252, C253, C254, C255, C256, C284, C285, C287, C288, C289, C290, C322, C323, C324, C325, C326, C327, C329, C330, C387, C388, C389, C390, C391, C392, C393, C396, C458, C459, C466, C467, C468, C525, C588, C589, C590, C591, C592, C593, C594, C595, C596, C597: 10nF_0402; SMD0402; Manufacturer Part Number CC0402ZRY5V7BB103
C36, C401, C576, C577: 470pF_0402_GRM1555C1H471JA01D; SMD0402; Manufacturer Part Number GRM1555C1H471JA01D
C38, C402, C526, C575: 47nF_0402_GCM155R71H473KE02D; SMD0402; Manufacturer Part Number GCM155R71H473KE02D
C190, C232, C233, C236, C237, C328: 5pF_0402_CBR04C509C5GAC; SMD0402; Manufacturer Part Number CBR04C509C5GAC
J4, J5, J15, J20: SMA_H_142-0701-851; SMA_H; Manufacturer Part Number 142-0701-851
J17, J22: SMA_VERT_SMD; SMA_vert_SMD; Manufacturer Part Number 0732511352
R6, R7, R8, R9, R10, R11, R12, R13, R16, R17, R18, R19: 0R_0603_NF; SMD0603; Manufacturer Part Number RCS06030000Z0EA
R22, R23, R230, R232, R565, R572: 0R_0402_NF; SMD0402; Manufacturer Part Number RC0402JR-070RL
R99, R190, R537, R573: 49.9R_0402_ERJ-U02F49R9X; SMD0402; Manufacturer Part Number ERJ-U02F49R9X
R126, R193, R194, R229, R231, R282, R302, R303, R304, R305: 0R_0402; SMD0402
R129, R132, R133, R134, R135, R136, R137, R140, R141, R142, R153, R163, R164, R165, R166, R167, R168, R169, R170, R288, R290, R293, R294, R295, R517, R518, R519, R520, R521, R522, R523, R524, R525, R526: 10K_0402; SMD0402
R191, R192: 0RNF_0402; SMD0402
U3, U107: PAT1220-C-6DB-T5; Manufacturer Part Number PAT1220-C-6DB-T5
U4, U27, U30, U31, U39, U40, U41, U42: SKY13330-397LF; Manufacturer Part Number SKY13330-397LF
U20, U23, U156, U158, U160, U162: NF_PAT1220-C-3DB-T5; PAT1220-C-3DB-T5; Manufacturer Part Number PAT1220-C-3DB-T5
U22, U25: NF_PAT1220-C-10DB-T5; PAT1220-C-10DB-T5; Manufacturer Part Number PAT1220-C-10DB-T5
U28, U32, U55, U70, U88: SN74HCS594QPWRQ1; Manufacturer Part Number SN74HCS594QPWRQ1
U33, U73: SN74LVC8T245QPWRQ1; Manufacturer Part Number SN74LVC8T245QPWRQ1
U34, U49, U50, U81, U82, U83, U84, U110: SN74LV1T04; Manufacturer Part Number SN74LV1T04DCKRG4
U35, U71, U72, U91: F1956NBGI8; Manufacturer Part Number F1956NBGI8
U36, U111: SN74LV1T34; Manufacturer Part Number Texas Instruments
U37, U43, U56, U87, U148, U149: BFCV-4085+; Manufacturer Part Number BFCV-4085+
U51, U52, U53, U54, U75, U80, U104, U105: MC74VHC1G08DTT1G; Manufacturer Part Number MC74VHC1G08DTT1G
U57, U61: PAT3060H-C-10DB-T1; Manufacturer Part Number PAT3060H-C-10DB-T1
U60, U62: NF_PAT3060H-C-1DB-T1; PAT3060H-C-1DB-T1; Manufacturer Part Number PAT3060H-C-1DB-T1
U123, U132: HHM2955A1; Manufacturer Part Number HHM2955A1
U155, U159: NF_PAT1220-C-2DB-T5; PAT1220-C-2DB-T5; Manufacturer Part Number PAT1220-C-2DB-T5
U157, U161: PAT1220-C-4DB-T5; Manufacturer Part Number PAT1220-C-4DB-T5

Connections:
+1.8V: C223.1, C287.2, C288.2, C289.2, C290.2, U33.1 (VCCA), U81.5 (VCC), U82.5 (VCC), U83.5 (VCC), U84.5 (VCC)
+5V: C36.1, C38.1, C393.1, C401.1, C402.1, C526.1, C575.1, C576.1, C577.1, U35.2 (VDD), U71.2 (VDD), U72.2 (VDD), U73.23 (VCCB), U73.24 (VCCB), U91.2 (VDD)
DA1_ATT_D0_3V3: C323.2, R163.1, U55.1 (QB), U71.32 (D0)
DA1_ATT_D1_3V3: C325.2, R165.1, U55.2 (QC), U71.31 (D1)
DA1_ATT_D2_3V3: C329.2, R167.1, U55.3 (QD), U71.30 (D2)
DA1_ATT_D3_3V3: C387.2, R169.1, U55.4 (QE), U71.29 (D3)
DA1_ATT_D4_3V3: C389.2, R288.1, U55.5 (QF), U71.28 (D4)
DA1_ATT_D5_3V3: C391.2, R293.1, U55.6 (QG), U71.27 (D5)
DA1_ATT_D6_3V3: C184.2, R129.1, U55.7 (QH), U71.26 (D6)
DA1_A\da1_b_CTRL_3V3: R140.1, U32.15 (QA)
DA1_A_EN_3V3: U28.15 (QA), U51.1 (B)
DA1_A_ON\off_3V3: U51.4 (Y), U73.5 (A3)
DA1_A_ON\off_5V: U73.19 (B3)
DA1_A_SEL: U4.7 (CTRL), U83.4 (Y)
DA1_A_SELn: U30.7 (CTRL), U81.4 (Y), U83.2 (A)
DA1_B_EN_3V3: U28.1 (QB), U75.1 (B)
DA1_B_ON\off_3V3: U73.6 (A4), U75.4 (Y)
DA1_B_ON\off_5V: U73.18 (B4)
DA1_CPL_OUT: R191.2, U123.4 (CPL)
DA2_ATT_D0_3V3: C324.2, R164.1, U70.1 (QB), U72.32 (D0)
DA2_ATT_D1_3V3: C326.2, R166.1, U70.2 (QC), U72.31 (D1)
DA2_ATT_D2_3V3: C330.2, R168.1, U70.3 (QD), U72.30 (D2)
DA2_ATT_D3_3V3: C388.2, R170.1, U70.4 (QE), U72.29 (D3)
DA2_ATT_D4_3V3: C390.2, R290.1, U70.5 (QF), U72.28 (D4)
DA2_ATT_D5_3V3: C525.2, R294.1, U70.6 (QG), U72.27 (D5)
DA2_ATT_D6_3V3: C322.2, R132.1, U70.7 (QH), U72.26 (D6)
DA2_A\da2_b_CTRL_3V3: R141.1, U88.15 (QA)
DA2_A_EN_3V3: U28.2 (QC), U53.1 (B)
DA2_A_ON\off_3V3: U53.4 (Y), U73.7 (A5)
DA2_A_ON\off_5V: U73.17 (B5)
DA2_A_SEL: U27.7 (CTRL), U84.4 (Y)
DA2_A_SELn: U31.7 (CTRL), U82.4 (Y), U84.2 (A)
DA2_B_EN_3V3: U28.3 (QD), U80.1 (B)
DA2_B_ON\off_3V3: U73.8 (A6), U80.4 (Y)
DA2_B_ON\off_5V: U73.16 (B6)
DA2_CPL_OUT: R192.2, U132.4 (CPL)
DATA_IN: U28.14 (SER)
DATA_OUT: U70.9 (QH')
DATA_OUT_EN: U28.12 (RCLK), U32.12 (RCLK), U55.12 (RCLK), U70.12 (RCLK), U88.12 (RCLK)
DATA_OUT_RSTn: U28.13 (RCLRn), U32.13 (RCLRn), U55.13 (RCLRn), U70.13 (RCLRn), U88.13 (RCLRn)
DATA_SER_CLK: U28.11 (SRCLK), U32.11 (SRCLK), U55.11 (SRCLK), U70.11 (SRCLK), U88.11 (SRCLK)
DATA_SER_RSTn: U28.10 (SRCLRn), U32.10 (SRCLRn), U55.10 (SRCLRn), U70.10 (SRCLRn), U88.10 (SRCLRn)
GND: C28.1, C29.1, C30.1, C31.1, C32.1, C34.1, C36.2, C37.1, C38.2, C40.1, C42.1, C182.2, C183.2, C184.1, C189.1, C205.2, C223.2, C224.2, C225.2, C226.1, C230.1, C231.1, C235.1, C251.1, C252.1, C253.1, C254.1, C255.1, C256.1, C284.1, C285.1, C287.1, C288.1, C289.1, C290.1, C322.1, C323.1, C324.1, C325.1, C326.1, C327.1, C329.1, C330.1, C387.1, C388.1, C389.1, C390.1, C391.1, C392.2, C393.2, C396.2, C401.2, C402.2, C458.1, C459.1, C466.1, C467.1, C468.1, C525.1, C526.2, C575.2, C576.2, C577.2, C588.1, C589.1, C590.1, C591.1, C592.1, C593.1, C594.1, C595.1, C596.1, C597.1, J4.2 (GND1), J4.3 (GND2), J4.4 (GND3), J4.5 (GND4), J5.2 (GND1), J5.3 (GND2), J5.4 (GND3), J5.5 (GND4), J15.2 (GND1), J15.3 (GND2), J15.4 (GND3), J15.5 (GND4), J17.2 (GND1), J17.3 (GND2), J17.4 (GND3), J17.5 (GND4), J20.2 (GND1), J20.3 (GND2), J20.4 (GND3), J20.5 (GND4), J22.2 (GND1), J22.3 (GND2), J22.4 (GND3), J22.5 (GND4), R99.1, R142.1, R153.1, R190.1, R537.1, R573.1, U3.3 (GND), U4.1 (GND), U4.3 (GND), U4.4 (GND), U4.6 (GND), U4.10 (GND), U4.12 (GND), U4.13, U20.3 (GND), U22.3 (GND), U23.3 (GND), U25.3 (GND), U27.1 (GND), U27.3 (GND), U27.4 (GND), U27.6 (GND), U27.10 (GND), U27.12 (GND), U27.13, U28.8 (GND), U30.1 (GND), U30.3 (GND), U30.4 (GND), U30.6 (GND), U30.10 (GND), U30.12 (GND), U30.13, U31.1 (GND), U31.3 (GND), U31.4 (GND), U31.6 (GND), U31.10 (GND), U31.12 (GND), U31.13, U32.8 (GND), U33.2 (DIR), U33.7 (A5), U33.8 (A6), U33.9 (A7), U33.10 (A8), U33.11 (GND), U33.12 (GND), U33.13 (GND), U33.14 (B8), U33.15 (B7), U33.16 (B6), U33.17 (B5), U33.22 (OEn), U34.3 (GND), U35.3 (V_MODE), U35.5 (GND), U35.6 (GND), U35.8 (GND), U35.9 (GND), U35.10 (GND), U35.11 (GND), U35.12 (GND), U35.13 (GND), U35.14 (GND), U35.15 (GND), U35.16 (GND), U35.17 (GND), U35.19 (GND), U35.25 (DATA), U35.33 (GND), U36.3 (GND), U37.2 (GND), U37.4 (GND), U39.1 (GND), U39.3 (GND), U39.4 (GND), U39.6 (GND), U39.10 (GND), U39.12 (GND), U39.13, U40.1 (GND), U40.3 (GND), U40.4 (GND), U40.6 (GND), U40.10 (GND), U40.12 (GND), U40.13, U41.1 (GND), U41.3 (GND), U41.4 (GND), U41.6 (GND), U41.10 (GND), U41.12 (GND), U41.13, U42.1 (GND), U42.3 (GND), U42.4 (GND), U42.6 (GND), U42.10 (GND), U42.12 (GND), U42.13, U43.2 (GND), U43.4 (GND), U49.3 (GND), U50.3 (GND), U51.3 (GND), U52.3 (GND), U53.3 (GND), U54.3 (GND), U55.8 (GND), U56.2 (GND), U56.4 (GND), U57.3 (GND), U60.3 (GND), U61.3 (GND), U62.3 (GND), U70.8 (GND), U71.3 (V_MODE), U71.5 (GND), U71.6 (GND), U71.8 (GND), U71.9 (GND), U71.10 (GND), U71.11 (GND), U71.12 (GND), U71.13 (GND), U71.14 (GND), U71.15 (GND), U71.16 (GND), U71.17 (GND), U71.19 (GND), U71.25 (DATA), U71.33 (GND), U72.3 (V_MODE), U72.5 (GND), U72.6 (GND), U72.8 (GND), U72.9 (GND), U72.10 (GND), U72.11 (GND), U72.12 (GND), U72.13 (GND), U72.14 (GND), U72.15 (GND), U72.16 (GND), U72.17 (GND), U72.19 (GND), U72.25 (DATA), U72.33 (GND), U73.11 (GND), U73.12 (GND), U73.13 (GND), U73.22 (OEn), U75.3 (GND), U80.3 (GND), U81.3 (GND), U82.3 (GND), U83.3 (GND), U84.3 (GND), U87.2 (GND), U87.4 (GND), U88.8 (GND), U91.3 (V_MODE), U91.5 (GND), U91.6 (GND), U91.8 (GND), U91.9 (GND), U91.10 (GND), U91.11 (GND), U91.12 (GND), U91.13 (GND), U91.14 (GND), U91.15 (GND), U91.16 (GND), U91.17 (GND), U91.19 (GND), U91.25 (DATA), U91.33 (GND), U104.3 (GND), U105.3 (GND), U107.3 (GND), U110.3 (GND), U111.3 (GND), U123.2 (GND), U123.5 (GND), U132.2 (GND), U132.5 (GND), U148.2 (GND), U148.4 (GND), U149.2 (GND), U149.4 (GND), U155.3 (GND), U156.3 (GND), U157.3 (GND), U158.3 (GND), U159.3 (GND), U160.3 (GND), U161.3 (GND), U162.3 (GND)
LNA1_EN_3V3: U28.4 (QE), U52.1 (B)
LNA1_ON\off_3V3: U52.4 (Y), U73.9 (A7)
LNA1_ON\off_5V: U73.15 (B7)
LNA2_EN_3V3: U28.5 (QF), U54.1 (B)
LNA2_ON\off_3V3: U54.4 (Y), U73.10 (A8)
LNA2_ON\off_5V: U73.14 (B8)
unnamed: C190.1, U31.2 (RF1)
unnamed: C190.2, U42.5 (RF3)
unnamed: C232.1, U30.2 (RF1)
unnamed: C232.2, U41.5 (RF3)
unnamed: C233.1, R565.2, U39.2 (RF1)
unnamed: C233.2, U41.11 (RF2)
unnamed: C236.1, U41.2 (RF1)
unnamed: C236.2, U123.3 (IN)
unnamed: C237.1, U42.2 (RF1)
unnamed: C237.2, U132.3 (IN)
unnamed: C328.1, R572.2, U40.2 (RF1)
unnamed: C328.2, U42.11 (RF2)
unnamed: J4.1 (RF), R193.1
unnamed: J5.1 (RF), R194.1
unnamed: J15.1 (RF), R18.1, U43.3 (OUT)
unnamed: J17.1 (RF), R12.1, U148.3 (OUT)
unnamed: J20.1 (RF), R19.1, U56.3 (OUT)
unnamed: J22.1 (RF), R13.1, U149.3 (OUT)
unnamed: R6.1, R8.2
unnamed: R7.1, R9.2
unnamed: R10.1, R12.2
unnamed: R10.2, R565.1, U148.1 (IN)
unnamed: R11.1, R13.2
unnamed: R11.2, R572.1, U149.1 (IN)
unnamed: R16.1, R18.2
unnamed: R16.2, U43.1 (IN), U123.1 (OUT)
unnamed: R17.1, R19.2
unnamed: R17.2, U56.1 (IN), U132.1 (OUT)
unnamed: R7.2, R22.2, U3.2 (OUT), U20.2 (OUT), U22.2 (OUT), U87.1 (IN)
unnamed: R6.2, R23.2, U23.2 (OUT), U25.2 (OUT), U37.1 (IN), U107.2 (OUT)
unnamed: R99.2, U39.11 (RF2)
unnamed: R140.2, R142.2, U81.2 (A)
unnamed: R141.2, R153.2, U82.2 (A)
unnamed: R190.2, U40.11 (RF2)
unnamed: R191.1, R193.2, U57.2 (OUT), U60.2 (OUT)
unnamed: R192.1, R194.2, U61.2 (OUT), U62.2 (OUT)
unnamed: R229.2, U4.11 (RF2), U155.1 (IN), U156.1 (IN)
unnamed: R230.1, U4.5 (RF3), U157.1 (IN), U158.1 (IN)
unnamed: R231.2, U27.11 (RF2), U159.1 (IN), U160.1 (IN)
unnamed: R232.1, U27.5 (RF3), U161.1 (IN), U162.1 (IN)
unnamed: R302.2, U71.23 (LE)
unnamed: R303.2, U72.23 (LE)
unnamed: R304.2, U91.23 (LE)
unnamed: R305.2, U35.23 (LE)
unnamed: R537.2, U123.6 (TERM)
unnamed: R573.2, U132.6 (TERM)
unnamed: U4.2 (RF1), U71.18 (RF2)
unnamed: U27.2 (RF1), U72.18 (RF2)
unnamed: U28.9 (QH'), U32.14 (SER)
unnamed: U32.9 (QH'), U88.14 (SER)
unnamed: U35.7 (RF1), U61.1 (IN), U62.1 (IN)
unnamed: U49.4 (Y), U52.2 (A)
unnamed: U50.4 (Y), U54.2 (A)
unnamed: U55.9 (QH'), U70.14 (SER)
unnamed: U55.14 (SER), U88.9 (QH')
unnamed: U57.1 (IN), U60.1 (IN), U91.7 (RF1)
ORX1_ATT_D0_3V3: C30.2, R135.1, U32.1 (QB), U91.32 (D0)
ORX1_ATT_D1_3V3: C31.2, R136.1, U32.2 (QC), U91.31 (D1)
ORX1_ATT_D2_3V3: C32.2, R137.1, U32.3 (QD), U91.30 (D2)
ORX1_ATT_D3_3V3: C592.2, R521.1, U32.4 (QE), U91.29 (D3)
ORX1_ATT_D4_3V3: C594.2, R523.1, U32.5 (QF), U91.28 (D4)
ORX1_ATT_D5_3V3: C596.2, R525.1, U32.6 (QG), U91.27 (D5)
ORX1_ATT_D6_3V3: C29.2, R134.1, U32.7 (QH), U91.26 (D6)
ORX2_ATT_D0_3V3: C589.2, R518.1, U35.32 (D0), U88.1 (QB)
ORX2_ATT_D1_3V3: C590.2, R519.1, U35.31 (D1), U88.2 (QC)
ORX2_ATT_D2_3V3: C591.2, R520.1, U35.30 (D2), U88.3 (QD)
ORX2_ATT_D3_3V3: C593.2, R522.1, U35.29 (D3), U88.4 (QE)
ORX2_ATT_D4_3V3: C595.2, R524.1, U35.28 (D4), U88.5 (QF)
ORX2_ATT_D5_3V3: C597.2, R526.1, U35.27 (D5), U88.6 (QG)
ORX2_ATT_D6_3V3: C588.2, R517.1, U35.26 (D6), U88.7 (QH)
PDA1_EN_3V3: U28.6 (QG), U104.1 (B)
PDA1_ON\off_3V3: U73.3 (A1), U104.4 (Y)
PDA1_ON\off_5V: U73.21 (B1)
PDA2_EN_3V3: U28.7 (QH), U105.1 (B)
PDA2_ON\off_3V3: U73.4 (A2), U105.4 (Y)
PDA2_ON\off_5V: U73.20 (B2)
RF_IN: R8.1, R9.1, R230.2, R232.2, U37.3 (OUT), U87.3 (OUT), U157.2 (OUT), U158.2 (OUT), U161.2 (OUT), U162.2 (OUT)
RF_IN_D_#1: U91.18 (RF2)
RF_IN_D_#2: U35.18 (RF2)
RF_OUT: U30.11 (RF2), U31.11 (RF2), U71.7 (RF1), U72.7 (RF1)
RF_OUT_C_#1: R23.1, U23.1 (IN), U25.1 (IN), U107.1 (IN)
RF_OUT_C_#2: R22.1, U3.1 (IN), U20.1 (IN), U22.1 (IN)
RF_in: R229.1, R231.1, U39.5 (RF3), U40.5 (RF3), U155.2 (OUT), U156.2 (OUT), U159.2 (OUT), U160.2 (OUT)
RF_out: U30.5 (RF3), U31.5 (RF3)
RX_ISOL_1_1V8: U33.3 (A1), U39.7 (CTRL)
RX_ISOL_1_3V3: U33.21 (B1), U36.4 (Y)
RX_ISOL_2_1V8: U33.5 (A3), U40.7 (CTRL)
RX_ISOL_2_3V3: U33.19 (B3), U111.4 (Y)
TX\rx_1: R126.1, R133.1, U34.2 (A), U36.2 (A), U49.2 (A), U51.2 (A), U75.2 (A), U104.2 (A)
TX\rx_2: R282.1, R295.1, U50.2 (A), U53.2 (A), U80.2 (A), U105.2 (A), U110.2 (A), U111.2 (A)
VDIO: C28.2, C34.2, C37.2, C40.2, C42.2, C182.1, C183.1, C189.2, C205.1, C224.1, C225.1, C226.2, C230.2, C231.2, C235.2, C251.2, C252.2, C253.2, C254.2, C255.2, C256.2, C284.2, C285.2, C327.2, C392.1, C396.1, C458.2, C459.2, C466.2, C467.2, C468.2, R129.2, R132.2, R133.2, R134.2, R135.2, R136.2, R137.2, R163.2, R164.2, R165.2, R166.2, R167.2, R168.2, R169.2, R170.2, R288.2, R290.2, R293.2, R294.2, R295.2, R302.1, R303.1, R304.1, R305.1, R517.2, R518.2, R519.2, R520.2, R521.2, R522.2, R523.2, R524.2, R525.2, R526.2, U4.8 (ENABLE), U4.9 (VBATT), U27.8 (ENABLE), U27.9 (VBATT), U28.16 (VCC), U30.8 (ENABLE), U30.9 (VBATT), U31.8 (ENABLE), U31.9 (VBATT), U32.16 (VCC), U33.23 (VCCB), U33.24 (VCCB), U34.5 (VCC), U36.5 (VCC), U39.8 (ENABLE), U39.9 (VBATT), U40.8 (ENABLE), U40.9 (VBATT), U41.8 (ENABLE), U41.9 (VBATT), U42.8 (ENABLE), U42.9 (VBATT), U49.5 (VCC), U50.5 (VCC), U51.5 (VCC), U52.5 (VCC), U53.5 (VCC), U54.5 (VCC), U55.16 (VCC), U70.16 (VCC), U73.1 (VCCA), U73.2 (DIR), U75.5 (VCC), U80.5 (VCC), U88.16 (VCC), U104.5 (VCC), U105.5 (VCC), U110.5 (VCC), U111.5 (VCC)
g_TX\rx_1: R126.2
g_TX\rx_2: R282.2
tx_RX_1_1V8: U33.4 (A2), U41.7 (CTRL)
tx_RX_1_3V3: U33.20 (B2), U34.4 (Y)
tx_RX_2_1V8: U33.6 (A4), U42.7 (CTRL)
tx_RX_2_3V3: U33.18 (B4), U110.4 (Y)

Notes on the sheet:
TXRX1
DAISY CHAIN IN OUT SIGNALS
ISOL=24dB IL = 0.5dB
inA
outA
inB
outB
inC
outC
outD
inD
LMS8001 #1
DAs control
LMS8001 #2
PDA1
PDA2
pull-up
Pull-Ups for Variable Attenuators in Observation Path
TDD SWITCHES control
ORX1
ORX2
DA1_A
LNA2
LNA1
DA2 Output to OBSERVATION PATH
DA1 Output to OBSERVATION PATH
External PA1 Output to OBSERVATION PATH
External PA2 Output to OBSERVATION PATH
SKY13373-460LF vdd=3.3, vctrl=1.8, iso=20, il=0.6 SKYA21003, vdd=3.3=vctrl=1.8, iso=24, il=0.5 SKY13330-397LF isti ko skya21003
3.3V level
DA2_A
DA1_B
DA2_B
DA A or B Selection Switches Control
OP1dB = 30-27 dBm (@3.3-3.8 GHz) Gain = 33 dB
OP1dB = 25 dBm (@2.3-5.0 GHz) Gain = 34 dB
NF=1.5-1.8 dB (@2-5 GHz) Gain = 18.5-14.8 dB (@2-5 GHz)
ATT = 10 dB
ATT = 1 dB
PDAs control
1.65-5.5V on B side
ATT = (0-31.75, step 0.25) dB
LNAs control
OP1dB = 16 dBm OIP3dB = 25 dBm Gain = 17 dB
TXRX2
RX1
RX2
BPF 3.1-4.9 GHz IL = 2dB
Pull-Ups for Variable Attenuators in Transmiter Path
Microstrip coupler 1.43-5.95 GHz Coup = 24 dB IL = 0.2 dB
1.65-5.5V on A side
Daisy chain side
TXRX side
