myriadrf/LimeRFE-8001P/hardware/1v1/KiCAD/SC1905_1.sch

## KiCad design hardware/1v1/KiCAD/SC1905_1.sch (2023-10-04)

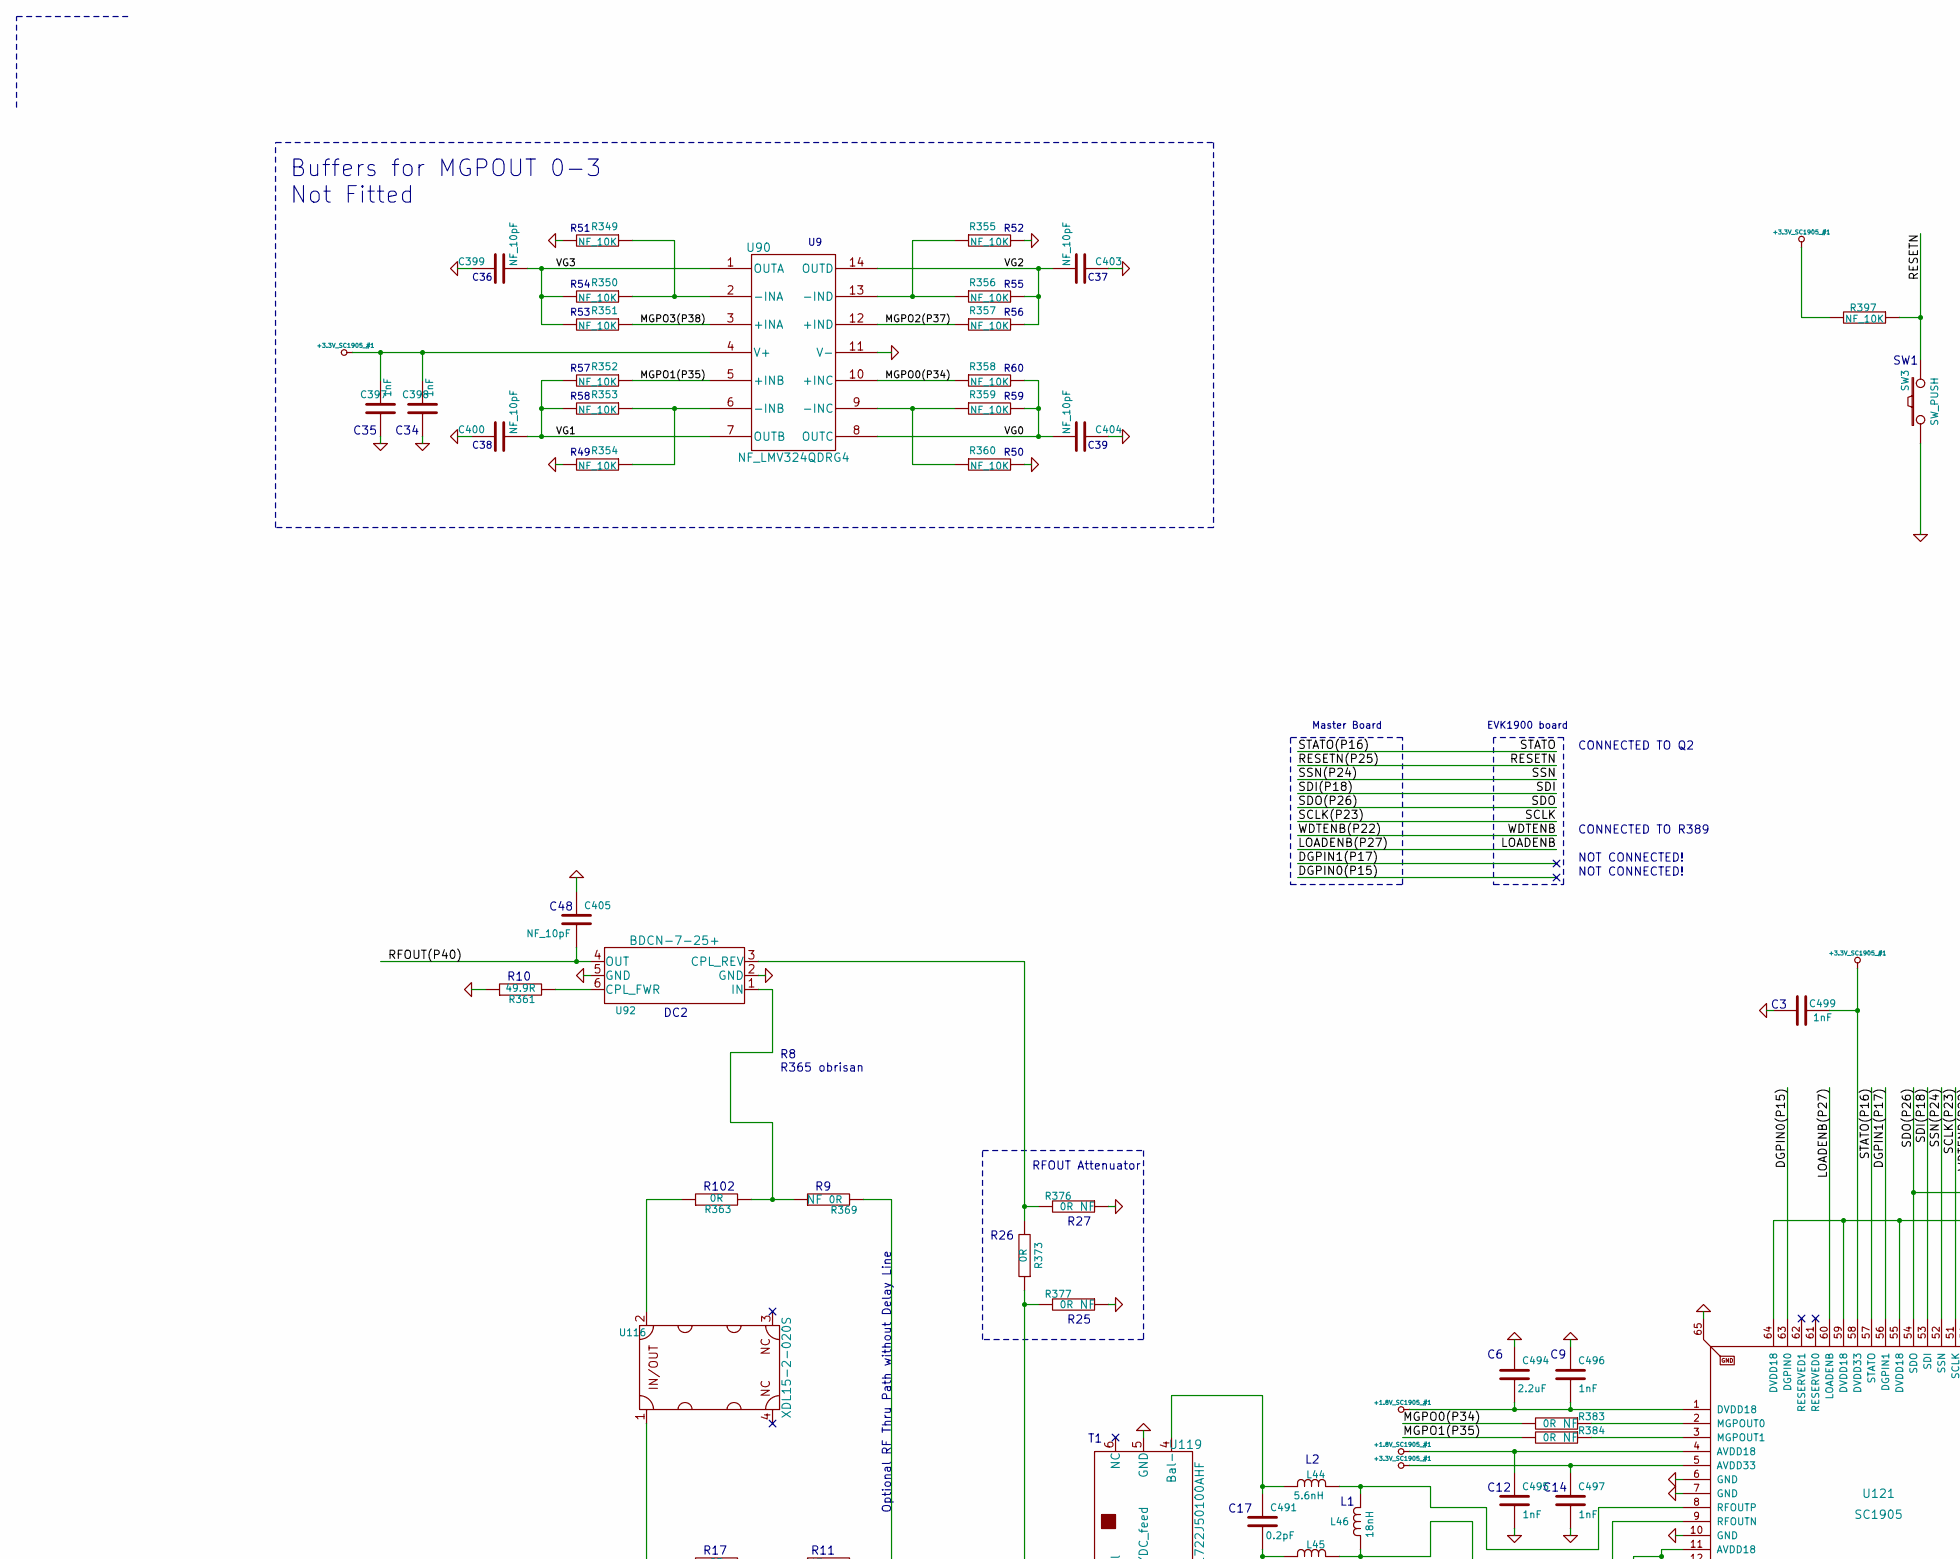
[picture p106: schematic SC1905_1.sch, part in row 1, column 1]

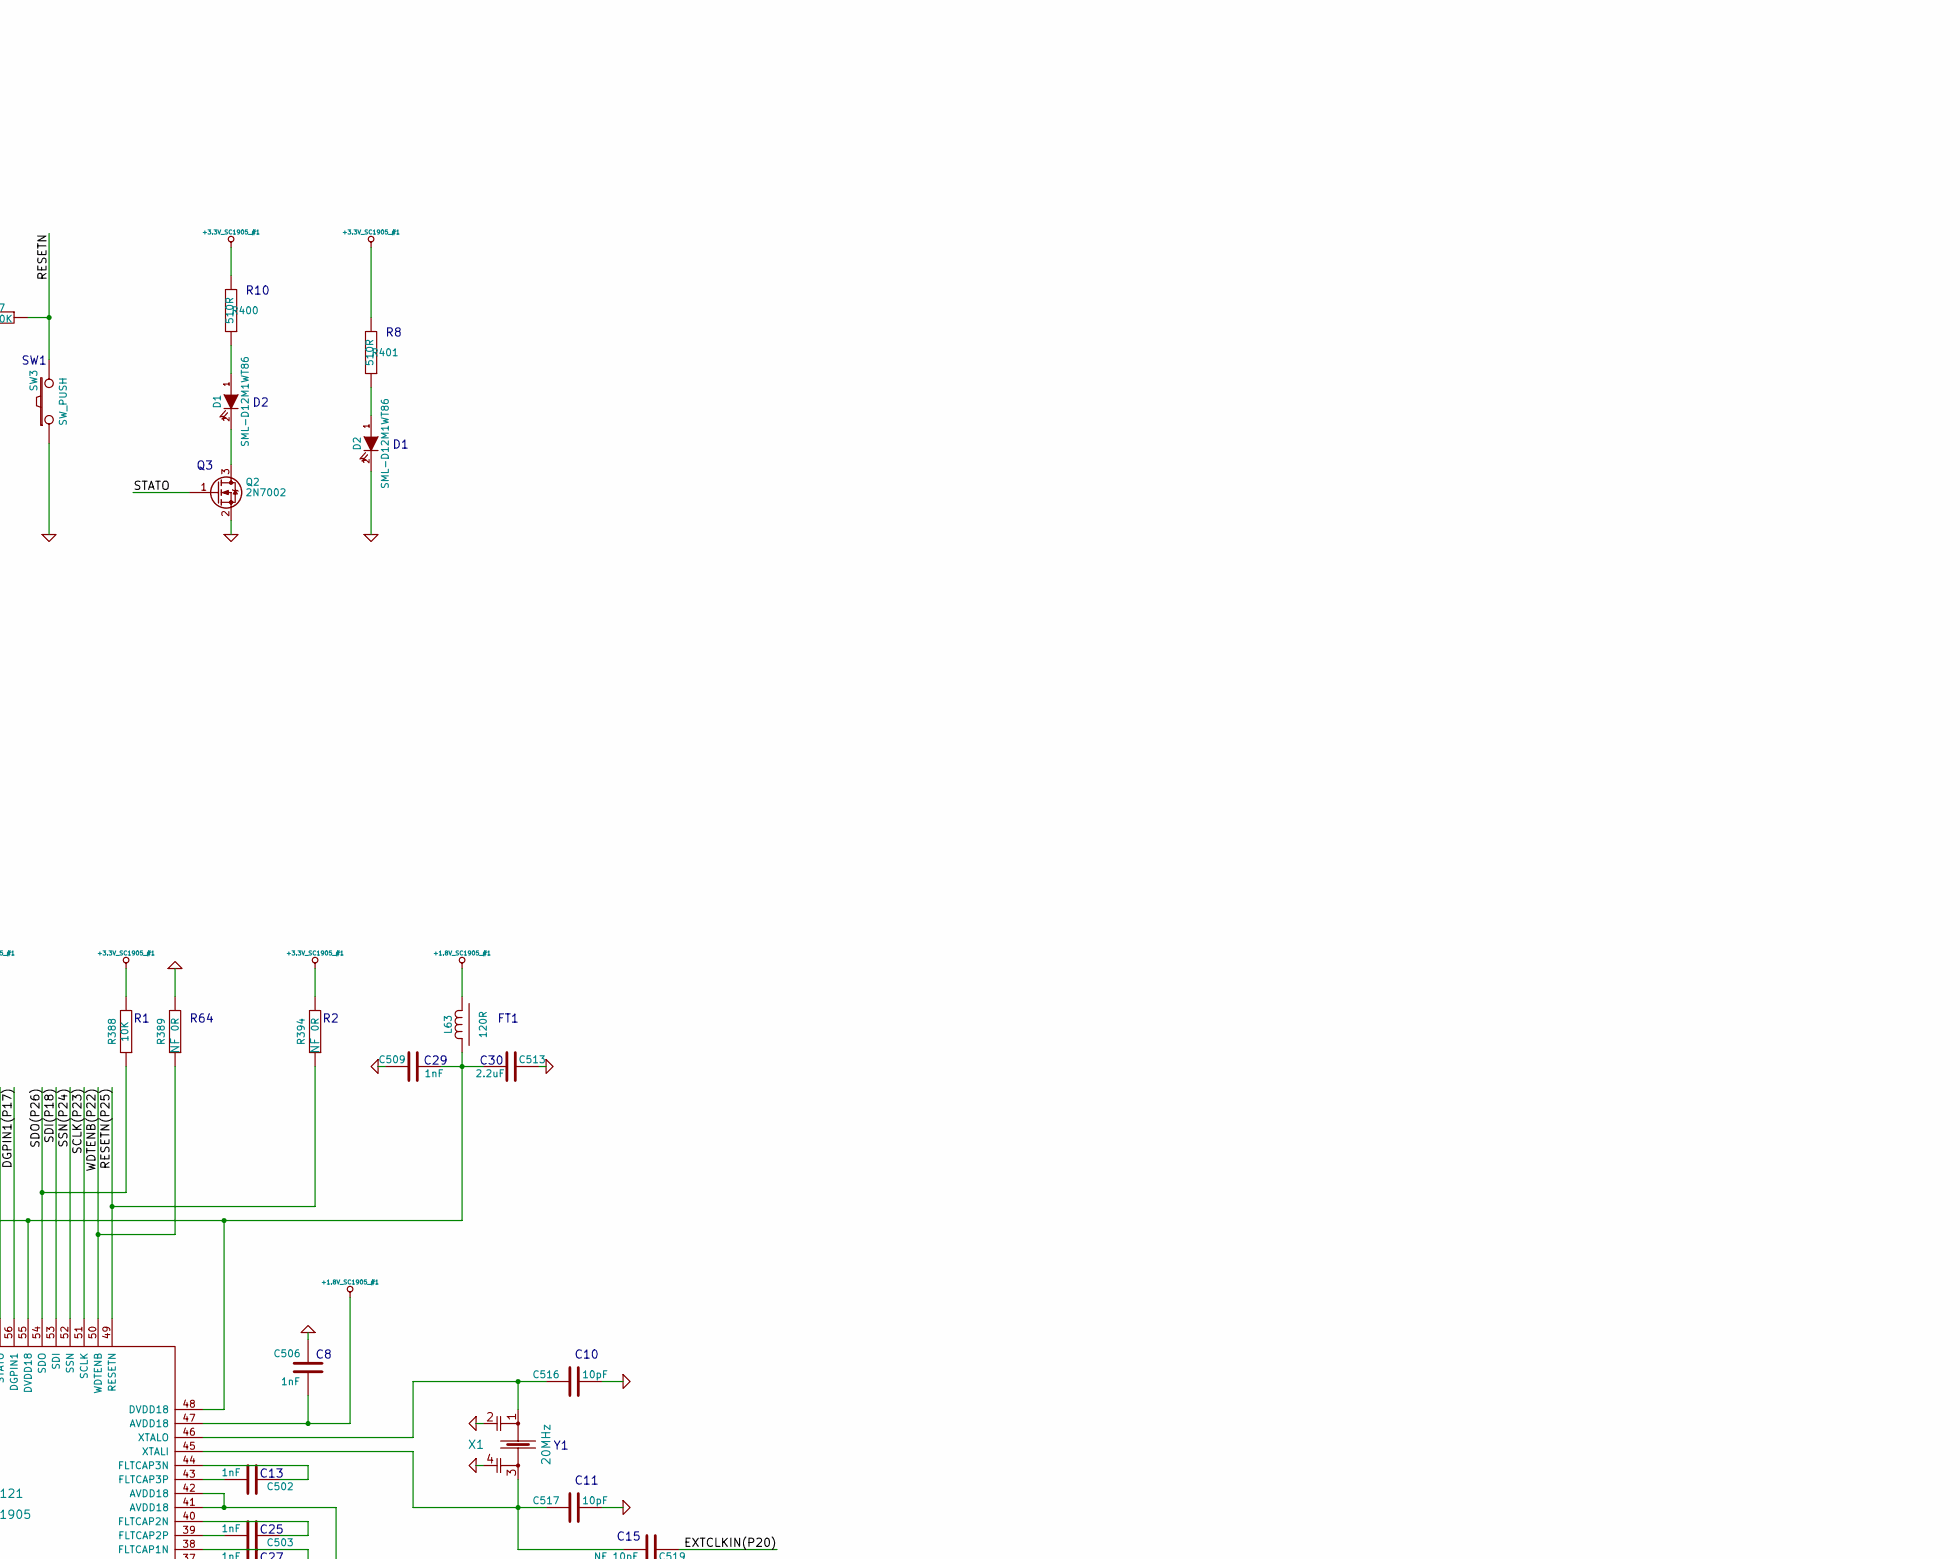
[picture p107: schematic SC1905_1.sch, part in row 1, column 2]

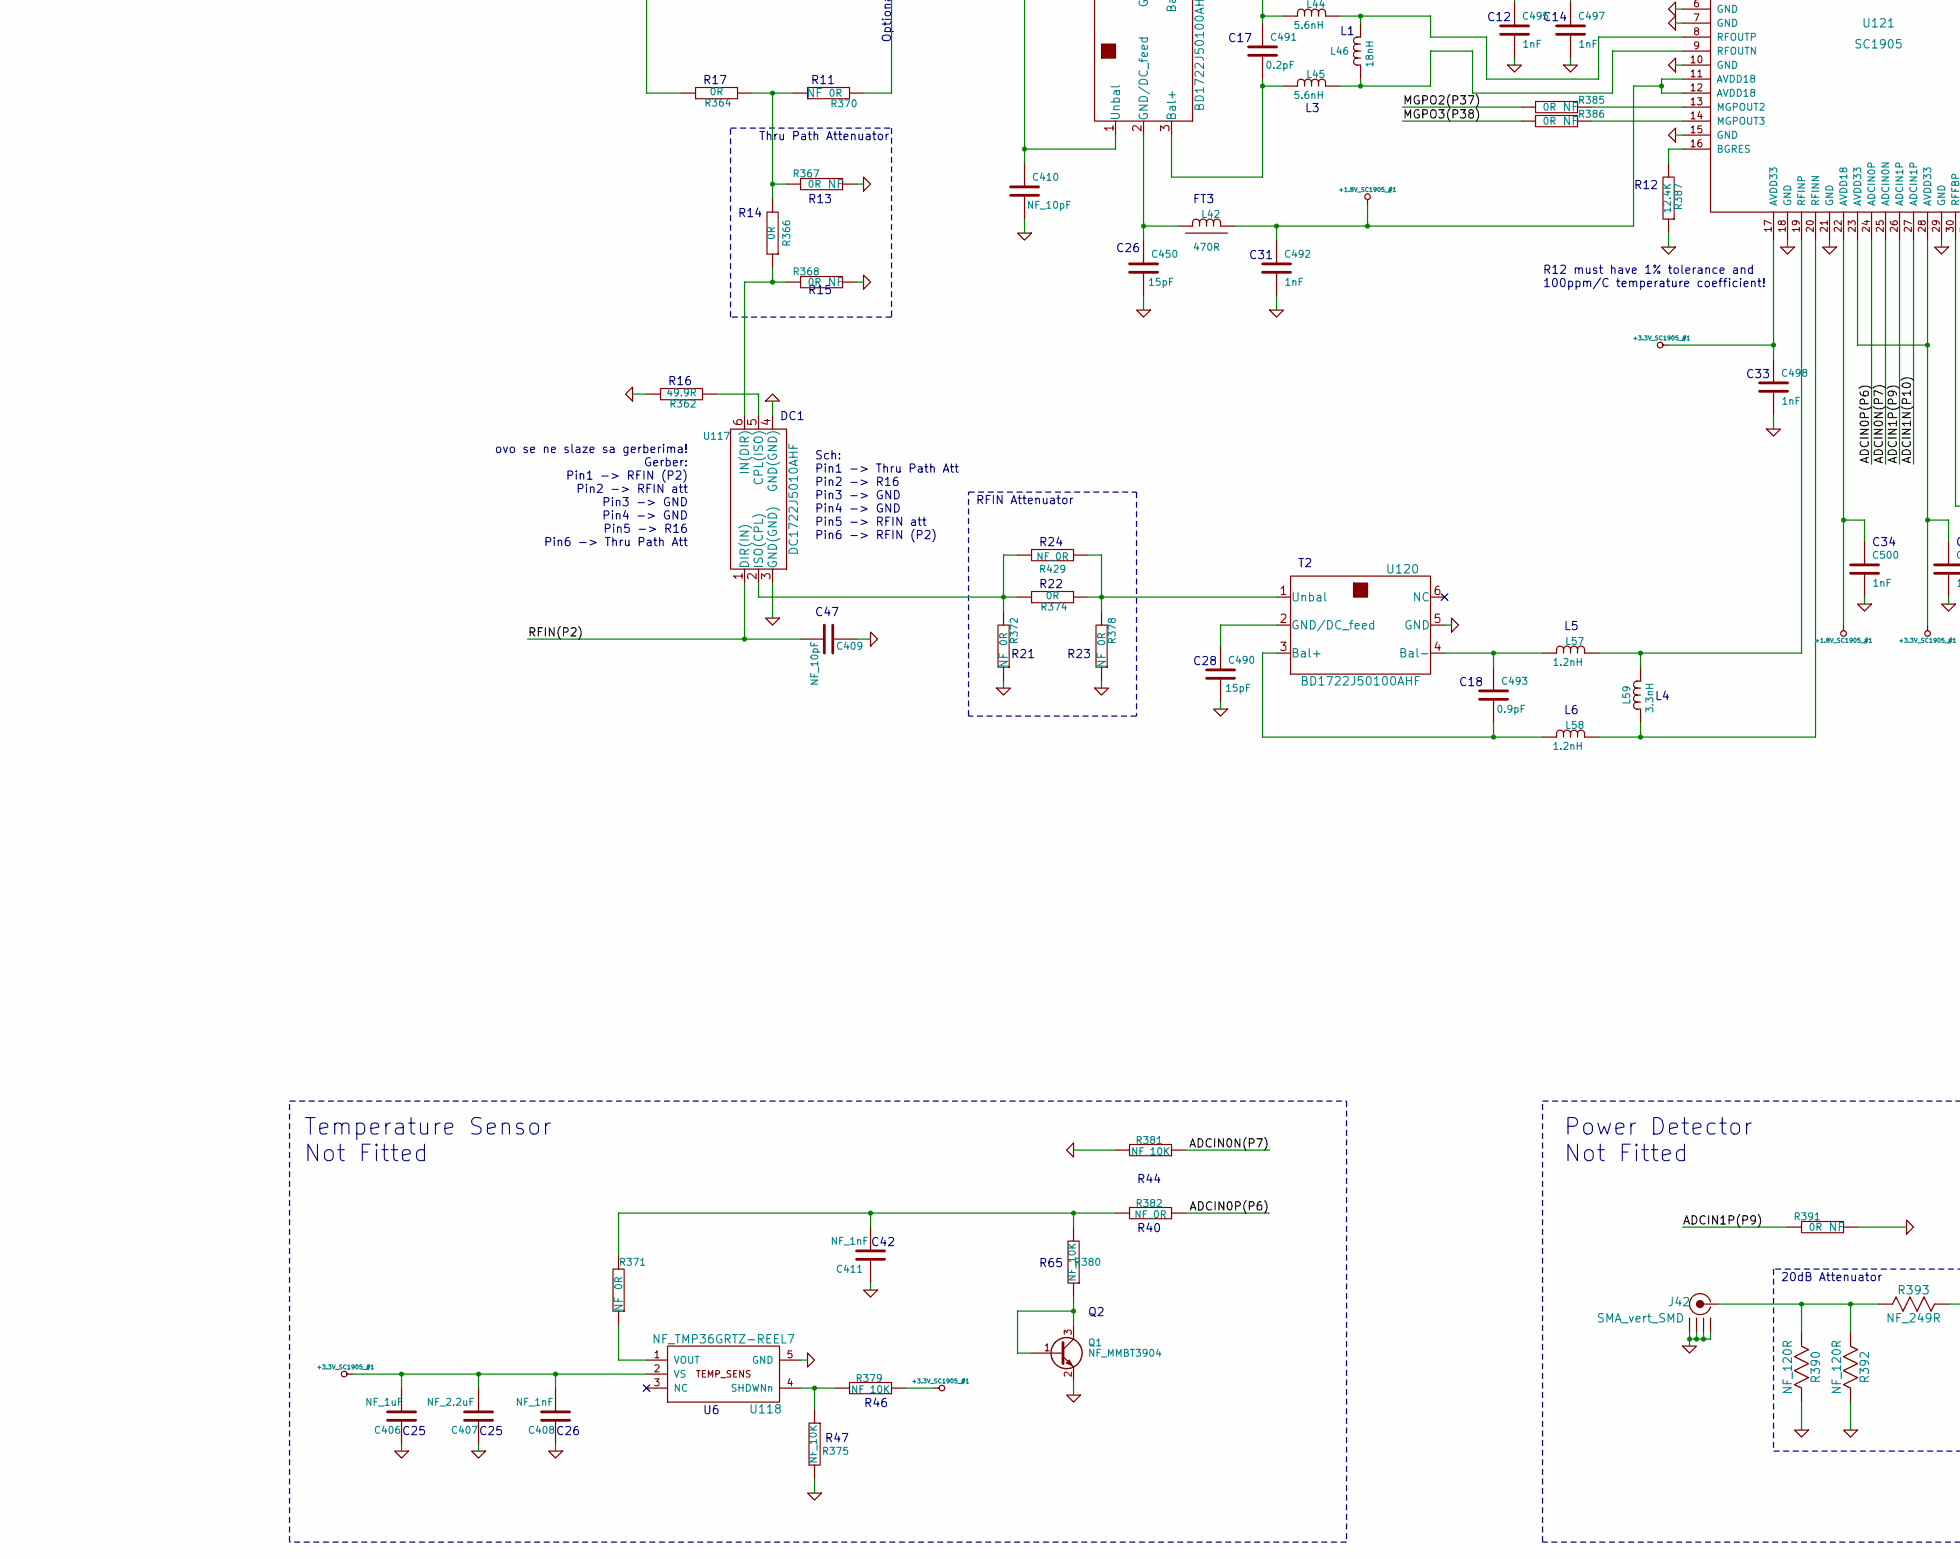
[picture p108: schematic SC1905_1.sch, part in row 2, column 1]

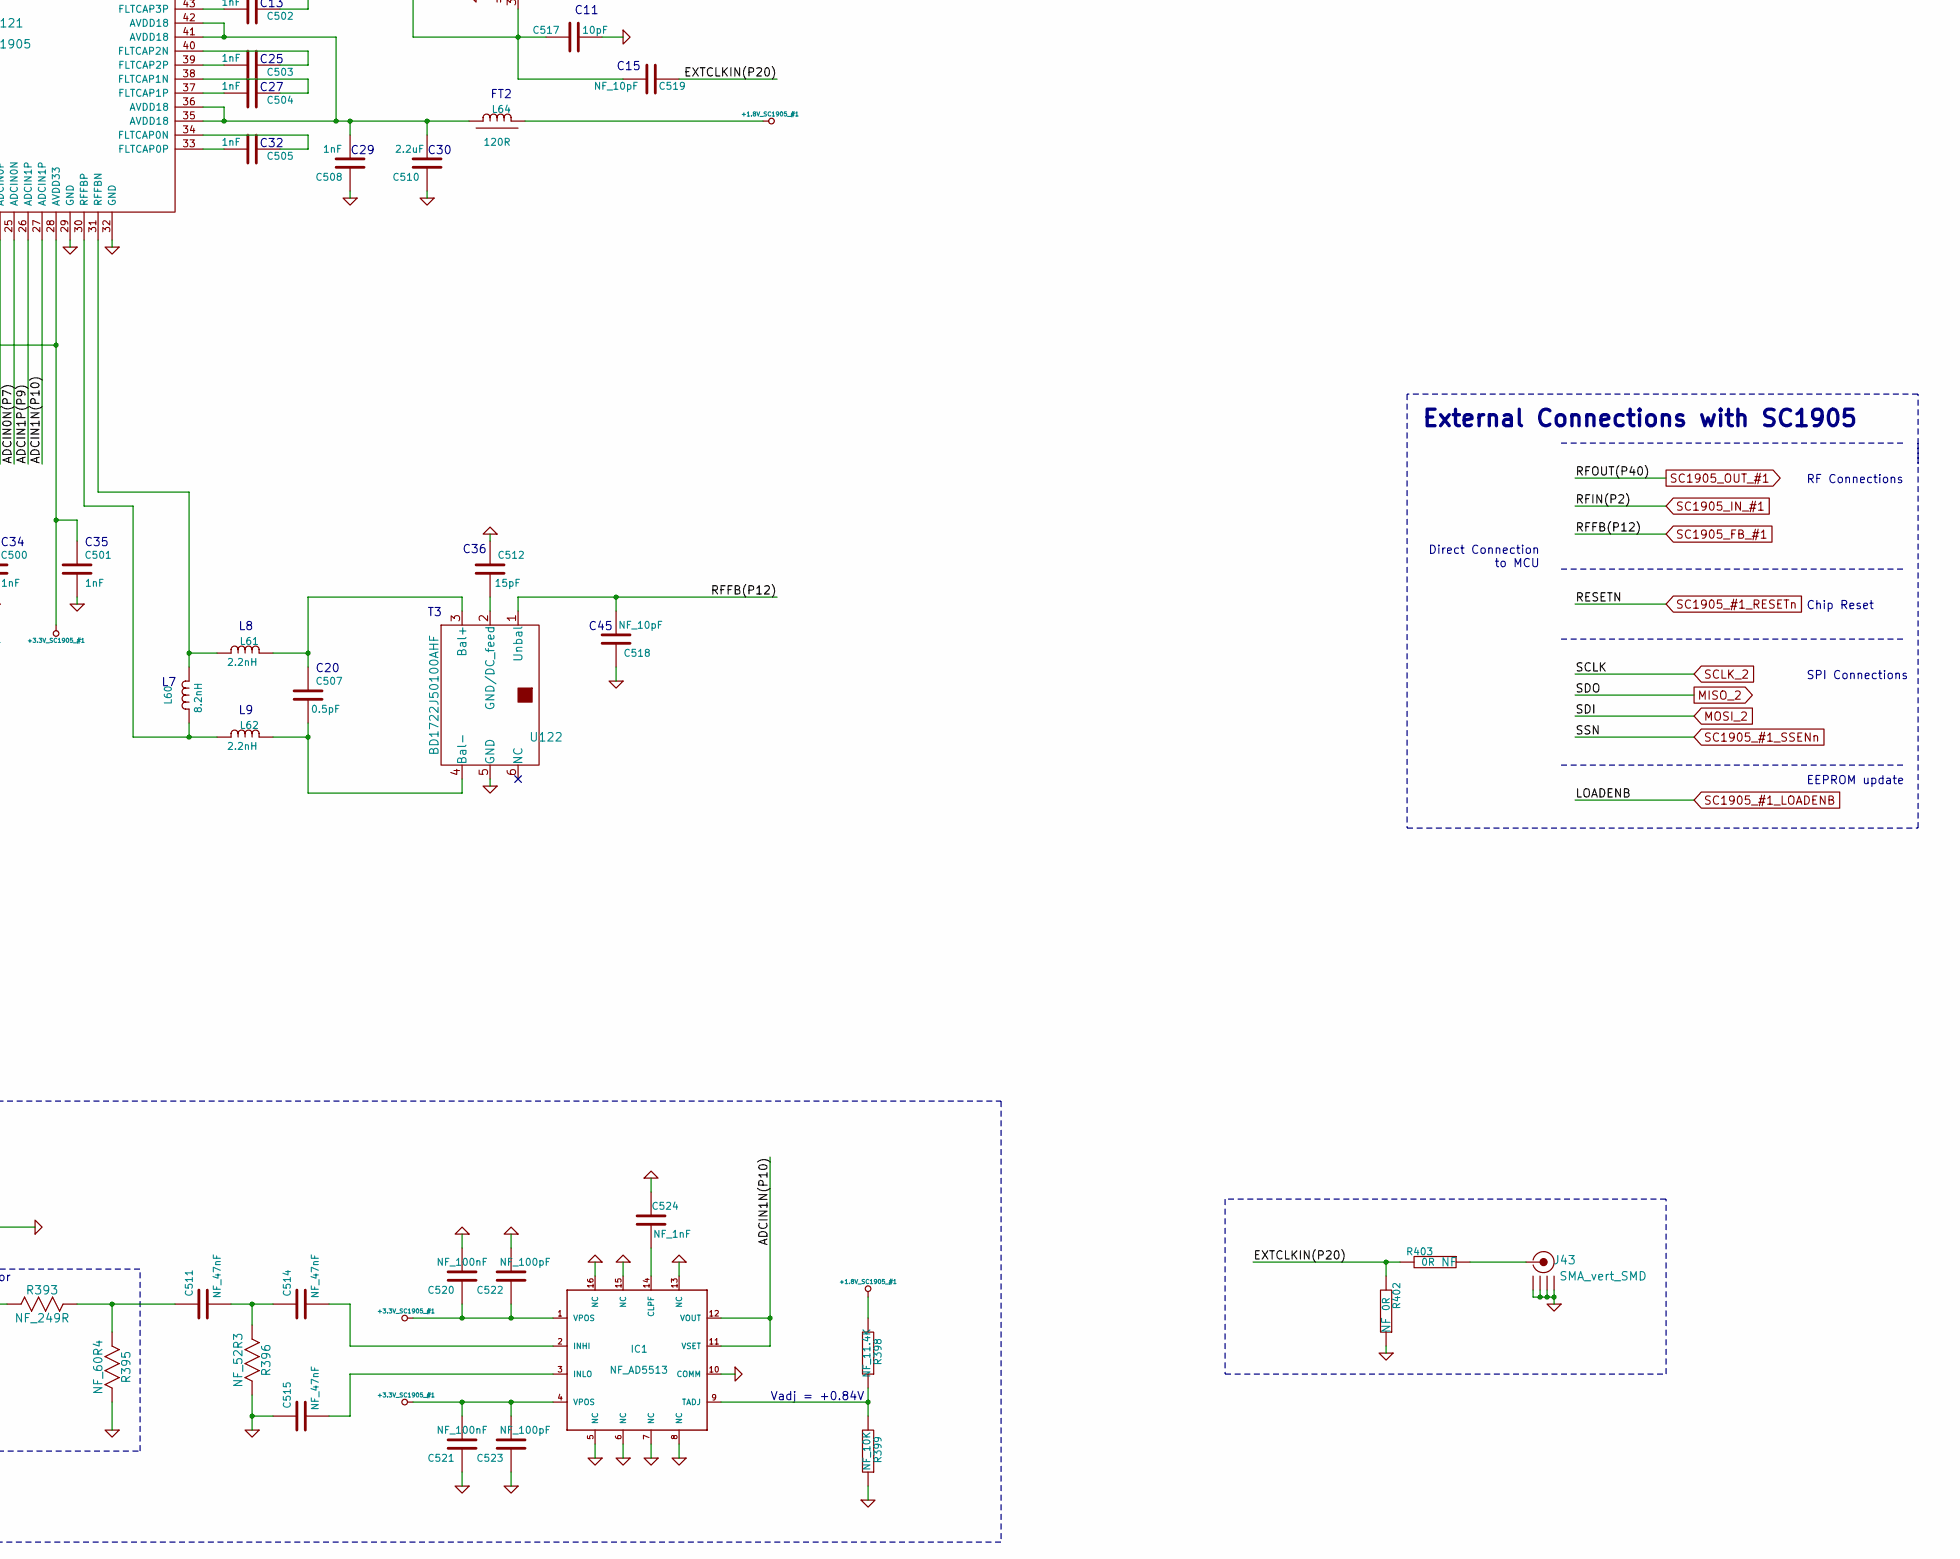
[picture p109: schematic SC1905_1.sch, part in row 2, column 2]

Parts:
C397, C398, C492, C495, C496, C497, C498, C499, C500, C501, C502, C503, C504, C505, C506, C508, C509: 1nF_0402_GRM1555C1H102JA01D; SMD0402; Manufacturer Part Number GRM1555C1H102JA01D
C399, C400, C403, C404, C405, C409, C410, C518, C519: NF_10pF_0402_GJM1555C1H100GB01D; SMD0402; Manufacturer Part Number GJM1555C1H100GB01D
C406: NF_1uF_0603_GRM188R61A105KA61D; SMD0603; Manufacturer Part Number GRM188R61A105KA61D
C407: NF_2.2uF_0603_GRM188R71A225KE15J; SMD0603; Manufacturer Part Number GRM188R71A225KE15J
C408, C411, C524: NF_1nF_0402_GRM1555C1H102JA01D; SMD0402; Manufacturer Part Number GRM1555C1H102JA01D
C450, C490, C512: 15pF_0402_GJM1555C1H150JB01D; SMD0402; Manufacturer Part Number GJM1555C1H150JB01D
C491: 0.2pF_0402_GJM1555C1HR20BB01D; SMD0402; Manufacturer Part Number GJM1555C1HR20BB01D
C493: 0.9pF_0402_GJM1555C1HR90BB01D; SMD0402; Manufacturer Part Number GJM1555C1HR90BB01D
C494, C510, C513: 2.2uF_0603_GRM188R71A225KE15J; SMD0603; Manufacturer Part Number GRM188R71A225KE15J
C507: 0.5pF_0402_GJM1555C1HR50BB01D; SMD0402; Manufacturer Part Number GJM1555C1HR50BB01D
C511, C514, C515: NF_47nF_0402_GCM155R71H473KE02D; SMD0402; Manufacturer Part Number GCM155R71H473KE02D
C516, C517: 10pF_0402_GJM1555C1H100GB01D; SMD0402; Manufacturer Part Number GJM1555C1H100GB01D
C520, C521: NF_100nF_0402_GRM155R71C104KA88J; SMD0402; Manufacturer Part Number GRM155R71C104KA88J
C522, C523: NF_100pF_0402_GRM1555C1H101JA01D; SMD0402; Manufacturer Part Number GRM1555C1H101JA01D
D1, D2: LED0603_GREEN; LED_0603; Manufacturer Part Number SML-D12M1WT86
IC1: NF_AD5513; AD5513; Manufacturer Part Number ADL5513ACPZ-R7
J42, J43: SMA_vert_SMD; Manufacturer Part Number 0732511352
L42: 470R_0402_BLM15BD471SN1D; SMD0402; Manufacturer Part Number BLM15BD471SN1D
L44, L45: 5.6nH_0402_HK10055N6S-T; SMD0402; Manufacturer Part Number HK10055N6S-T
L46: 18nH_0402_HK100518NJ-T; SMD0402; Manufacturer Part Number HK100518NJ-T
L57, L58: 1.2nH_0402_HK10051N2S-T; SMD0402; Manufacturer Part Number HK10051N2S-T
L59: 3.3nH_0402_HK10053N3S-T; SMD0402; Manufacturer Part Number HK10053N3S-T
L60: 8.2nH_0402_HK10058N2J-T; SMD0402; Manufacturer Part Number HK10058N2J-T
L61, L62: 2.2nH_0402_HK10052N2S-T; SMD0402; Manufacturer Part Number HK10052N2S-T
L63, L64: 120R_0603_BLM18AG121SN1D; SMD0603; Manufacturer Part Number BLM18AG121SN1D
Q1: NF_MMBT3904; MMBT3904; Manufacturer Part Number MMBT3904
Q2: 2N7002; SOT-23; Manufacturer PN 2N7002
R349, R350, R351, R352, R353, R354, R355, R356, R357, R358, R359, R360, R375, R379, R380, R381, R397, R399: NF_10K_0402; SMD0402
R361, R362: 49.9R_0402_ERJ-U02F49R9X; SMD0402; Manufacturer Part Number ERJ-U02F49R9X
R363, R364, R366, R373, R374: 0R_0402_RC0402JR-070RL; SMD0402; Manufacturer Part Number RC0402JR-070RL
R367, R368, R369, R370, R371, R372, R376, R377, R378, R383, R384, R385, R386, R389, R391, R394, R402, R403: 0R_0402_NF; SMD0402; Manufacturer Part Number RC0402JR-070RL
R382, R429: NF_0R_0402_RCS04020000Z0ED; SMD0402; Manufacturer Part Number RCS04020000Z0ED
R387: 12.4K_0402_ERJ-2RKF1242X; SMD0402; Manufacturer Part Number ERJ-2RKF1242X
R388: 10K_0402_Yageo; SMD0402; Manufacturer Part Number RC0402JR-7D10KL
R390, R392: NF_120R_0805_Panasonic; SMD0805; Manufacturer Part Number ERJ-P06J121V
R393: NF_249R_0603_CRCW0603249RFKEAHP; SMD0603; Manufacturer Part Number CRCW0603249RFKEAHP
R395: NF_60R4_0603_Yageo; SMD0603; Manufacturer Part Number RC0603FR-0760R4L
R396: NF_52R3_0603_Yageo; SMD0603; Manufacturer Part Number RC0603FR-0752R3L
R398: NF_11.4K_0402_RT0402BRE0711K4L; SMD0402; Manufacturer Part Number RT0402BRE0711K4L
R400, R401: 510R_0402_RC0402JR-07510RL; SMD0402; Manufacturer Part Number RC0402JR-07510RL
SW3: SW_PUSH; B3U-1000P; Manufacturer Part Number B3U-1000P
U90: NF_LMV324QDRG4; LMV324QDRG4; Manufacturer Part Number LMV324QDRG4
U92: BDCN-7-25+; Manufacturer Part Number BDCN-7-25+
U116: XDL15-2-020S; Manufacturer Part Number XDL15-2-020S
U117: DC1722J5010AHF; Manufacturer Part Number DC1722J5010AHF
U118: NF_TMP36GRTZ-REEL7; TMP36GRTZ-REEL7; Manufacturer Part Number TMP36GRTZ-REEL7
U119, U120, U122: BD1722J50100AHF; Manufacturer Part Number BD1722J50100AHF
U121: SC1905; SC1905A-00A00; Manufacturer Part Number SC1905A-00A00
X1: 830108207209; Manufacturer Part Number 830108207209

Connections:
+1.8V_SC1905_#1: C492.1, C494.2, C495.1, C496.2, C500.1, C506.2, L42.1, L63.1, L64.1, R398.2, U121.1 (DVDD18), U121.4 (AVDD18), U121.11 (AVDD18), U121.12 (AVDD18), U121.22 (AVDD18), U121.47 (AVDD18)
+3.3V_SC1905_#1: C397.2, C398.2, C406.2, C407.2, C408.2, C497.1, C498.1, C499.2, C501.1, C520.1, C521.2, C522.1, C523.2, IC1.1 (VPOS), IC1.4 (VPOS), R379.1, R388.2, R394.2, R397.2, R400.2, R401.2, U90.4 (V+), U118.2 (VS), U121.5 (AVDD33), U121.17 (AVDD33), U121.23 (AVDD33), U121.28 (AVDD33), U121.58 (DVDD33)
ADCIN0N(P7): R381.1, U121.25 (ADCIN0N)
ADCIN0P(P6): R382.1, U121.24 (ADCIN0P)
ADCIN1N(P10): IC1.11 (VSET), IC1.12 (VOUT), U121.27 (ADCIN1P)
ADCIN1P(P9): R391.2, U121.26 (ADCIN1P)
DGPIN0(P15): U121.63 (DGPIN0)
DGPIN1(P17): U121.56 (DGPIN1)
EXTCLKIN(P20): C519.1, R402.2, R403.2
GND: C397.1, C398.1, C399.1, C400.1, C403.1, C404.1, C405.1, C406.1, C407.1, C408.1, C409.1, C410.2, C411.1, C450.2, C490.2, C492.2, C494.1, C495.2, C496.1, C497.2, C498.2, C499.1, C500.2, C501.2, C506.1, C508.1, C509.1, C510.1, C512.1, C513.1, C515.1, C516.2, C517.2, C518.1, C520.2, C521.1, C522.2, C523.1, C524.1, D2.2 (K), IC1.5 (NC), IC1.6 (NC), IC1.7 (NC), IC1.8 (NC), IC1.10 (COMM), IC1.13 (NC), IC1.15 (NC), IC1.16 (NC), J42.2 (GND1), J42.3 (GND2), J42.4 (GND3), J42.5 (GND4), J43.2 (GND1), J43.3 (GND2), J43.4 (GND3), J43.5 (GND4), Q1.2 (E), Q2.2 (S), R349.2, R354.2, R355.2, R360.2, R361.1, R362.1, R367.1, R368.1, R372.1, R375.2, R376.1, R377.1, R378.1, R381.2, R387.1, R389.2, R390.2, R391.1, R392.2, R395.2, R396.2, R399.1, R402.1, SW3.1, U90.11 (V-), U92.2 (GND), U92.5 (GND), U117.3 (GND(GND)), U117.4 (GND(GND)), U118.5 (GND), U119.5 (GND), U120.5 (GND), U121.6 (GND), U121.7 (GND), U121.10 (GND), U121.15 (GND), U121.18 (GND), U121.21 (GND), U121.29 (GND), U121.32 (GND), U121.65, U122.5 (GND), X1.2, X1.4
MGPO0(P34): R358.1, R383.2, U90.10 (+INC)
MGPO1(P35): R352.1, R384.2, U90.5 (+INB)
MGPO2(P37): R357.1, R385.2, U90.12 (+IND)
MGPO3(P38): R351.1, R386.2, U90.3 (+INA)
MISO_2: R388.1, U121.54 (SDO)
MOSI_2: U121.53 (SDI)
unnamed: C410.1, R373.1, R377.2, U119.1 (Unbal)
unnamed: C411.2, R371.2, R380.2, R382.2
unnamed: C450.1, L42.2, U119.2 (GND/DC_feed)
unnamed: C490.1, U120.2 (GND/DC_feed)
unnamed: C491.1, L44.2, U119.4 (Bal-)
unnamed: C491.2, L45.2, U119.3 (Bal+)
unnamed: C493.1, L57.2, U120.4 (Bal-)
unnamed: C493.2, L58.2, U120.3 (Bal+)
unnamed: C502.1, U121.44 (FLTCAP3N)
unnamed: C502.2, U121.43 (FLTCAP3P)
unnamed: C503.1, U121.40 (FLTCAP2N)
unnamed: C503.2, U121.39 (FLTCAP2P)
unnamed: C504.1, U121.38 (FLTCAP1N)
unnamed: C504.2, U121.37 (FLTCAP1P)
unnamed: C505.1, U121.34 (FLTCAP0N)
unnamed: C505.2, U121.33 (FLTCAP0P)
unnamed: C507.1, L61.1, U122.3 (Bal+)
unnamed: C507.2, L62.1, U122.4 (Bal-)
unnamed: C508.2, C510.2, L64.2, U121.35 (AVDD18), U121.36 (AVDD18), U121.41 (AVDD18), U121.42 (AVDD18)
unnamed: C509.2, C513.2, L63.2, U121.48 (DVDD18), U121.55 (DVDD18), U121.59 (DVDD18), U121.64 (DVDD18)
unnamed: C511.1, R393.2, R395.1
unnamed: C511.2, C514.1, R396.1
unnamed: C512.2, U122.2 (GND/DC_feed)
unnamed: C514.2, IC1.2 (INHI)
unnamed: C515.2, IC1.3 (INLO)
unnamed: C516.1, U121.46 (XTALO), X1.1
unnamed: C517.1, C519.2, U121.45 (XTALI), X1.3
unnamed: C524.2, IC1.14 (CLPF)
unnamed: D1.1 (A), R400.1
unnamed: D1.2 (K), Q2.3 (D)
unnamed: D2.1 (A), R401.1
unnamed: IC1.9 (TADJ), R398.1, R399.2
unnamed: J42.1 (RF), R390.1, R392.1, R393.1
unnamed: J43.1 (RF), R403.1
unnamed: L44.1, L46.1, U121.8 (RFOUTP)
unnamed: L45.1, L46.2, U121.9 (RFOUTN)
unnamed: L57.1, L59.1, U121.19 (RFINP)
unnamed: L58.1, L59.2, U121.20 (RFINN)
unnamed: L60.1, L61.2, U121.31 (RFFBN)
unnamed: L60.2, L62.2, U121.30 (RFFBP)
unnamed: Q1.1 (B), Q1.3 (C), R380.1
unnamed: R349.1, R350.1, U90.2 (-INA)
unnamed: R353.1, R354.1, U90.6 (-INB)
unnamed: R355.1, R356.1, U90.13 (-IND)
unnamed: R359.1, R360.1, U90.9 (-INC)
unnamed: R361.2, U92.6 (CPL_FWR)
unnamed: R362.2, U117.5 (CPL(ISO))
unnamed: R363.1, U116.2
unnamed: R363.2, R369.1, U92.1 (IN)
unnamed: R364.1, U116.1
unnamed: R364.2, R366.2, R367.2, R370.1
unnamed: R366.1, R368.2, U117.6 (IN(DIR))
unnamed: R369.2, R370.2
unnamed: R371.1, U118.1 (VOUT)
unnamed: R372.2, R374.1, R429.2, U117.2 (ISO(CPL))
unnamed: R373.2, R376.2, U92.3 (CPL_REV)
unnamed: R374.2, R378.2, R429.1, U120.1 (Unbal)
unnamed: R375.1, R379.2, U118.4 (SHDWNn)
unnamed: R383.1, U121.2 (MGPOUT0)
unnamed: R384.1, U121.3 (MGPOUT1)
unnamed: R385.1, U121.13 (MGPOUT2)
unnamed: R386.1, U121.14 (MGPOUT3)
unnamed: R387.2, U121.16 (BGRES)
SC1905_#1_LOADENB: U121.60 (LOADENB)
SC1905_#1_RESETn: R394.1, R397.1, SW3.2, U121.49 (RESETN)
SC1905_#1_SSENn: U121.52 (SSN)
SC1905_FB_#1: C518.2, U122.1 (Unbal)
SC1905_IN_#1: C409.2, U117.1 (DIR(IN))
SC1905_OUT_#1: C405.2, U92.4 (OUT)
SCLK_2: U121.51 (SCLK)
STATO: Q2.1 (G), U121.57 (STATO)
VG0: C404.2, R358.2, R359.2, U90.8 (OUTC)
VG1: C400.2, R352.2, R353.2, U90.7 (OUTB)
VG2: C403.2, R356.2, R357.2, U90.14 (OUTD)
VG3: C399.2, R350.2, R351.2, U90.1 (OUTA)
WDTENB: R389.1, U121.50 (WDTENB)

Notes on the sheet:
C14
C12
R12
C17
C26
FT3
C31
C33
R27
R25
R26
RFOUT Attenuator
DC2
R10
C48
R8 R365 obrisan
R102
R17
R13
R15
R14
Thru Path Attenuator
R11
Optional RF Thru Path without Delay Line
DC1
R16
C47
R23
R21
R22
RFIN Attenuator
C18
C28
C34
C35
C20
C36
C45
C32
FT2
C29
C30
C27
C25
C13
C10
C11
C15
FT1
SW1
R12 must have 1% tolerance and 100ppm/C temperature coefficient!
R46
R47
R44
R65
C42
R40
Vadj = +0.84V
20dB Attenuator
Power Detector Not Fitted
Temperature Sensor Not Fitted
R64
R53
R54
R51
R57
R58
C38
R49
R56
R55
C37
R52
R60
R59
R50
C39
Buffers for MGPOUT 0-3 Not Fitted
Master Board
EVK1900 board
R24
External Connections with SC1905
RF Connections
SPI Connections
Chip Reset
Direct Connection to MCU
ovo se ne slaze sa gerberima! Gerber: Pin1 -> RFIN (P2) Pin2 -> RFIN att Pin3 -> GND Pin4 -> GND Pin5 -> R16 Pin6 -> Thru Path Att
Sch: Pin1 -> Thru Path Att Pin2 -> R16 Pin3 -> GND Pin4 -> GND Pin5 -> RFIN att Pin6 -> RFIN (P2)
NOT CONNECTED!
CONNECTED TO R389
EEPROM update
CONNECTED TO Q2
