myriadrf/LimeRFE-8001P/hardware/1v1/KiCAD/SC1905_2.sch

## KiCad design hardware/1v1/KiCAD/SC1905_2.sch (2023-10-04)

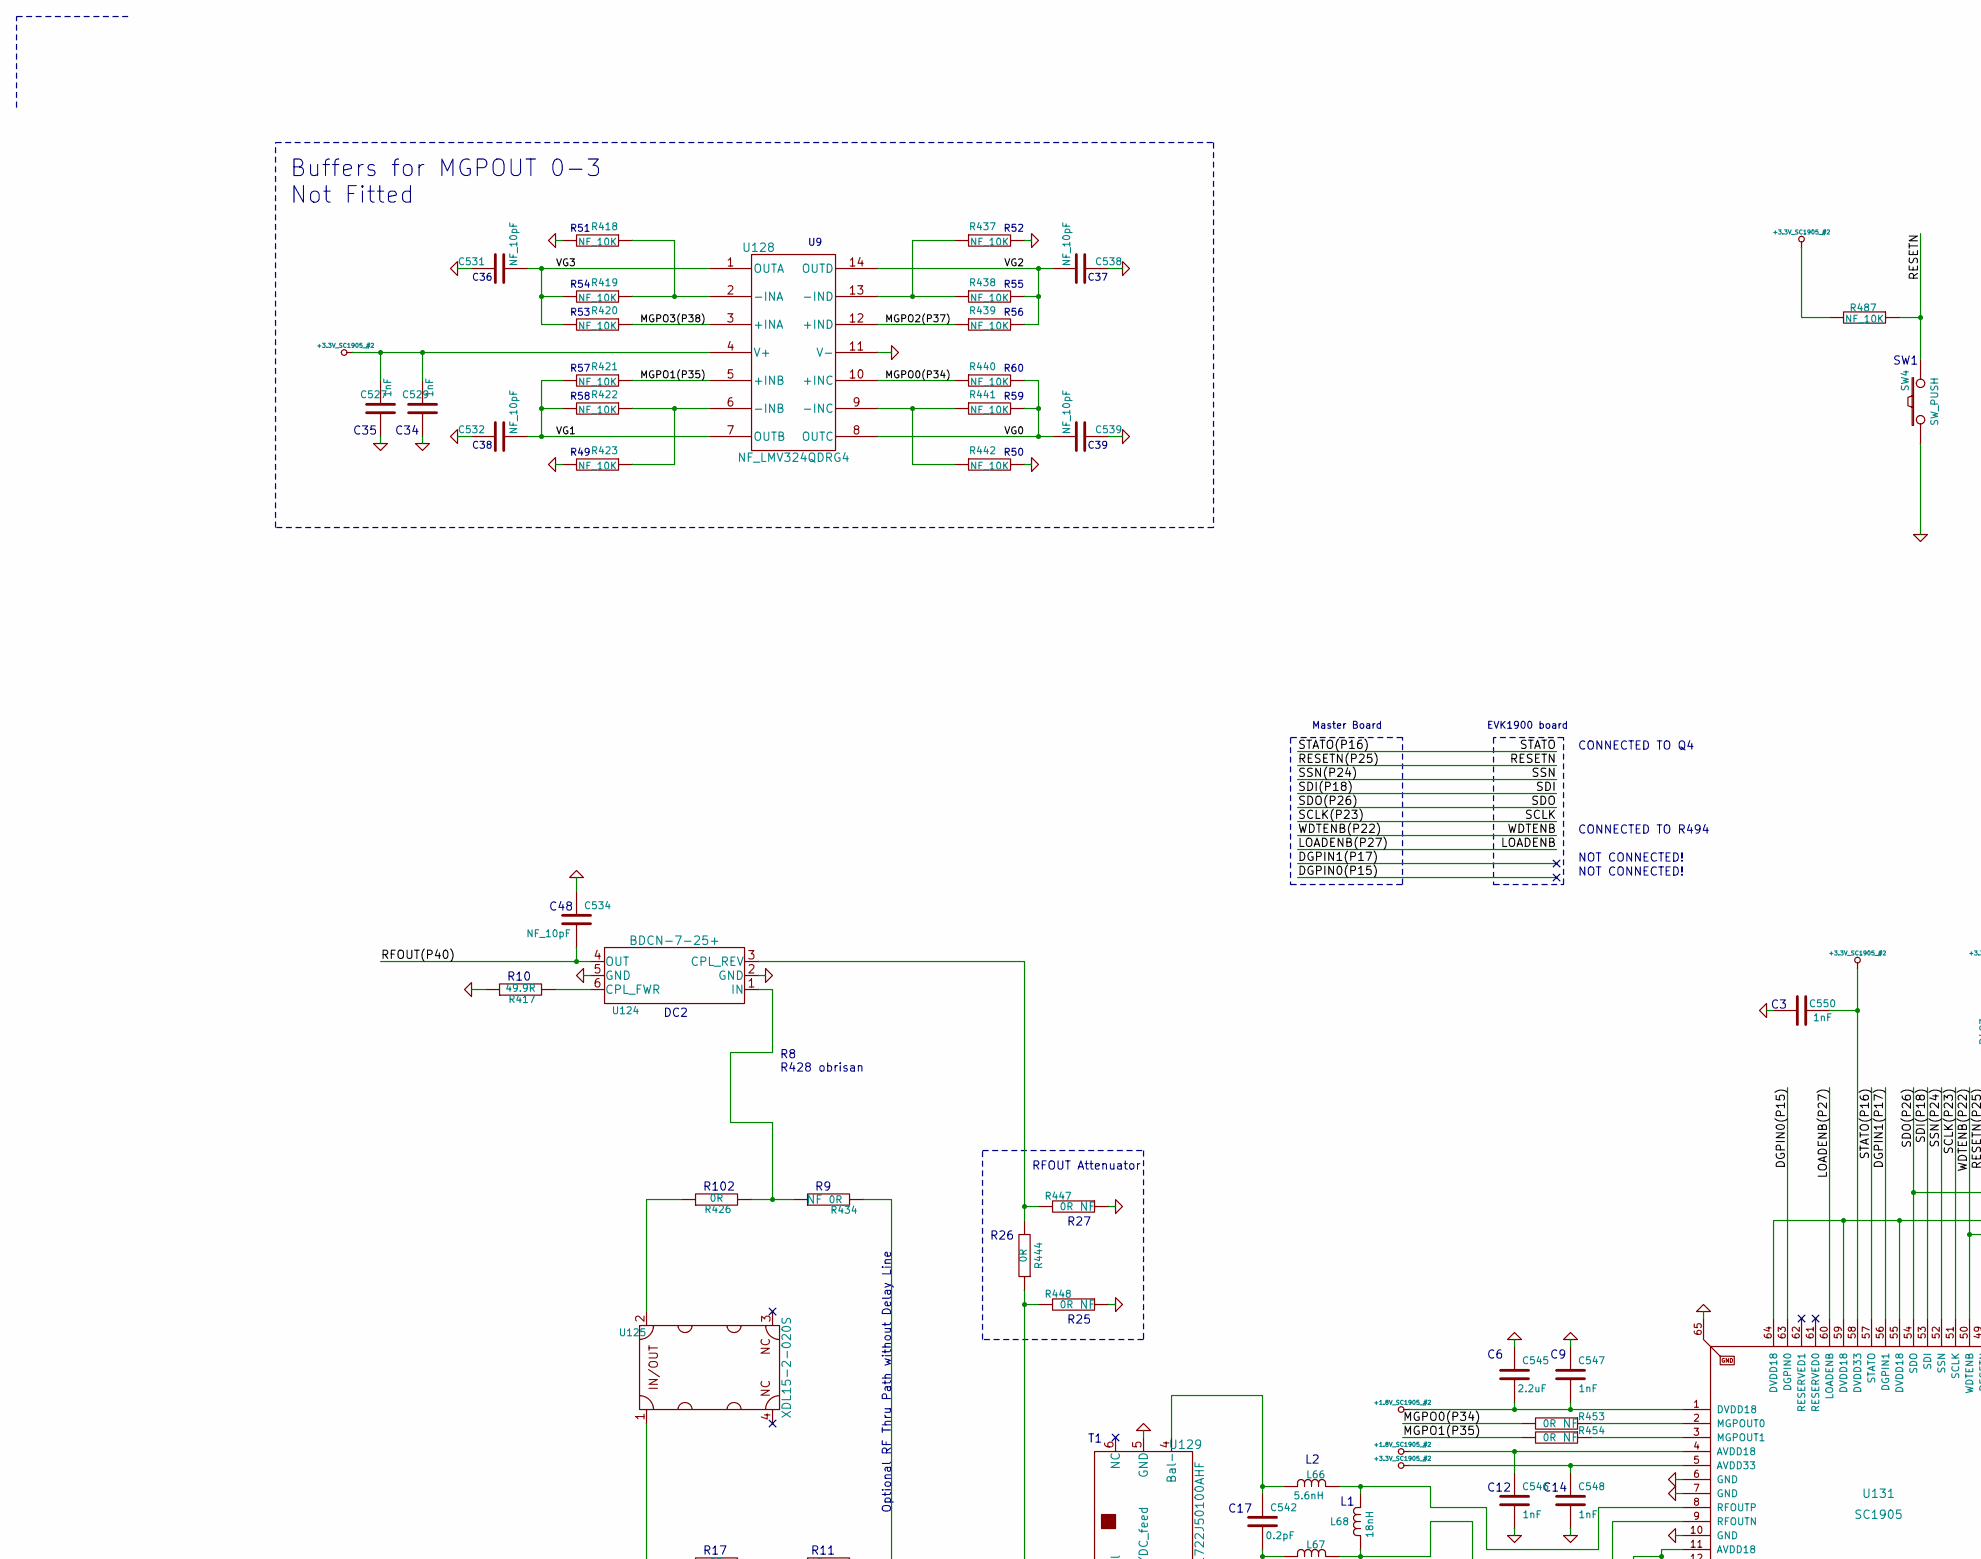
[picture p110: schematic SC1905_2.sch, part in row 1, column 1]

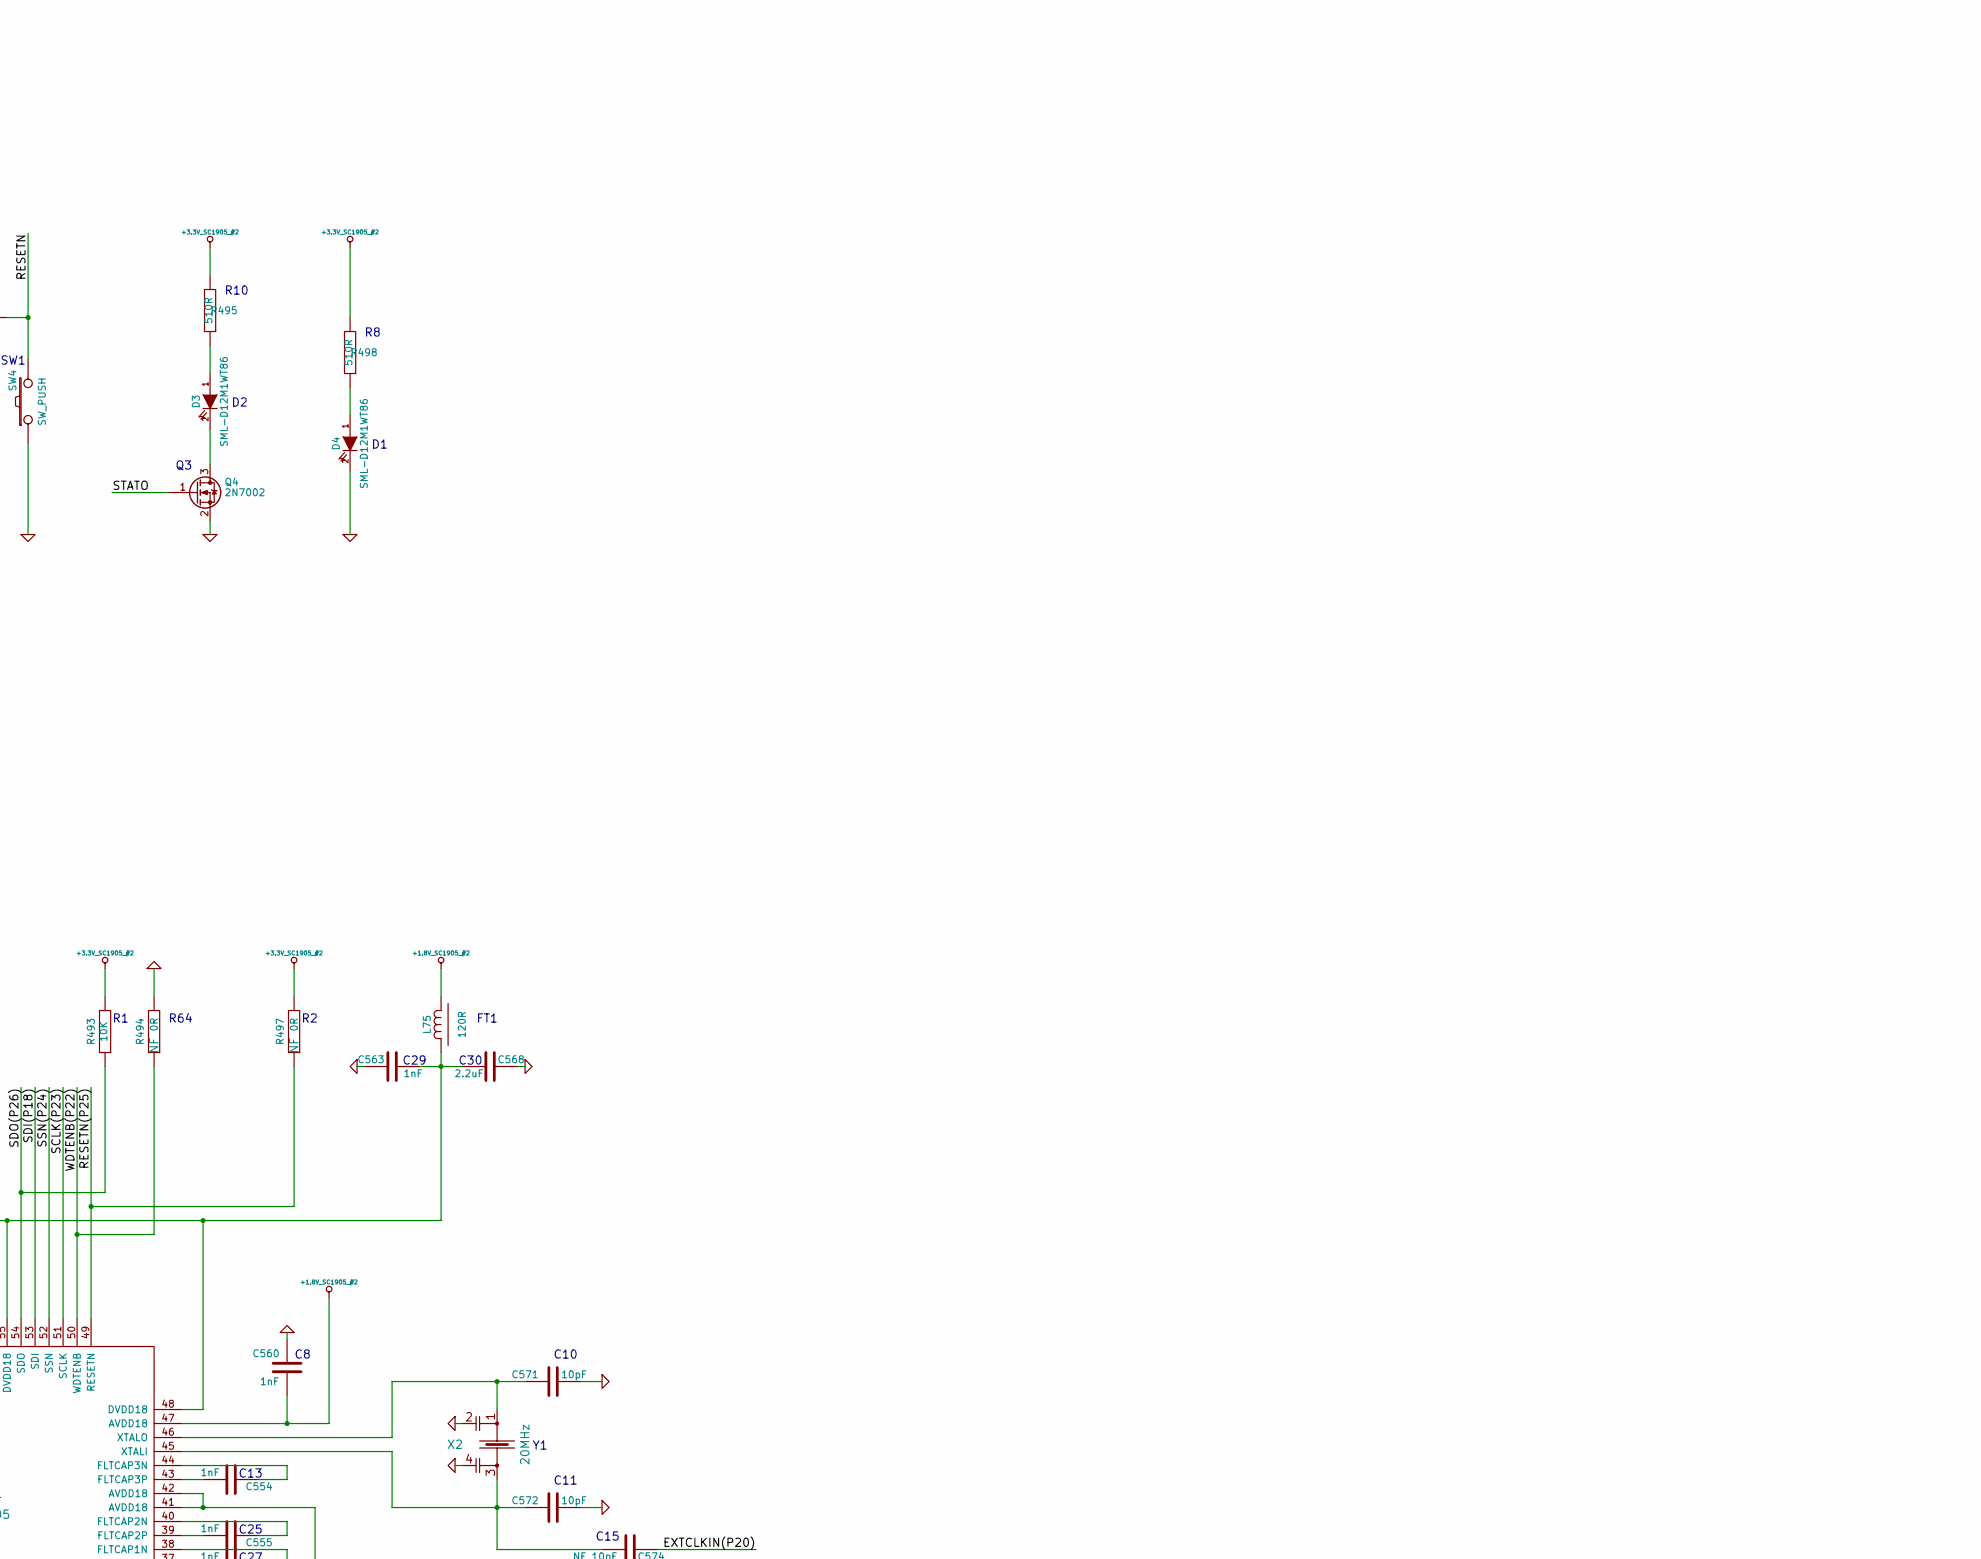
[picture p111: schematic SC1905_2.sch, part in row 1, column 2]

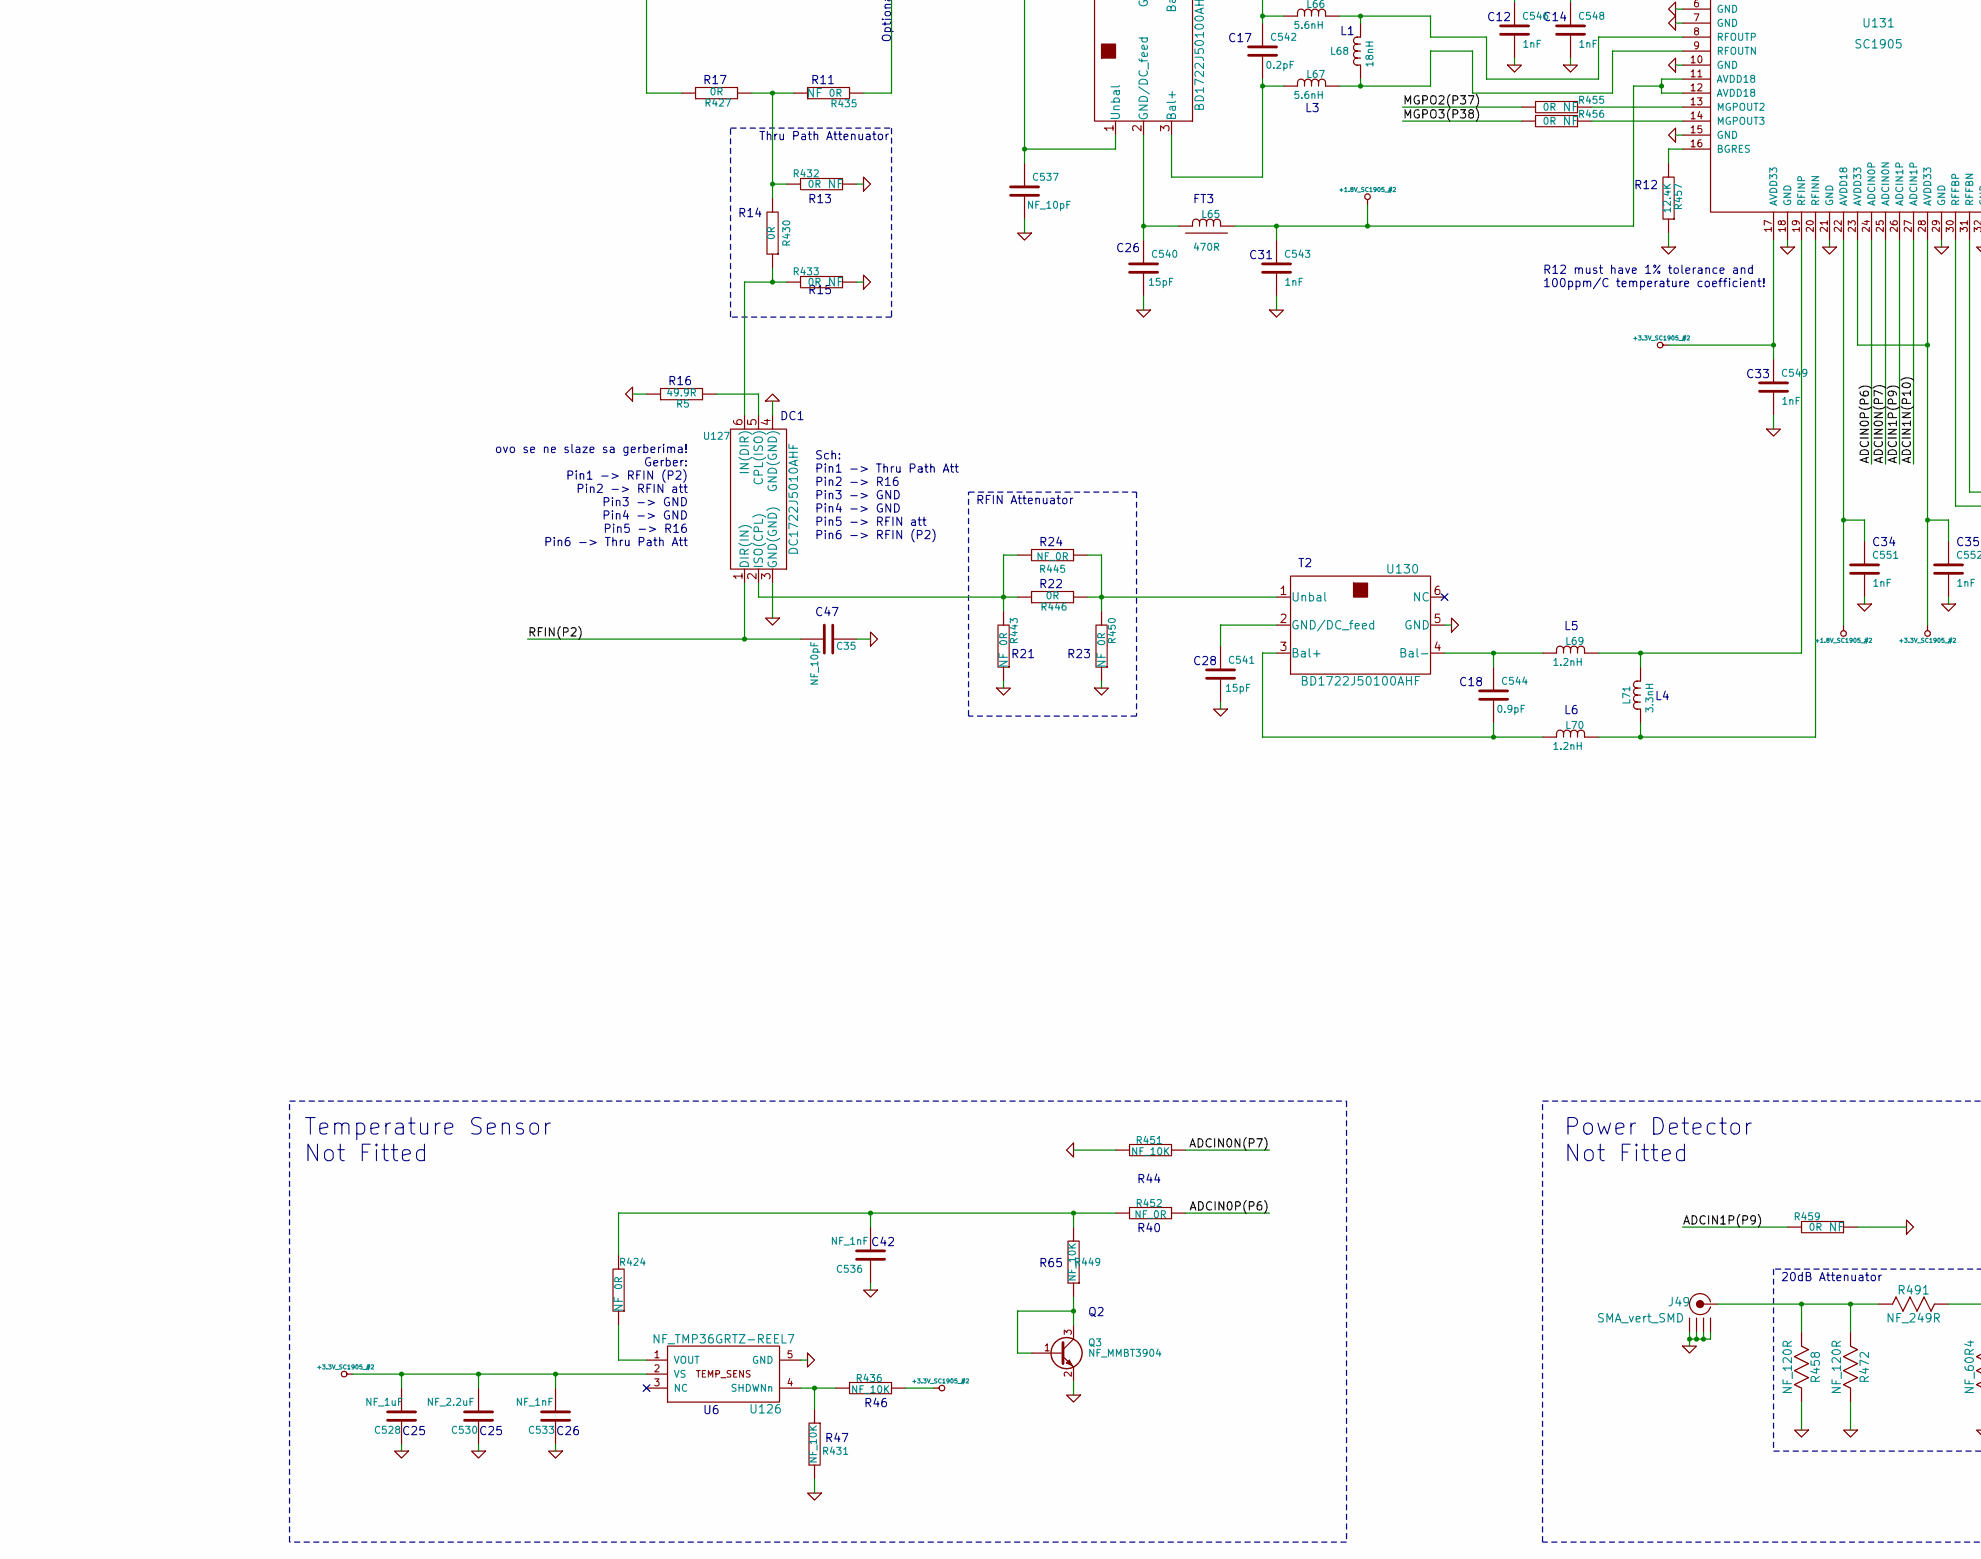
[picture p112: schematic SC1905_2.sch, part in row 2, column 1]

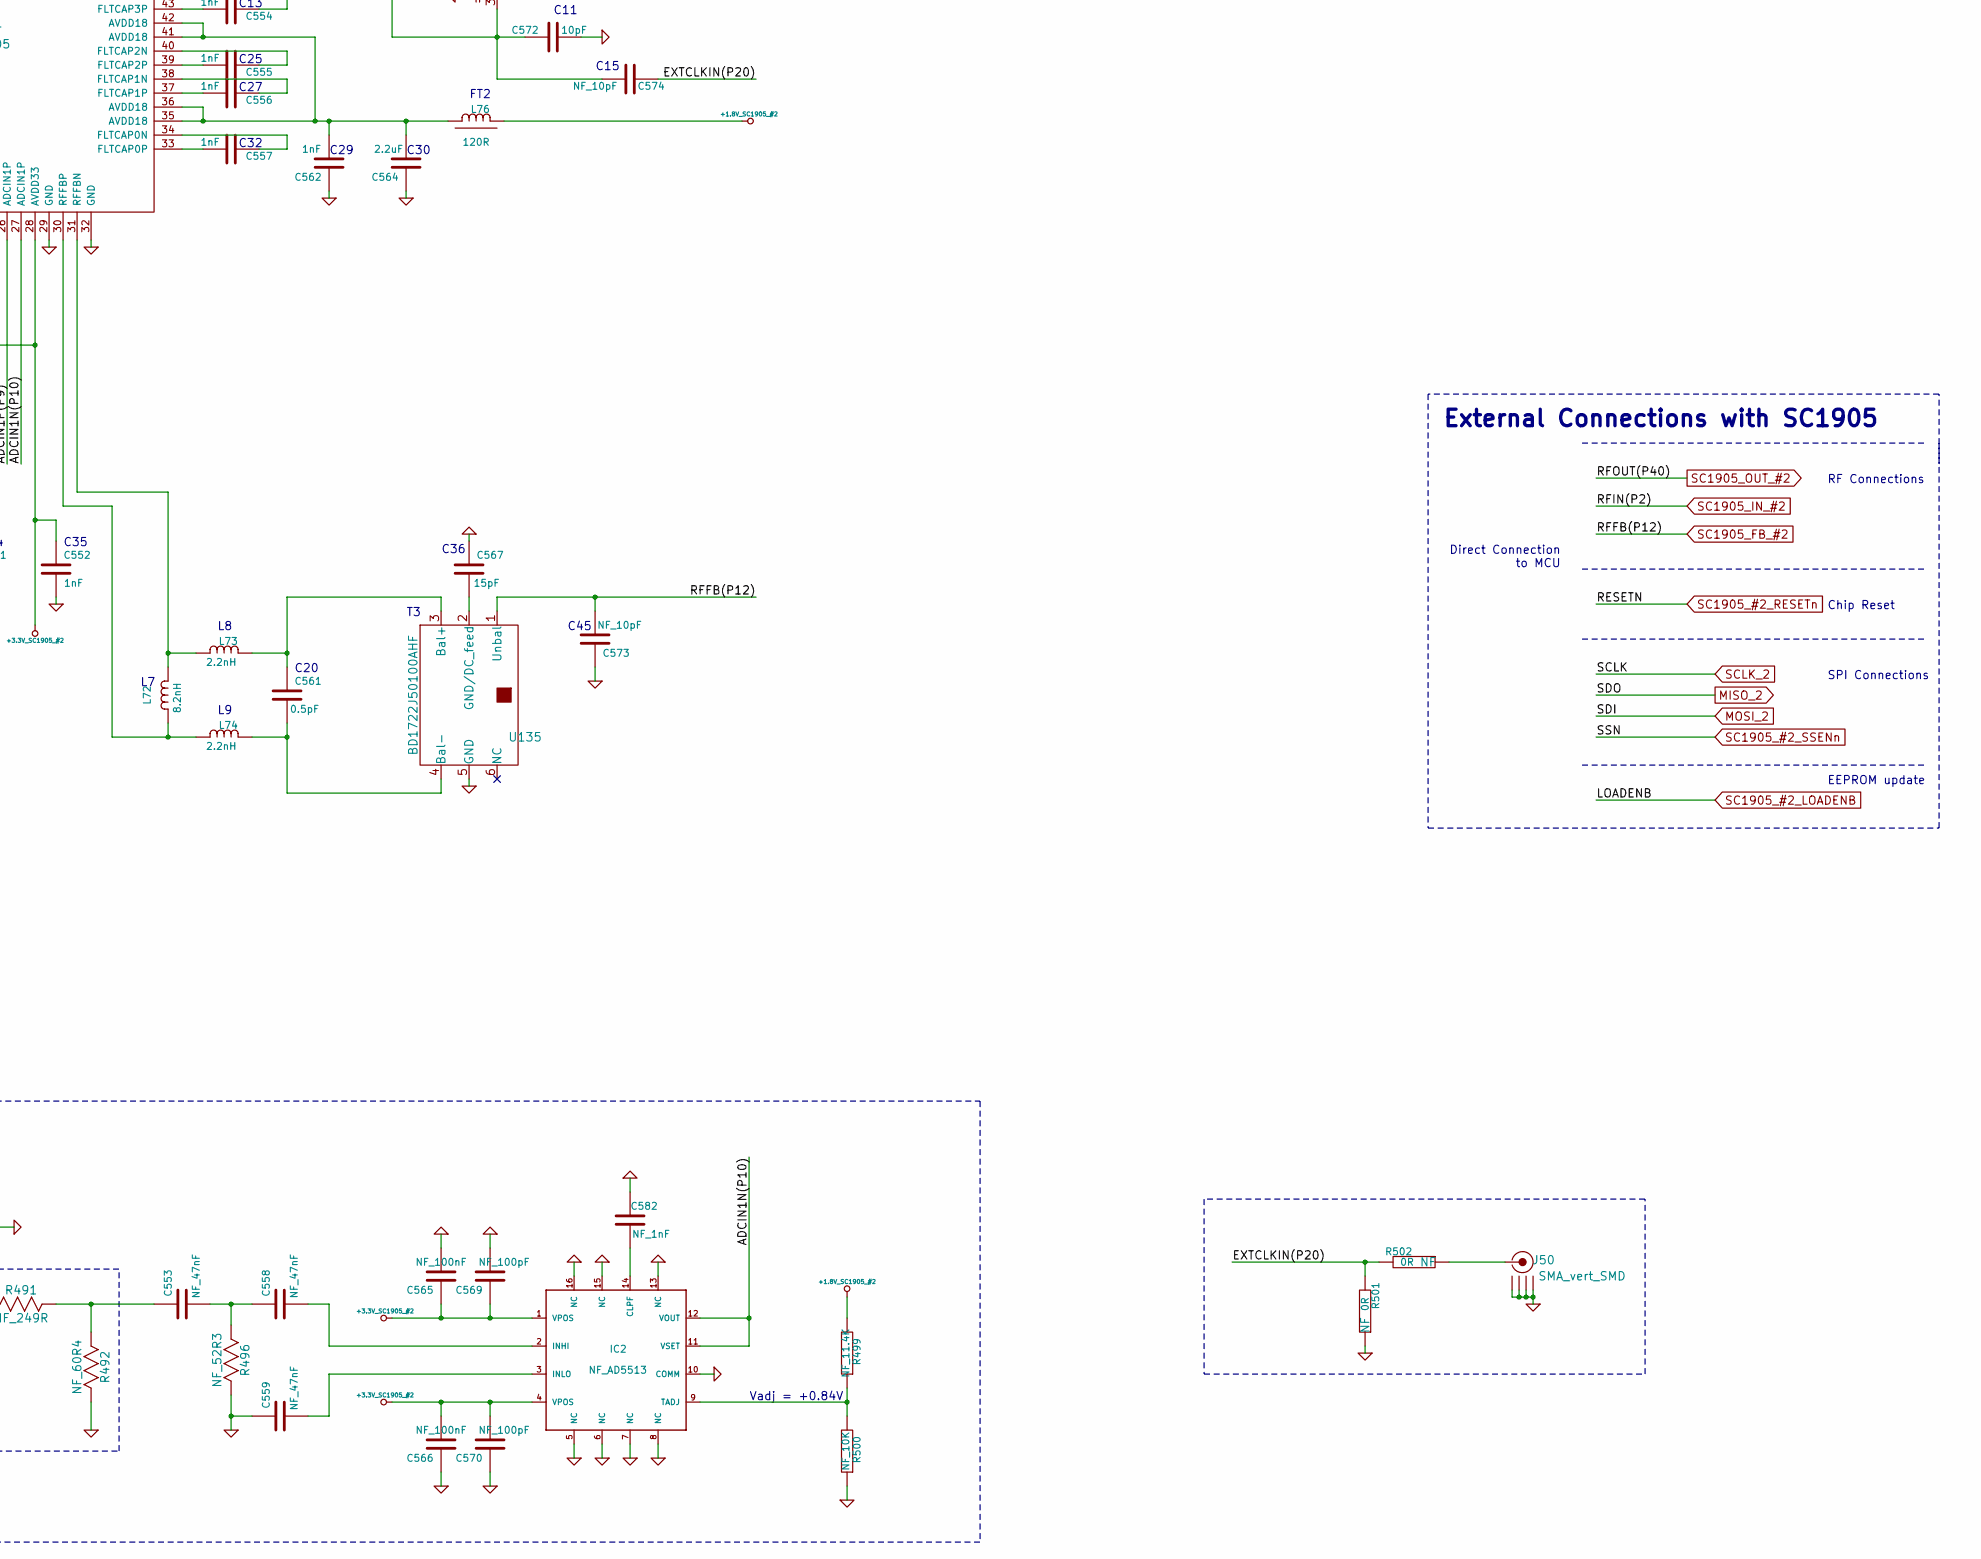
[picture p113: schematic SC1905_2.sch, part in row 2, column 2]

Parts:
C35, C531, C532, C534, C537, C538, C539, C573, C574: NF_10pF_0402_GJM1555C1H100GB01D; SMD0402; Manufacturer Part Number GJM1555C1H100GB01D
C527, C529, C543, C546, C547, C548, C549, C550, C551, C552, C554, C555, C556, C557, C560, C562, C563: 1nF_0402_GRM1555C1H102JA01D; SMD0402; Manufacturer Part Number GRM1555C1H102JA01D
C528: NF_1uF_0603_GRM188R61A105KA61D; SMD0603; Manufacturer Part Number GRM188R61A105KA61D
C530: NF_2.2uF_0603_GRM188R71A225KE15J; SMD0603; Manufacturer Part Number GRM188R71A225KE15J
C533, C536, C582: NF_1nF_0402_GRM1555C1H102JA01D; SMD0402; Manufacturer Part Number GRM1555C1H102JA01D
C540, C541, C567: 15pF_0402_GJM1555C1H150JB01D; SMD0402; Manufacturer Part Number GJM1555C1H150JB01D
C542: 0.2pF_0402_GJM1555C1HR20BB01D; SMD0402; Manufacturer Part Number GJM1555C1HR20BB01D
C544: 0.9pF_0402_GJM1555C1HR90BB01D; SMD0402; Manufacturer Part Number GJM1555C1HR90BB01D
C545, C564, C568: 2.2uF_0603_GRM188R71A225KE15J; SMD0603; Manufacturer Part Number GRM188R71A225KE15J
C553, C558, C559: NF_47nF_0402_GCM155R71H473KE02D; SMD0402; Manufacturer Part Number GCM155R71H473KE02D
C561: 0.5pF_0402_GJM1555C1HR50BB01D; SMD0402; Manufacturer Part Number GJM1555C1HR50BB01D
C565, C566: NF_100nF_0402_GRM155R71C104KA88J; SMD0402; Manufacturer Part Number GRM155R71C104KA88J
C569, C570: NF_100pF_0402_GRM1555C1H101JA01D; SMD0402; Manufacturer Part Number GRM1555C1H101JA01D
C571, C572: 10pF_0402_GJM1555C1H100GB01D; SMD0402; Manufacturer Part Number GJM1555C1H100GB01D
D3, D4: LED0603_GREEN; LED_0603; Manufacturer Part Number SML-D12M1WT86
IC2: NF_AD5513; AD5513; Manufacturer Part Number ADL5513ACPZ-R7
J49, J50: SMA_vert_SMD; Manufacturer Part Number 0732511352
L65: 470R_0402_BLM15BD471SN1D; SMD0402; Manufacturer Part Number BLM15BD471SN1D
L66, L67: 5.6nH_0402_HK10055N6S-T; SMD0402; Manufacturer Part Number HK10055N6S-T
L68: 18nH_0402_HK100518NJ-T; SMD0402; Manufacturer Part Number HK100518NJ-T
L69, L70: 1.2nH_0402_HK10051N2S-T; SMD0402; Manufacturer Part Number HK10051N2S-T
L71: 3.3nH_0402_HK10053N3S-T; SMD0402; Manufacturer Part Number HK10053N3S-T
L72: 8.2nH_0402_HK10058N2J-T; SMD0402; Manufacturer Part Number HK10058N2J-T
L73, L74: 2.2nH_0402_HK10052N2S-T; SMD0402; Manufacturer Part Number HK10052N2S-T
L75, L76: 120R_0603_BLM18AG121SN1D; SMD0603; Manufacturer Part Number BLM18AG121SN1D
Q3: NF_MMBT3904; MMBT3904; Manufacturer Part Number MMBT3904
Q4: 2N7002; SOT-23; Manufacturer PN 2N7002
R5, R417: 49.9R_0402_ERJ-U02F49R9X; SMD0402; Manufacturer Part Number ERJ-U02F49R9X
R418, R419, R420, R421, R422, R423, R431, R436, R437, R438, R439, R440, R441, R442, R449, R451, R487, R500: NF_10K_0402; SMD0402
R424, R432, R433, R434, R435, R443, R447, R448, R450, R453, R454, R455, R456, R459, R494, R497, R501, R502: 0R_0402_NF; SMD0402; Manufacturer Part Number RC0402JR-070RL
R426, R427, R430, R444, R446: 0R_0402_RC0402JR-070RL; SMD0402; Manufacturer Part Number RC0402JR-070RL
R445, R452: NF_0R_0402_RCS04020000Z0ED; SMD0402; Manufacturer Part Number RCS04020000Z0ED
R457: 12.4K_0402_ERJ-2RKF1242X; SMD0402; Manufacturer Part Number ERJ-2RKF1242X
R458, R472: NF_120R_0805_Panasonic; SMD0805; Manufacturer Part Number ERJ-P06J121V
R491: NF_249R_0603_CRCW0603249RFKEAHP; SMD0603; Manufacturer Part Number CRCW0603249RFKEAHP
R492: NF_60R4_0603_Yageo; SMD0603; Manufacturer Part Number RC0603FR-0760R4L
R493: 10K_0402_Yageo; SMD0402; Manufacturer Part Number RC0402JR-7D10KL
R495, R498: 510R_0402_RC0402JR-07510RL; SMD0402; Manufacturer Part Number RC0402JR-07510RL
R496: NF_52R3_0603_Yageo; SMD0603; Manufacturer Part Number RC0603FR-0752R3L
R499: NF_11.4K_0402_RT0402BRE0711K4L; SMD0402; Manufacturer Part Number RT0402BRE0711K4L
SW4: SW_PUSH; B3U-1000P; Manufacturer Part Number B3U-1000P
U124: BDCN-7-25+; Manufacturer Part Number BDCN-7-25+
U125: XDL15-2-020S; Manufacturer Part Number XDL15-2-020S
U126: NF_TMP36GRTZ-REEL7; TMP36GRTZ-REEL7; Manufacturer Part Number TMP36GRTZ-REEL7
U127: DC1722J5010AHF; Manufacturer Part Number DC1722J5010AHF
U128: NF_LMV324QDRG4; LMV324QDRG4; Manufacturer Part Number LMV324QDRG4
U129, U130, U135: BD1722J50100AHF; Manufacturer Part Number BD1722J50100AHF
U131: SC1905; SC1905A-00A00; Manufacturer Part Number SC1905A-00A00
X2: 830108207209; Manufacturer Part Number 830108207209

Connections:
+1.8V_SC1905_#2: C543.1, C545.2, C546.1, C547.2, C551.1, C560.2, L65.1, L75.1, L76.1, R499.2, U131.1 (DVDD18), U131.4 (AVDD18), U131.11 (AVDD18), U131.12 (AVDD18), U131.22 (AVDD18), U131.47 (AVDD18)
+3.3V_SC1905_#2: C527.2, C528.2, C529.2, C530.2, C533.2, C548.1, C549.1, C550.2, C552.1, C565.1, C566.2, C569.1, C570.2, IC2.1 (VPOS), IC2.4 (VPOS), R436.1, R487.2, R493.2, R495.2, R497.2, R498.2, U126.2 (VS), U128.4 (V+), U131.5 (AVDD33), U131.17 (AVDD33), U131.23 (AVDD33), U131.28 (AVDD33), U131.58 (DVDD33)
ADCIN0N(P7): R451.1, U131.25 (ADCIN0N)
ADCIN0P(P6): R452.1, U131.24 (ADCIN0P)
ADCIN1N(P10): IC2.11 (VSET), IC2.12 (VOUT), U131.27 (ADCIN1P)
ADCIN1P(P9): R459.2, U131.26 (ADCIN1P)
DGPIN0(P15): U131.63 (DGPIN0)
DGPIN1(P17): U131.56 (DGPIN1)
EXTCLKIN(P20): C574.1, R501.2, R502.2
GND: C35.1, C527.1, C528.1, C529.1, C530.1, C531.1, C532.1, C533.1, C534.1, C536.1, C537.2, C538.1, C539.1, C540.2, C541.2, C543.2, C545.1, C546.2, C547.1, C548.2, C549.2, C550.1, C551.2, C552.2, C559.1, C560.1, C562.1, C563.1, C564.1, C565.2, C566.1, C567.1, C568.1, C569.2, C570.1, C571.2, C572.2, C573.1, C582.1, D4.2 (K), IC2.5 (NC), IC2.6 (NC), IC2.7 (NC), IC2.8 (NC), IC2.10 (COMM), IC2.13 (NC), IC2.15 (NC), IC2.16 (NC), J49.2 (GND1), J49.3 (GND2), J49.4 (GND3), J49.5 (GND4), J50.2 (GND1), J50.3 (GND2), J50.4 (GND3), J50.5 (GND4), Q3.2 (E), Q4.2 (S), R5.1, R417.1, R418.2, R423.2, R431.2, R432.1, R433.1, R437.2, R442.2, R443.1, R447.1, R448.1, R450.1, R451.2, R457.1, R458.2, R459.1, R472.2, R492.2, R494.2, R496.2, R500.1, R501.1, SW4.1, U124.2 (GND), U124.5 (GND), U126.5 (GND), U127.3 (GND(GND)), U127.4 (GND(GND)), U128.11 (V-), U129.5 (GND), U130.5 (GND), U131.6 (GND), U131.7 (GND), U131.10 (GND), U131.15 (GND), U131.18 (GND), U131.21 (GND), U131.29 (GND), U131.32 (GND), U131.65, U135.5 (GND), X2.2, X2.4
MGPO0(P34): R440.1, R453.2, U128.10 (+INC)
MGPO1(P35): R421.1, R454.2, U128.5 (+INB)
MGPO2(P37): R439.1, R455.2, U128.12 (+IND)
MGPO3(P38): R420.1, R456.2, U128.3 (+INA)
MISO_2: R493.1, U131.54 (SDO)
MOSI_2: U131.53 (SDI)
unnamed: C536.2, R424.2, R449.2, R452.2
unnamed: C537.1, R444.1, R448.2, U129.1 (Unbal)
unnamed: C540.1, L65.2, U129.2 (GND/DC_feed)
unnamed: C541.1, U130.2 (GND/DC_feed)
unnamed: C542.1, L66.2, U129.4 (Bal-)
unnamed: C542.2, L67.2, U129.3 (Bal+)
unnamed: C544.1, L69.2, U130.4 (Bal-)
unnamed: C544.2, L70.2, U130.3 (Bal+)
unnamed: C553.1, R491.2, R492.1
unnamed: C553.2, C558.1, R496.1
unnamed: C554.1, U131.44 (FLTCAP3N)
unnamed: C554.2, U131.43 (FLTCAP3P)
unnamed: C555.1, U131.40 (FLTCAP2N)
unnamed: C555.2, U131.39 (FLTCAP2P)
unnamed: C556.1, U131.38 (FLTCAP1N)
unnamed: C556.2, U131.37 (FLTCAP1P)
unnamed: C557.1, U131.34 (FLTCAP0N)
unnamed: C557.2, U131.33 (FLTCAP0P)
unnamed: C558.2, IC2.2 (INHI)
unnamed: C559.2, IC2.3 (INLO)
unnamed: C561.1, L73.1, U135.3 (Bal+)
unnamed: C561.2, L74.1, U135.4 (Bal-)
unnamed: C562.2, C564.2, L76.2, U131.35 (AVDD18), U131.36 (AVDD18), U131.41 (AVDD18), U131.42 (AVDD18)
unnamed: C563.2, C568.2, L75.2, U131.48 (DVDD18), U131.55 (DVDD18), U131.59 (DVDD18), U131.64 (DVDD18)
unnamed: C567.2, U135.2 (GND/DC_feed)
unnamed: C571.1, U131.46 (XTALO), X2.1
unnamed: C572.1, C574.2, U131.45 (XTALI), X2.3
unnamed: C582.2, IC2.14 (CLPF)
unnamed: D3.1 (A), R495.1
unnamed: D3.2 (K), Q4.3 (D)
unnamed: D4.1 (A), R498.1
unnamed: IC2.9 (TADJ), R499.1, R500.2
unnamed: J49.1 (RF), R458.1, R472.1, R491.1
unnamed: J50.1 (RF), R502.1
unnamed: L66.1, L68.1, U131.8 (RFOUTP)
unnamed: L67.1, L68.2, U131.9 (RFOUTN)
unnamed: L69.1, L71.1, U131.19 (RFINP)
unnamed: L70.1, L71.2, U131.20 (RFINN)
unnamed: L72.1, L73.2, U131.31 (RFFBN)
unnamed: L72.2, L74.2, U131.30 (RFFBP)
unnamed: Q3.1 (B), Q3.3 (C), R449.1
unnamed: R5.2, U127.5 (CPL(ISO))
unnamed: R417.2, U124.6 (CPL_FWR)
unnamed: R418.1, R419.1, U128.2 (-INA)
unnamed: R422.1, R423.1, U128.6 (-INB)
unnamed: R424.1, U126.1 (VOUT)
unnamed: R426.1, U125.2
unnamed: R426.2, R434.1, U124.1 (IN)
unnamed: R427.1, U125.1
unnamed: R427.2, R430.2, R432.2, R435.1
unnamed: R430.1, R433.2, U127.6 (IN(DIR))
unnamed: R431.1, R436.2, U126.4 (SHDWNn)
unnamed: R434.2, R435.2
unnamed: R437.1, R438.1, U128.13 (-IND)
unnamed: R441.1, R442.1, U128.9 (-INC)
unnamed: R443.2, R445.2, R446.1, U127.2 (ISO(CPL))
unnamed: R444.2, R447.2, U124.3 (CPL_REV)
unnamed: R445.1, R446.2, R450.2, U130.1 (Unbal)
unnamed: R453.1, U131.2 (MGPOUT0)
unnamed: R454.1, U131.3 (MGPOUT1)
unnamed: R455.1, U131.13 (MGPOUT2)
unnamed: R456.1, U131.14 (MGPOUT3)
unnamed: R457.2, U131.16 (BGRES)
SC1905_#2_LOADENB: U131.60 (LOADENB)
SC1905_#2_RESETn: R487.1, R497.1, SW4.2, U131.49 (RESETN)
SC1905_#2_SSENn: U131.52 (SSN)
SC1905_FB_#2: C573.2, U135.1 (Unbal)
SC1905_IN_#2: C35.2, U127.1 (DIR(IN))
SC1905_OUT_#2: C534.2, U124.4 (OUT)
SCLK_2: U131.51 (SCLK)
STATO: Q4.1 (G), U131.57 (STATO)
VG0: C539.2, R440.2, R441.2, U128.8 (OUTC)
VG1: C532.2, R421.2, R422.2, U128.7 (OUTB)
VG2: C538.2, R438.2, R439.2, U128.14 (OUTD)
VG3: C531.2, R419.2, R420.2, U128.1 (OUTA)
WDTENB: R494.1, U131.50 (WDTENB)

Notes on the sheet:
C14
C12
R12
C17
C26
FT3
C31
C33
R27
R25
R26
RFOUT Attenuator
DC2
R10
C48
R8 R428 obrisan
R102
R17
R13
R15
R14
Thru Path Attenuator
R11
Optional RF Thru Path without Delay Line
R23
R21
R22
RFIN Attenuator
C18
C28
C34
C35
C20
C36
C45
C32
FT2
C29
C30
C27
C25
C13
C10
C11
C15
FT1
SW1
R12 must have 1% tolerance and 100ppm/C temperature coefficient!
R46
R47
R44
R65
C42
R40
Vadj = +0.84V
20dB Attenuator
Power Detector Not Fitted
Temperature Sensor Not Fitted
R64
R53
R54
R51
R57
R58
C38
R49
R56
R55
C37
R52
R60
R59
R50
C39
Buffers for MGPOUT 0-3 Not Fitted
Master Board
EVK1900 board
R24
External Connections with SC1905
RF Connections
SPI Connections
Chip Reset
Direct Connection to MCU
DC1
R16
C47
ovo se ne slaze sa gerberima! Gerber: Pin1 -> RFIN (P2) Pin2 -> RFIN att Pin3 -> GND Pin4 -> GND Pin5 -> R16 Pin6 -> Thru Path Att
Sch: Pin1 -> Thru Path Att Pin2 -> R16 Pin3 -> GND Pin4 -> GND Pin5 -> RFIN att Pin6 -> RFIN (P2)
NOT CONNECTED!
CONNECTED TO R494
CONNECTED TO Q4
EEPROM update
