myriadrf/LimeRFE-8001P/firmware/1v0/LMS8FE/errorCode.h

#define COMPLETED                         0
#define ERROR_SC1905_RSR                  1
#define ERROR_SC1905_CHK                  2
#define ERROR_SC1905_EEPROM_BUSY          3
#define ERROR_SC1905_EEPROM_LOCKED        4
#define ERROR_SC1905_EEPROM_UNLOCKED      5
